electrodyssey/NASR-M/conf/LMK03328-settings/LMK03328-TP-solver-PS33.33-SZG64.8.jpg

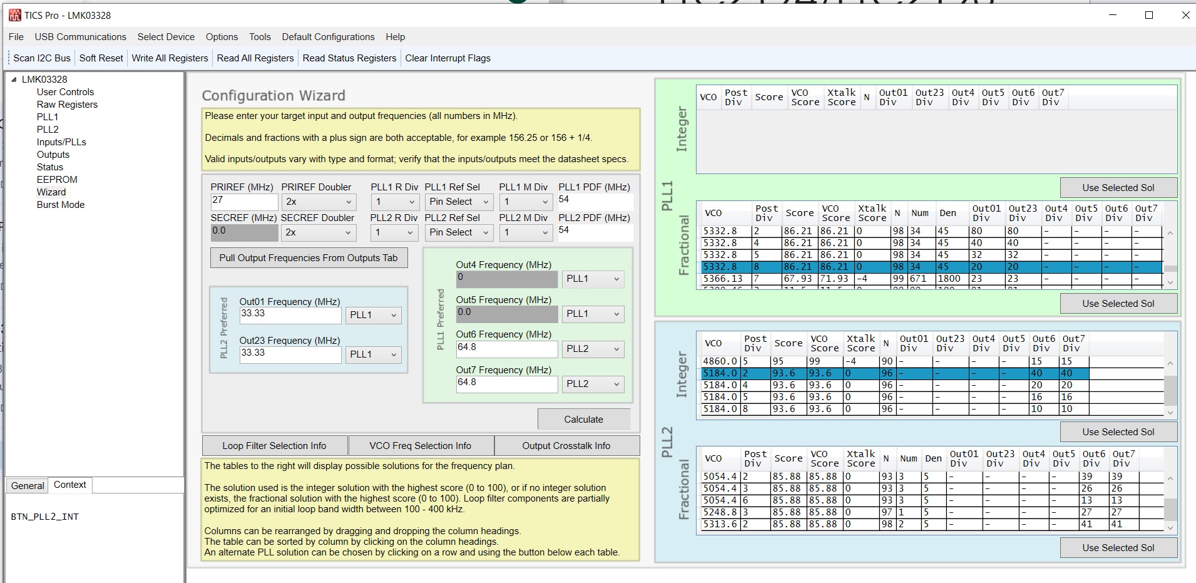
conf/LMK03328-settings/LMK03328-TP-solver-PS33.33-SZG64.8.jpg
