electrodyssey/NASR-M/conf/mcu-conf/nasr_stm32_clock.png

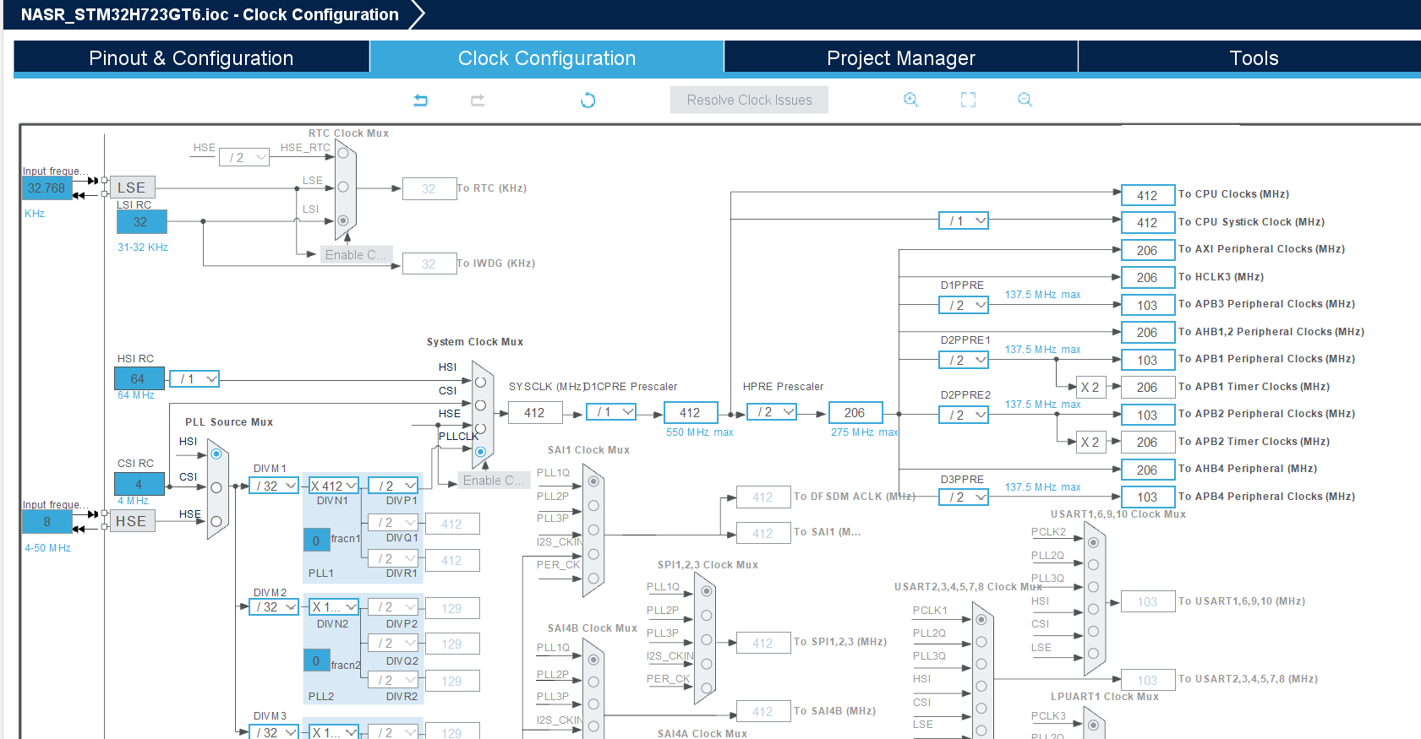
conf/mcu-conf/nasr_stm32_clock.png
