electrodyssey/NASR-M/datasheet/74/deadtime-spdt-nor-and.png

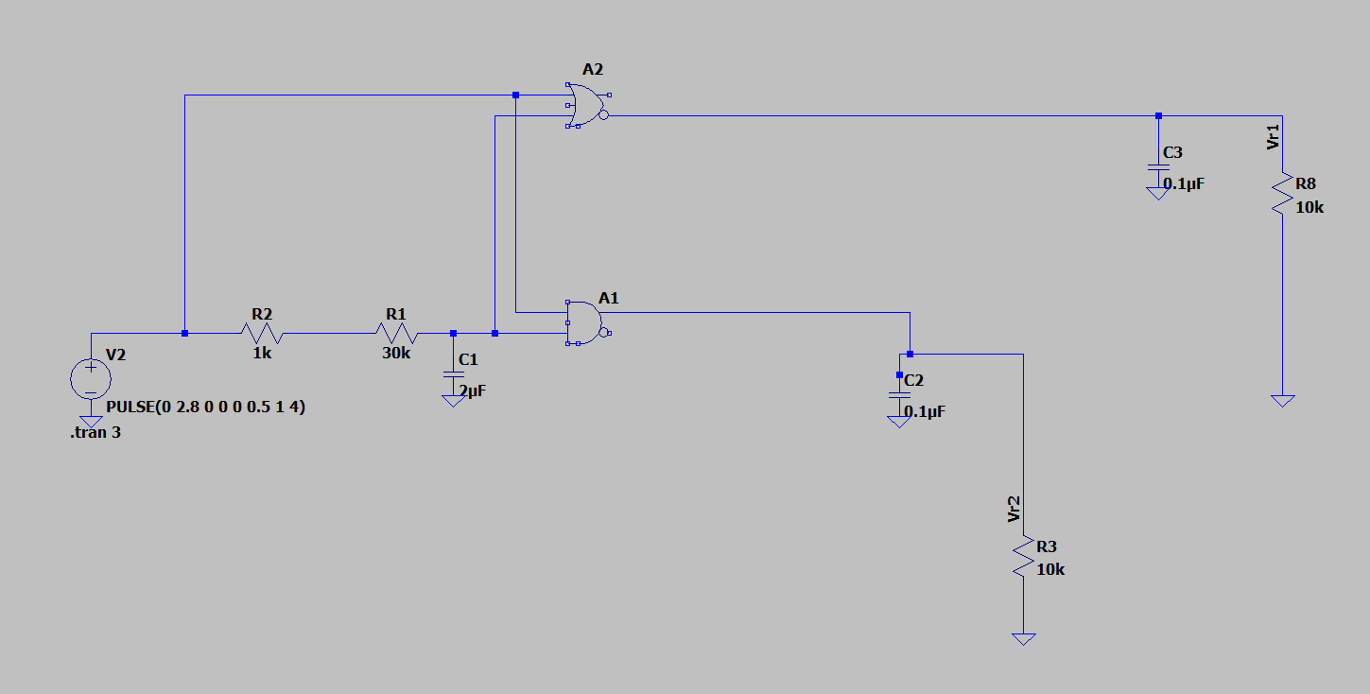
datasheet/74/deadtime-spdt-nor-and.png
