electrodyssey/NASR-M/datasheet/clock/Screenshot 2023-09-30 040555.jpg

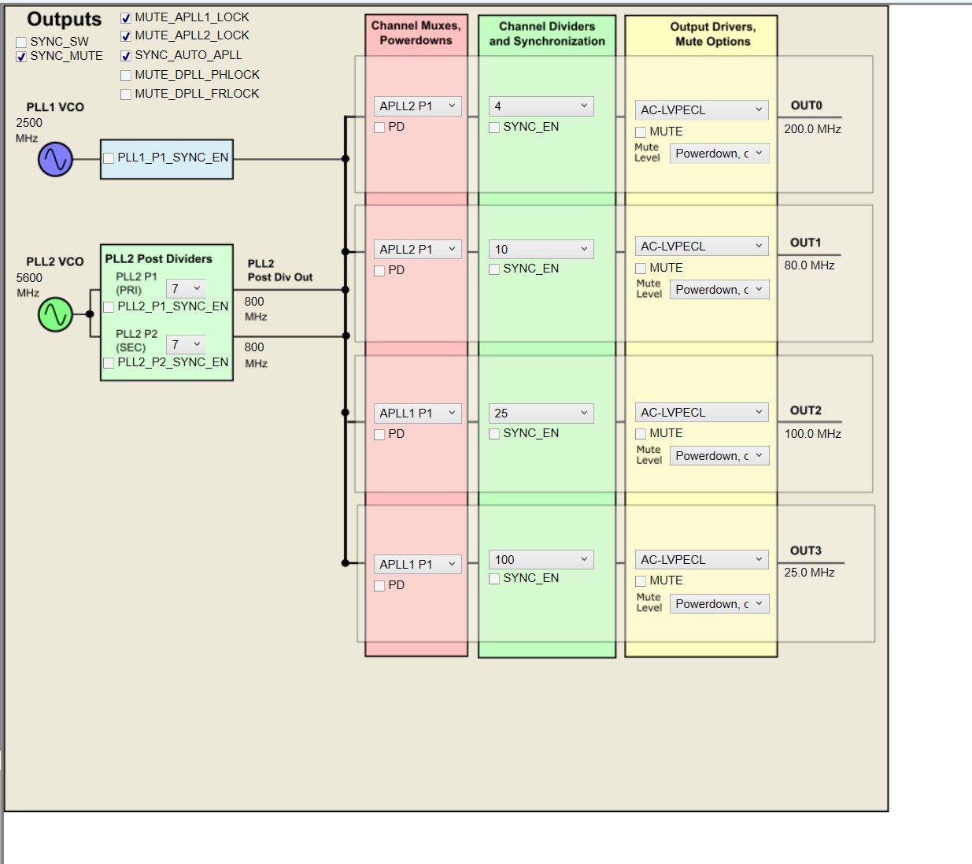
datasheet/clock/Screenshot 2023-09-30 040555.jpg
