electrodyssey/NASR-M/datasheet/enet-sw/4604.dp83640 AC coupling connection.JPG

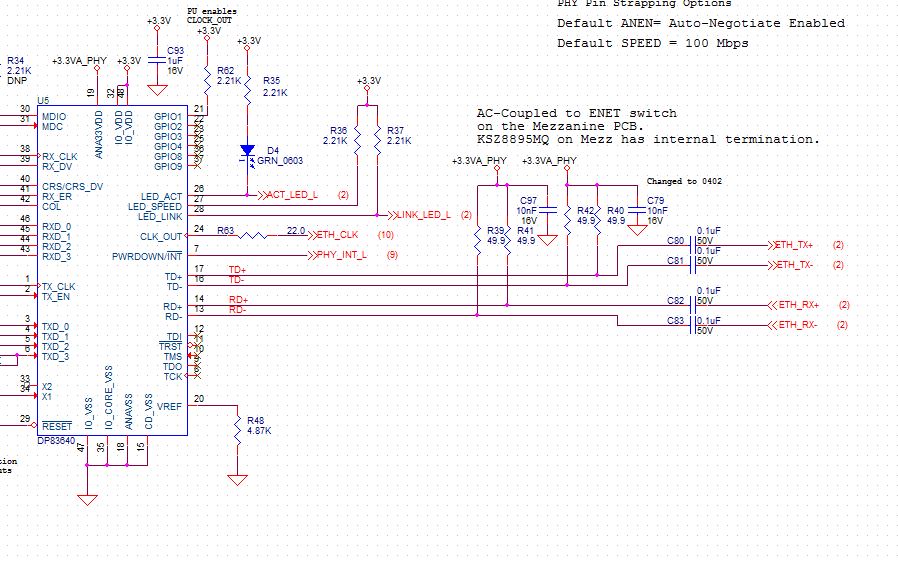
datasheet/enet-sw/4604.dp83640 AC coupling connection.JPG
