electrodyssey/NASR-M/datasheet/LM74700/LM74700-schema.png

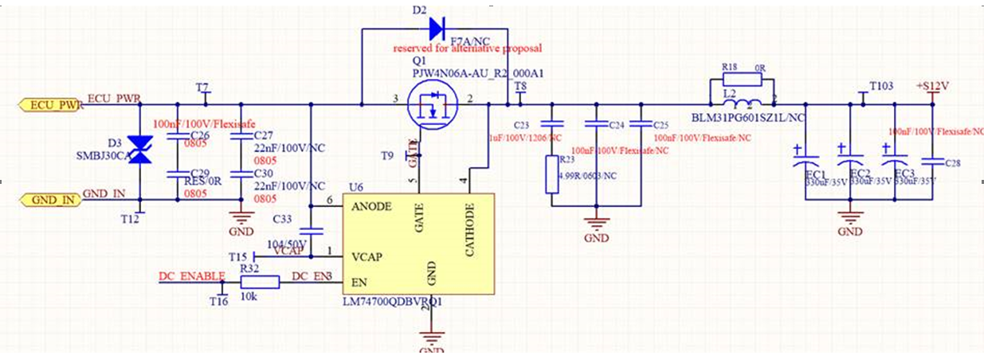
datasheet/LM74700/LM74700-schema.png
