electrodyssey/NASR-M/datasheet/pmic/LMR33640ADDAR  ‑  9V-36V to 6.50V @ 3.8A/LMR33640-buck-6.5V@3.8A.png

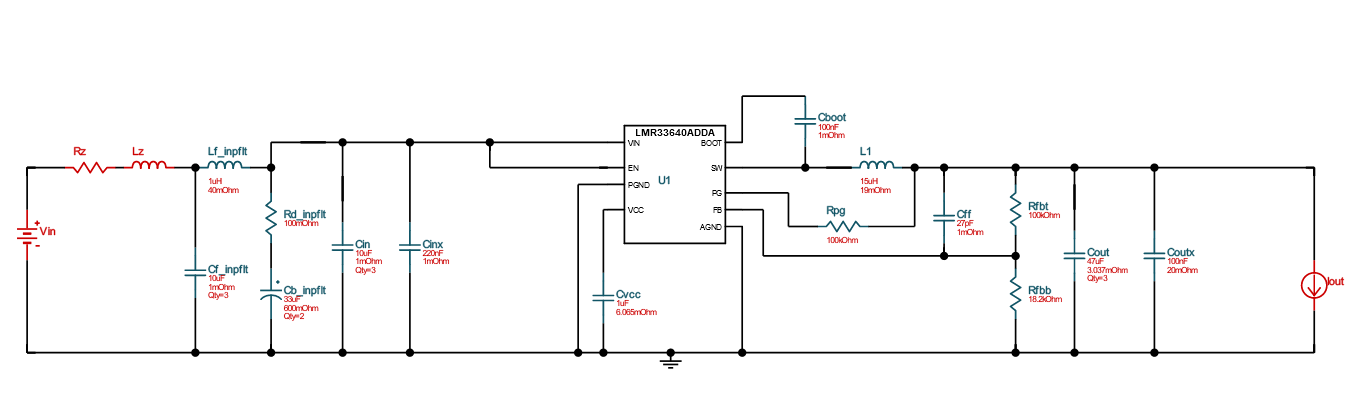
datasheet/pmic/LMR33640ADDAR ‑ 9V-36V to 6.50V @ 3.8A/LMR33640-buck-6.5V@3.8A.png
