electrodyssey/NASR-M/datasheet/usb-sata/sata-connector.jpg

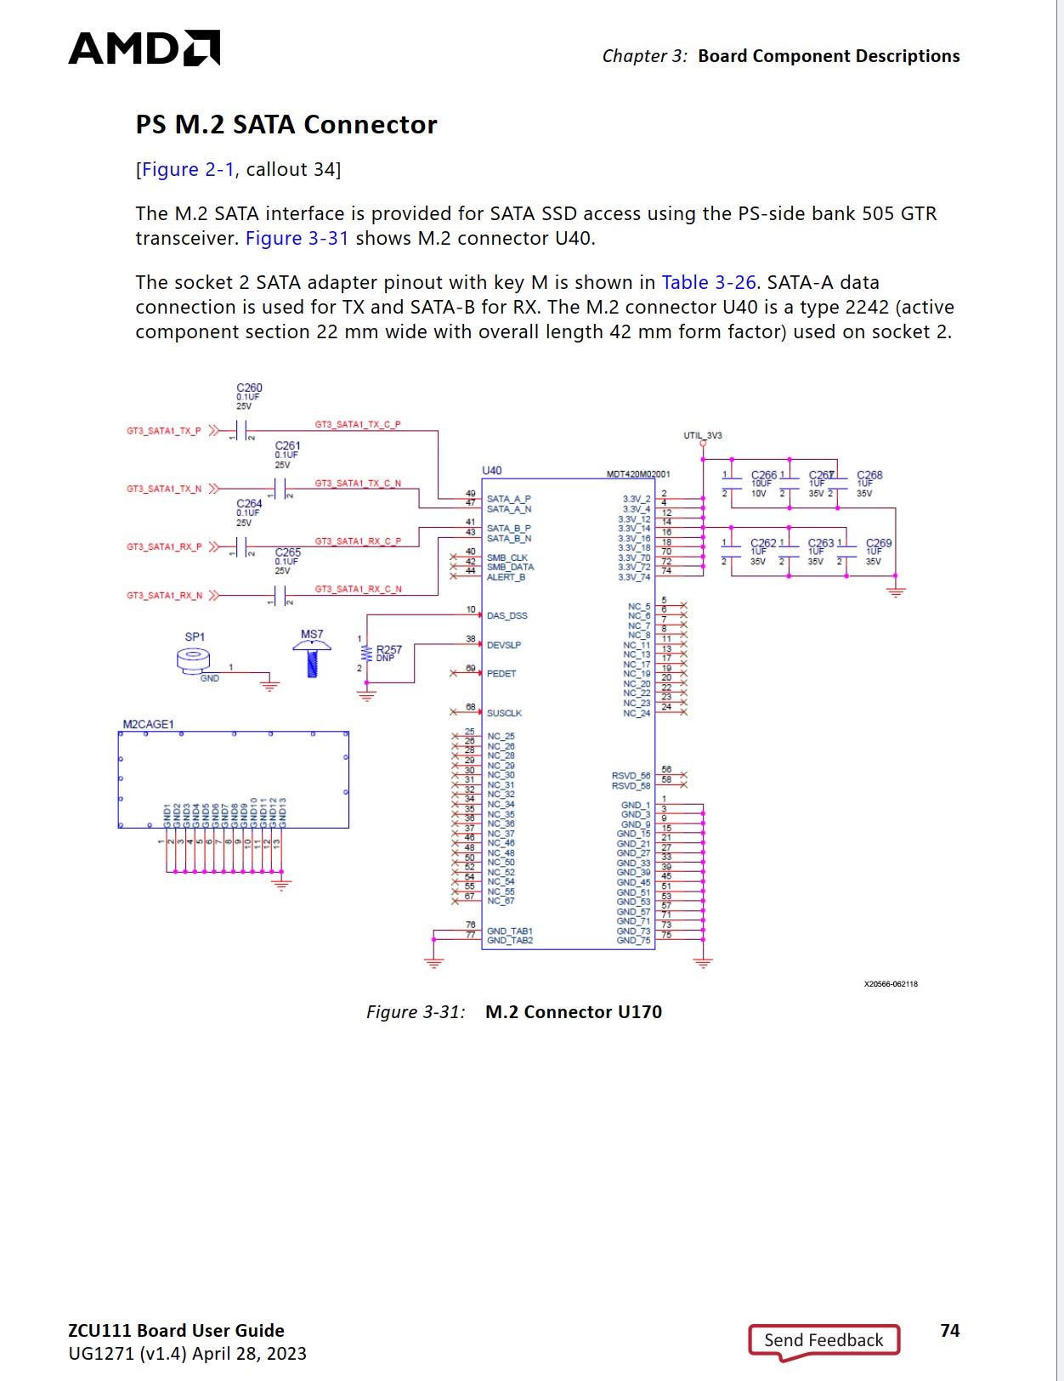
datasheet/usb-sata/sata-connector.jpg
