electrodyssey/NASR-M/datasheet/xilinx-7/artix-7-clocking/XC7A50T-FTG256.png

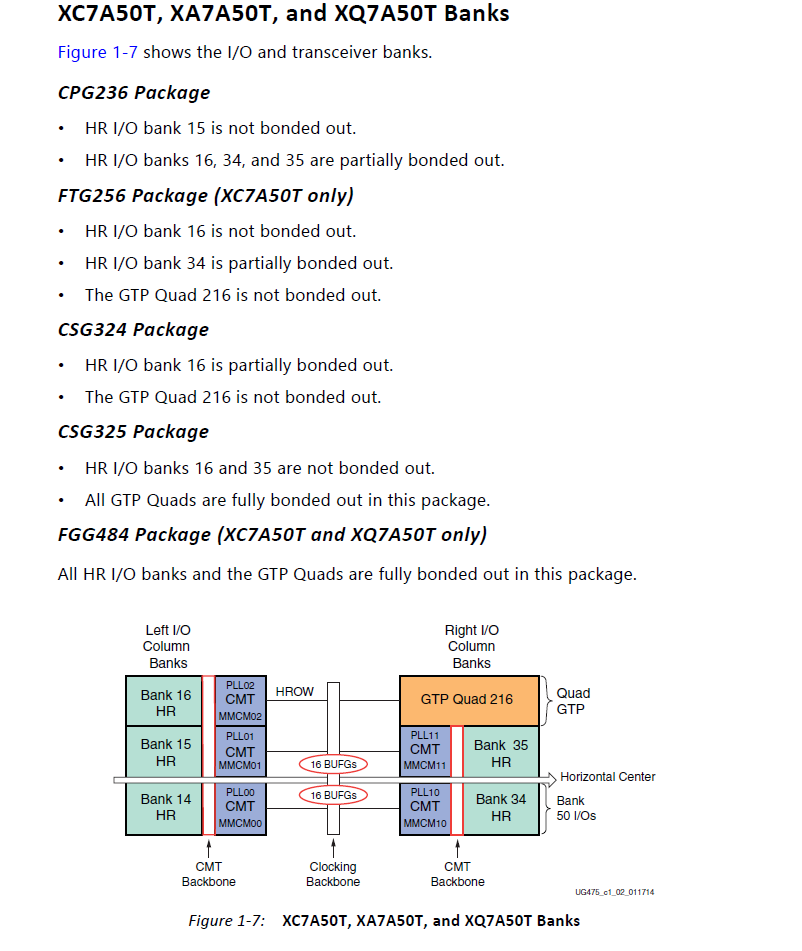
datasheet/xilinx-7/artix-7-clocking/XC7A50T-FTG256.png
