electrodyssey/NASR-M/stackup/JLC10161H-2116/stack-JLC10161H-2116-mil.jpg

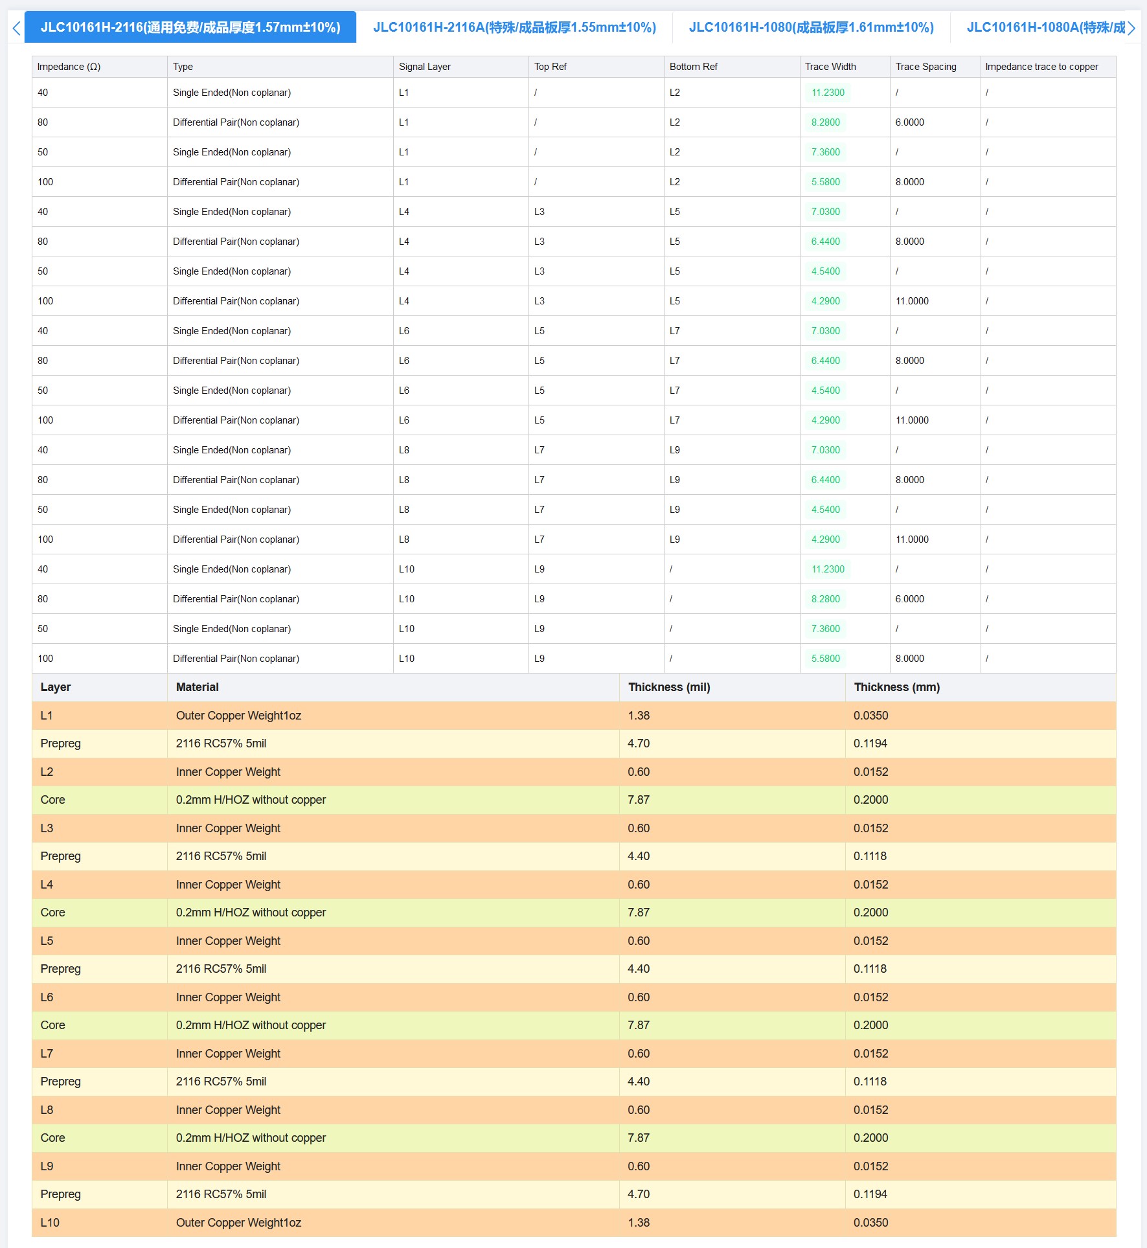
stackup/JLC10161H-2116/stack-JLC10161H-2116-mil.jpg
