electrodyssey/NASR-M/stackup/JLC10161H-2116/stack-JLC10161H-2116.jpg

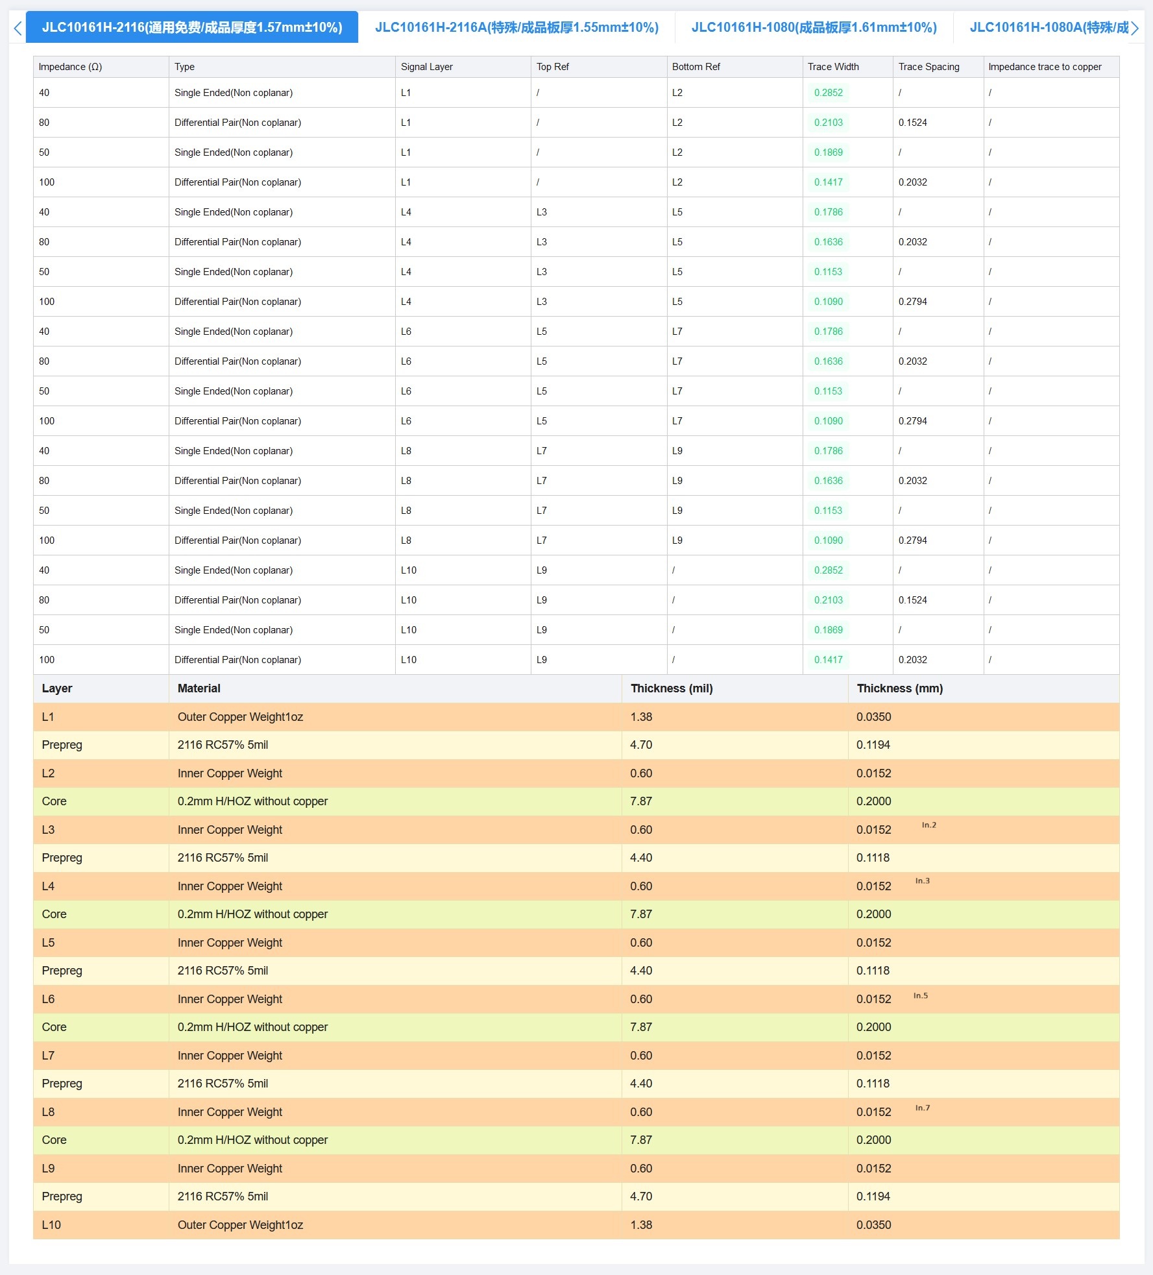
stackup/JLC10161H-2116/stack-JLC10161H-2116.jpg
