electrodyssey/NASR-M/vio-sim/tinadiag-vio-adc_0.001-2-sweep.bmp

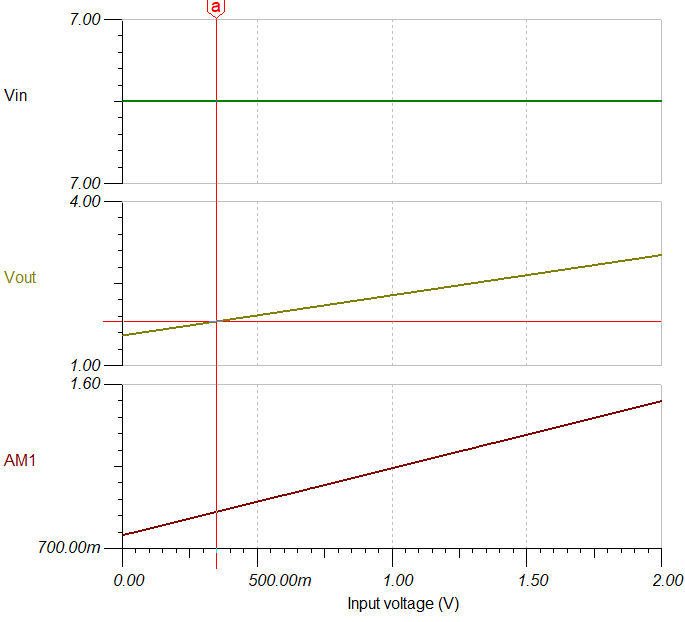
vio-sim/tinadiag-vio-adc_0.001-2-sweep.bmp
