electrodyssey/NASR-M/datasheet/74/spdt-emul.asc

A1: and
A2: or
C1: cap; 2µF
C2: cap; 0.1µF
C3: cap; 0.1µF
R1: res; 30k
R2: res; 1k
R3: res; 10k
R8: res; 10k
V2: voltage; PULSE(0 2.8 0 0 0 0.5 1 4)
Named nets: 0, Vr2, Vr1
.tran 3
