electrodyssey/NASR-M/NASR.kicad_sch

## KiCad design NASR.kicad_sch (2025-10-22)

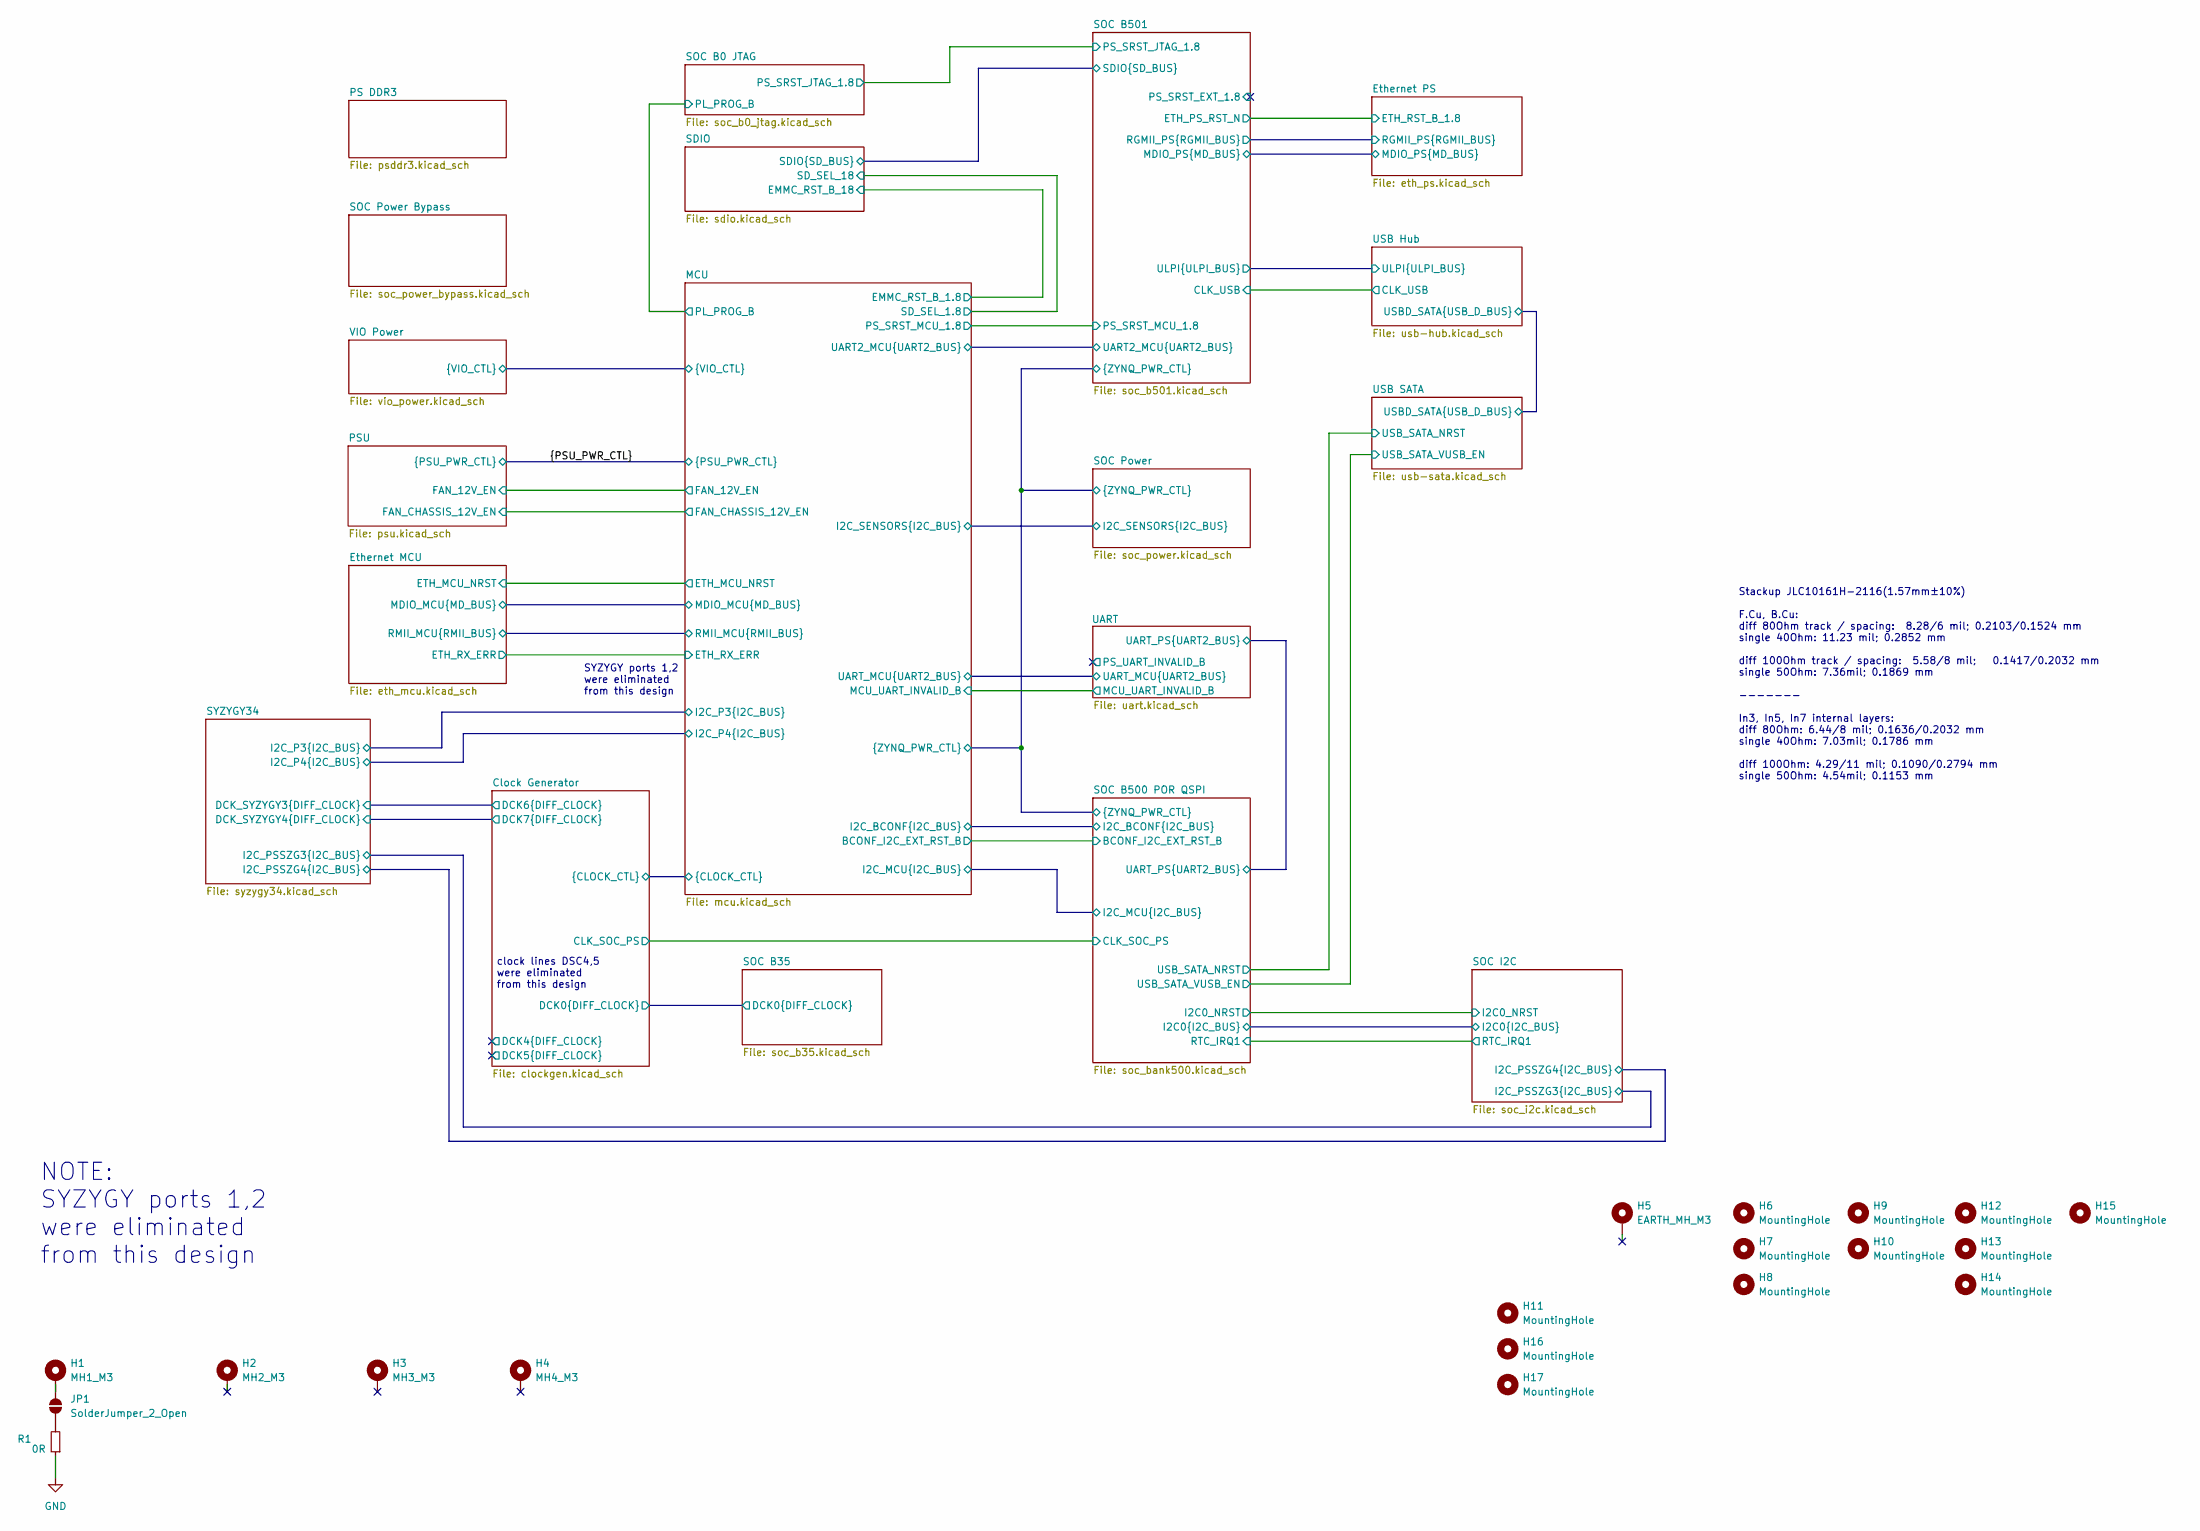
[picture p45: schematic NASR.kicad_sch]

Parts:
H1: MH1_M3; MountingHole_3.2mm_M3_Pad_Via
H2: MH2_M3; MountingHole_3.2mm_M3_Pad_Via
H3: MH3_M3; MountingHole_3.2mm_M3_Pad_Via
H4: MH4_M3; MountingHole_3.2mm_M3_Pad_Via
H5: EARTH_MH_M3; MountingHole_3.2mm_M3_Pad_Via
H6, H7, H8, H9, H10, H12, H13, H14, H15: MountingHole; MountingHole_3.2mm_M3
H11, H16, H17: MountingHole; MountingHole_4.3mm_M4_Pad_TopBottom
JP1: SolderJumper_2_Open; SolderJumper-2_P1.3mm_Open_RoundedPad1.0x1.5mm
R1: 0R; R_1210_3225Metric_Pad1.30x2.65mm_HandSolder; Part RC1210JR-070RL; JLCPCB Part # C137090

Connections:
GND: R1.1
unnamed: H1.1, JP1.2 (B)
unnamed: JP1.1 (A), R1.2

Notes on the sheet:
clock lines DSC4,5 were eliminated from this design
NOTE: SYZYGY ports 1,2 were eliminated from this design
SYZYGY ports 1,2 were eliminated from this design
Stackup JLC10161H-2116(1.57mm±10%) F.Cu, B.Cu: diff 80Ohm track / spacing: 8.28/6 mil; 0.2103/0.1524 mm single 40Ohm: 11.23 mil; 0.2852 mm diff 100Ohm track / spacing: 5.58/8 mil; 0.1417/0.2032 mm single 50Ohm: 7.36mil; 0.1869 mm ------- In3, In5, In7 internal layers: diff 80Ohm: 6.44/8 mil; 0.1636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
