electrodyssey/NASR-M/clockgen.kicad_sch

## KiCad design clockgen.kicad_sch (2026-03-24)

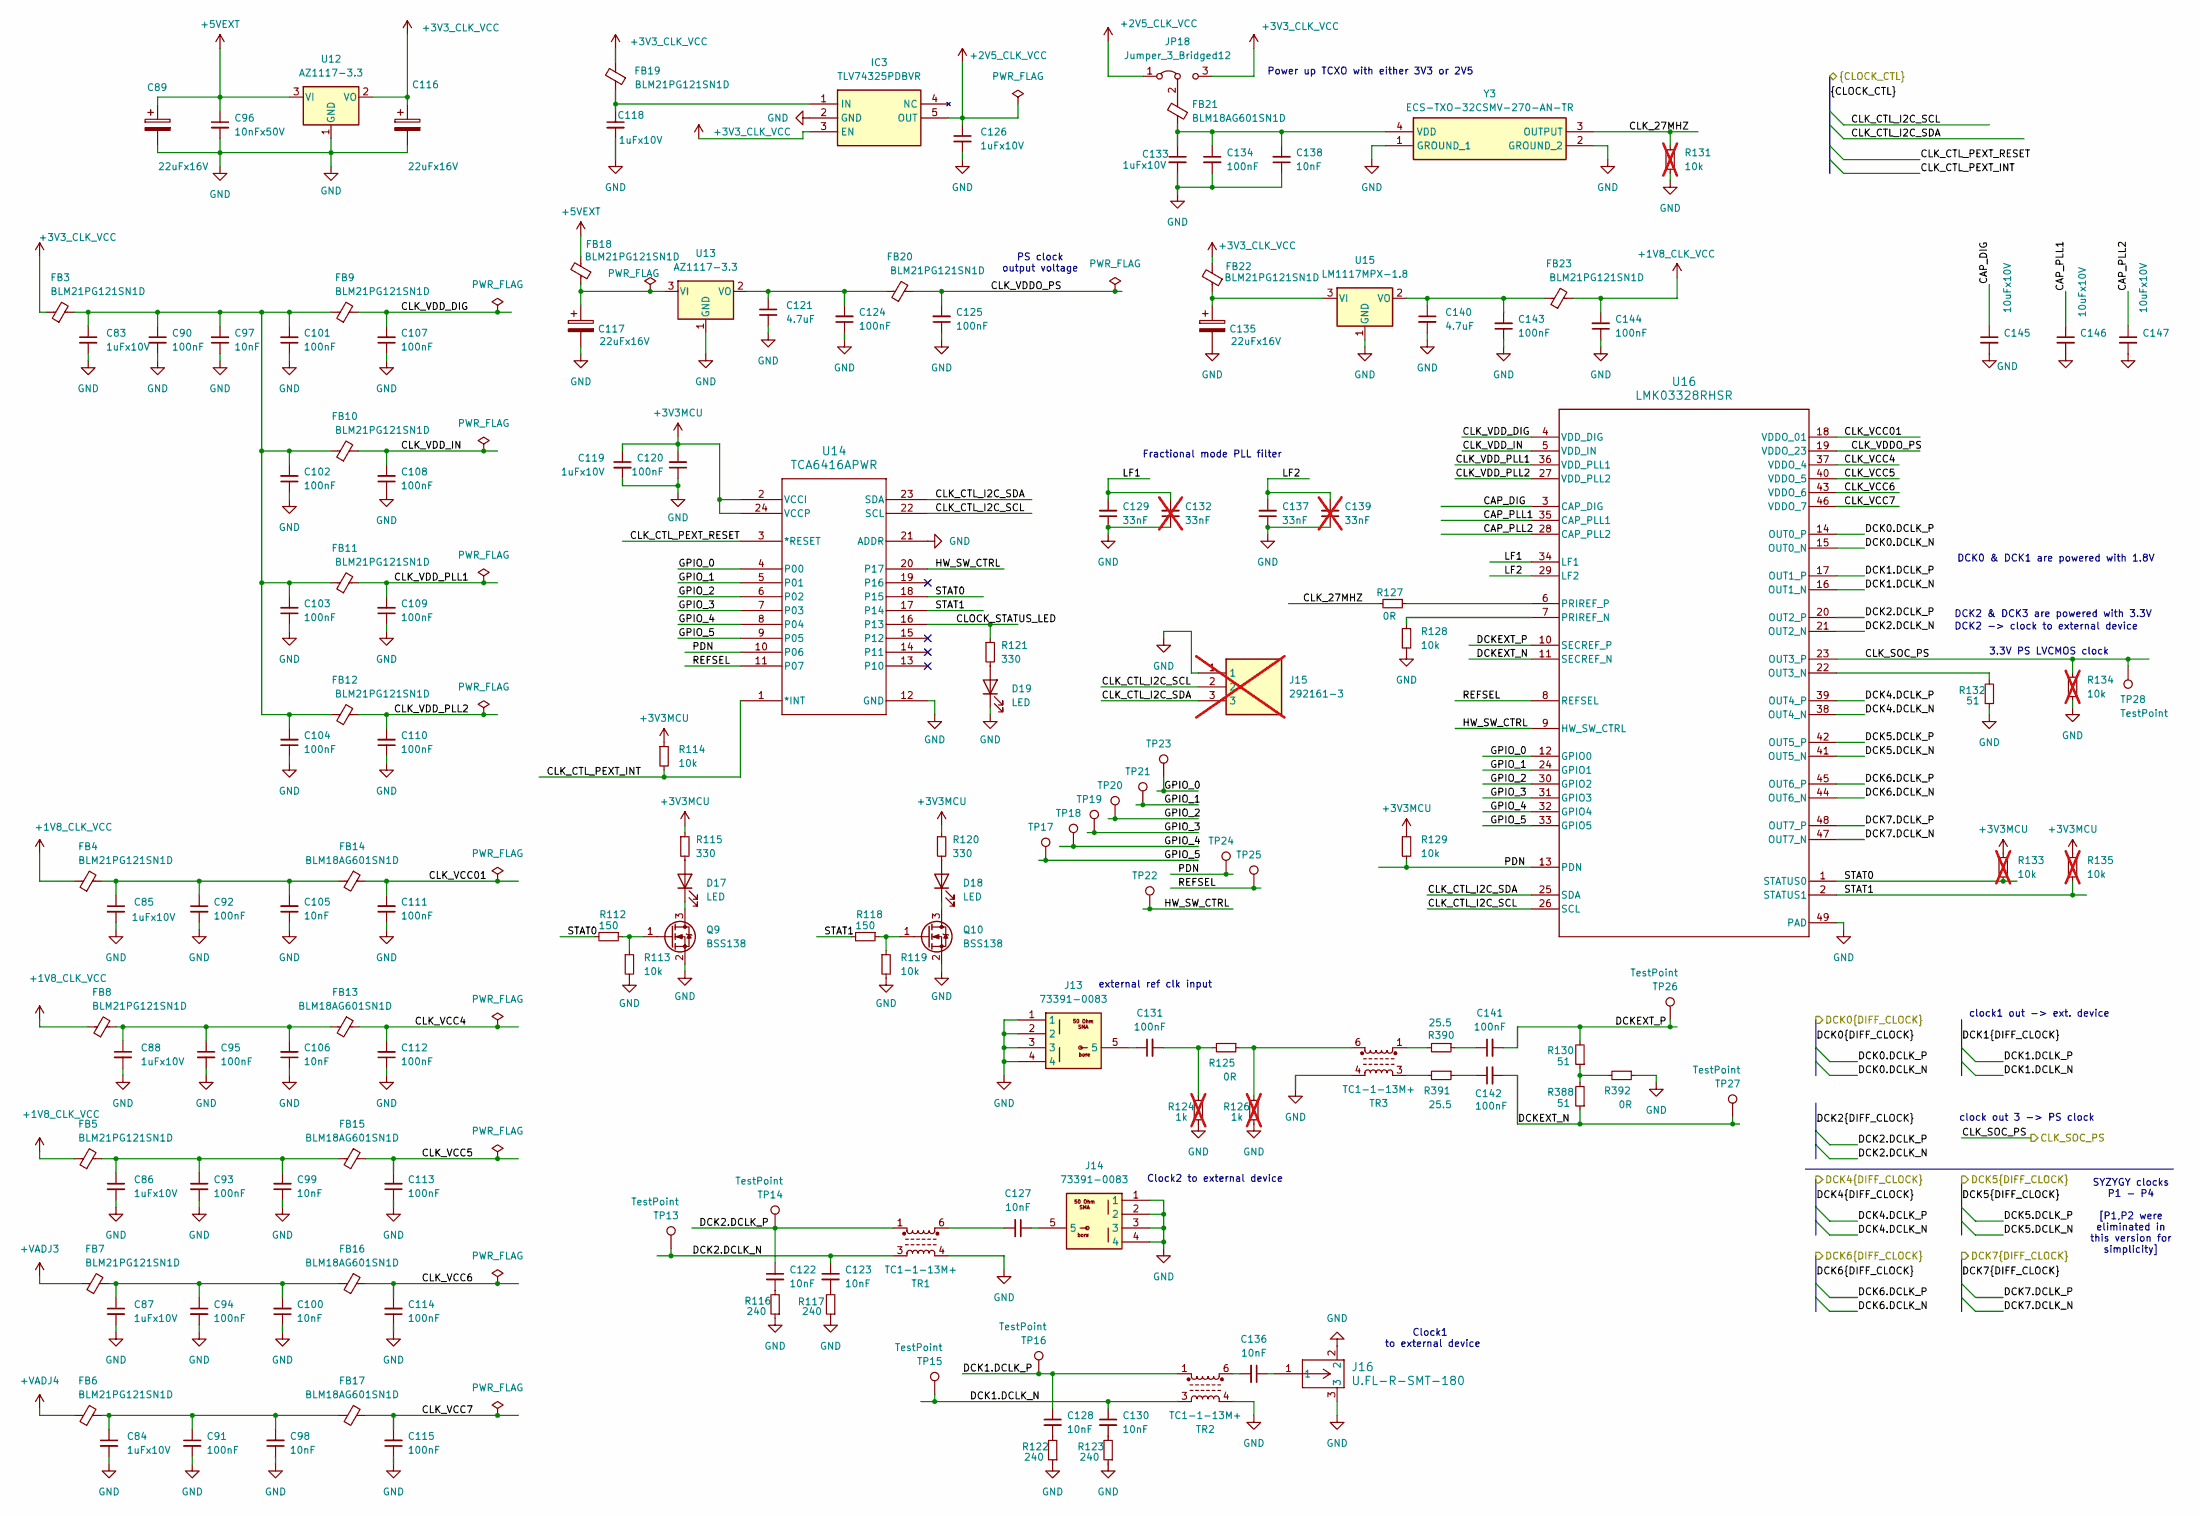
[picture p46: schematic clockgen.kicad_sch]

Parts:
C83, C84, C85, C86, C87, C88, C118, C119, C126, C133: 1uFx10V; C_0603_1608Metric; JLCPCB Part # C841050
C89, C116, C117, C135: 22uFx16V; CP_EIA-6032-15_Kemet-U; Part TR3C226K016C0350; JLCPCB Part # C1954274
C90, C91, C92, C93, C94, C95, C101, C102, C103, C104, C107, C108, C109, C110, C111, C112, C113, C114, C115, C120, C124, C125, C131, C134, C141, C142, C143, C144: 100nF; C_0402_1005Metric; Part CC0402JRX7R8BB104; JLCPCB Part # C541465
C96: 10nFx50V; C_1206_3216Metric; Part 1206B103K102NT; JLCPCB Part # C9194
C97, C98, C99, C100, C105, C106, C122, C123, C127, C128, C130, C136, C138: 10nF; C_0402_1005Metric; Part CL05B103KB5NNNC; JLCPCB Part # C15195
C121, C140: 4.7uF; C_0603_1608Metric; JLCPCB Part # C19666
C129, C137: 33nF; C_0603_1608Metric; Part CL10B333KB8NNNC; JLCPCB Part # C21117
C132, C139: 33nF; C_0603_1608Metric; Part CL10B333KB8NNNC; JLCPCB Part # C21117; not fitted
C145, C146, C147: 10uFx10V; C_0805_2012Metric; Part CL21A106KPFNNNE; JLCPCB Part # C17024
D17, D18, D19: LED; LED_0805_2012Metric; Part HL-PSC-2012S11GC; JLCPCB Part # C497958
FB3, FB4, FB5, FB6, FB7, FB8, FB9, FB10, FB11, FB12, FB18, FB19, FB20, FB22, FB23: BLM21PG121SN1D; L_0805_2012Metric; Part BLM21PG121SN1D; JLCPCB Part # C79382
FB13, FB14, FB15, FB16, FB17, FB21: BLM18AG601SN1D; L_0603_1608Metric; Part BLM18AG601SN1D; JLCPCB Part # C19330
IC3: TLV74325PDBVR; SOT95P280X145-5N; Mouser Part Number 595-TLV74325PDBVR
J13, J14: 73391-0083; 733910083; Mouser Part Number 538-73391-0083
J15: 292161-3; SHDR3W60P0X200_1X3_780X360X680P; Mouser Part Number 571-292161-3; not fitted
J16: U.FL-R-SMT-180; CONN1_U.FL-R-SMT-180_HIR; Part U.FL-R-SMT-1(80); JLCPCB Part # C88374
JP18: Jumper_3_Bridged12; SolderJumper-3_P1.3mm_Bridged2Bar12_Pad1.0x1.5mm_NumberLabe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
Q9, Q10: BSS138; SOT-23; JLCPCB Part # C52895
R112, R118: 150; R_0402_1005Metric; Part 0402WGF1500TCE; JLCPCB Part # C25082
R113, R114, R119, R128, R129: 10k; R_0402_1005Metric; Part 0402WGF1002TCE; JLCPCB Part # C25744
R115, R120, R121: 330; R_0402_1005Metric; Part 0402WGF3300TCE; JLCPCB Part # C25104
R116, R117, R122, R123: 240; R_0402_1005Metric; Part RK73B1ETTP241J; JLCPCB Part # C131545
R124, R126: 1k; R_0402_1005Metric; Part 0402WGF1001TCE; JLCPCB Part # C11702; not fitted
R125, R127, R392: 0R; R_0603_1608Metric; Part FRC0603F0000TS; JLCPCB Part # C2906974
R130, R132, R388: 51; R_0402_1005Metric; Part FRC0402J510 TS; JLCPCB Part # C2906953
R131, R133, R134, R135: 10k; R_0402_1005Metric; Part 0402WGF1002TCE; JLCPCB Part # C25744; not fitted
R390, R391: 25.5; R_0402_1005Metric; Part RK73H1ETTP25R5F; JLCPCB Part # C830244
TP13, TP14, TP15, TP16, TP17, TP18, TP19, TP20, TP21, TP22, TP23, TP24, TP25, TP26, TP27, TP28: TestPoint; TestPoint_Pad_D1.0mm
TR1, TR2, TR3: TC1-1-13M+; Transformer_MiniCircuits_AT224-1A; MFR.Part # TC1-1-13M+; JLCPCB Part # C879854
U12, U13: AZ1117-3.3; SOT-223-3_TabPin2; Part AZ1117H-3.3TRG1; JLCPCB Part # C110474
U14: TCA6416APWR; PW24; JLCPCB Part # C130203
U15: LM1117MPX-1.8; SOT-223-3_TabPin2; Part LM1117MPX-1.8/NOPB; JLCPCB Part # C9660
U16: LMK03328RHSR; RHS0048A; JLCPCB Part # C544831
Y3: ECS-TXO-32CSMV-270-AN-TR; ECSTXO32CSMV270ANTR; Mouser Part Number 520-TXO32CSMV270ANTR

Connections:
+1V8_CLK_VCC: C144.2, FB4.1, FB5.1, FB8.1, FB23.2
+2V5_CLK_VCC: C126.1, IC3.5 (OUT), JP18.1 (A)
+3V3MCU: C119.1, C120.2, R114.1, R115.1, R120.1, R129.1, R133.1, R135.1, U14.2 (VCCI), U14.24 (VCCP)
+3V3_CLK_VCC: C116.1, FB3.1, FB19.2, FB22.2, IC3.3 (EN), JP18.3 (B), U12.2 (VO)
+5VEXT: C89.1, C96.1, FB18.2, U12.3 (VI)
+VADJ3: FB7.1
+VADJ4: FB6.1
CAP_DIG: C145.1, U16.3 (CAP_DIG)
CAP_PLL1: C146.1, U16.35 (CAP_PLL1)
CAP_PLL2: C147.1, U16.28 (CAP_PLL2)
CLK_27MHZ: R127.2, R131.1, Y3.3 (OUTPUT)
CLK_CTL_I2C_SCL: J15.2, U14.22 (SCL), U16.26 (SCL)
CLK_CTL_I2C_SDA: J15.3, U14.23 (SDA), U16.25 (SDA)
CLK_CTL_PEXT_INT: R114.2, U14.1 (*INT)
CLK_CTL_PEXT_RESET: U14.3 (*RESET)
CLK_SOC_PS: R134.1, TP28.1, U16.23 (OUT3_P)
CLK_VCC01: C111.2, FB14.1, U16.18 (VDDO_01)
CLK_VCC4: C112.2, FB13.1, U16.37 (VDDO_4)
CLK_VCC5: C113.2, FB15.1, U16.40 (VDDO_5)
CLK_VCC6: C114.2, FB16.1, U16.43 (VDDO_6)
CLK_VCC7: C115.2, FB17.1, U16.46 (VDDO_7)
CLK_VDDO_PS: C125.2, FB20.2, U16.19 (VDDO_23)
CLK_VDD_DIG: C107.2, FB9.2, U16.4 (VDD_DIG)
CLK_VDD_IN: C108.2, FB10.2, U16.5 (VDD_IN)
CLK_VDD_PLL1: C109.2, FB11.2, U16.36 (VDD_PLL1)
CLK_VDD_PLL2: C110.2, FB12.2, U16.27 (VDD_PLL2)
CLOCK_STATUS_LED: R121.1, U14.16 (P13)
DCK0.DCLK_N: U16.15 (OUT0_N)
DCK0.DCLK_P: U16.14 (OUT0_P)
DCK1.DCLK_N: C130.1, TP15.1, TR2.3, U16.16 (OUT1_N)
DCK1.DCLK_P: C128.1, TP16.1, TR2.1, U16.17 (OUT1_P)
DCK2.DCLK_N: C123.1, TP13.1, TR1.3, U16.21 (OUT2_N)
DCK2.DCLK_P: C122.1, TP14.1, TR1.1, U16.20 (OUT2_P)
DCK4.DCLK_N: U16.38 (OUT4_N)
DCK4.DCLK_P: U16.39 (OUT4_P)
DCK5.DCLK_N: U16.41 (OUT5_N)
DCK5.DCLK_P: U16.42 (OUT5_P)
DCK6.DCLK_N: U16.44 (OUT6_N)
DCK6.DCLK_P: U16.45 (OUT6_P)
DCK7.DCLK_N: U16.47 (OUT7_N)
DCK7.DCLK_P: U16.48 (OUT7_P)
DCKEXT_N: C142.2, R388.1, TP27.1, U16.11 (SECREF_N)
DCKEXT_P: C141.2, R130.2, TP26.1, U16.10 (SECREF_P)
GND: C83.2, C84.2, C85.2, C86.2, C87.2, C88.2, C89.2, C90.2, C91.2, C92.2, C93.2, C94.2, C95.2, C96.2, C97.1, C98.1, C99.1, C100.1, C101.1, C102.1, C103.1, C104.1, C105.1, C106.1, C107.1, C108.1, C109.1, C110.1, C111.1, C112.1, C113.1, C114.1, C115.1, C116.2, C117.2, C118.2, C119.2, C120.1, C121.2, C124.1, C125.1, C126.2, C129.1, C132.1, C133.2, C134.2, C135.2, C137.1, C138.1, C139.1, C140.2, C143.1, C144.1, C145.2, C146.2, C147.2, D19.1 (K), IC3.2 (GND), J13.1, J13.2, J13.3, J13.4, J14.1, J14.2, J14.3, J14.4, J15.1, J16.2, J16.3, Q9.2 (S), Q10.2 (S), R113.2, R116.1, R117.1, R119.2, R122.1, R123.1, R124.1, R126.1, R128.2, R131.2, R132.1, R134.2, R392.1, TR1.4, TR2.4, TR3.4, U12.1 (GND), U13.1 (GND), U14.12 (GND), U14.21 (ADDR), U15.1 (GND), U16.49 (PAD), Y3.1 (GROUND_1), Y3.2 (GROUND_2)
GPIO_0: TP23.1, U14.4 (P00), U16.12 (GPIO0)
GPIO_1: TP21.1, U14.5 (P01), U16.24 (GPIO1)
GPIO_2: TP20.1, U14.6 (P02), U16.30 (GPIO2)
GPIO_3: TP19.1, U14.7 (P03), U16.31 (GPIO3)
GPIO_4: TP18.1, U14.8 (P04), U16.32 (GPIO4)
GPIO_5: TP17.1, U14.9 (P05), U16.33 (GPIO5)
HW_SW_CTRL: TP22.1, U14.20 (P17), U16.9 (HW_SW_CTRL)
LF1: C129.2, C132.2, U16.34 (LF1)
LF2: C137.2, C139.2, U16.29 (LF2)
unnamed: C84.1, C91.1, C98.2, FB6.2, FB17.2
unnamed: C86.1, C93.1, C99.2, FB5.2, FB15.2
unnamed: C87.1, C94.1, C100.2, FB7.2, FB16.2
unnamed: C83.1, C90.1, C97.2, C101.2, C102.2, C103.2, C104.2, FB3.2, FB9.1, FB10.1, FB11.1, FB12.1
unnamed: C85.1, C92.1, C105.2, FB4.2, FB14.2
unnamed: C88.1, C95.1, C106.2, FB8.2, FB13.2
unnamed: C117.1, FB18.1, U13.3 (VI)
unnamed: C118.1, FB19.1, IC3.1 (IN)
unnamed: C121.1, C124.2, FB20.1, U13.2 (VO)
unnamed: C122.2, R116.2
unnamed: C123.2, R117.2
unnamed: C127.1, J14.5
unnamed: C127.2, TR1.6
unnamed: C128.2, R122.2
unnamed: C130.2, R123.2
unnamed: C131.1, J13.5
unnamed: C131.2, R124.2, R125.2
unnamed: C133.1, C134.1, C138.2, FB21.1, Y3.4 (VDD)
unnamed: C135.1, FB22.1, U15.3 (VI)
unnamed: C136.1, J16.1
unnamed: C136.2, TR2.6
unnamed: C140.1, C143.2, FB23.1, U15.2 (VO)
unnamed: C141.1, R390.1
unnamed: C142.1, R391.1
unnamed: D17.1 (K), Q9.3 (D)
unnamed: D17.2 (A), R115.2
unnamed: D18.1 (K), Q10.3 (D)
unnamed: D18.2 (A), R120.2
unnamed: D19.2 (A), R121.2
unnamed: FB21.2, JP18.2 (C)
unnamed: Q9.1 (G), R112.1, R113.1
unnamed: Q10.1 (G), R118.1, R119.1
unnamed: R125.1, R126.2, TR3.6
unnamed: R127.1, U16.6 (PRIREF_P)
unnamed: R128.1, U16.7 (PRIREF_N)
unnamed: R130.1, R388.2, R392.2
unnamed: R132.2, U16.22 (OUT3_N)
unnamed: R390.2, TR3.1
unnamed: R391.2, TR3.3
PDN: R129.2, TP24.1, U14.10 (P06), U16.13 (PDN)
REFSEL: TP25.1, U14.11 (P07), U16.8 (REFSEL)
STAT0: R112.2, R133.2, U14.18 (P15), U16.1 (STATUS0)
STAT1: R118.2, R135.2, U14.17 (P14), U16.2 (STATUS1)

Notes on the sheet:
Clock1 to external device
DCK2 -> clock to external device
DCK2 & DCK3 are powered with 3.3V
Power up TCXO with either 3V3 or 2V5
Clock2 to external device
SYZYGY clocks P1 - P4 [P1,P2 were eliminated in this version for simplicity]
DCK0 & DCK1 are powered with 1.8V
PS clock output voltage
clock1 out -> ext. device
external ref clk input
clock out 3 -> PS clock
Fractional mode PLL filter
3.3V PS LVCMOS clock
