electrodyssey/NASR-M/eth_mcu.kicad_sch

## KiCad design eth_mcu.kicad_sch (2025-10-22)

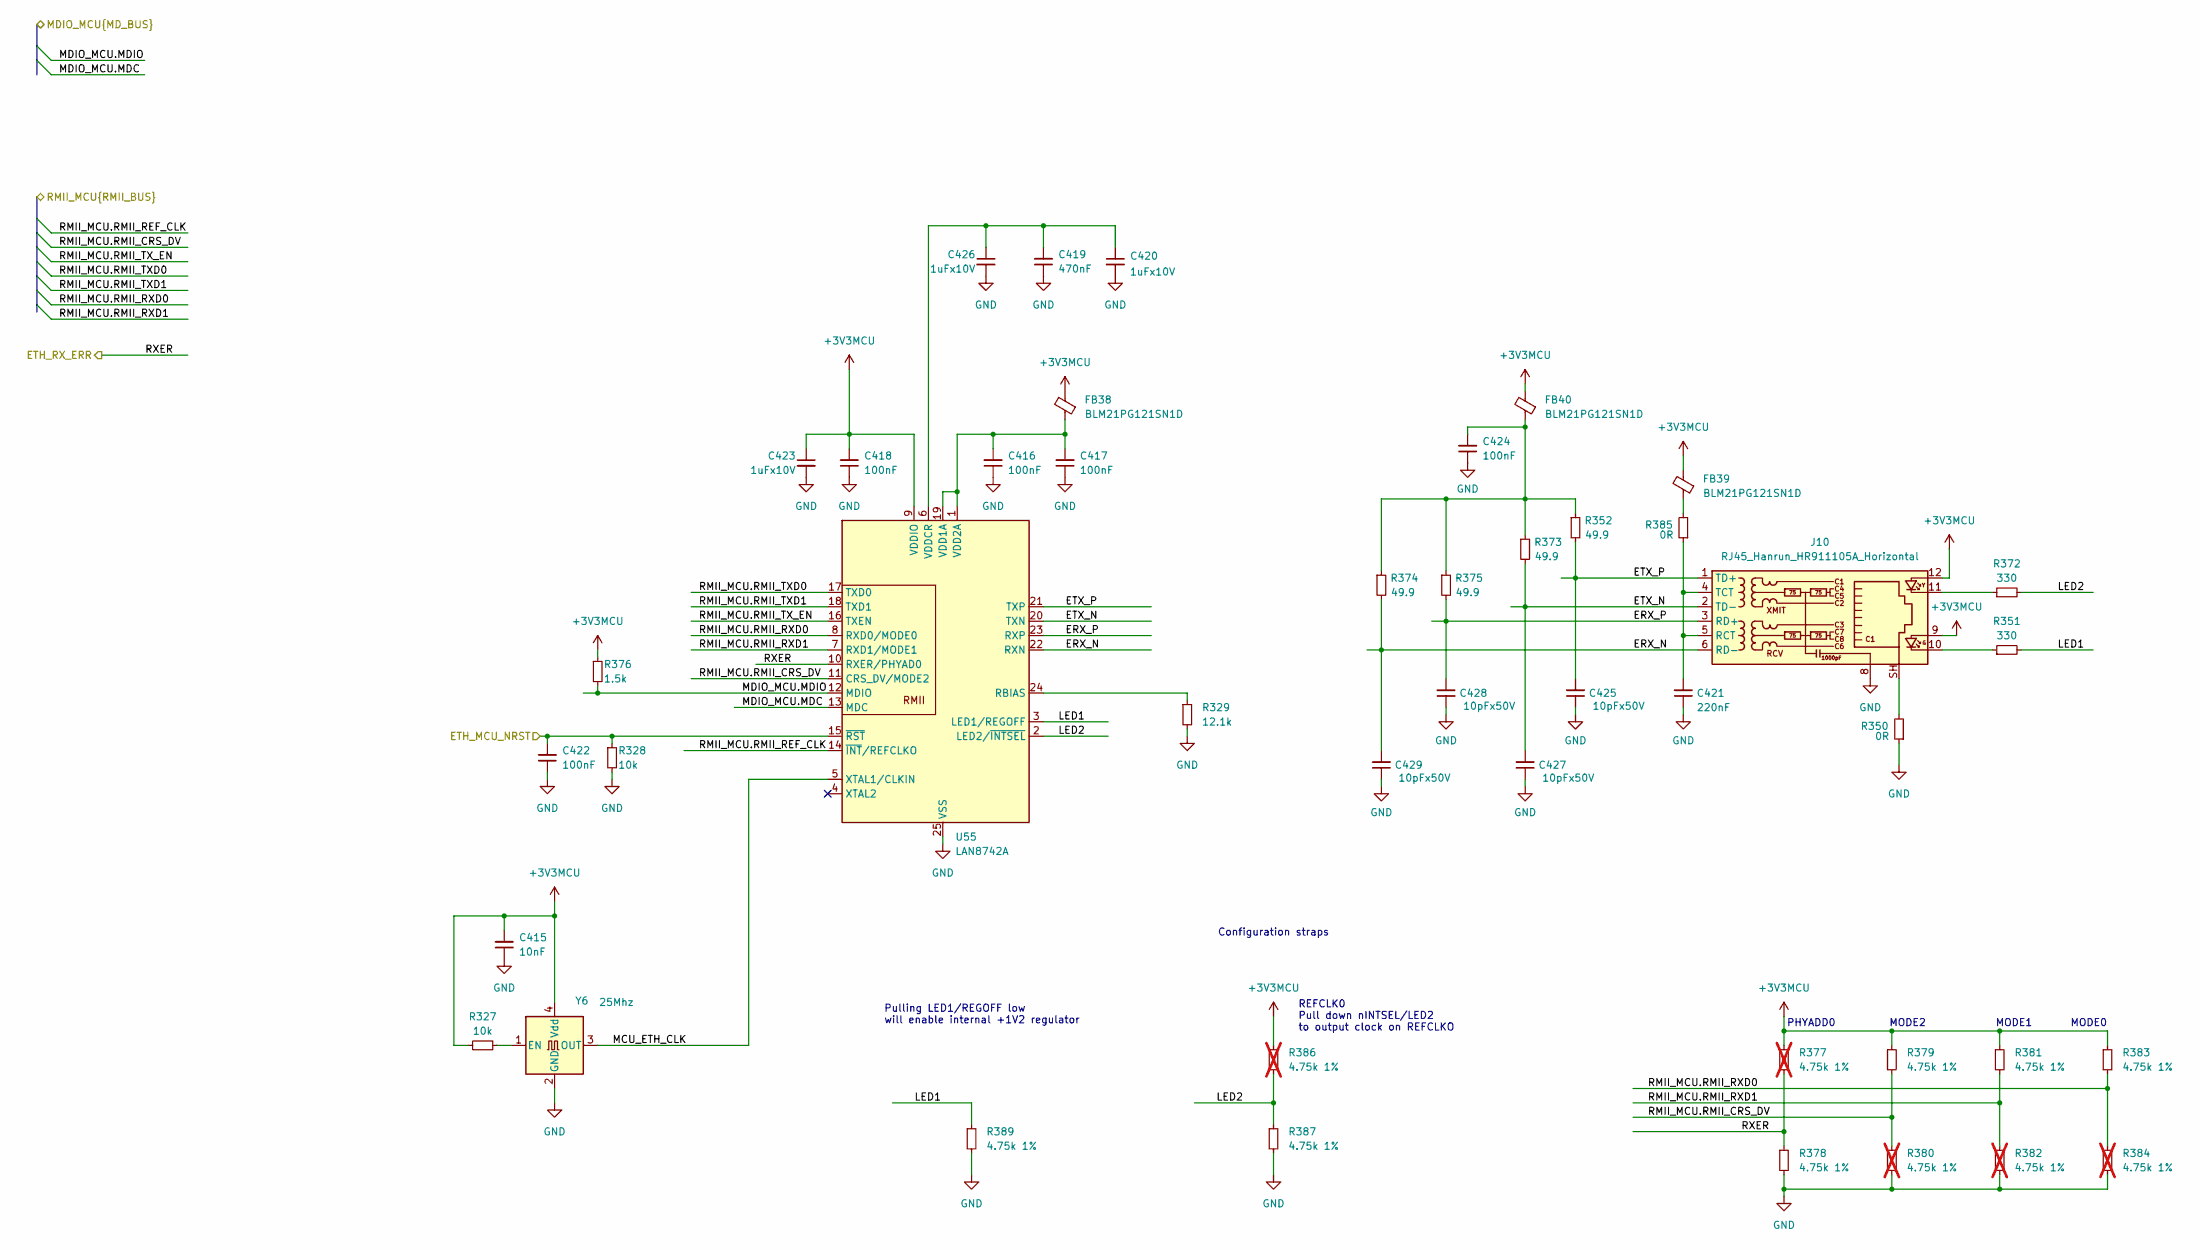
[picture p47: schematic eth_mcu.kicad_sch]

Parts:
C415: 10nF; C_0402_1005Metric; Part CL05B103KB5NNNC; JLCPCB Part # C15195
C416, C417, C418, C422, C424: 100nF; C_0402_1005Metric; Part CC0402JRX7R8BB104; JLCPCB Part # C541465
C419: 470nF; C_0201_0603Metric; Part CL03A474KQ3NNNC; JLCPCB Part # C318543
C420, C423, C426: 1uFx10V; C_0603_1608Metric; JLCPCB Part # C841050
C421: 220nF; C_0805_2012Metric; Part CL21B224KBFNNNE; JLCPCB Part # C5378
C425, C427, C428, C429: 10pFx50V; C_0402_1005Metric; Part 0402CG100J500NT; JLCPCB Part # C1545
FB38, FB39, FB40: BLM21PG121SN1D; L_0805_2012Metric; Part BLM21PG121SN1D; JLCPCB Part # C79382
J10: RJ45_Hanrun_HR911105A_Horizontal; JLCPCB Part # C12074
R327, R328: 10k; R_0402_1005Metric; Part 0402WGF1002TCE; JLCPCB Part # C25744
R329: 12.1k; R_0402_1005Metric; Part 0402WGF1212TCE; JLCPCB Part # C25852
R350, R385: 0R; R_1210_3225Metric_Pad1.30x2.65mm_HandSolder; Part RC1210JR-070RL; JLCPCB Part # C137090
R351, R372: 330; R_0402_1005Metric; Part FRC0402J331 TS; JLCPCB Part # C2906929
R352, R373, R374, R375: 49.9; R_0201_0603Metric; Part FRC0201F49R9TS; JLCPCB Part # C7467280
R376: 1.5k; R_0402_1005Metric; Part 0402WGF1501TCE; JLCPCB Part # C25867
R377, R380, R382, R384, R386: 4.75k 1%; R_0402_1005Metric; Part 0402WGF4751TCE; JLCPCB Part # C25901; not fitted
R378, R379, R381, R383, R387, R389: 4.75k 1%; R_0402_1005Metric; Part 0402WGF4751TCE; JLCPCB Part # C25901
U55: LAN8742A; VQFN-24-1EP_4x4mm_P0.5mm_EP2.5x2.5mm_ThermalVias; Part LAN8742AI-CZ; JLCPCB Part # C153279
Y6: 25Mhz; Oscillator_SMD_Abracon_ASE-4Pin_3.2x2.5mm; Part SX2M25.000M20F30TNN; JLCPCB Part # C2901601

Connections:
+3V3MCU: C415.2, C418.2, C423.1, FB38.2, FB39.2, FB40.2, J10.9, J10.12, R327.2, R376.1, R377.1, R379.1, R381.1, R383.1, R386.1, U55.9 (VDDIO), Y6.4 (Vdd)
ERX_N: C429.2, J10.6 (RD-), R374.2, U55.22 (RXN)
ERX_P: C428.2, J10.3 (RD+), R375.2, U55.23 (RXP)
ETH_MCU_NRST: C422.2, R328.1, U55.15 (~RST)
ETH_RX_ERR: R377.2, R378.1, U55.10 (RXER/PHYAD0)
ETX_N: C427.2, J10.2 (TD-), R373.2, U55.20 (TXN)
ETX_P: C425.2, J10.1 (TD+), R352.2, U55.21 (TXP)
GND: C415.1, C416.1, C417.1, C418.1, C419.1, C420.2, C421.1, C422.1, C423.2, C424.1, C425.1, C426.2, C427.1, C428.1, C429.1, J10.8, R328.2, R329.2, R350.1, R378.2, R380.2, R382.2, R384.2, R387.2, R389.2, U55.25 (VSS), Y6.2 (GND)
LED1: R351.2, R389.1, U55.3 (LED1/REGOFF)
LED2: R372.2, R386.2, R387.1, U55.2 (LED2/~INTSEL)
MCU_ETH_CLK: U55.5 (XTAL1/CLKIN), Y6.3 (OUT)
MDIO_MCU.MDC: U55.13 (MDC)
MDIO_MCU.MDIO: R376.2, U55.12 (MDIO)
unnamed: C416.2, C417.2, FB38.1, U55.1 (VDD2A), U55.19 (VDD1A)
unnamed: C419.2, C420.1, C426.1, U55.6 (VDDCR)
unnamed: C421.2, J10.4 (TCT), J10.5 (RCT), R385.1
unnamed: C424.2, FB40.1, R352.1, R373.1, R374.1, R375.1
unnamed: FB39.1, R385.2
unnamed: J10.10, R351.1
unnamed: J10.11, R372.1
unnamed: J10.SH, R350.2
unnamed: R327.1, Y6.1 (EN)
unnamed: R329.1, U55.24 (RBIAS)
RMII_MCU.RMII_CRS_DV: R379.2, R380.1, U55.11 (CRS_DV/MODE2)
RMII_MCU.RMII_REF_CLK: U55.14 (~INT/REFCLKO)
RMII_MCU.RMII_RXD0: R383.2, R384.1, U55.8 (RXD0/MODE0)
RMII_MCU.RMII_RXD1: R381.2, R382.1, U55.7 (RXD1/MODE1)
RMII_MCU.RMII_TXD0: U55.17 (TXD0)
RMII_MCU.RMII_TXD1: U55.18 (TXD1)
RMII_MCU.RMII_TX_EN: U55.16 (TXEN)

Notes on the sheet:
MODE1
Configuration straps
Pulling LED1/REGOFF low will enable internal +1V2 regulator
MODE2
PHYADD0
MODE0
REFCLK0 Pull down nINTSEL/LED2 to output clock on REFCLKO
