electrodyssey/NASR-M/eth_ps.kicad_sch

## KiCad design eth_ps.kicad_sch (2025-10-22)

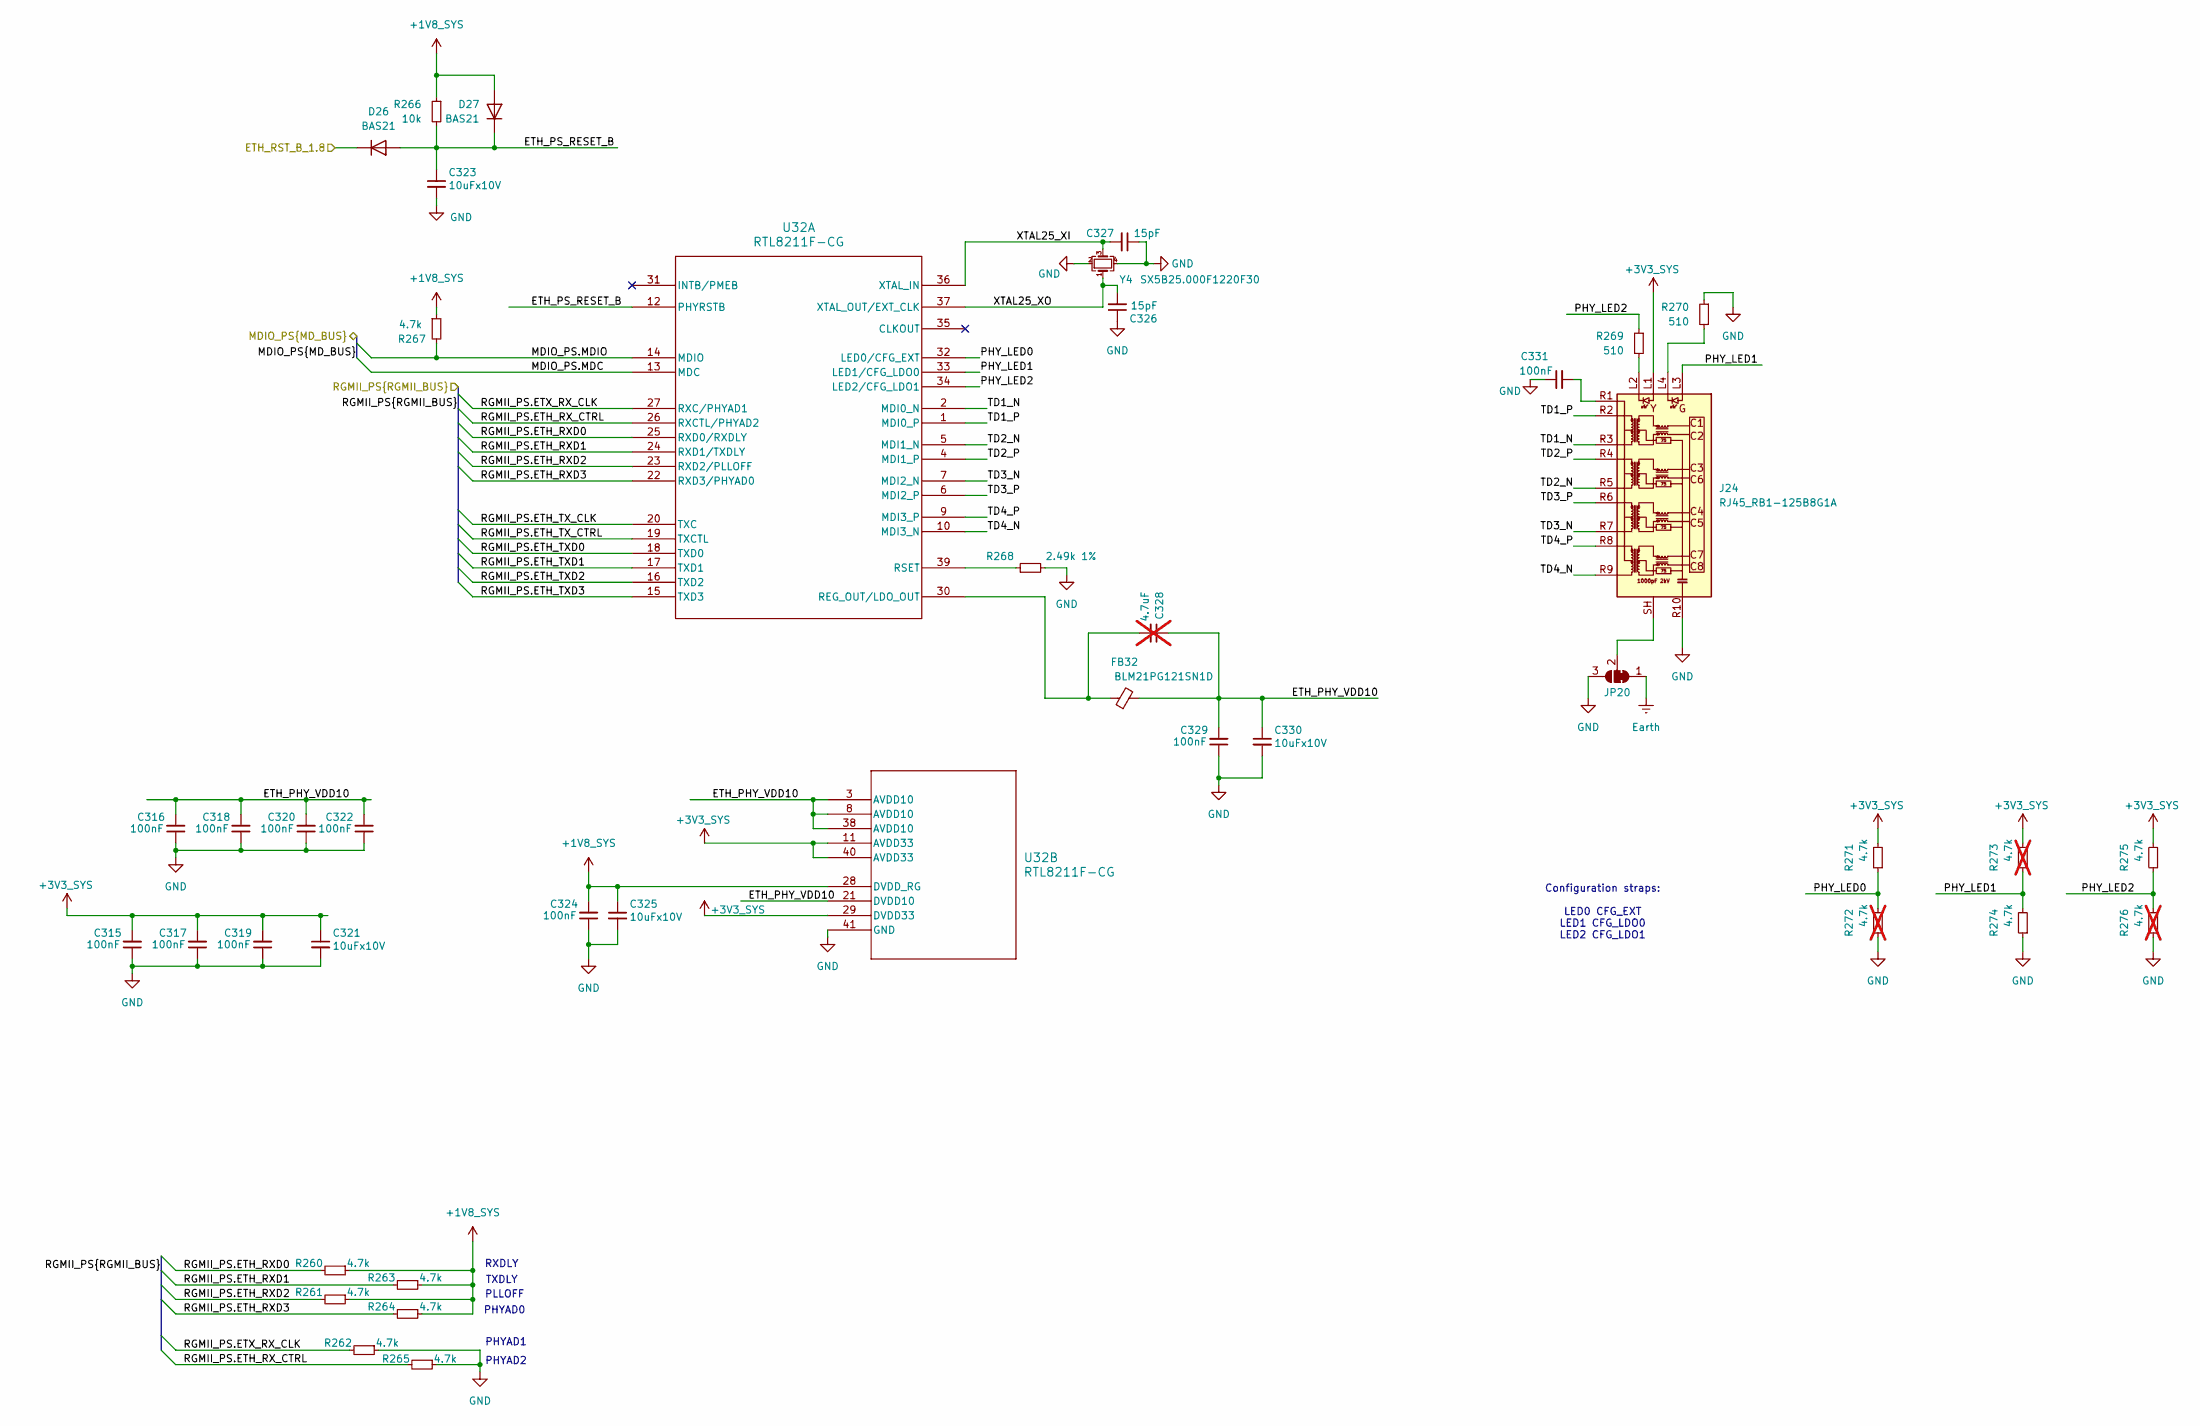
[picture p48: schematic eth_ps.kicad_sch]

Parts:
C315, C316, C317, C318, C319, C320, C322, C324, C329, C331: 100nF; C_0402_1005Metric; Part CC0402JRX7R8BB104; JLCPCB Part # C541465
C321, C323, C325, C330: 10uFx10V; C_0805_2012Metric; Part CL21A106KPFNNNE; JLCPCB Part # C17024
C326, C327: 15pF; C_0603_1608Metric; Part CL10C150JB8NNNC; JLCPCB Part # C1644
C328: 4.7uF; C_0402_1005Metric; Part 04026D475MAT2A; JLCPCB Part # C2170363; not fitted
D26, D27: BAS21; SOT-23; JLCPCB Part # C8661
FB32: BLM21PG121SN1D; L_0805_2012Metric; Part BLM21PG121SN1D; JLCPCB Part # C79382
J24: RJ45_RB1-125B8G1A; RJ45_UDE_RB1-125B8G1A; Part RJ45_RB1-125B8G1A; JLCPCB Part # C363353
JP20: SolderJumper_3_Bridged12; SolderJumper-3_P1.3mm_Bridged12_RoundedPad1.0x1.5mm_NumberL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
R260, R261, R262, R263, R264, R265, R267, R271, R274, R275: 4.7k; R_0402_1005Metric; Part 0402WGF4701TCE; JLCPCB Part # C25900
R266: 10k; R_0402_1005Metric; Part 0402WGF1002TCE; JLCPCB Part # C25744
R268: 2.49k 1%; R_0603_1608Metric; Part 0603WAF2491T5E; JLCPCB Part # C22908
R269, R270: 510; R_0402_1005Metric; Part 0402WGF5100TCE; JLCPCB Part # C25123
R272, R273, R276: 4.7k; R_0402_1005Metric; Part 0402WGF4701TCE; JLCPCB Part # C25900; not fitted
U32: RTL8211F-CG; RTL8211F-CG_RTK; JLCPCB Part # C187932
Y4: SX5B25.000F1220F30; Crystal_SMD_5032-4Pin_5.0x3.2mm; Part SX5B25.000F1220F30; JLCPCB Part # C2901635

Connections:
+1V8_SYS: C324.2, C325.1, D27.1 (A), R260.1, R261.1, R263.1, R264.1, R266.1, R267.1, U32.28 (DVDD_RG)
+3V3_SYS: C315.2, C317.2, C319.2, C321.1, J24.L1, R271.2, R273.2, R275.2, U32.11 (AVDD33), U32.29 (DVDD33), U32.40 (AVDD33)
ETH_PHY_VDD10: C316.2, C318.2, C320.2, C322.2, C328.1, C329.2, C330.1, FB32.2, U32.3 (AVDD10), U32.8 (AVDD10), U32.21 (DVDD10), U32.38 (AVDD10)
ETH_PS_RESET_B: C323.1, D26.1 (A), D27.3 (K), R266.2, U32.12 (PHYRSTB)
ETH_RST_B_1.8: D26.3 (K)
Earth: JP20.1 (A)
GND: C315.1, C316.1, C317.1, C318.1, C319.1, C320.1, C321.2, C322.1, C323.2, C324.1, C325.2, C326.1, C327.1, C329.1, C330.2, C331.1, J24.R10 (GND), JP20.3 (B), R262.1, R265.1, R268.2, R270.1, R272.1, R274.1, R276.1, U32.41 (GND), Y4.2, Y4.4
MDIO_PS.MDC: U32.13 (MDC)
MDIO_PS.MDIO: R267.2, U32.14 (MDIO)
unnamed: C328.2, FB32.1, U32.30 (REG_OUT/LDO_OUT)
unnamed: C331.2, J24.R1 (CT)
unnamed: J24.L2, R269.2
unnamed: J24.L4, R270.2
unnamed: J24.SH, JP20.2 (C)
unnamed: R268.1, U32.39 (RSET)
PHY_LED0: R271.1, R272.2, U32.32 (LED0/CFG_EXT)
PHY_LED1: J24.L3, R273.1, R274.2, U32.33 (LED1/CFG_LDO0)
PHY_LED2: R269.1, R275.1, R276.2, U32.34 (LED2/CFG_LDO1)
RGMII_PS.ETH_RXD0: R260.2, U32.25 (RXD0/RXDLY)
RGMII_PS.ETH_RXD1: R263.2, U32.24 (RXD1/TXDLY)
RGMII_PS.ETH_RXD2: R261.2, U32.23 (RXD2/PLLOFF)
RGMII_PS.ETH_RXD3: R264.2, U32.22 (RXD3/PHYAD0)
RGMII_PS.ETH_RX_CTRL: R265.2, U32.26 (RXCTL/PHYAD2)
RGMII_PS.ETH_TXD0: U32.18 (TXD0)
RGMII_PS.ETH_TXD1: U32.17 (TXD1)
RGMII_PS.ETH_TXD2: U32.16 (TXD2)
RGMII_PS.ETH_TXD3: U32.15 (TXD3)
RGMII_PS.ETH_TX_CLK: U32.20 (TXC)
RGMII_PS.ETH_TX_CTRL: U32.19 (TXCTL)
RGMII_PS.ETX_RX_CLK: R262.2, U32.27 (RXC/PHYAD1)
TD1_N: J24.R3 (TD1-), U32.2 (MDI0_N)
TD1_P: J24.R2 (TD1+), U32.1 (MDI0_P)
TD2_N: J24.R5 (TD2-), U32.5 (MDI1_N)
TD2_P: J24.R4 (TD2+), U32.4 (MDI1_P)
TD3_N: J24.R7 (TD3-), U32.7 (MDI2_N)
TD3_P: J24.R6 (TD3+), U32.6 (MDI2_P)
TD4_N: J24.R9 (TD4-), U32.10 (MDI3_N)
TD4_P: J24.R8 (TD4+), U32.9 (MDI3_P)
XTAL25_XI: C327.2, U32.36 (XTAL_IN), Y4.3
XTAL25_XO: C326.2, U32.37 (XTAL_OUT/EXT_CLK), Y4.1

Notes on the sheet:
TXDLY
PHYAD0
PHYAD1
PHYAD2
PLLOFF
Configuration straps: LED0 CFG_EXT LED1 CFG_LDO0 LED2 CFG_LDO1
RXDLY
