electrodyssey/NASR-M/ethconn.kicad_sch

## KiCad design ethconn.kicad_sch (2025-09-22)

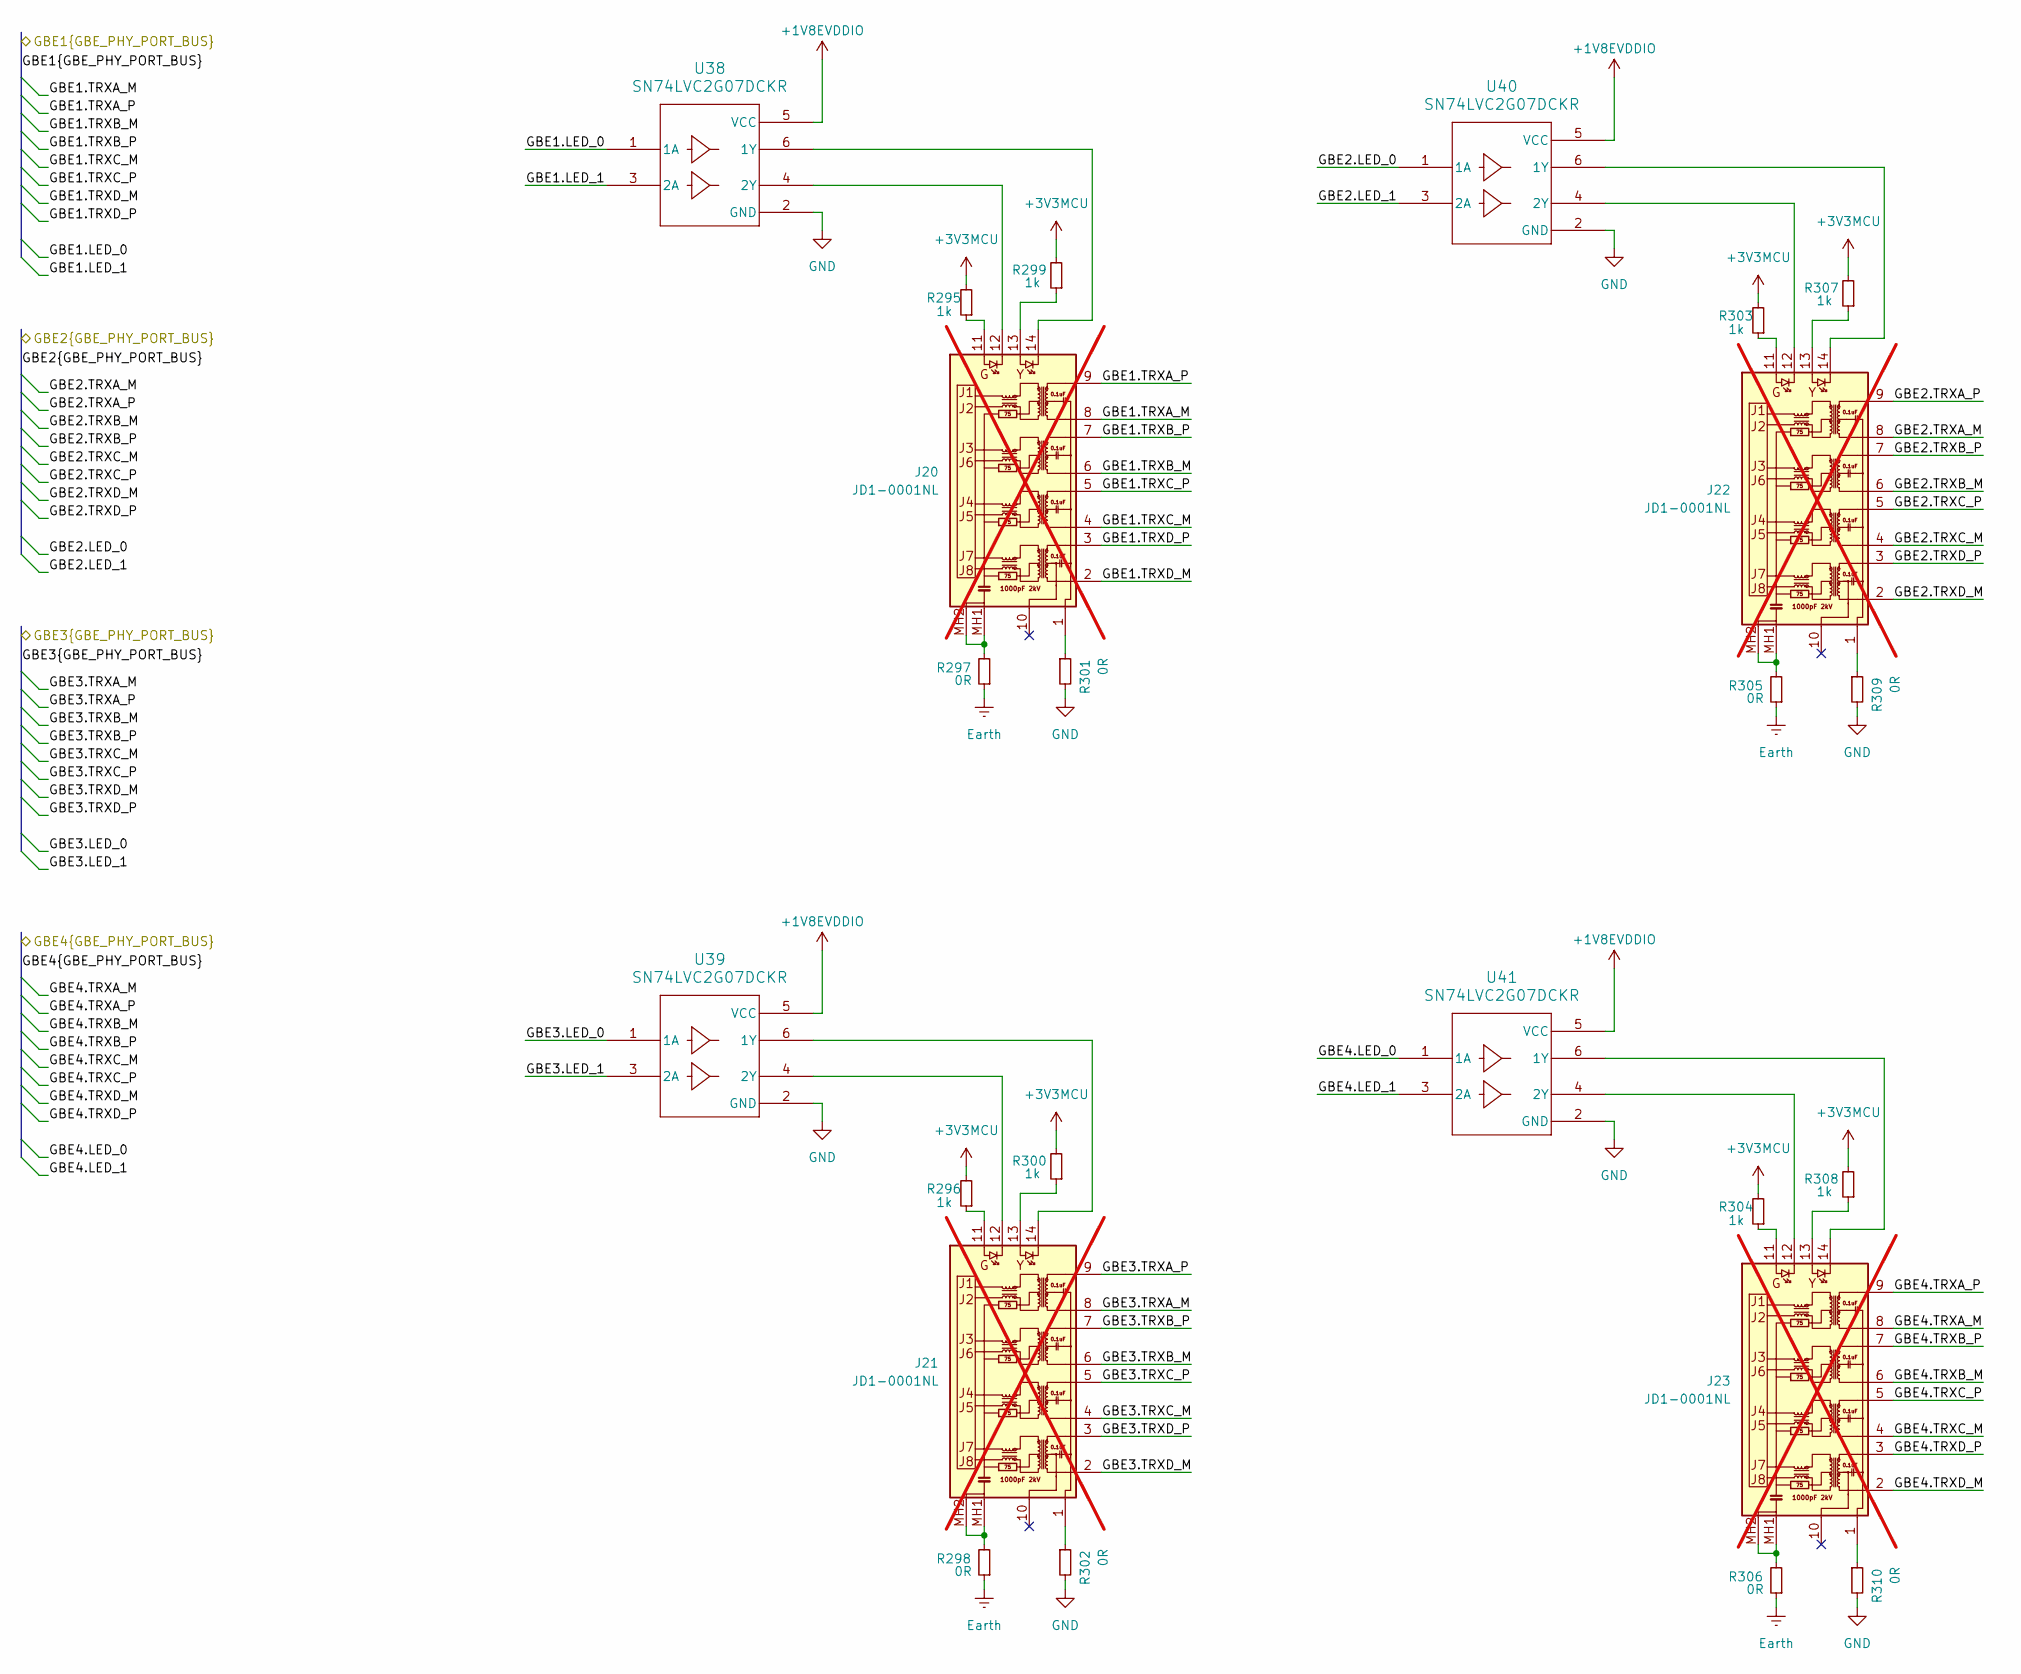
[picture p49: schematic ethconn.kicad_sch]

Parts:
J20, J21, J22, J23: JD1-0001NL; JD10001NL; Part JD1-0001NL; Mouser 673-JD1-0001NL; not fitted
R295, R296, R299, R300, R303, R304, R307, R308: 1k; R_0402_1005Metric; Part 0402WGF1001TCE; JLCPCB Part # C11702
R297, R298, R305, R306: 0R; R_1210_3225Metric_Pad1.30x2.65mm_HandSolder; Part RC1210JR-070RL; JLCPCB Part # C137090
R301, R302, R309, R310: 0R; R_0603_1608Metric; Part 0603WAF0000T5E; JLCPCB Part # C21189
U38, U39, U40, U41: SN74LVC2G07DCKR; DCK6; Part SN74LVC2G07DCKR; JLCPCB Part # C7849

Connections:
+1V8EVDDIO: U38.5 (VCC), U39.5 (VCC), U40.5 (VCC), U41.5 (VCC)
+3V3MCU: R295.2, R296.2, R299.2, R300.2, R303.2, R304.2, R307.2, R308.2
Earth: R297.1, R298.1, R305.1, R306.1
GBE1.LED_0: U38.1 (1A)
GBE1.LED_1: U38.3 (2A)
GBE1.TRXA_M: J20.8 (TD1-)
GBE1.TRXA_P: J20.9 (TD1+)
GBE1.TRXB_M: J20.6 (TD2-)
GBE1.TRXB_P: J20.7 (TD2+)
GBE1.TRXC_M: J20.4 (TD3-)
GBE1.TRXC_P: J20.5 (TD3+)
GBE1.TRXD_M: J20.2 (TD4-)
GBE1.TRXD_P: J20.3 (TD4+)
GBE2.LED_0: U40.1 (1A)
GBE2.LED_1: U40.3 (2A)
GBE2.TRXA_M: J22.8 (TD1-)
GBE2.TRXA_P: J22.9 (TD1+)
GBE2.TRXB_M: J22.6 (TD2-)
GBE2.TRXB_P: J22.7 (TD2+)
GBE2.TRXC_M: J22.4 (TD3-)
GBE2.TRXC_P: J22.5 (TD3+)
GBE2.TRXD_M: J22.2 (TD4-)
GBE2.TRXD_P: J22.3 (TD4+)
GBE3.LED_0: U39.1 (1A)
GBE3.LED_1: U39.3 (2A)
GBE3.TRXA_M: J21.8 (TD1-)
GBE3.TRXA_P: J21.9 (TD1+)
GBE3.TRXB_M: J21.6 (TD2-)
GBE3.TRXB_P: J21.7 (TD2+)
GBE3.TRXC_M: J21.4 (TD3-)
GBE3.TRXC_P: J21.5 (TD3+)
GBE3.TRXD_M: J21.2 (TD4-)
GBE3.TRXD_P: J21.3 (TD4+)
GBE4.LED_0: U41.1 (1A)
GBE4.LED_1: U41.3 (2A)
GBE4.TRXA_M: J23.8 (TD1-)
GBE4.TRXA_P: J23.9 (TD1+)
GBE4.TRXB_M: J23.6 (TD2-)
GBE4.TRXB_P: J23.7 (TD2+)
GBE4.TRXC_M: J23.4 (TD3-)
GBE4.TRXC_P: J23.5 (TD3+)
GBE4.TRXD_M: J23.2 (TD4-)
GBE4.TRXD_P: J23.3 (TD4+)
GND: R301.2, R302.2, R309.2, R310.2, U38.2 (GND), U39.2 (GND), U40.2 (GND), U41.2 (GND)
unnamed: J20.1 (CTCAP), R301.1
unnamed: J20.11 (GLED_A), R295.1
unnamed: J20.12 (GLED_C), U38.4 (2Y)
unnamed: J20.13 (YLED_A), R299.1
unnamed: J20.14 (YLED_C), U38.6 (1Y)
unnamed: J20.MH1, J20.MH2, R297.2
unnamed: J21.1 (CTCAP), R302.1
unnamed: J21.11 (GLED_A), R296.1
unnamed: J21.12 (GLED_C), U39.4 (2Y)
unnamed: J21.13 (YLED_A), R300.1
unnamed: J21.14 (YLED_C), U39.6 (1Y)
unnamed: J21.MH1, J21.MH2, R298.2
unnamed: J22.1 (CTCAP), R309.1
unnamed: J22.11 (GLED_A), R303.1
unnamed: J22.12 (GLED_C), U40.4 (2Y)
unnamed: J22.13 (YLED_A), R307.1
unnamed: J22.14 (YLED_C), U40.6 (1Y)
unnamed: J22.MH1, J22.MH2, R305.2
unnamed: J23.1 (CTCAP), R310.1
unnamed: J23.11 (GLED_A), R304.1
unnamed: J23.12 (GLED_C), U41.4 (2Y)
unnamed: J23.13 (YLED_A), R308.1
unnamed: J23.14 (YLED_C), U41.6 (1Y)
unnamed: J23.MH1, J23.MH2, R306.2
