electrodyssey/NASR-M/ethsw.kicad_sch

## KiCad design ethsw.kicad_sch (2025-09-22)

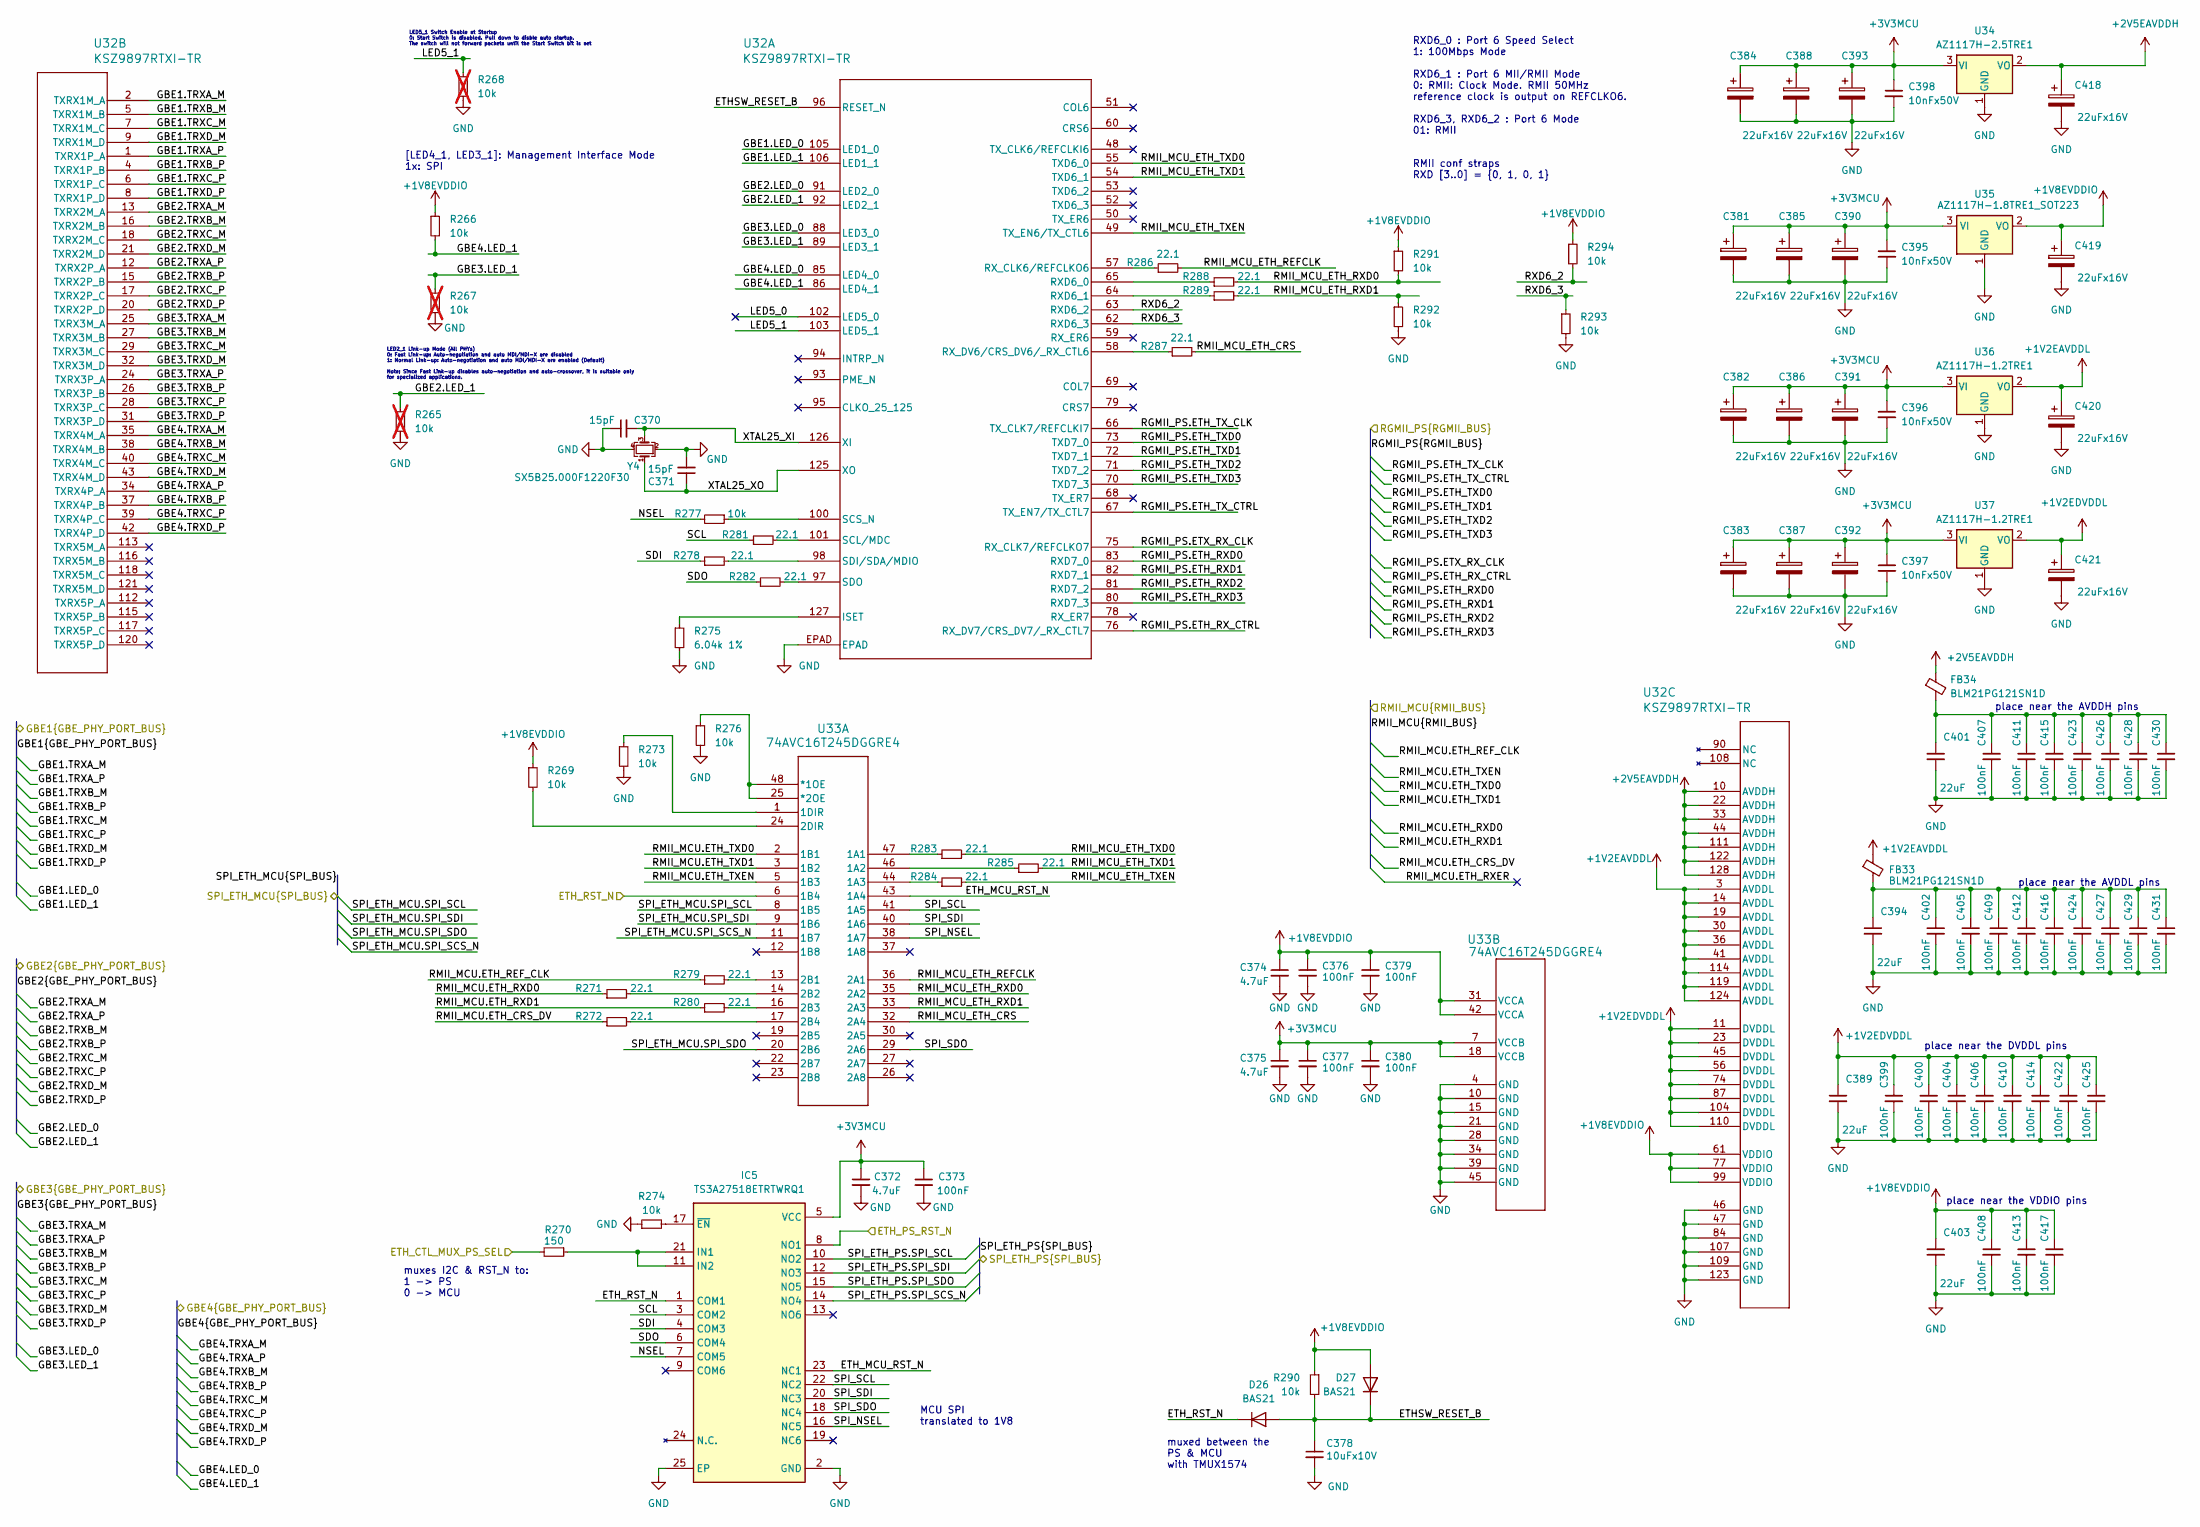
[picture p50: schematic ethsw.kicad_sch]

Parts:
C370, C371: 15pF; C_0603_1608Metric; Part CC0603JRNPO0BN150; JLCPCB Part # C327117
C372, C374, C375: 4.7uF; C_0402_1005Metric; Part 04026D475MAT2A; JLCPCB Part # C2170363
C373, C376, C377, C379, C380, C399, C400, C402, C404, C405, C406, C407, C408, C409, C410, C411, C412, C413, C414, C415, C416, C417, C422, C423, C424, C425, C426, C427, C428, C429, C430, C431: 100nF; C_0402_1005Metric; Part CC0402JRX7R8BB104; JLCPCB Part # C541465
C378: 10uFx10V; C_0805_2012Metric; Part CS2012X7R106M100NRE; JLCPCB Part # C5189822
C381, C382, C383, C384, C385, C386, C387, C388, C390, C391, C392, C393, C418, C419, C420, C421: 22uFx16V; CP_EIA-6032-15_Kemet-U; Part T494C226M016AT; JLCPCB Part # C1952930
C389, C394, C401, C403: 22uF; C_0805_2012Metric; Part GRM187R61A226ME15D; JLCPCB Part # C361061
C395, C396, C397, C398: 10nFx50V; C_1206_3216Metric; JLCPCB Part # C513774
D26, D27: BAS21; SOT-23
FB33, FB34: BLM21PG121SN1D; L_0805_2012Metric; Part BLM21PG121SN1D; JLCPCB Part # C79382
IC5: TS3A27518ETRTWRQ1; QFN50P400X400X80-25N-D; Mouser Part Number 595-S3A27518ETRTWRQ1
R265, R267, R268: 10k; R_0402_1005Metric; Part 0402WGF1002TCE; JLCPCB Part # C25744; not fitted
R266, R269, R273, R274, R276, R277, R290, R291, R292, R293, R294: 10k; R_0402_1005Metric; Part 0402WGF1002TCE; JLCPCB Part # C25744
R270: 150; R_0402_1005Metric; Part WR04X1500FTL; JLCPCB Part # C168203
R271, R272, R278, R279, R280, R281, R282, R283, R284, R285, R286, R287, R288, R289: 22.1; R_0402_1005Metric; Part WR04X22R1FTL; JLCPCB Part # C170264
R275: 6.04k 1%; R_0402_1005Metric; Part RC0402DR-076K04L; JLCPCB Part # C309541
U32: KSZ9897RTXI-TR; TQFP-EP128_TX_MCH
U33: 74AVC16T245DGGRE4; DGG48
U34: AZ1117H-2.5TRE1; SOT-223-3_TabPin2; Part AZ1117H-2.5TRE1; JLCPCB Part # C526404
U35: AZ1117H-1.8TRE1_SOT223; SOT-223-3_TabPin2; Part LM1117MPX-1.8/NOPB; JLCPCB Part # C9660
U36, U37: AZ1117H-1.2TRE1; SOT-223-3_TabPin2; Part AZ1117H-1.2TRE1; JLCPCB Part # C110105
Y4: SX5B25.000F1220F30; Crystal_SMD_5032-4Pin_5.0x3.2mm; Part SX5B25.000F1220F30; JLCPCB Part # C2901635

Connections:
+1V2EAVDDL: C420.1, FB33.1, U32.3 (AVDDL), U32.14 (AVDDL), U32.19 (AVDDL), U32.30 (AVDDL), U32.36 (AVDDL), U32.41 (AVDDL), U32.114 (AVDDL), U32.119 (AVDDL), U32.124 (AVDDL), U36.2 (VO)
+1V2EDVDDL: C389.1, C399.1, C400.1, C404.1, C406.1, C410.1, C414.1, C421.1, C422.1, C425.1, U32.11 (DVDDL), U32.23 (DVDDL), U32.45 (DVDDL), U32.56 (DVDDL), U32.74 (DVDDL), U32.87 (DVDDL), U32.104 (DVDDL), U32.110 (DVDDL), U37.2 (VO)
+1V8EVDDIO: C374.1, C376.1, C379.1, C403.1, C408.1, C413.1, C417.1, C419.1, D27.1 (A), R266.1, R269.1, R290.1, R291.1, R294.1, U32.61 (VDDIO), U32.77 (VDDIO), U32.99 (VDDIO), U33.31 (VCCA), U33.42 (VCCA), U35.2 (VO)
+2V5EAVDDH: C418.1, FB34.1, U32.10 (AVDDH), U32.22 (AVDDH), U32.33 (AVDDH), U32.44 (AVDDH), U32.111 (AVDDH), U32.122 (AVDDH), U32.128 (AVDDH), U34.2 (VO)
+3V3MCU: C372.1, C373.1, C375.1, C377.1, C380.1, C381.1, C382.1, C383.1, C384.1, C385.1, C386.1, C387.1, C388.1, C390.1, C391.1, C392.1, C393.1, C395.1, C396.1, C397.1, C398.1, IC5.5 (VCC), U33.7 (VCCB), U33.18 (VCCB), U34.3 (VI), U35.3 (VI), U36.3 (VI), U37.3 (VI)
ETHSW_RESET_B: C378.1, D26.1 (A), D27.3 (K), R290.2, U32.96 (RESET_N)
ETH_CTL_MUX_PS_SEL: R270.2
ETH_MCU_RST_N: IC5.23 (NC1), U33.43 (1A4)
ETH_PS_RST_N: IC5.8 (NO1)
ETH_RST_N: D26.3 (K), IC5.1 (COM1), U33.6 (1B4)
GBE1.LED_0: U32.105 (LED1_0)
GBE1.LED_1: U32.106 (LED1_1)
GBE1.TRXA_M: U32.2 (TXRX1M_A)
GBE1.TRXA_P: U32.1 (TXRX1P_A)
GBE1.TRXB_M: U32.5 (TXRX1M_B)
GBE1.TRXB_P: U32.4 (TXRX1P_B)
GBE1.TRXC_M: U32.7 (TXRX1M_C)
GBE1.TRXC_P: U32.6 (TXRX1P_C)
GBE1.TRXD_M: U32.9 (TXRX1M_D)
GBE1.TRXD_P: U32.8 (TXRX1P_D)
GBE2.LED_0: U32.91 (LED2_0)
GBE2.LED_1: R265.1, U32.92 (LED2_1)
GBE2.TRXA_M: U32.13 (TXRX2M_A)
GBE2.TRXA_P: U32.12 (TXRX2P_A)
GBE2.TRXB_M: U32.16 (TXRX2M_B)
GBE2.TRXB_P: U32.15 (TXRX2P_B)
GBE2.TRXC_M: U32.18 (TXRX2M_C)
GBE2.TRXC_P: U32.17 (TXRX2P_C)
GBE2.TRXD_M: U32.21 (TXRX2M_D)
GBE2.TRXD_P: U32.20 (TXRX2P_D)
GBE3.LED_0: U32.88 (LED3_0)
GBE3.LED_1: R267.1, U32.89 (LED3_1)
GBE3.TRXA_M: U32.25 (TXRX3M_A)
GBE3.TRXA_P: U32.24 (TXRX3P_A)
GBE3.TRXB_M: U32.27 (TXRX3M_B)
GBE3.TRXB_P: U32.26 (TXRX3P_B)
GBE3.TRXC_M: U32.29 (TXRX3M_C)
GBE3.TRXC_P: U32.28 (TXRX3P_C)
GBE3.TRXD_M: U32.32 (TXRX3M_D)
GBE3.TRXD_P: U32.31 (TXRX3P_D)
GBE4.LED_0: U32.85 (LED4_0)
GBE4.LED_1: R266.2, U32.86 (LED4_1)
GBE4.TRXA_M: U32.35 (TXRX4M_A)
GBE4.TRXA_P: U32.34 (TXRX4P_A)
GBE4.TRXB_M: U32.38 (TXRX4M_B)
GBE4.TRXB_P: U32.37 (TXRX4P_B)
GBE4.TRXC_M: U32.40 (TXRX4M_C)
GBE4.TRXC_P: U32.39 (TXRX4P_C)
GBE4.TRXD_M: U32.43 (TXRX4M_D)
GBE4.TRXD_P: U32.42 (TXRX4P_D)
GND: C370.1, C371.2, C372.2, C373.2, C374.2, C375.2, C376.2, C377.2, C378.2, C379.2, C380.2, C381.2, C382.2, C383.2, C384.2, C385.2, C386.2, C387.2, C388.2, C389.2, C390.2, C391.2, C392.2, C393.2, C394.2, C395.2, C396.2, C397.2, C398.2, C399.2, C400.2, C401.2, C402.2, C403.2, C404.2, C405.2, C406.2, C407.2, C408.2, C409.2, C410.2, C411.2, C412.2, C413.2, C414.2, C415.2, C416.2, C417.2, C418.2, C419.2, C420.2, C421.2, C422.2, C423.2, C424.2, C425.2, C426.2, C427.2, C428.2, C429.2, C430.2, C431.2, IC5.2 (GND), IC5.25 (EP), R265.2, R267.2, R268.2, R273.2, R274.1, R275.2, R276.2, R292.2, R293.2, U32.46 (GND), U32.47 (GND), U32.84 (GND), U32.107 (GND), U32.109 (GND), U32.123 (GND), U32.EPAD, U33.4 (GND), U33.10 (GND), U33.15 (GND), U33.21 (GND), U33.28 (GND), U33.34 (GND), U33.39 (GND), U33.45 (GND), U34.1 (GND), U35.1 (GND), U36.1 (GND), U37.1 (GND), Y4.2, Y4.4
LED5_0: U32.102 (LED5_0)
LED5_1: R268.1, U32.103 (LED5_1)
NSEL: IC5.7 (COM5), R277.2
unnamed: C394.1, C402.1, C405.1, C409.1, C412.1, C416.1, C424.1, C427.1, C429.1, C431.1, FB33.2
unnamed: C401.1, C407.1, C411.1, C415.1, C423.1, C426.1, C428.1, C430.1, FB34.2
unnamed: IC5.11 (IN2), IC5.21 (IN1), R270.1
unnamed: IC5.17 (~EN), R274.2
unnamed: R269.2, U33.24 (2DIR)
unnamed: R271.2, U33.14 (2B2)
unnamed: R272.2, U33.17 (2B4)
unnamed: R273.1, U33.1 (1DIR)
unnamed: R275.1, U32.127 (ISET)
unnamed: R276.1, U33.25 (*2OE), U33.48 (*1OE)
unnamed: R277.1, U32.100 (SCS_N)
unnamed: R278.2, U32.98 (SDI/SDA/MDIO)
unnamed: R279.2, U33.13 (2B1)
unnamed: R280.2, U33.16 (2B3)
unnamed: R281.2, U32.101 (SCL/MDC)
unnamed: R282.2, U32.97 (SDO)
unnamed: R283.1, U33.47 (1A1)
unnamed: R284.1, U33.44 (1A3)
unnamed: R285.1, U33.46 (1A2)
unnamed: R286.1, U32.57 (RX_CLK6/REFCLKO6)
unnamed: R287.1, U32.58 (RX_DV6/CRS_DV6/_RX_CTL6)
unnamed: R288.1, U32.65 (RXD6_0)
unnamed: R289.1, U32.64 (RXD6_1)
RGMII_PS.ETH_RXD0: U32.83 (RXD7_0)
RGMII_PS.ETH_RXD1: U32.82 (RXD7_1)
RGMII_PS.ETH_RXD2: U32.81 (RXD7_2)
RGMII_PS.ETH_RXD3: U32.80 (RXD7_3)
RGMII_PS.ETH_RX_CTRL: U32.76 (RX_DV7/CRS_DV7/_RX_CTL7)
RGMII_PS.ETH_TXD0: U32.73 (TXD7_0)
RGMII_PS.ETH_TXD1: U32.72 (TXD7_1)
RGMII_PS.ETH_TXD2: U32.71 (TXD7_2)
RGMII_PS.ETH_TXD3: U32.70 (TXD7_3)
RGMII_PS.ETH_TX_CLK: U32.66 (TX_CLK7/REFCLKI7)
RGMII_PS.ETH_TX_CTRL: U32.67 (TX_EN7/TX_CTL7)
RGMII_PS.ETX_RX_CLK: U32.75 (RX_CLK7/REFCLKO7)
RMII_MCU.ETH_CRS_DV: R272.1
RMII_MCU.ETH_REF_CLK: R279.1
RMII_MCU.ETH_RXD0: R271.1
RMII_MCU.ETH_RXD1: R280.1
RMII_MCU.ETH_TXD0: U33.2 (1B1)
RMII_MCU.ETH_TXD1: U33.3 (1B2)
RMII_MCU.ETH_TXEN: U33.5 (1B3)
RMII_MCU_ETH_CRS: R287.2, U33.32 (2A4)
RMII_MCU_ETH_REFCLK: R286.2, U33.36 (2A1)
RMII_MCU_ETH_RXD0: R288.2, R291.2, U33.35 (2A2)
RMII_MCU_ETH_RXD1: R289.2, R292.1, U33.33 (2A3)
RMII_MCU_ETH_TXD0: R283.2, U32.55 (TXD6_0)
RMII_MCU_ETH_TXD1: R285.2, U32.54 (TXD6_1)
RMII_MCU_ETH_TXEN: R284.2, U32.49 (TX_EN6/TX_CTL6)
RXD6_2: R294.2, U32.63 (RXD6_2)
RXD6_3: R293.1, U32.62 (RXD6_3)
SCL: IC5.3 (COM2), R281.1
SDI: IC5.4 (COM3), R278.1
SDO: IC5.6 (COM4), R282.1
SPI_ETH_MCU.SPI_SCL: U33.8 (1B5)
SPI_ETH_MCU.SPI_SCS_N: U33.11 (1B7)
SPI_ETH_MCU.SPI_SDI: U33.9 (1B6)
SPI_ETH_MCU.SPI_SDO: U33.20 (2B6)
SPI_ETH_PS.SPI_SCL: IC5.10 (NO2)
SPI_ETH_PS.SPI_SCS_N: IC5.14 (NO4)
SPI_ETH_PS.SPI_SDI: IC5.12 (NO3)
SPI_ETH_PS.SPI_SDO: IC5.15 (NO5)
SPI_NSEL: IC5.16 (NC5), U33.38 (1A7)
SPI_SCL: IC5.22 (NC2), U33.41 (1A5)
SPI_SDI: IC5.20 (NC3), U33.40 (1A6)
SPI_SDO: IC5.18 (NC4), U33.29 (2A6)
XTAL25_XI: C370.2, U32.126 (XI), Y4.3
XTAL25_XO: C371.1, U32.125 (XO), Y4.1

Notes on the sheet:
muxed between the PS & MCU with TMUX1574
LED5_1 Switch Enable at Startup 0: Start Switch is disabled. Pull down to disble auto startup. The switch will not forward packets until the Start Switch bit is set
place near the AVDDL pins
[LED4_1, LED3_1]: Management Interface Mode 1x: SPI
place near the VDDIO pins
muxes I2C & RST_N to: 1 -> PS 0 -> MCU
MCU SPI translated to 1V8
LED2_1 Link-up Mode (All PHYs) 0: Fast Link-up: Auto-negotiation and auto MDI/MDI-X are disabled 1: Normal Link-up: Auto-negotiation and auto MDI/MDI-X are enabled (Default) Note: Since Fast Link-up disables auto-negotiation and auto-crossover, it is suitable only for specialized applications.
place near the AVDDH pins
RXD6_0 : Port 6 Speed Select 1: 100Mbps Mode RXD6_1 : Port 6 MII/RMII Mode 0: RMII: Clock Mode. RMII 50MHz reference clock is output on REFCLKO6. RXD6_3, RXD6_2 : Port 6 Mode 01: RMII
RMII conf straps RXD [3..0] = {0, 1, 0, 1}
place near the DVDDL pins
