electrodyssey/NASR-M/frontend.kicad_sch

## KiCad design frontend.kicad_sch (2025-09-22)

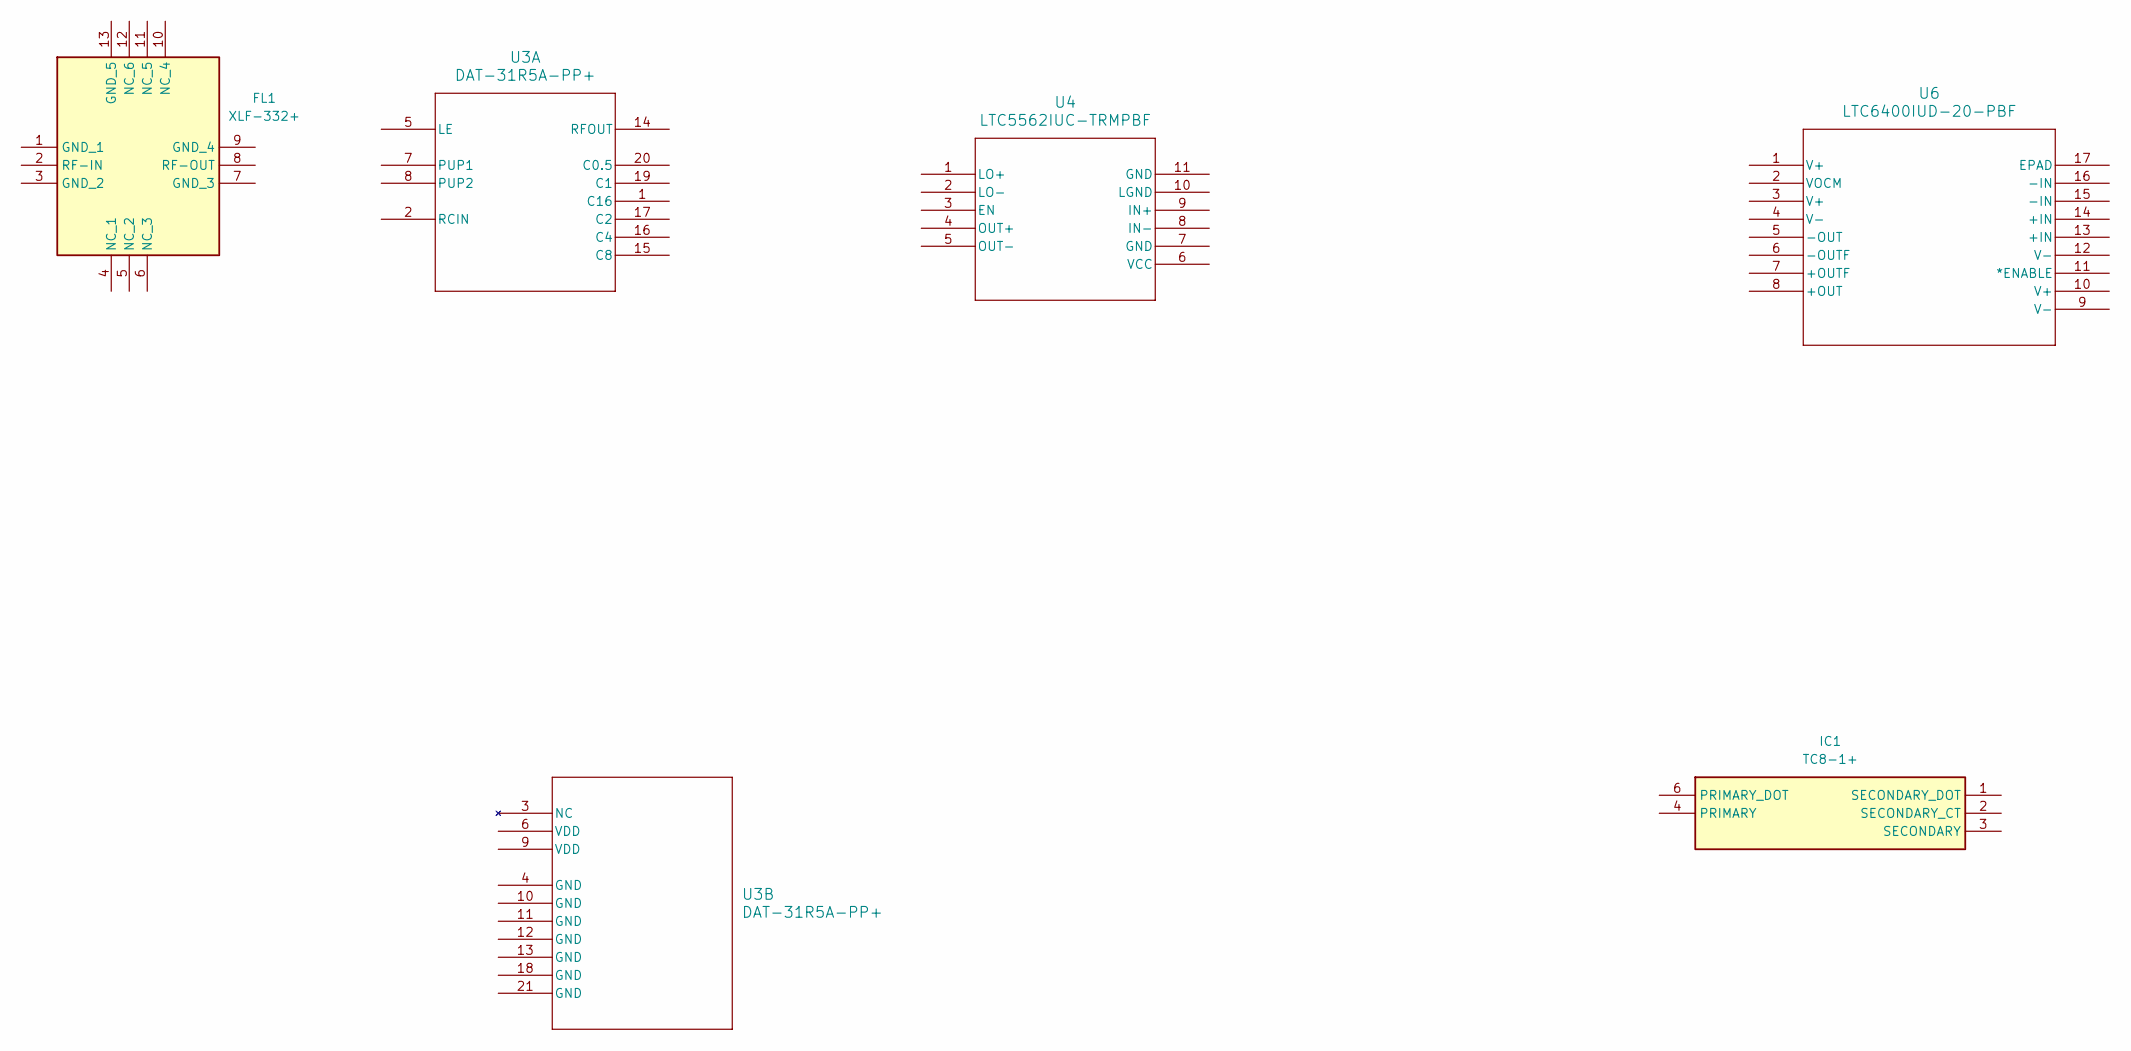
[picture p51: schematic frontend.kicad_sch]

Parts:
FL1: XLF-332+; QFN51P300X300X89-13N; Mouser Part Number 139-XLF-332
IC1: TC8-1+; TC81; Mouser Part Number 139-TC8-1
U3: DAT-31R5A-PP+; DG983-2_MNC
U4: LTC5562IUC-TRMPBF; 05-08-1534_ADI
U6: LTC6400IUD-20-PBF; QFN-16_UD_LIT
