electrodyssey/NASR-M/mcu.kicad_sch

## KiCad design mcu.kicad_sch (2025-10-22)

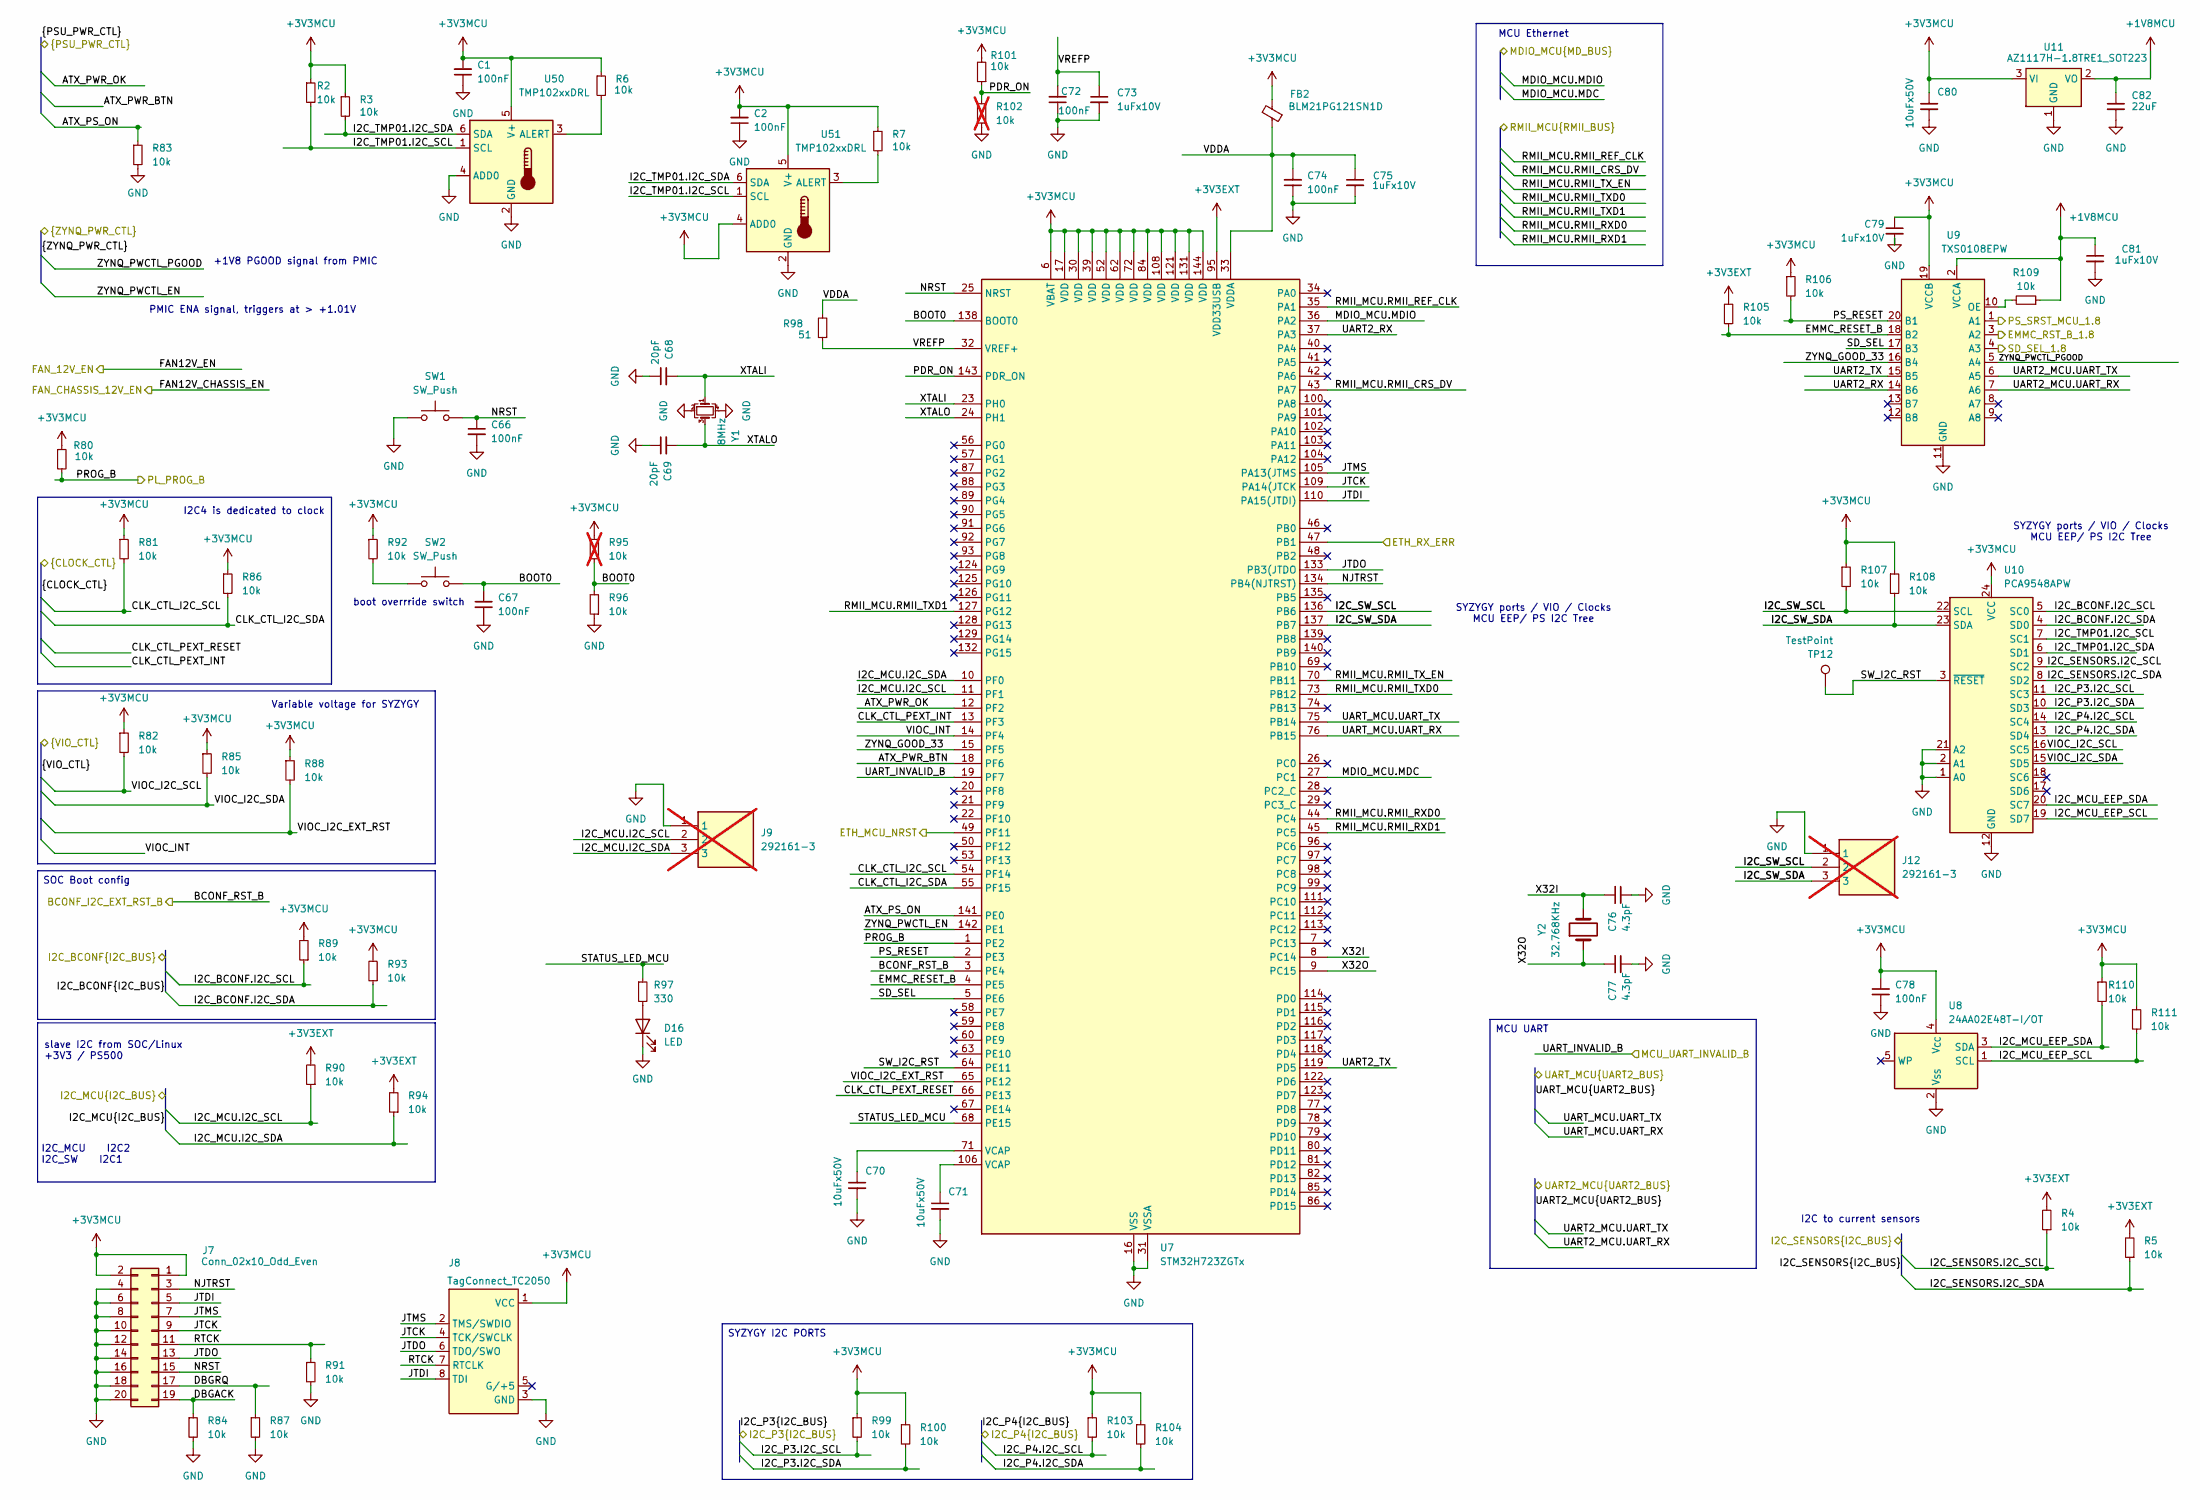
[picture p52: schematic mcu.kicad_sch]

Parts:
C1, C2, C66, C67, C72, C74, C78: 100nF; C_0402_1005Metric; Part CC0402JRX7R8BB104; JLCPCB Part # C541465
C68, C69: 20pF; C_0402_1005Metric; Part CC0402FRNPO9BN200; JLCPCB Part # C327010
C70, C71, C80: 10uFx50V; C_1206_3216Metric; Part CS3216X5R106K500NRI; JLCPCB Part # C513774
C73, C75, C79, C81: 1uFx10V; C_0603_1608Metric; JLCPCB Part # C841050
C76, C77: 4.3pF; C_0402_1005Metric; Part RF15N4R3A500CT; JLCPCB Part # C2918589
C82: 22uF; C_0805_2012Metric; Part CL21A226MQQNNNE; JLCPCB Part # C5674
D16: LED; LED_0805_2012Metric; Part HL-PSC-2012S11GC; JLCPCB Part # C497958
FB2: BLM21PG121SN1D; L_0805_2012Metric; Part BLM21PG121SN1D; JLCPCB Part # C79382
J7: Conn_02x10_Odd_Even; PinHeader_2x10_P2.00mm_Vertical_SMD; Part 3111-20MSNBK00R1; JLCPCB Part # C720760
J8: TagConnect_TC2050; Tag-Connect_TC2050-IDC-FP_2x05_P1.27mm_Vertical
J9, J12: 292161-3; SHDR3W60P0X200_1X3_780X360X680P; Mouser Part Number 571-292161-3; not fitted
R2, R3, R4, R5, R6, R7, R80, R81, R82, R83, R84, R85, R86, R87, R88, R89, R90, R91, R92, R93, R94, R96, R99, R100, R101, R103, R104, R105, R106, R107, R108, R109, R110, R111: 10k; R_0402_1005Metric; Part 0402WGF1002TCE; JLCPCB Part # C25744
R95, R102: 10k; R_0402_1005Metric; Part 0402WGF1002TCE; JLCPCB Part # C25744; not fitted
R97: 330; R_0402_1005Metric; Part 0402WGF3300TCE; JLCPCB Part # C25104
R98: 51; R_0402_1005Metric; Part FRC0402J510 TS; JLCPCB Part # C2906953
SW1: SW_Push; SW_Push_SPST_NO_Alps_SKRK; Part SKRKAHE020; JLCPCB Part # C202388
SW2: SW_Push; SW_Push_1P1T-MP_NO_Horizontal_Alps_SKRTLAE010; Part SKRTLAE010; JLCPCB Part # C110293
TP12: TestPoint; TestPoint_Pad_D1.0mm
U7: STM32H723ZGTx; LQFP-144_20x20mm_P0.5mm; JLCPCB Part # C730146
U8: 24AA02E48T-I/OT; SOT-23-5; Part 24AA02E48T-I/OT; JLCPCB Part # C38987
U9: TXS0108EPW; TSSOP-20_4.4x6.5mm_P0.65mm; Part TXS0108EPWR; JLCPCB Part # C17206
U10: PCA9548APW; TSSOP-24_4.4x7.8mm_P0.65mm; JLCPCB Part # C21198
U11: AZ1117H-1.8TRE1_SOT223; SOT-223-3_TabPin2; Part LM1117MPX-1.8/NOPB; JLCPCB Part # C9660
U50, U51: TMP102xxDRL; SOT-563; Part TMP102AIDRLR; JLCPCB Part # C99269
Y1: 8MHz; Crystal_SMD_5032-4Pin_5.0x3.2mm; Part SX5B8.000F1520F30; JLCPCB Part # C2901621
Y2: 32.768KHz; Crystal_SMD_3215-2Pin_3.2x1.5mm; Part X321532768KGD2SI; JLCPCB Part # C620155

Connections:
+1V8MCU: C81.1, C82.1, R109.1, U9.2 (VCCA), U11.2 (VO)
+3V3EXT: R4.2, R5.2, R90.2, R94.2, R105.1, U7.95 (VDD33USB)
+3V3MCU: C1.2, C2.2, C78.2, C79.1, C80.1, FB2.2, J7.1, J7.2, J8.1 (VCC), R2.1, R3.1, R6.1, R7.1, R80.1, R81.1, R82.1, R85.1, R86.1, R88.1, R89.2, R92.1, R93.2, R95.2, R99.1, R100.1, R101.2, R103.1, R104.1, R106.1, R107.1, R108.1, R110.1, R111.1, U7.6 (VBAT), U7.17 (VDD), U7.30 (VDD), U7.39 (VDD), U7.52 (VDD), U7.62 (VDD), U7.72 (VDD), U7.84 (VDD), U7.108 (VDD), U7.121 (VDD), U7.131 (VDD), U7.144 (VDD), U8.4 (V_{CC}), U9.19 (VCCB), U10.24 (VCC), U11.3 (VI), U50.5 (V+), U51.4 (ADD0), U51.5 (V+)
ATX_PS_ON: R83.1, U7.141 (PE0)
ATX_PWR_BTN: U7.18 (PF6)
ATX_PWR_OK: U7.12 (PF2)
BCONF_I2C_EXT_RST_B: U7.3 (PE4)
BOOT0: C67.1, R95.1, R96.2, SW2.2, U7.138 (BOOT0)
CLK_CTL_I2C_SCL: R81.2, U7.54 (PF14)
CLK_CTL_I2C_SDA: R86.2, U7.55 (PF15)
CLK_CTL_PEXT_INT: U7.13 (PF3)
CLK_CTL_PEXT_RESET: U7.66 (PE13)
DBGACK: J7.19, R84.1
DBGRQ: J7.17, R87.1
EMMC_RST_B_1.8: U9.3 (A2)
EMMC_RЕSЕT_B: R105.2, U7.4 (PE5), U9.18 (B2)
ETH_MCU_NRST: U7.49 (PF11)
ETH_RX_ERR: U7.47 (PB1)
GND: C1.1, C2.1, C66.2, C67.2, C68.1, C69.1, C70.2, C71.2, C72.1, C73.2, C74.1, C75.2, C76.1, C77.1, C78.1, C79.2, C80.2, C81.2, C82.2, D16.1 (K), J7.4, J7.6, J7.8, J7.10, J7.12, J7.14, J7.16, J7.18, J7.20, J8.3 (GND), J9.1, J12.1, R83.2, R84.2, R87.2, R91.2, R96.1, R102.1, SW1.1, U7.16 (VSS), U7.31 (VSSA), U7.38 (VSS), U7.51 (VSS), U7.61 (VSS), U7.83 (VSS), U7.94 (VSS), U7.107 (VSS), U7.120 (VSS), U7.130 (VSS), U8.2 (V_{SS}), U9.11 (GND), U10.1 (A0), U10.2 (A1), U10.12 (GND), U10.21 (A2), U11.1 (GND), U50.2 (GND), U50.4 (ADD0), U51.2 (GND), Y1.2, Y1.4
I2C_BCONF.I2C_SCL: R89.1, U10.5 (SC0)
I2C_BCONF.I2C_SDA: R93.1, U10.4 (SD0)
I2C_MCU.I2C_SCL: J9.2, R90.1, U7.11 (PF1)
I2C_MCU.I2C_SDA: J9.3, R94.1, U7.10 (PF0)
I2C_MCU_EEP_SCL: R111.2, U8.1 (SCL), U10.19 (SD7)
I2C_MCU_EEP_SDA: R110.2, U8.3 (SDA), U10.20 (SC7)
I2C_P3.I2C_SCL: R99.2, U10.11 (SC3)
I2C_P3.I2C_SDA: R100.2, U10.10 (SD3)
I2C_P4.I2C_SCL: R103.2, U10.14 (SC4)
I2C_P4.I2C_SDA: R104.2, U10.13 (SD4)
I2C_SENSORS.I2C_SCL: R4.1, U10.9 (SC2)
I2C_SENSORS.I2C_SDA: R5.1, U10.8 (SD2)
I2C_SW_SCL: J12.2, R107.2, U7.136 (PB6), U10.22 (SCL)
I2C_SW_SDA: J12.3, R108.2, U7.137 (PB7), U10.23 (SDA)
I2C_TMP01.I2C_SCL: R2.2, U10.7 (SC1), U50.1 (SCL), U51.1 (SCL)
I2C_TMP01.I2C_SDA: R3.2, U10.6 (SD1), U50.6 (SDA), U51.6 (SDA)
JTCK: J7.9, J8.4 (TCK/SWCLK), U7.109 (PA14(JTCK)
JTDI: J7.5, J8.8 (TDI), U7.110 (PA15(JTDI))
JTDO: J7.13, J8.6 (TDO/SWO), U7.133 (PB3(JTDO)
JTMS: J7.7, J8.2 (TMS/SWDIO), U7.105 (PA13(JTMS)
MCU_UART_INVALID_B: U7.19 (PF7)
MDIO_MCU.MDC: U7.27 (PC1)
MDIO_MCU.MDIO: U7.36 (PA2)
NJTRST: J7.3, U7.134 (PB4(NJTRST))
NRST: C66.1, J7.15, SW1.2, U7.25 (NRST)
unnamed: C70.1, U7.71 (VCAP)
unnamed: C71.1, U7.106 (VCAP)
unnamed: D16.2 (A), R97.2
unnamed: R6.2, U50.3 (ALERT)
unnamed: R7.2, U51.3 (ALERT)
unnamed: R92.2, SW2.1
unnamed: R109.2, U9.10 (OE)
PDR_ON: R101.1, R102.2, U7.143 (PDR_ON)
PL_PROG_B: R80.2, U7.1 (PE2)
PS_RESET: R106.2, U7.2 (PE3), U9.20 (B1)
PS_SRST_MCU_1.8: U9.1 (A1)
RMII_MCU.RMII_CRS_DV: U7.43 (PA7)
RMII_MCU.RMII_REF_CLK: U7.35 (PA1)
RMII_MCU.RMII_RXD0: U7.44 (PC4)
RMII_MCU.RMII_RXD1: U7.45 (PC5)
RMII_MCU.RMII_TXD0: U7.73 (PB12)
RMII_MCU.RMII_TXD1: U7.127 (PG12)
RMII_MCU.RMII_TX_EN: U7.70 (PB11)
RTCK: J7.11, J8.7 (RTCLK), R91.1
SD_SEL: U7.5 (PE6), U9.17 (B3)
SD_SEL_1.8: U9.4 (A3)
STATUS_LED_MCU: R97.1, U7.68 (PE15)
SW_I2C_RST: TP12.1, U7.64 (PE11), U10.3 (~RESET)
UART2_MCU.UART_RX: U9.7 (A6)
UART2_MCU.UART_TX: U9.6 (A5)
UART2_RX: U7.37 (PA3), U9.14 (B6)
UART2_TX: U7.119 (PD5), U9.15 (B5)
UART_MCU.UART_RX: U7.76 (PB15)
UART_MCU.UART_TX: U7.75 (PB14)
VDDA: C74.2, C75.1, FB2.1, R98.2, U7.33 (VDDA)
VIOC_I2C_EXT_RST: R88.2, U7.65 (PE12)
VIOC_I2C_SCL: R82.2, U10.16 (SC5)
VIOC_I2C_SDA: R85.2, U10.15 (SD5)
VIOC_INT: U7.14 (PF4)
VREFP: C72.2, C73.1, R98.1, U7.32 (VREF+)
X32I: C76.2, U7.8 (PC14), Y2.2
X32O: C77.2, U7.9 (PC15), Y2.1
XTALI: C68.2, U7.23 (PH0), Y1.1
XTALO: C69.2, U7.24 (PH1), Y1.3
ZYNQ_GOOD_33: U7.15 (PF5), U9.16 (B4)
ZYNQ_PWCTL_EN: U7.142 (PE1)
ZYNQ_PWCTL_PGOOD: U9.5 (A4)

Notes on the sheet:
slave I2C from SOC/Linux +3V3 / PS500
I2C to current sensors
MCU Ethernet
boot overrride switch
SYZYGY ports / VIO / Clocks MCU EEP/ PS I2C Tree
Variable voltage for SYZYGY
I2C_MCU I2C2 I2C_SW I2C1
PMIC ENA signal, triggers at > +1.01V
+1V8 PGOOD signal from PMIC
I2C4 is dedicated to clock
SOC Boot config
MCU UART
SYZYGY I2C PORTS
