electrodyssey/NASR-M/psddr3.kicad_sch

## KiCad design psddr3.kicad_sch (2025-10-22)

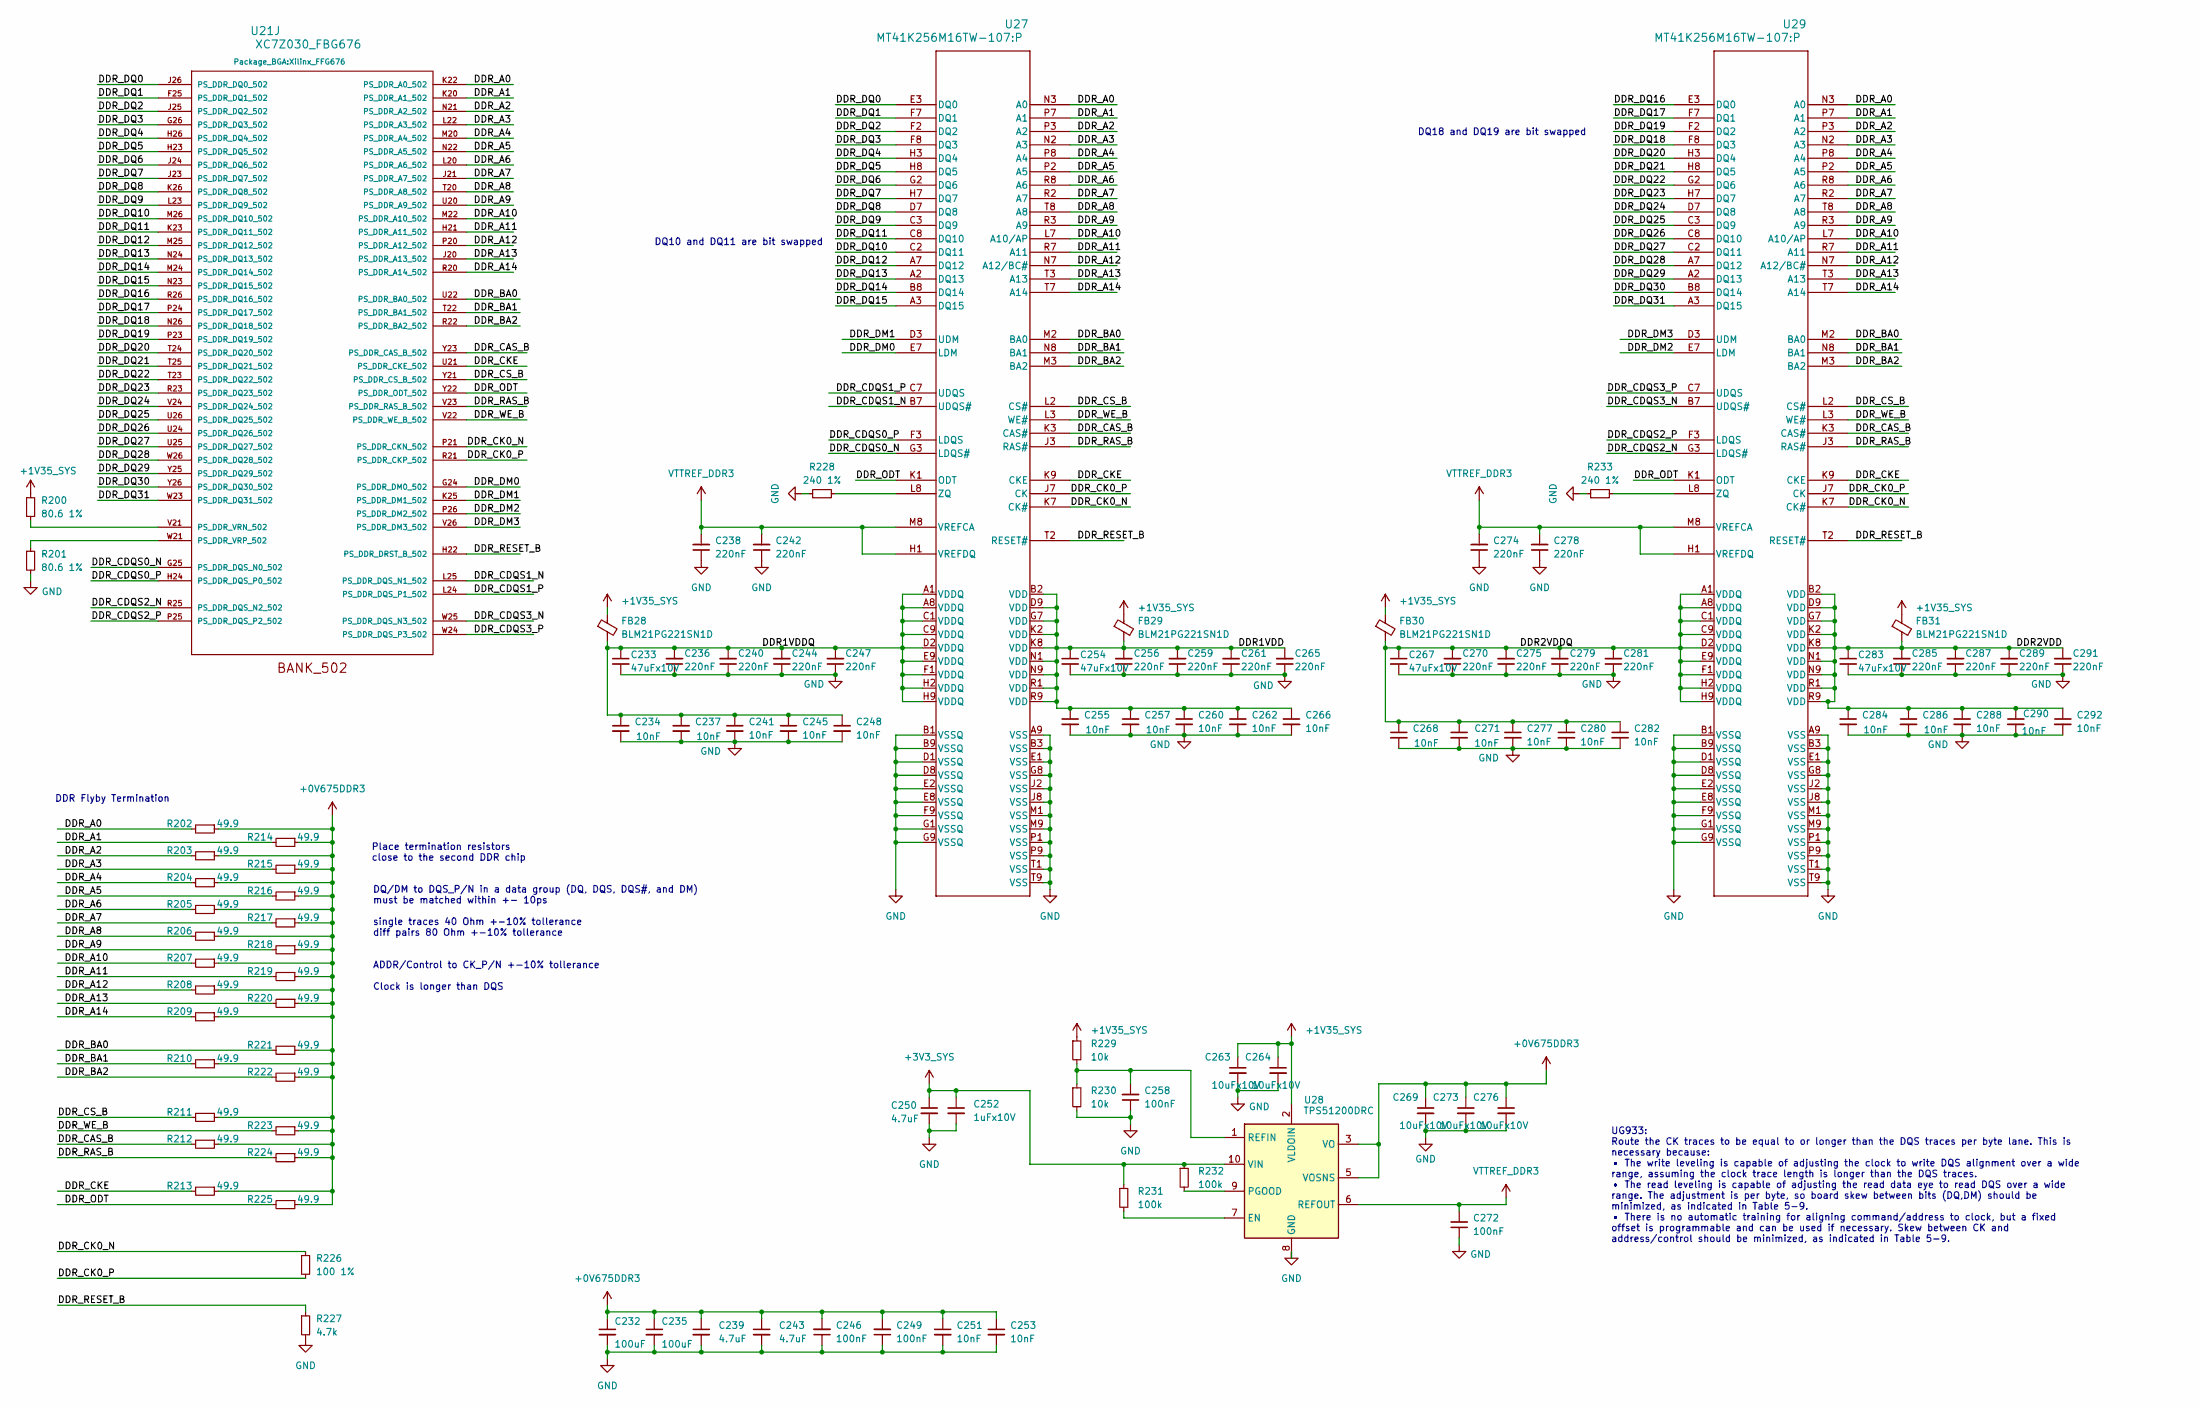
[picture p53: schematic psddr3.kicad_sch]

Parts:
C232, C235: 100uF; C_1210_3225Metric; Part GRM32EC70J107ME15L; JLCPCB Part # C393041
C233, C254, C267, C283: 47uFx10V; C_1210_3225Metric; Part GRM32ER71A476KE15L; JLCPCB Part # C84494
C234, C237, C241, C245, C248, C255, C257, C260, C262, C266, C268, C271, C277, C280, C282, C284, C286, C288, C290, C292: 10nF; C_0201_0603Metric; Part 0201B103K250NT; JLCPCB Part # C285010
C236, C238, C240, C242, C244, C247, C256, C259, C261, C265, C270, C274, C275, C278, C279, C281, C285, C287, C289, C291: 220nF; C_0201_0603Metric; Part CL03A224MQ3NNNC; JLCPCB Part # C34696
C239, C243, C250: 4.7uF; C_0402_1005Metric; Part CL05A475KP5NRNC; JLCPCB Part # C368809
C246, C249, C258, C272: 100nF; C_0402_1005Metric; Part CC0402JRX7R8BB104; JLCPCB Part # C541465
C251, C253: 10nF; C_0805_2012Metric; Part TCC0805X7R103K500DT; JLCPCB Part # C282728
C252: 1uFx10V; C_0603_1608Metric; JLCPCB Part # C841050
C263, C264, C269, C273, C276: 10uFx10V; C_0805_2012Metric; Part CL21A106KPFNNNE; JLCPCB Part # C17024
FB28, FB29, FB30, FB31: BLM21PG221SN1D; L_0805_2012Metric; Part BLM21PG221SN1D; JLCPCB Part # C85840
R200, R201: 80.6 1%; R_0402_1005Metric; Part 0402WGF806JTCE; JLCPCB Part # C25134
R202, R203, R204, R205, R206, R207, R208, R209, R210, R211, R212, R213, R214, R215, R216, R217, R218, R219, R220, R221, R222, R223, R224, R225: 49.9; R_0201_0603Metric; Part FRC0201F49R9TS; JLCPCB Part # C7467280
R226: 100 1%; R_0402_1005Metric; Part RM04FTN1000; JLCPCB Part # C153111
R227: 4.7k; R_0402_1005Metric; Part 0402WGF4701TCE; JLCPCB Part # C25900
R228, R233: 240 1%; R_0402_1005Metric; Part RT0402BRD07240RL; JLCPCB Part # C852660
R229, R230: 10k; R_0402_1005Metric; Part 0402WGF1002TCE; JLCPCB Part # C25744
R231, R232: 100k; R_0402_1005Metric; Part RC0402FR-07100KL; JLCPCB Part # C60491
U21: XC7Z030_FBG676; Xilinx_FFG676; JLCPCB Part # C966962
U27, U29: MT41K256M16TW-107:P; FBGA96_TW_MRN; Part MT41K256M16TW-107:P; JLCPCB Part # C253882
U28: TPS51200DRC; VSON-10-1EP_3x3mm_P0.5mm_EP1.65x2.4mm; Part TPS51200DRCT; JLCPCB Part # C70874

Connections:
+0V675DDR3: C232.1, C235.1, C239.1, C243.1, C246.2, C249.2, C251.1, C253.1, C269.1, C273.1, C276.1, R202.1, R203.1, R204.1, R205.1, R206.1, R207.1, R208.1, R209.1, R210.1, R211.1, R212.1, R213.1, R214.1, R215.1, R216.1, R217.1, R218.1, R219.1, R220.1, R221.1, R222.1, R223.1, R224.1, R225.1, U28.3 (VO), U28.5 (VOSNS)
+1V35_SYS: C263.1, C264.1, FB28.1, FB29.1, FB30.1, FB31.1, R200.1, R229.1, U28.2 (VLDOIN)
+3V3_SYS: C250.1, C252.1, R231.1, R232.1, U28.10 (VIN)
DDR1VDD: C254.1, C255.1, C256.2, C257.1, C259.2, C260.1, C261.2, C262.1, C265.2, C266.1, FB29.2, U27.B2 (VDD), U27.D9 (VDD), U27.G7 (VDD), U27.K2 (VDD), U27.K8 (VDD), U27.N1 (VDD), U27.N9 (VDD), U27.R1 (VDD), U27.R9 (VDD)
DDR1VDDQ: C233.1, C234.1, C236.2, C237.1, C240.2, C241.1, C244.2, C245.1, C247.2, C248.1, FB28.2, U27.A1 (VDDQ), U27.A8 (VDDQ), U27.C1 (VDDQ), U27.C9 (VDDQ), U27.D2 (VDDQ), U27.E9 (VDDQ), U27.F1 (VDDQ), U27.H2 (VDDQ), U27.H9 (VDDQ)
DDR2VDD: C283.1, C284.1, C285.2, C286.1, C287.2, C288.1, C289.2, C290.1, C291.2, C292.1, FB31.2, U29.B2 (VDD), U29.D9 (VDD), U29.G7 (VDD), U29.K2 (VDD), U29.K8 (VDD), U29.N1 (VDD), U29.N9 (VDD), U29.R1 (VDD), U29.R9 (VDD)
DDR2VDDQ: C267.1, C268.1, C270.2, C271.1, C275.2, C277.1, C279.2, C280.1, C281.2, C282.1, FB30.2, U29.A1 (VDDQ), U29.A8 (VDDQ), U29.C1 (VDDQ), U29.C9 (VDDQ), U29.D2 (VDDQ), U29.E9 (VDDQ), U29.F1 (VDDQ), U29.H2 (VDDQ), U29.H9 (VDDQ)
DDR_A0: R202.2, U21.K22 (PS_DDR_A0_502), U27.N3 (A0), U29.N3 (A0)
DDR_A1: R214.2, U21.K20 (PS_DDR_A1_502), U27.P7 (A1), U29.P7 (A1)
DDR_A2: R203.2, U21.N21 (PS_DDR_A2_502), U27.P3 (A2), U29.P3 (A2)
DDR_A3: R215.2, U21.L22 (PS_DDR_A3_502), U27.N2 (A3), U29.N2 (A3)
DDR_A4: R204.2, U21.M20 (PS_DDR_A4_502), U27.P8 (A4), U29.P8 (A4)
DDR_A5: R216.2, U21.N22 (PS_DDR_A5_502), U27.P2 (A5), U29.P2 (A5)
DDR_A6: R205.2, U21.L20 (PS_DDR_A6_502), U27.R8 (A6), U29.R8 (A6)
DDR_A7: R217.2, U21.J21 (PS_DDR_A7_502), U27.R2 (A7), U29.R2 (A7)
DDR_A8: R206.2, U21.T20 (PS_DDR_A8_502), U27.T8 (A8), U29.T8 (A8)
DDR_A9: R218.2, U21.U20 (PS_DDR_A9_502), U27.R3 (A9), U29.R3 (A9)
DDR_A10: R207.2, U21.M22 (PS_DDR_A10_502), U27.L7 (A10/AP), U29.L7 (A10/AP)
DDR_A11: R219.2, U21.H21 (PS_DDR_A11_502), U27.R7 (A11), U29.R7 (A11)
DDR_A12: R208.2, U21.P20 (PS_DDR_A12_502), U27.N7 (A12/BC#), U29.N7 (A12/BC#)
DDR_A13: R220.2, U21.J20 (PS_DDR_A13_502), U27.T3 (A13), U29.T3 (A13)
DDR_A14: R209.2, U21.R20 (PS_DDR_A14_502), U27.T7 (A14), U29.T7 (A14)
DDR_BA0: R221.2, U21.U22 (PS_DDR_BA0_502), U27.M2 (BA0), U29.M2 (BA0)
DDR_BA1: R210.2, U21.T22 (PS_DDR_BA1_502), U27.N8 (BA1), U29.N8 (BA1)
DDR_BA2: R222.2, U21.R22 (PS_DDR_BA2_502), U27.M3 (BA2), U29.M3 (BA2)
DDR_CAS_B: R212.2, U21.Y23 (PS_DDR_CAS_B_502), U27.K3 (CAS#), U29.K3 (CAS#)
DDR_CDQS0_N: U21.G25 (PS_DDR_DQS_N0_502), U27.G3 (LDQS#)
DDR_CDQS0_P: U21.H24 (PS_DDR_DQS_P0_502), U27.F3 (LDQS)
DDR_CDQS1_N: U21.L25 (PS_DDR_DQS_N1_502), U27.B7 (UDQS#)
DDR_CDQS1_P: U21.L24 (PS_DDR_DQS_P1_502), U27.C7 (UDQS)
DDR_CDQS2_N: U21.R25 (PS_DDR_DQS_N2_502), U29.G3 (LDQS#)
DDR_CDQS2_P: U21.P25 (PS_DDR_DQS_P2_502), U29.F3 (LDQS)
DDR_CDQS3_N: U21.W25 (PS_DDR_DQS_N3_502), U29.B7 (UDQS#)
DDR_CDQS3_P: U21.W24 (PS_DDR_DQS_P3_502), U29.C7 (UDQS)
DDR_CK0_N: R226.1, U21.P21 (PS_DDR_CKN_502), U27.K7 (CK#), U29.K7 (CK#)
DDR_CK0_P: R226.2, U21.R21 (PS_DDR_CKP_502), U27.J7 (CK), U29.J7 (CK)
DDR_CKE: R213.2, U21.U21 (PS_DDR_CKE_502), U27.K9 (CKE), U29.K9 (CKE)
DDR_CS_B: R211.2, U21.Y21 (PS_DDR_CS_B_502), U27.L2 (CS#), U29.L2 (CS#)
DDR_DM0: U21.G24 (PS_DDR_DM0_502), U27.E7 (LDM)
DDR_DM1: U21.K25 (PS_DDR_DM1_502), U27.D3 (UDM)
DDR_DM2: U21.P26 (PS_DDR_DM2_502), U29.E7 (LDM)
DDR_DM3: U21.V26 (PS_DDR_DM3_502), U29.D3 (UDM)
DDR_DQ0: U21.J26 (PS_DDR_DQ0_502), U27.E3 (DQ0)
DDR_DQ1: U21.F25 (PS_DDR_DQ1_502), U27.F7 (DQ1)
DDR_DQ2: U21.J25 (PS_DDR_DQ2_502), U27.F2 (DQ2)
DDR_DQ3: U21.G26 (PS_DDR_DQ3_502), U27.F8 (DQ3)
DDR_DQ4: U21.H26 (PS_DDR_DQ4_502), U27.H3 (DQ4)
DDR_DQ5: U21.H23 (PS_DDR_DQ5_502), U27.H8 (DQ5)
DDR_DQ6: U21.J24 (PS_DDR_DQ6_502), U27.G2 (DQ6)
DDR_DQ7: U21.J23 (PS_DDR_DQ7_502), U27.H7 (DQ7)
DDR_DQ8: U21.K26 (PS_DDR_DQ8_502), U27.D7 (DQ8)
DDR_DQ9: U21.L23 (PS_DDR_DQ9_502), U27.C3 (DQ9)
DDR_DQ10: U21.M26 (PS_DDR_DQ10_502), U27.C2 (DQ11)
DDR_DQ11: U21.K23 (PS_DDR_DQ11_502), U27.C8 (DQ10)
DDR_DQ12: U21.M25 (PS_DDR_DQ12_502), U27.A7 (DQ12)
DDR_DQ13: U21.N24 (PS_DDR_DQ13_502), U27.A2 (DQ13)
DDR_DQ14: U21.M24 (PS_DDR_DQ14_502), U27.B8 (DQ14)
DDR_DQ15: U21.N23 (PS_DDR_DQ15_502), U27.A3 (DQ15)
DDR_DQ16: U21.R26 (PS_DDR_DQ16_502), U29.E3 (DQ0)
DDR_DQ17: U21.P24 (PS_DDR_DQ17_502), U29.F7 (DQ1)
DDR_DQ18: U21.N26 (PS_DDR_DQ18_502), U29.F8 (DQ3)
DDR_DQ19: U21.P23 (PS_DDR_DQ19_502), U29.F2 (DQ2)
DDR_DQ20: U21.T24 (PS_DDR_DQ20_502), U29.H3 (DQ4)
DDR_DQ21: U21.T25 (PS_DDR_DQ21_502), U29.H8 (DQ5)
DDR_DQ22: U21.T23 (PS_DDR_DQ22_502), U29.G2 (DQ6)
DDR_DQ23: U21.R23 (PS_DDR_DQ23_502), U29.H7 (DQ7)
DDR_DQ24: U21.V24 (PS_DDR_DQ24_502), U29.D7 (DQ8)
DDR_DQ25: U21.U26 (PS_DDR_DQ25_502), U29.C3 (DQ9)
DDR_DQ26: U21.U24 (PS_DDR_DQ26_502), U29.C8 (DQ10)
DDR_DQ27: U21.U25 (PS_DDR_DQ27_502), U29.C2 (DQ11)
DDR_DQ28: U21.W26 (PS_DDR_DQ28_502), U29.A7 (DQ12)
DDR_DQ29: U21.Y25 (PS_DDR_DQ29_502), U29.A2 (DQ13)
DDR_DQ30: U21.Y26 (PS_DDR_DQ30_502), U29.B8 (DQ14)
DDR_DQ31: U21.W23 (PS_DDR_DQ31_502), U29.A3 (DQ15)
DDR_ODT: R225.2, U21.Y22 (PS_DDR_ODT_502), U27.K1 (ODT), U29.K1 (ODT)
DDR_RAS_B: R224.2, U21.V23 (PS_DDR_RAS_B_502), U27.J3 (RAS#), U29.J3 (RAS#)
DDR_RESET_B: R227.1, U21.H22 (PS_DDR_DRST_B_502), U27.T2 (RESET#), U29.T2 (RESET#)
DDR_WE_B: R223.2, U21.V22 (PS_DDR_WE_B_502), U27.L3 (WE#), U29.L3 (WE#)
GND: C232.2, C233.2, C234.2, C235.2, C236.1, C237.2, C238.1, C239.2, C240.1, C241.2, C242.1, C243.2, C244.1, C245.2, C246.1, C247.1, C248.2, C249.1, C250.2, C251.2, C252.2, C253.2, C254.2, C255.2, C256.1, C257.2, C258.1, C259.1, C260.2, C261.1, C262.2, C263.2, C264.2, C265.1, C266.2, C267.2, C268.2, C269.2, C270.1, C271.2, C272.1, C273.2, C274.1, C275.1, C276.2, C277.2, C278.1, C279.1, C280.2, C281.1, C282.2, C283.2, C284.2, C285.1, C286.2, C287.1, C288.2, C289.1, C290.2, C291.1, C292.2, R201.2, R227.2, R228.1, R230.2, R233.1, U27.A9 (VSS), U27.B1 (VSSQ), U27.B3 (VSS), U27.B9 (VSSQ), U27.D1 (VSSQ), U27.D8 (VSSQ), U27.E1 (VSS), U27.E2 (VSSQ), U27.E8 (VSSQ), U27.F9 (VSSQ), U27.G1 (VSSQ), U27.G8 (VSS), U27.G9 (VSSQ), U27.J2 (VSS), U27.J8 (VSS), U27.M1 (VSS), U27.M9 (VSS), U27.P1 (VSS), U27.P9 (VSS), U27.T1 (VSS), U27.T9 (VSS), U28.4 (GND), U28.8 (GND), U28.11 (GND), U29.A9 (VSS), U29.B1 (VSSQ), U29.B3 (VSS), U29.B9 (VSSQ), U29.D1 (VSSQ), U29.D8 (VSSQ), U29.E1 (VSS), U29.E2 (VSSQ), U29.E8 (VSSQ), U29.F9 (VSSQ), U29.G1 (VSSQ), U29.G8 (VSS), U29.G9 (VSSQ), U29.J2 (VSS), U29.J8 (VSS), U29.M1 (VSS), U29.M9 (VSS), U29.P1 (VSS), U29.P9 (VSS), U29.T1 (VSS), U29.T9 (VSS)
unnamed: C258.2, R229.2, R230.1, U28.1 (REFIN)
unnamed: R200.2, U21.V21 (PS_DDR_VRN_502)
unnamed: R201.1, U21.W21 (PS_DDR_VRP_502)
unnamed: R228.2, U27.L8 (ZQ)
unnamed: R231.2, U28.7 (EN)
unnamed: R232.2, U28.9 (PGOOD)
unnamed: R233.2, U29.L8 (ZQ)
VTTREF_DDR3: C238.2, C242.2, C272.2, C274.2, C278.2, U27.H1 (VREFDQ), U27.M8 (VREFCA), U28.6 (REFOUT), U29.H1 (VREFDQ), U29.M8 (VREFCA)

Notes on the sheet:
UG933: Route the CK traces to be equal to or longer than the DQS traces per byte lane. This is necessary because: • The write leveling is capable of adjusting the clock to write DQS alignment over a wide range, assuming the clock trace length is longer than the DQS traces. • The read leveling is ca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
DQ18 and DQ19 are bit swapped
Place termination resistors close to the second DDR chip
DQ/DM to DQS_P/N in a data group (DQ, DQS, DQS#, and DM) must be matched within +- 10ps single traces 40 Ohm +-10% tollerance diff pairs 80 Ohm +-10% tollerance ADDR/Control to CK_P/N +-10% tollerance Clock is longer than DQS
DQ10 and DQ11 are bit swapped
DDR Flyby Termination
