electrodyssey/NASR-M/psu.kicad_sch

## KiCad design psu.kicad_sch (2025-10-22)

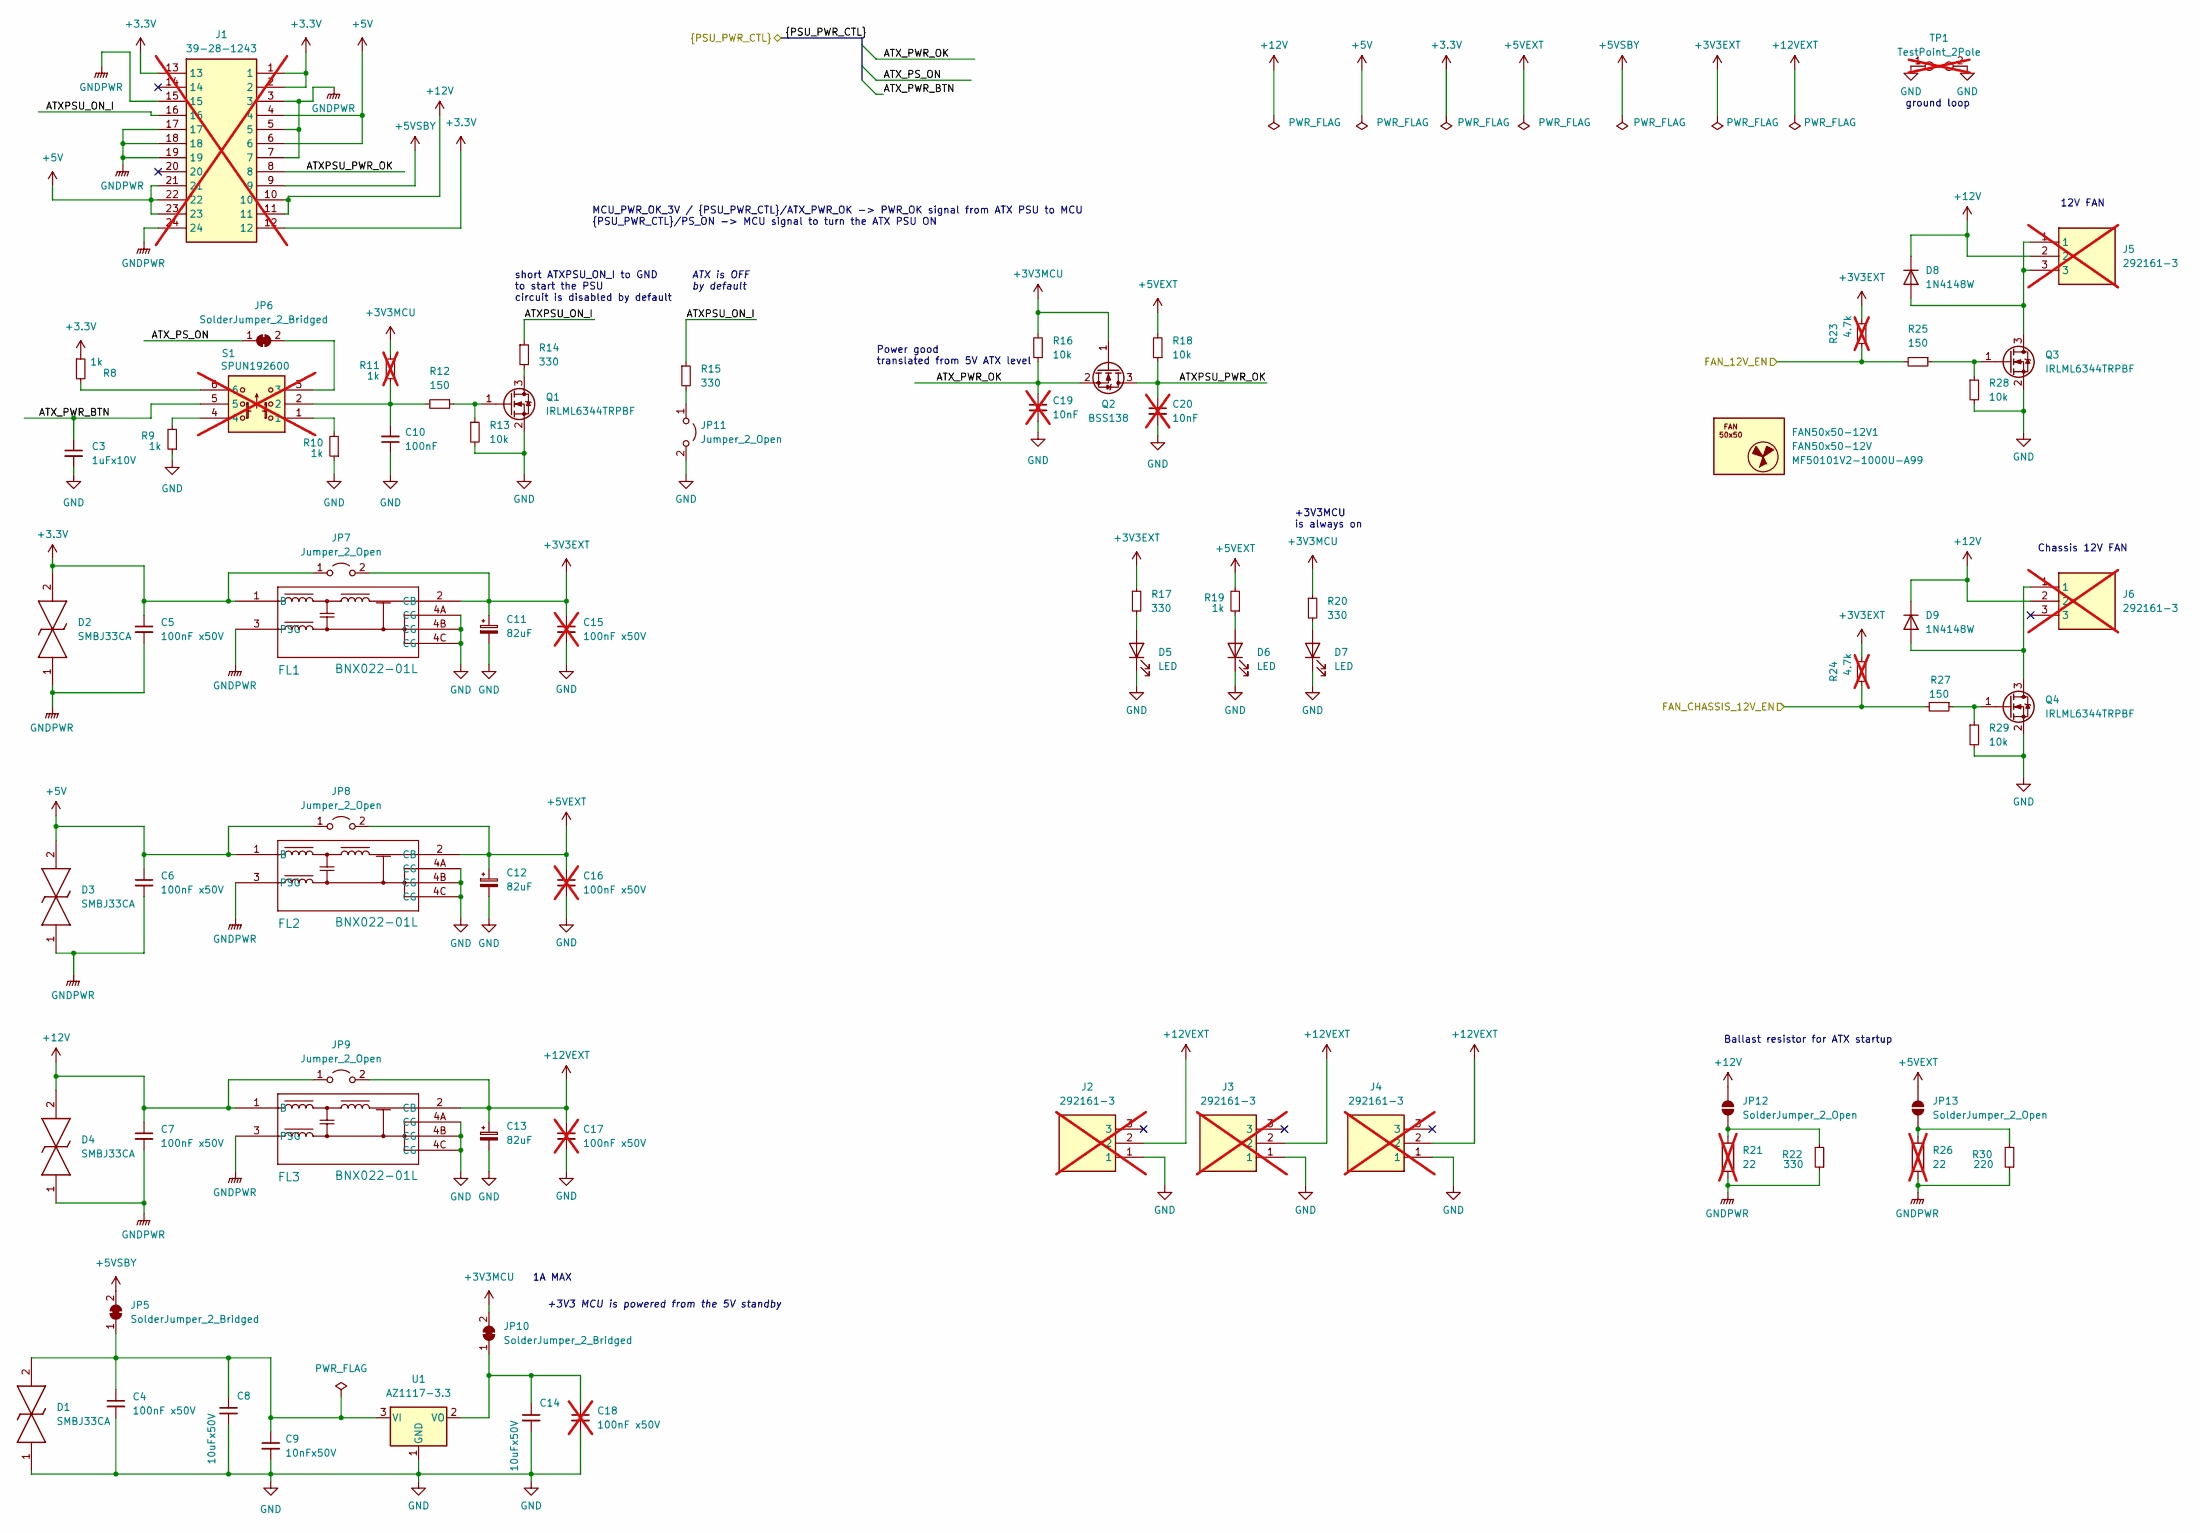
[picture p54: schematic psu.kicad_sch]

Parts:
C3: 1uFx10V; C_0603_1608Metric; JLCPCB Part # C841050
C4, C6, C7: 100nF x50V; C_0805_2012Metric; JLCPCB Part # C141172
C5: 100nF x50V; C_0805_2012Metric; Part C0805X104K5RACAUTO; JLCPCB Part # C141172
C8, C14: 10uFx50V; C_1206_3216Metric; Part CS3216X5R106K500NRI; JLCPCB Part # C513774
C9: 10nFx50V; C_1206_3216Metric; Part 1206B103K102NT; JLCPCB Part # C9194
C10: 100nF; C_0402_1005Metric; Part CC0402JRX7R8BB104; JLCPCB Part # C541465
C11, C12, C13: 82uF; CP_Elec_8x11.9; Part 35SVPF82M; JLCPCB Part # C188358
C15, C16, C17, C18: 100nF x50V; C_0805_2012Metric; Part C0805X104K5RACAUTO; JLCPCB Part # C141172; not fitted
C19, C20: 10nF; C_0805_2012Metric; not fitted
D1, D2, D3, D4: SMBJ33CA; D_SMB_Handsoldering; Mouser Part Number 652-SMBJ33CA
D5, D6, D7: LED; LED_0805_2012Metric; Part HL-PSC-2012S11GC; JLCPCB Part # C497958
D8, D9: 1N4148W; D_SOD-123; Part 1N4148W; JLCPCB Part # C81598
FAN50x50-12V1: FAN50x50-12V; FAN50x50; Manufacturer_Part_Number MF50101V2-1000U-A99; LCSC Part # C456906
FL1, FL2, FL3: BNX022-01L; BNX022_23-01_MUR; Part BNX022-01L; JLCPCB Part # C91575
J1: 39-28-1243; Mouser Part Number 538-39-28-1243; not fitted
J2, J3, J4, J5, J6: 292161-3; SHDR3W60P0X200_1X3_780X360X680P; Mouser Part Number 571-292161-3; not fitted
JP5, JP6, JP10: SolderJumper_2_Bridged; SolderJumper-2_P1.3mm_Bridged2Bar_Pad1.0x1.5mm
JP7, JP8, JP9, JP11: Jumper_2_Open; SolderJumper-2_P1.3mm_Open_TrianglePad1.0x1.5mm
JP12, JP13: SolderJumper_2_Open; SolderJumper-2_P1.3mm_Open_Pad1.0x1.5mm
Q1, Q3, Q4: IRLML6344TRPBF; SOT-23; JLCPCB Part # C53550
Q2: BSS138; SOT-23; JLCPCB Part # C52895
R8, R9, R10, R19: 1k; R_0402_1005Metric; Part 0402WGF1001TCE; JLCPCB Part # C11702
R11: 1k; R_0402_1005Metric; Part 0402WGF1001TCE; JLCPCB Part # C11702; not fitted
R12, R25, R27: 150; R_0402_1005Metric; Part 0402WGF1500TCE; JLCPCB Part # C25082
R13, R28, R29: 10k; R_0402_1005Metric; Part 0402WGF1002TCE; JLCPCB Part # C25744
R14, R15: 330; R_1206_3216Metric; Part 1206W4F3300T5E; JLCPCB Part # C17930
R16, R18: 10k; R_0603_1608Metric; Part 0603WAF1002T5E; JLCPCB Part # C25804
R17, R20: 330; R_0603_1608Metric; Part 0603WAF3300T5E; JLCPCB Part # C23138
R21, R26: 22; R_Axial_DIN0617_L17.0mm_D6.0mm_P7.62mm_Vertical; not fitted
R22: 330; R_1210_3225Metric_Pad1.30x2.65mm_HandSolder; Part FRC1210J331TS; JLCPCB Part # C5154013
R23, R24: 4.7k; R_0402_1005Metric; Part 0402WGF4701TCE; JLCPCB Part # C25900; not fitted
R30: 220; R_1210_3225Metric_Pad1.30x2.65mm_HandSolder; Part AC1210FR-07220RL; JLCPCB Part # C230115
S1: SPUN192600; Mouser Part Number 688-SPUN192600; not fitted
TP1: TestPoint_2Pole; PinHeader_1x02_P2.54mm_Vertical; not fitted
U1: AZ1117-3.3; SOT-223-3_TabPin2; Part AZ1117H-3.3TRG1; JLCPCB Part # C110474

Connections:
+3.3V: C5.1, D2.2, FL1.1 (B), J1.1, J1.2, J1.12, J1.13, JP7.1 (A), R8.1
+3V3EXT: C11.1, C15.1, FL1.2 (CB), JP7.2 (B), R17.1, R23.2, R24.2
+3V3MCU: JP10.2 (B), Q2.1 (G), R11.2, R16.2, R20.1
+5V: C6.1, D3.2, FL2.1 (B), J1.4, J1.6, J1.21, J1.22, J1.23, JP8.1 (A)
+5VEXT: C12.1, C16.1, FL2.2 (CB), JP8.2 (B), JP13.2 (B), R18.2, R19.2
+5VSBY: J1.9, JP5.2 (B)
+12V: C7.1, D4.2, D8.1 (K), D9.1 (K), FL3.1 (B), J1.10, J1.11, J5.2, J6.2, JP9.1 (A), JP12.2 (B)
+12VEXT: C13.1, C17.1, FL3.2 (CB), J2.2, J3.2, J4.2, JP9.2 (B)
ATXPSU_ON_I: J1.16, R14.1, R15.1
ATXPSU_PWR_OK: C20.1, J1.8, Q2.3 (D), R18.1
ATX_PS_ON: JP6.1 (A)
ATX_PWR_BTN: C3.1, S1.5
ATX_PWR_OK: C19.1, Q2.2 (S), R16.1
FAN_12V_EN: R23.1, R25.2
FAN_CHASSIS_12V_EN: R24.1, R27.2
GND: C3.2, C4.2, C8.2, C9.2, C10.1, C11.2, C12.2, C13.2, C14.2, C15.2, C16.2, C17.2, C18.2, C19.2, C20.2, D1.1, D5.1 (K), D6.1 (K), D7.1 (K), FL1.4A (CG), FL1.4B (CG), FL1.4C (CG), FL2.4A (CG), FL2.4B (CG), FL2.4C (CG), FL3.4A (CG), FL3.4B (CG), FL3.4C (CG), J2.1, J3.1, J4.1, JP11.2 (B), Q1.2 (S), Q3.2 (S), Q4.2 (S), R9.1, R10.1, R13.2, R28.2, R29.2, TP1.1, TP1.2, U1.1 (GND)
GNDPWR: C5.2, C6.2, C7.2, D2.1, D3.1, D4.1, FL1.3 (PSG), FL2.3 (PSG), FL3.3 (PSG), J1.3, J1.5, J1.7, J1.15, J1.17, J1.18, J1.19, J1.24, R21.2, R22.1, R26.2, R30.1
unnamed: C4.1, C8.1, C9.1, D1.2, JP5.1 (A), U1.3 (VI)
unnamed: C10.2, R11.1, R12.2, S1.2
unnamed: C14.1, C18.1, JP10.1 (A), U1.2 (VO)
unnamed: D5.2 (A), R17.2
unnamed: D6.2 (A), R19.1
unnamed: D7.2 (A), R20.2
unnamed: D8.2 (A), J5.1, J5.3, Q3.3 (D)
unnamed: D9.2 (A), J6.1, Q4.3 (D)
unnamed: JP6.2 (B), S1.3
unnamed: JP11.1 (A), R15.2
unnamed: JP12.1 (A), R21.1, R22.2
unnamed: JP13.1 (A), R26.1, R30.2
unnamed: Q1.1 (G), R12.1, R13.1
unnamed: Q1.3 (D), R14.2
unnamed: Q3.1 (G), R25.1, R28.1
unnamed: Q4.1 (G), R27.1, R29.1
unnamed: R8.2, S1.6
unnamed: R9.2, S1.4
unnamed: R10.2, S1.1

Notes on the sheet:
MCU_PWR_OK_3V / {PSU_PWR_CTL}/ATX_PWR_OK -> PWR_OK signal from ATX PSU to MCU {PSU_PWR_CTL}/PS_ON -> MCU signal to turn the ATX PSU ON
+3V3 MCU is powered from the 5V standby
1A MAX
+3V3MCU is always on
ground loop
short ATXPSU_ON_I to GND to start the PSU circuit is disabled by default
ATX is OFF by default
Chassis 12V FAN
Power good translated from 5V ATX level
Ballast resistor for ATX startup
12V FAN
