electrodyssey/NASR-M/sdio.kicad_sch

## KiCad design sdio.kicad_sch (2025-10-22)

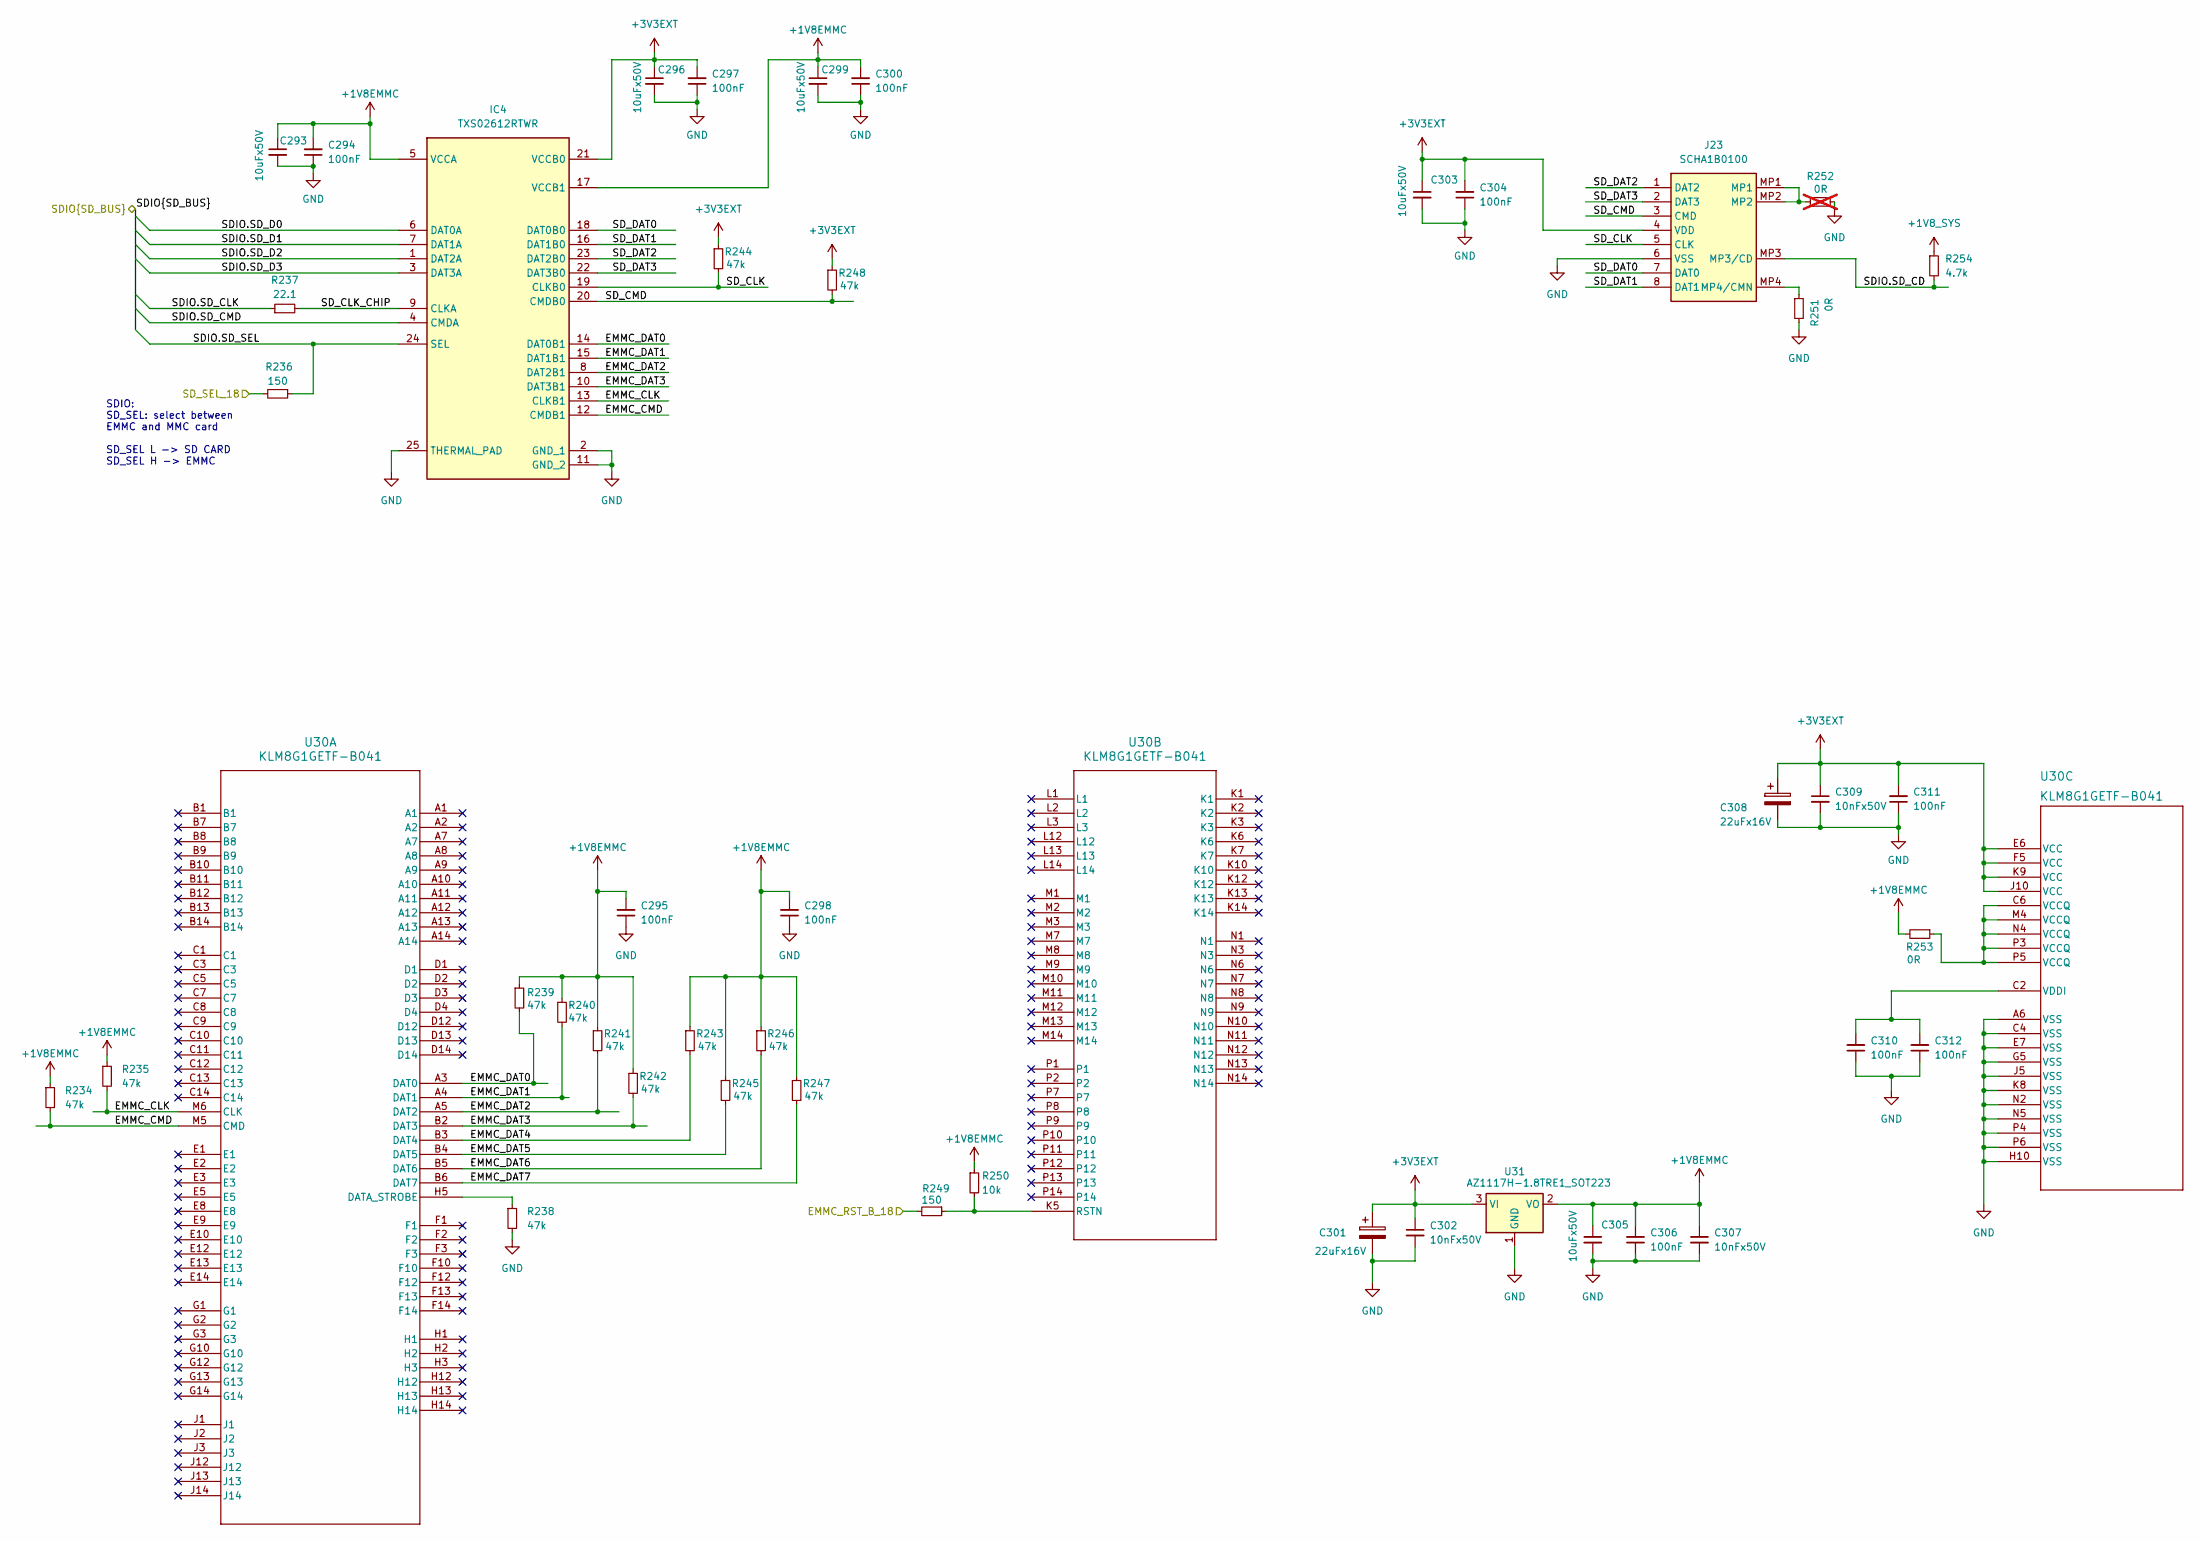
[picture p55: schematic sdio.kicad_sch]

Parts:
C293, C296, C299, C303, C305: 10uFx50V; C_1206_3216Metric; Part CS3216X5R106K500NRI; JLCPCB Part # C513774
C294, C295, C297, C298, C300, C304, C306, C310, C311, C312: 100nF; C_0402_1005Metric; Part CC0402JRX7R8BB104; JLCPCB Part # C541465
C301, C308: 22uFx16V; CP_EIA-6032-15_Kemet-U; Part TR3C226K016C0350; JLCPCB Part # C1954274
C302, C307, C309: 10nFx50V; C_1206_3216Metric; JLCPCB Part # C513774
IC4: TXS02612RTWR; QFN50P400X400X80-25N-D; Mouser Part Number 595-TXS02612RTWR
J23: SCHA1B0100; Manufacturer_Part_Number SCHA1B0100; Mouser Part Number 688-SCHA1B0100
R234, R235, R238, R239, R240, R241, R242, R243, R244, R245, R246, R247, R248: 47k; R_0402_1005Metric; Part 0402WGF4702TCE; JLCPCB Part # C25792
R236, R249: 150; R_0402_1005Metric; Part 0402WGF1500TCE; JLCPCB Part # C25082
R237: 22.1; R_0402_1005Metric; Part WR04X22R1FTL; JLCPCB Part # C170264
R250: 10k; R_0402_1005Metric; Part 0402WGF1002TCE; JLCPCB Part # C25744
R251, R253: 0R; R_0603_1608Metric; Part FRC0603F0000TS; JLCPCB Part # C2906974
R252: 0R; R_0603_1608Metric; Part 0603WAF0000T5E; JLCPCB Part # C21189; not fitted
R254: 4.7k; R_0402_1005Metric; Part 0402WGF4701TCE; JLCPCB Part # C25900
U30: KLM8G1GETF-B041; KLMBG2JENB-B041_SAM; JLCPCB Part # C499918
U31: AZ1117H-1.8TRE1_SOT223; SOT-223-3_TabPin2; Part LM1117MPX-1.8/NOPB; JLCPCB Part # C9660

Connections:
+1V8EMMC: C293.1, C294.2, C295.2, C298.2, C299.1, C300.2, C305.1, C306.2, C307.1, IC4.5 (VCCA), IC4.17 (VCCB1), R234.1, R235.1, R239.1, R240.1, R241.1, R242.1, R243.1, R245.1, R246.1, R247.1, R250.1, R253.2, U31.2 (VO)
+1V8_SYS: R254.1
+3V3EXT: C296.1, C297.2, C301.1, C302.1, C303.1, C304.2, C308.1, C309.1, C311.2, IC4.21 (VCCB0), J23.4 (VDD), R244.1, R248.1, U30.E6 (VCC), U30.F5 (VCC), U30.J10 (VCC), U30.K9 (VCC), U31.3 (VI)
EMMC_CLK: IC4.13 (CLKB1), R235.2, U30.M6 (CLK)
EMMC_CMD: IC4.12 (CMDB1), R234.2, U30.M5 (CMD)
EMMC_DAT0: IC4.14 (DAT0B1), R239.2, U30.A3 (DAT0)
EMMC_DAT1: IC4.15 (DAT1B1), R240.2, U30.A4 (DAT1)
EMMC_DAT2: IC4.8 (DAT2B1), R241.2, U30.A5 (DAT2)
EMMC_DAT3: IC4.10 (DAT3B1), R242.2, U30.B2 (DAT3)
EMMC_DAT4: R243.2, U30.B3 (DAT4)
EMMC_DAT5: R245.2, U30.B4 (DAT5)
EMMC_DAT6: R246.2, U30.B5 (DAT6)
EMMC_DAT7: R247.2, U30.B6 (DAT7)
EMMC_RST_B_18: R249.2
GND: C293.2, C294.1, C295.1, C296.2, C297.1, C298.1, C299.2, C300.1, C301.2, C302.2, C303.2, C304.1, C305.2, C306.1, C307.2, C308.2, C309.2, C310.1, C311.1, C312.1, IC4.2 (GND_1), IC4.11 (GND_2), IC4.25 (THERMAL_PAD), J23.6 (VSS), R238.2, R251.2, R252.2, U30.A6 (VSS), U30.C4 (VSS), U30.E7 (VSS), U30.G5 (VSS), U30.H10 (VSS), U30.J5 (VSS), U30.K8 (VSS), U30.N2 (VSS), U30.N5 (VSS), U30.P4 (VSS), U30.P6 (VSS), U31.1 (GND)
unnamed: C310.2, C312.2, U30.C2 (VDDI)
unnamed: J23.MP1, J23.MP2, R252.1
unnamed: J23.MP4 (MP4/CMN), R251.1
unnamed: R238.1, U30.H5 (DATA_STROBE)
unnamed: R249.1, R250.2, U30.K5 (RSTN)
unnamed: R253.1, U30.C6 (VCCQ), U30.M4 (VCCQ), U30.N4 (VCCQ), U30.P3 (VCCQ), U30.P5 (VCCQ)
SDIO.SD_CD: J23.MP3 (MP3/CD), R254.2
SDIO.SD_CLK: R237.1
SDIO.SD_CMD: IC4.4 (CMDA)
SDIO.SD_D0: IC4.6 (DAT0A)
SDIO.SD_D1: IC4.7 (DAT1A)
SDIO.SD_D2: IC4.1 (DAT2A)
SDIO.SD_D3: IC4.3 (DAT3A)
SDIO.SD_SEL: IC4.24 (SEL), R236.1
SD_CLK: IC4.19 (CLKB0), J23.5 (CLK), R244.2
SD_CLK_CHIP: IC4.9 (CLKA), R237.2
SD_CMD: IC4.20 (CMDB0), J23.3 (CMD), R248.2
SD_DAT0: IC4.18 (DAT0B0), J23.7 (DAT0)
SD_DAT1: IC4.16 (DAT1B0), J23.8 (DAT1)
SD_DAT2: IC4.23 (DAT2B0), J23.1 (DAT2)
SD_DAT3: IC4.22 (DAT3B0), J23.2 (DAT3)
SD_SEL_18: R236.2

Notes on the sheet:
SDIO: SD_SEL: select between EMMC and MMC card SD_SEL L -> SD CARD SD_SEL H -> EMMC
