electrodyssey/NASR-M/soc_b0_jtag.kicad_sch

## KiCad design soc_b0_jtag.kicad_sch (2025-10-22)

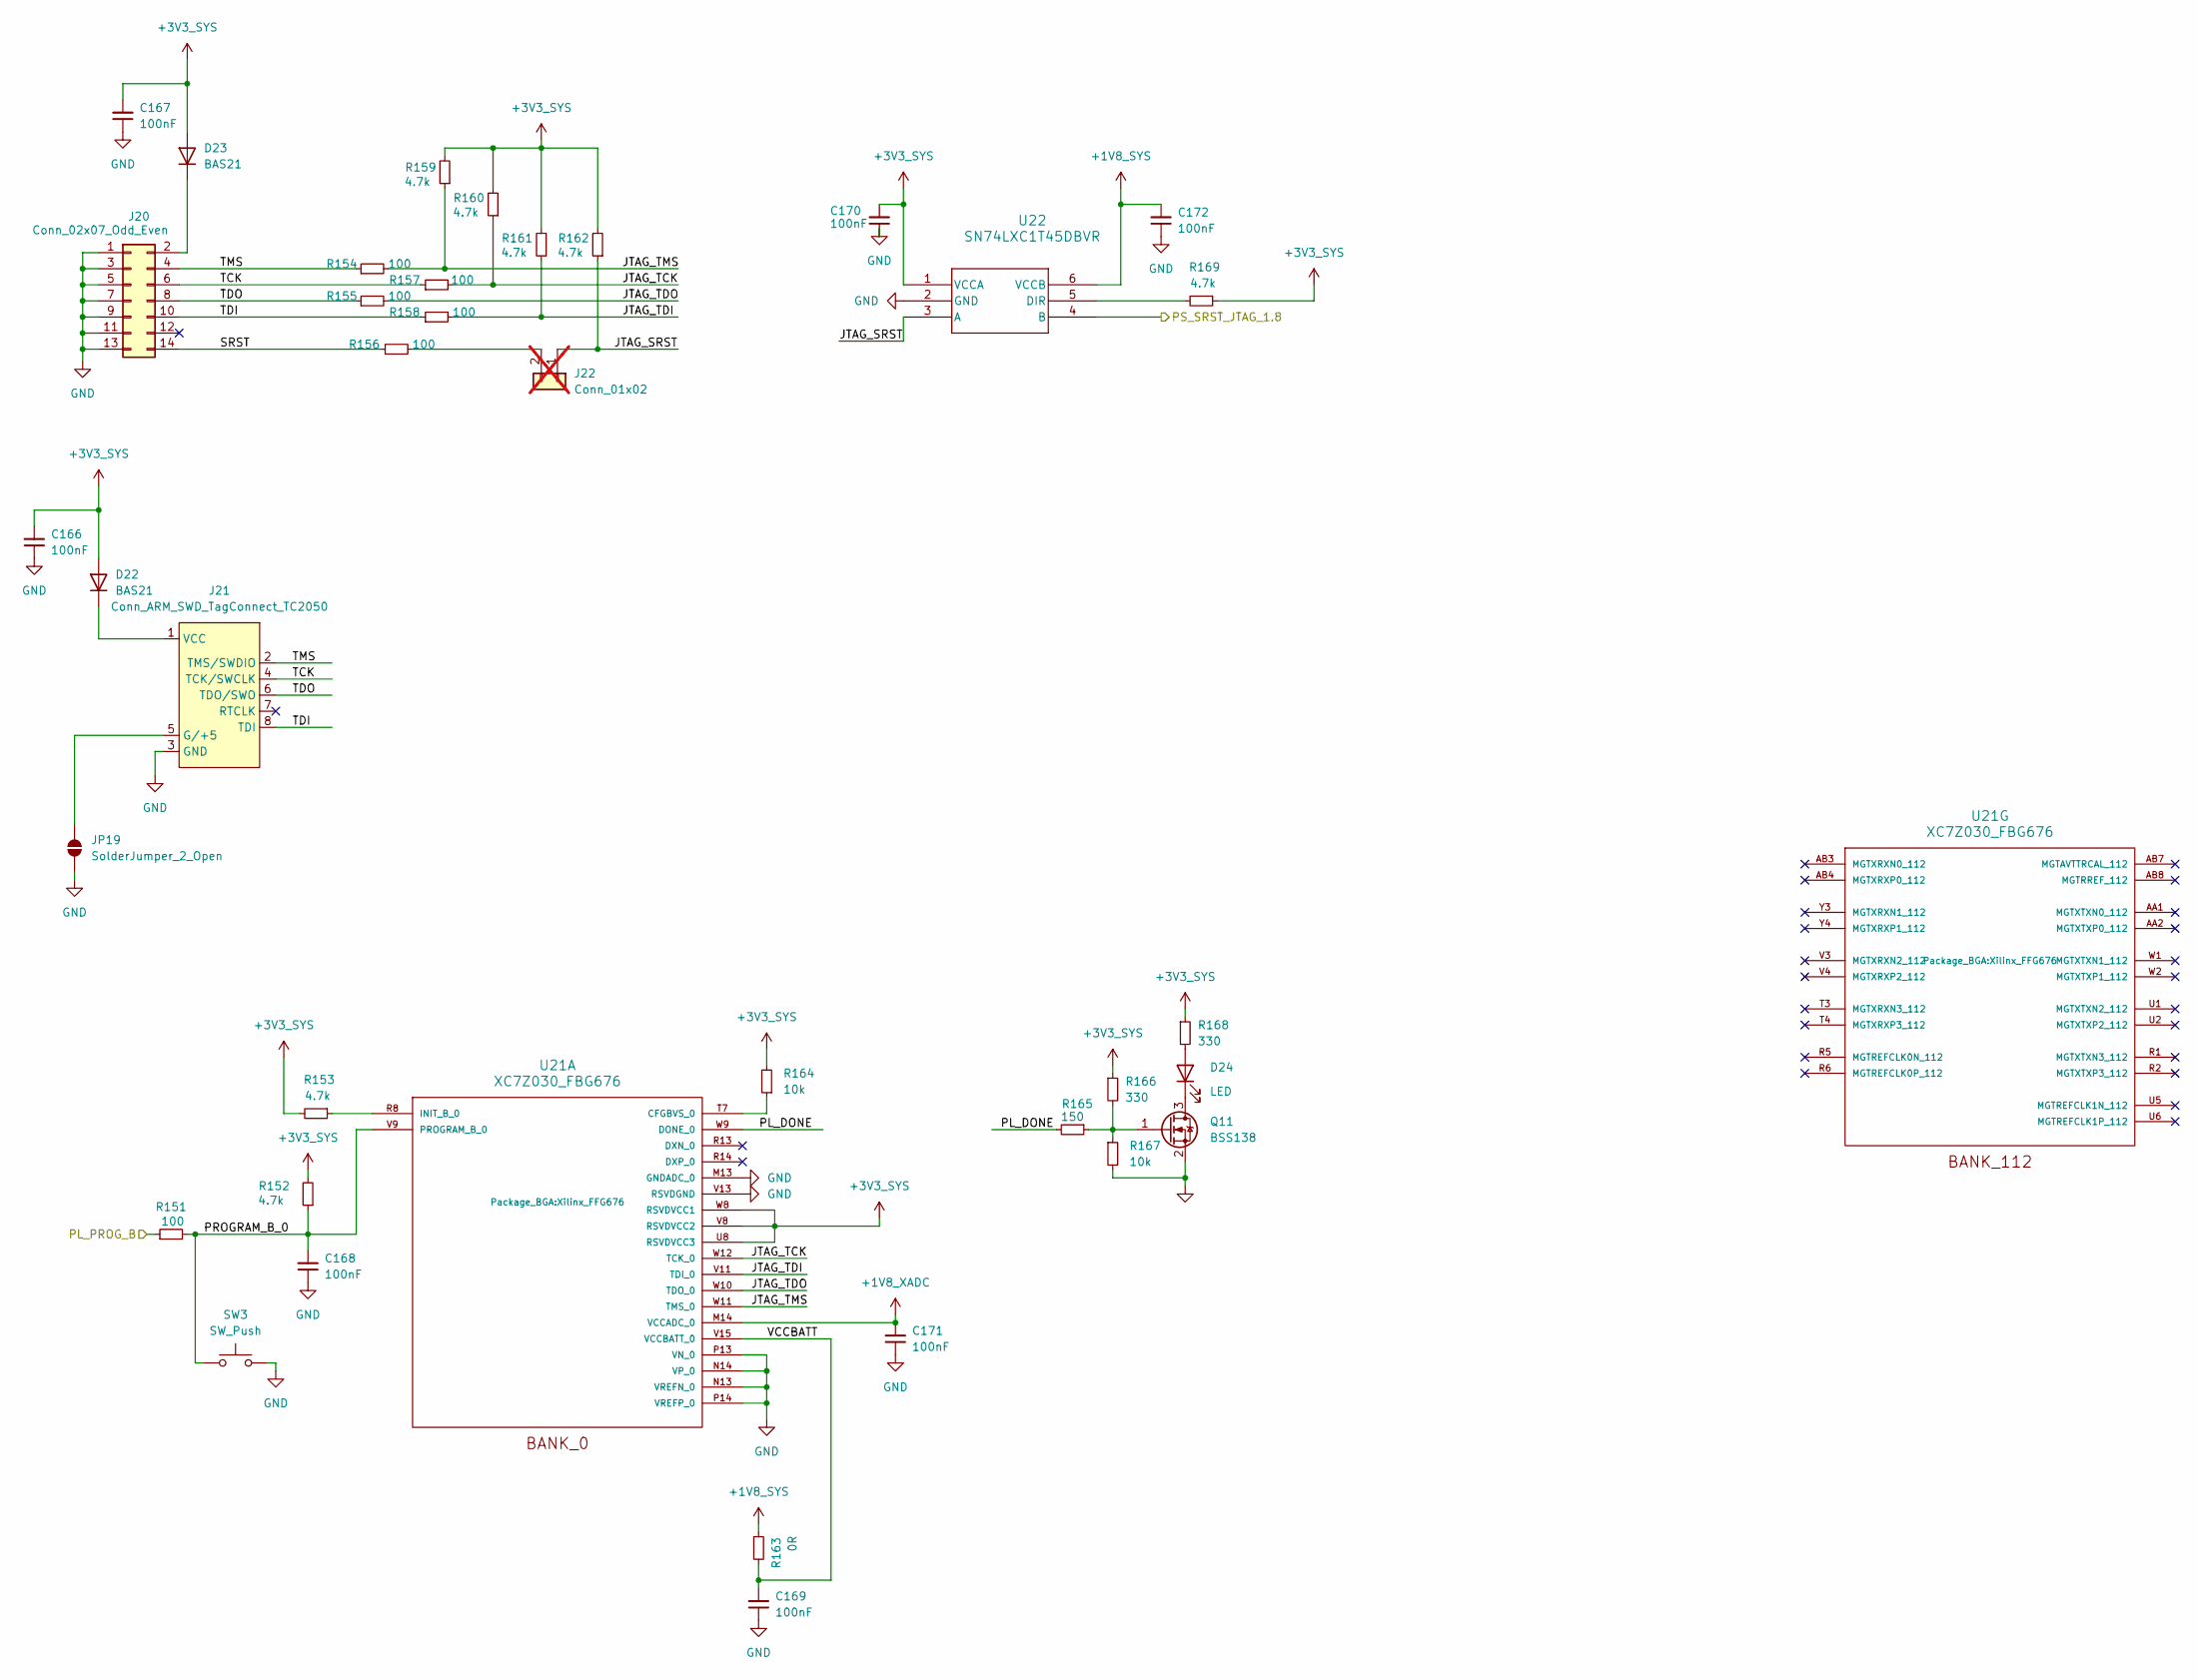
[picture p56: schematic soc_b0_jtag.kicad_sch]

Parts:
C166, C167, C168, C169, C170, C171, C172: 100nF; C_0402_1005Metric; Part CC0402JRX7R8BB104; JLCPCB Part # C541465
D22, D23: BAS21; SOT-23; JLCPCB Part # C8661
D24: LED; LED_0805_2012Metric; Part HL-PSC-2012S11GC; JLCPCB Part # C497958
J20: Conn_02x07_Odd_Even; PinHeader_2x07_P2.00mm_Vertical_SMD; Part B-3002N14P-0110; JLCPCB Part # C383681
J21: Conn_ARM_SWD_TagConnect_TC2050; Tag-Connect_TC2050-IDC-FP_2x05_P1.27mm_Vertical
J22: Conn_01x02; PinHeader_1x02_P2.54mm_Vertical; not fitted
JP19: SolderJumper_2_Open; SolderJumper-2_P1.3mm_Open_Pad1.0x1.5mm
Q11: BSS138; SOT-23; JLCPCB Part # C52895
R151, R154, R155, R156, R157, R158: 100; R_0402_1005Metric; Part RM04FTN1000; JLCPCB Part # C153111
R152, R153, R159, R160, R161, R162, R169: 4.7k; R_0402_1005Metric; Part 0402WGF4701TCE; JLCPCB Part # C25900
R163: 0R; R_0603_1608Metric; Part FRC0603F0000TS; JLCPCB Part # C2906974
R164, R167: 10k; R_0402_1005Metric; Part 0402WGF1002TCE; JLCPCB Part # C25744
R165: 150; R_0402_1005Metric; Part 0402WGF1500TCE; JLCPCB Part # C25082
R166, R168: 330; R_0402_1005Metric; Part 0402WGF3300TCE; JLCPCB Part # C25104
SW3: SW_Push; SW_Push_SPST_NO_Alps_SKRK; Part SKRKAHE020; JLCPCB Part # C202388
U21: XC7Z030_FBG676; Xilinx_FFG676; JLCPCB Part # C966962
U22: SN74LXC1T45DBVR; SOT-23-6_DBV_TEX; Part SN74LXC1T45DBVR; JLCPCB Part # C4364198

Connections:
+1V8_SYS: C172.2, R163.1, U22.6 (VCCB)
+1V8_XADC: C171.2, U21.M14 (VCCADC_0)
+3V3_SYS: C166.2, C167.2, C170.2, D22.1 (A), D23.1 (A), R152.2, R153.2, R159.2, R160.2, R161.2, R162.2, R164.2, R166.1, R168.1, R169.1, U21.U8 (RSVDVCC3), U21.V8 (RSVDVCC2), U21.W8 (RSVDVCC1), U22.1 (VCCA)
GND: C166.1, C167.1, C168.1, C169.1, C170.1, C171.1, C172.1, J20.1, J20.3, J20.5, J20.7, J20.9, J20.11, J20.13, J21.3 (GND), JP19.1 (A), Q11.2 (S), R167.2, SW3.2, U21.M13 (GNDADC_0), U21.N13 (VREFN_0), U21.N14 (VP_0), U21.P13 (VN_0), U21.P14 (VREFP_0), U21.V13 (RSVDGND), U22.2 (GND)
JTAG_SRST: J22.1, R162.1, U22.3 (A)
JTAG_TCK: R157.2, R160.1, U21.W12 (TCK_0)
JTAG_TDI: R158.2, R161.1, U21.V11 (TDI_0)
JTAG_TDO: R155.2, U21.W10 (TDO_0)
JTAG_TMS: R154.2, R159.1, U21.W11 (TMS_0)
unnamed: D22.3 (K), J21.1 (VCC)
unnamed: D23.3 (K), J20.2
unnamed: D24.1 (K), Q11.3 (D)
unnamed: D24.2 (A), R168.2
unnamed: J21.5 (G/+5), JP19.2 (B)
unnamed: J22.2, R156.2
unnamed: Q11.1 (G), R165.1, R166.2, R167.1
unnamed: R153.1, U21.R8 (INIT_B_0)
unnamed: R164.1, U21.T7 (CFGBVS_0)
unnamed: R169.2, U22.5 (DIR)
PL_DONE: R165.2, U21.W9 (DONE_0)
PL_PROG_B: R151.1
PROGRAM_B_0: C168.2, R151.2, R152.1, SW3.1, U21.V9 (PROGRAM_B_0)
PS_SRST_JTAG_1.8: U22.4 (B)
SRST: J20.14, R156.1
TCK: J20.6, J21.4 (TCK/SWCLK), R157.1
TDI: J20.10, J21.8 (TDI), R158.1
TDO: J20.8, J21.6 (TDO/SWO), R155.1
TMS: J20.4, J21.2 (TMS/SWDIO), R154.1
VCCBATT: C169.2, R163.2, U21.V15 (VCCBATT_0)
