electrodyssey/NASR-M/soc_b35.kicad_sch

## KiCad design soc_b35.kicad_sch (2025-10-22)

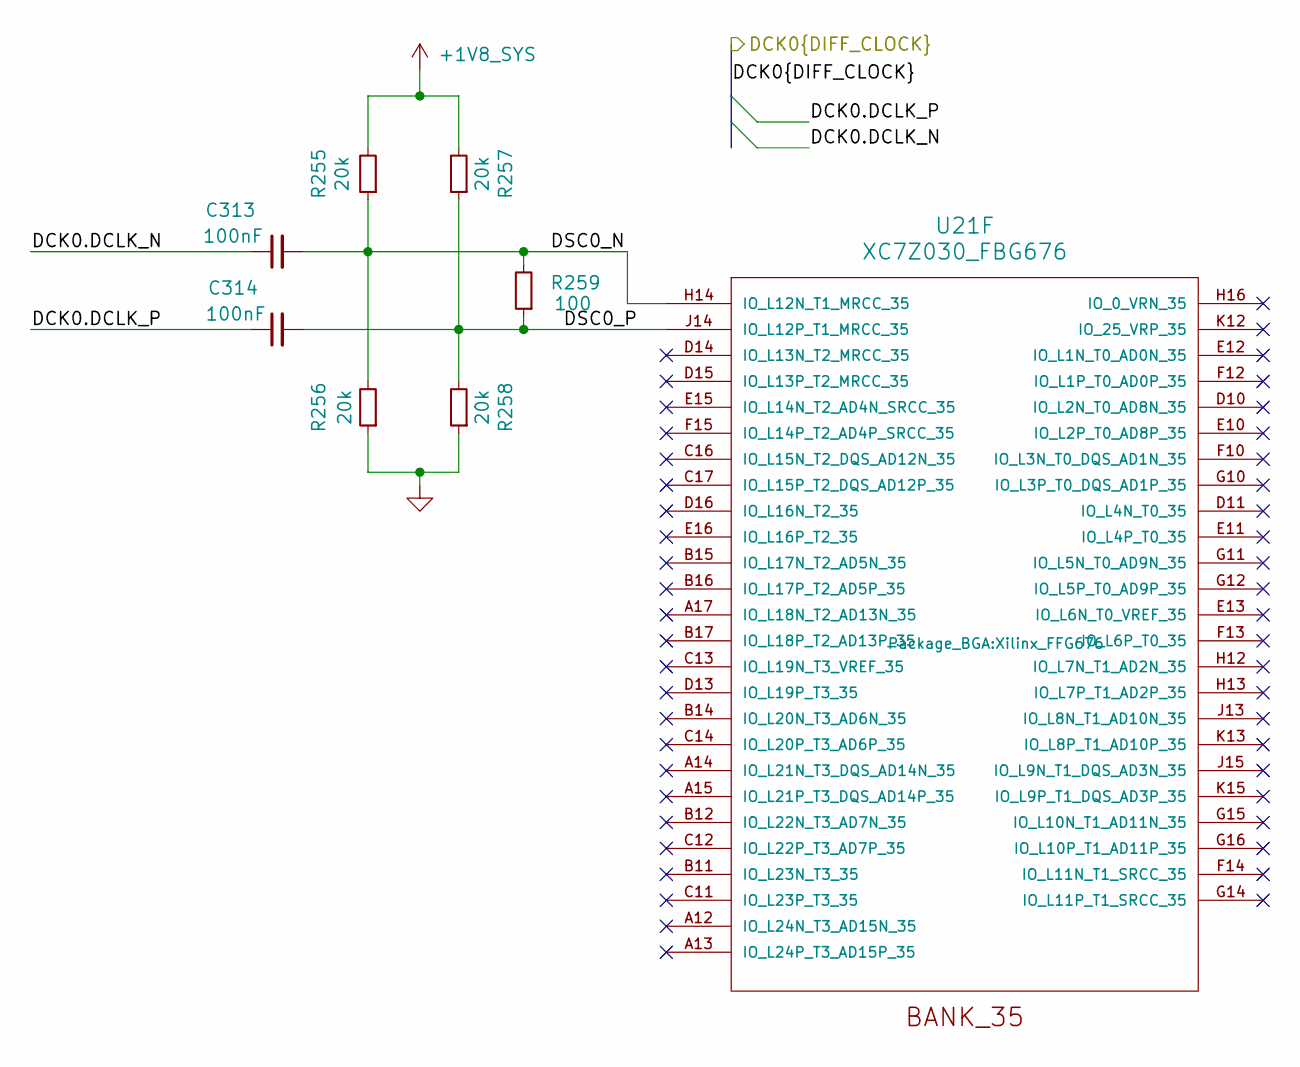
[picture p57: schematic soc_b35.kicad_sch]

Parts:
C313, C314: 100nF; C_0402_1005Metric; Part CC0402JRX7R8BB104; JLCPCB Part # C541465
R255, R256, R257, R258: 20k; R_0402_1005Metric; Part RT0402DRE0720KL; JLCPCB Part # C705678
R259: 100; R_0201_0603Metric; Part WR02X1000FAL; JLCPCB Part # C180289
U21: XC7Z030_FBG676; Xilinx_FFG676; JLCPCB Part # C966962

Connections:
+1V8_SYS: R255.2, R257.2
DCK0.DCLK_N: C313.1
DCK0.DCLK_P: C314.1
DSC0_N: C313.2, R255.1, R256.2, R259.2, U21.H14 (IO_L12N_T1_MRCC_35)
DSC0_P: C314.2, R257.1, R258.2, R259.1, U21.J14 (IO_L12P_T1_MRCC_35)
GND: R256.1, R258.1
