electrodyssey/NASR-M/soc_b501.kicad_sch

## KiCad design soc_b501.kicad_sch (2025-10-22)

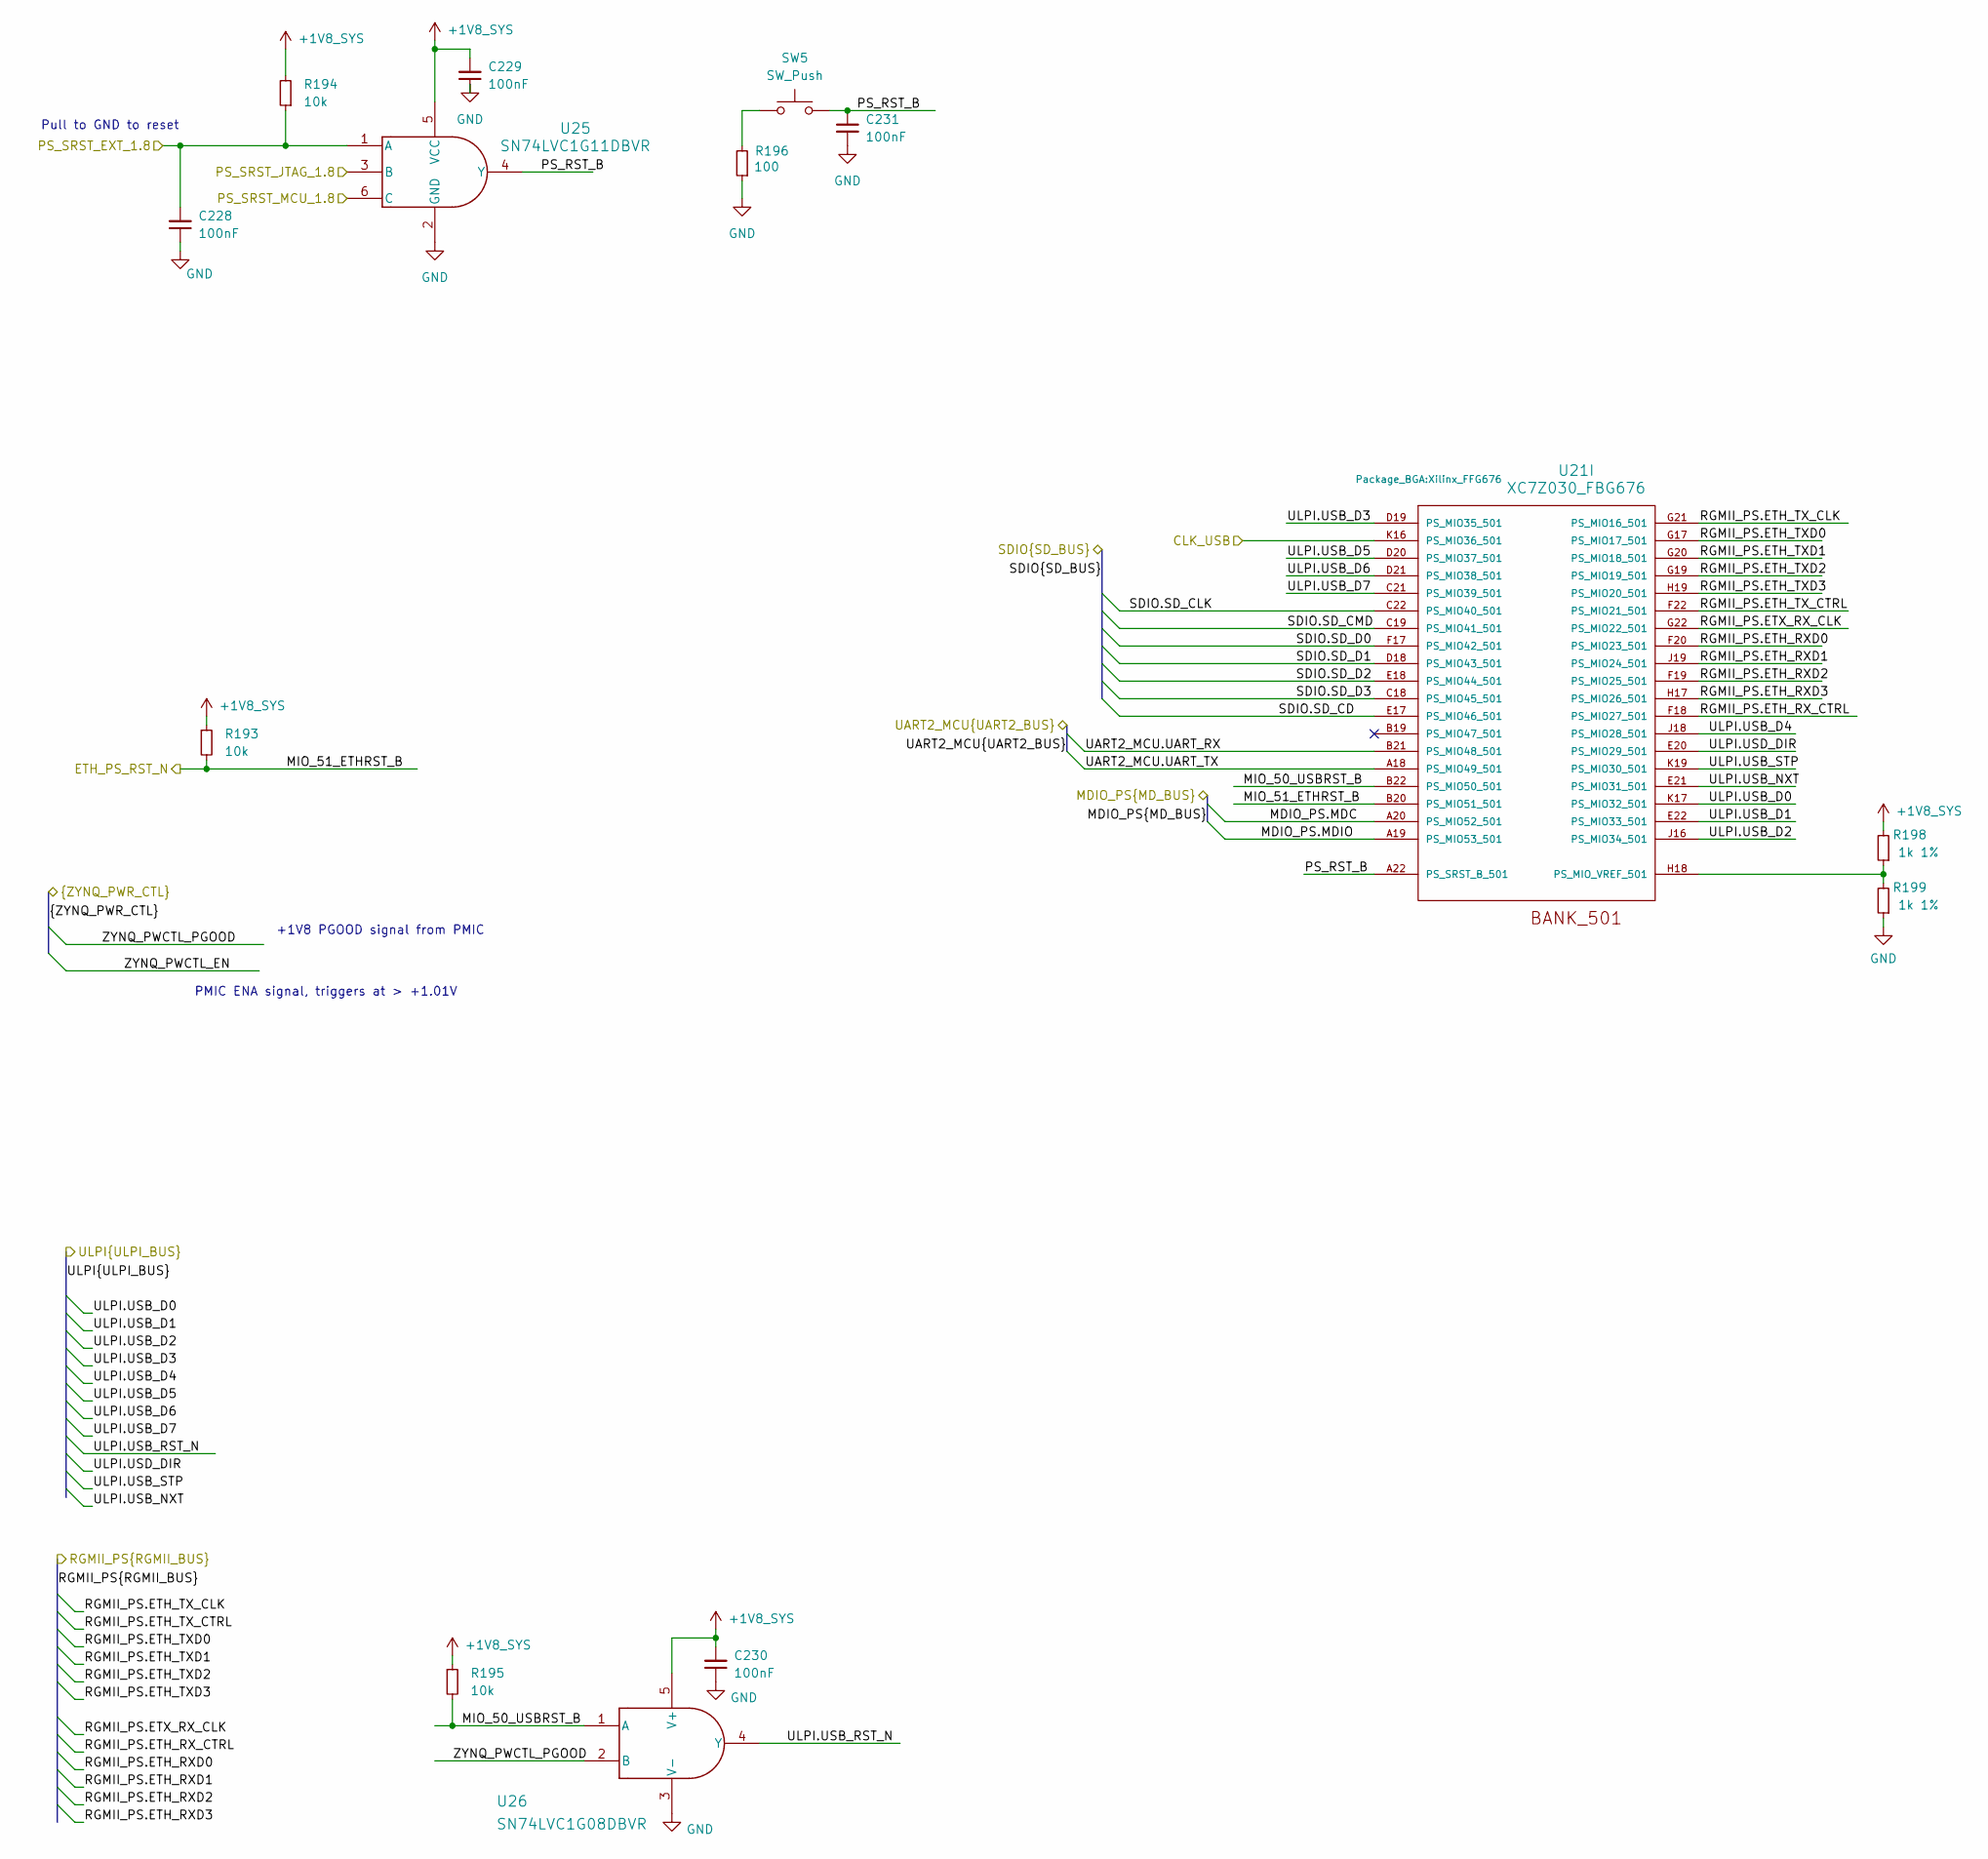
[picture p58: schematic soc_b501.kicad_sch]

Parts:
C228, C229, C230, C231: 100nF; C_0402_1005Metric; Part CC0402JRX7R8BB104; JLCPCB Part # C541465
R193, R194, R195: 10k; R_0402_1005Metric; Part 0402WGF1002TCE; JLCPCB Part # C25744
R196: 100; R_0402_1005Metric; Part RM04FTN1000; JLCPCB Part # C153111
R198, R199: 1k 1%; R_0603_1608Metric; Part 0603WAF1001T5E; JLCPCB Part # C21190
SW5: SW_Push; SW_Push_SPST_NO_Alps_SKRK; Part SKRKAHE020; JLCPCB Part # C202388
U21: XC7Z030_FBG676; Xilinx_FFG676; JLCPCB Part # C966962
U25: SN74LVC1G11DBVR; DBV0006A_N; Part SN74LVC1G11DBVR; JLCPCB Part # C22046
U26: SN74LVC1G08DBVR; DBV0005A_N; Part SN74LVC1G08DBVR; JLCPCB Part # C7666

Connections:
+1V8_SYS: C229.2, C230.2, R193.1, R194.2, R195.1, R198.2, U25.5 (VCC), U26.5 (V+)
CLK_USB: U21.K16 (PS_MIO36_501)
ETH_PS_RST_N: R193.2, U21.B20 (PS_MIO51_501)
GND: C228.1, C229.1, C230.1, C231.2, R196.1, R199.1, U25.2 (GND), U26.3 (V-)
MDIO_PS.MDC: U21.A20 (PS_MIO52_501)
MDIO_PS.MDIO: U21.A19 (PS_MIO53_501)
MIO_50_USBRST_B: R195.2, U21.B22 (PS_MIO50_501), U26.1 (A)
unnamed: R196.2, SW5.1
unnamed: R198.1, R199.2, U21.H18 (PS_MIO_VREF_501)
PS_RST_B: C231.1, SW5.2, U21.A22 (PS_SRST_B_501), U25.4 (Y)
PS_SRST_EXT_1.8: C228.2, R194.1, U25.1 (A)
PS_SRST_JTAG_1.8: U25.3 (B)
PS_SRST_MCU_1.8: U25.6 (C)
RGMII_PS.ETH_RXD0: U21.F20 (PS_MIO23_501)
RGMII_PS.ETH_RXD1: U21.J19 (PS_MIO24_501)
RGMII_PS.ETH_RXD2: U21.F19 (PS_MIO25_501)
RGMII_PS.ETH_RXD3: U21.H17 (PS_MIO26_501)
RGMII_PS.ETH_RX_CTRL: U21.F18 (PS_MIO27_501)
RGMII_PS.ETH_TXD0: U21.G17 (PS_MIO17_501)
RGMII_PS.ETH_TXD1: U21.G20 (PS_MIO18_501)
RGMII_PS.ETH_TXD2: U21.G19 (PS_MIO19_501)
RGMII_PS.ETH_TXD3: U21.H19 (PS_MIO20_501)
RGMII_PS.ETH_TX_CLK: U21.G21 (PS_MIO16_501)
RGMII_PS.ETH_TX_CTRL: U21.F22 (PS_MIO21_501)
RGMII_PS.ETX_RX_CLK: U21.G22 (PS_MIO22_501)
SDIO.SD_CD: U21.E17 (PS_MIO46_501)
SDIO.SD_CLK: U21.C22 (PS_MIO40_501)
SDIO.SD_CMD: U21.C19 (PS_MIO41_501)
SDIO.SD_D0: U21.F17 (PS_MIO42_501)
SDIO.SD_D1: U21.D18 (PS_MIO43_501)
SDIO.SD_D2: U21.E18 (PS_MIO44_501)
SDIO.SD_D3: U21.C18 (PS_MIO45_501)
UART2_MCU.UART_RX: U21.B21 (PS_MIO48_501)
UART2_MCU.UART_TX: U21.A18 (PS_MIO49_501)
ULPI.USB_D0: U21.K17 (PS_MIO32_501)
ULPI.USB_D1: U21.E22 (PS_MIO33_501)
ULPI.USB_D2: U21.J16 (PS_MIO34_501)
ULPI.USB_D3: U21.D19 (PS_MIO35_501)
ULPI.USB_D4: U21.J18 (PS_MIO28_501)
ULPI.USB_D5: U21.D20 (PS_MIO37_501)
ULPI.USB_D6: U21.D21 (PS_MIO38_501)
ULPI.USB_D7: U21.C21 (PS_MIO39_501)
ULPI.USB_NXT: U21.E21 (PS_MIO31_501)
ULPI.USB_RST_N: U26.4 (Y)
ULPI.USB_STP: U21.K19 (PS_MIO30_501)
ULPI.USD_DIR: U21.E20 (PS_MIO29_501)
ZYNQ_PWCTL_PGOOD: U26.2 (B)

Notes on the sheet:
Pull to GND to reset
+1V8 PGOOD signal from PMIC
PMIC ENA signal, triggers at > +1.01V
