electrodyssey/NASR-M/soc_bank500.kicad_sch

## KiCad design soc_bank500.kicad_sch (2025-10-22)

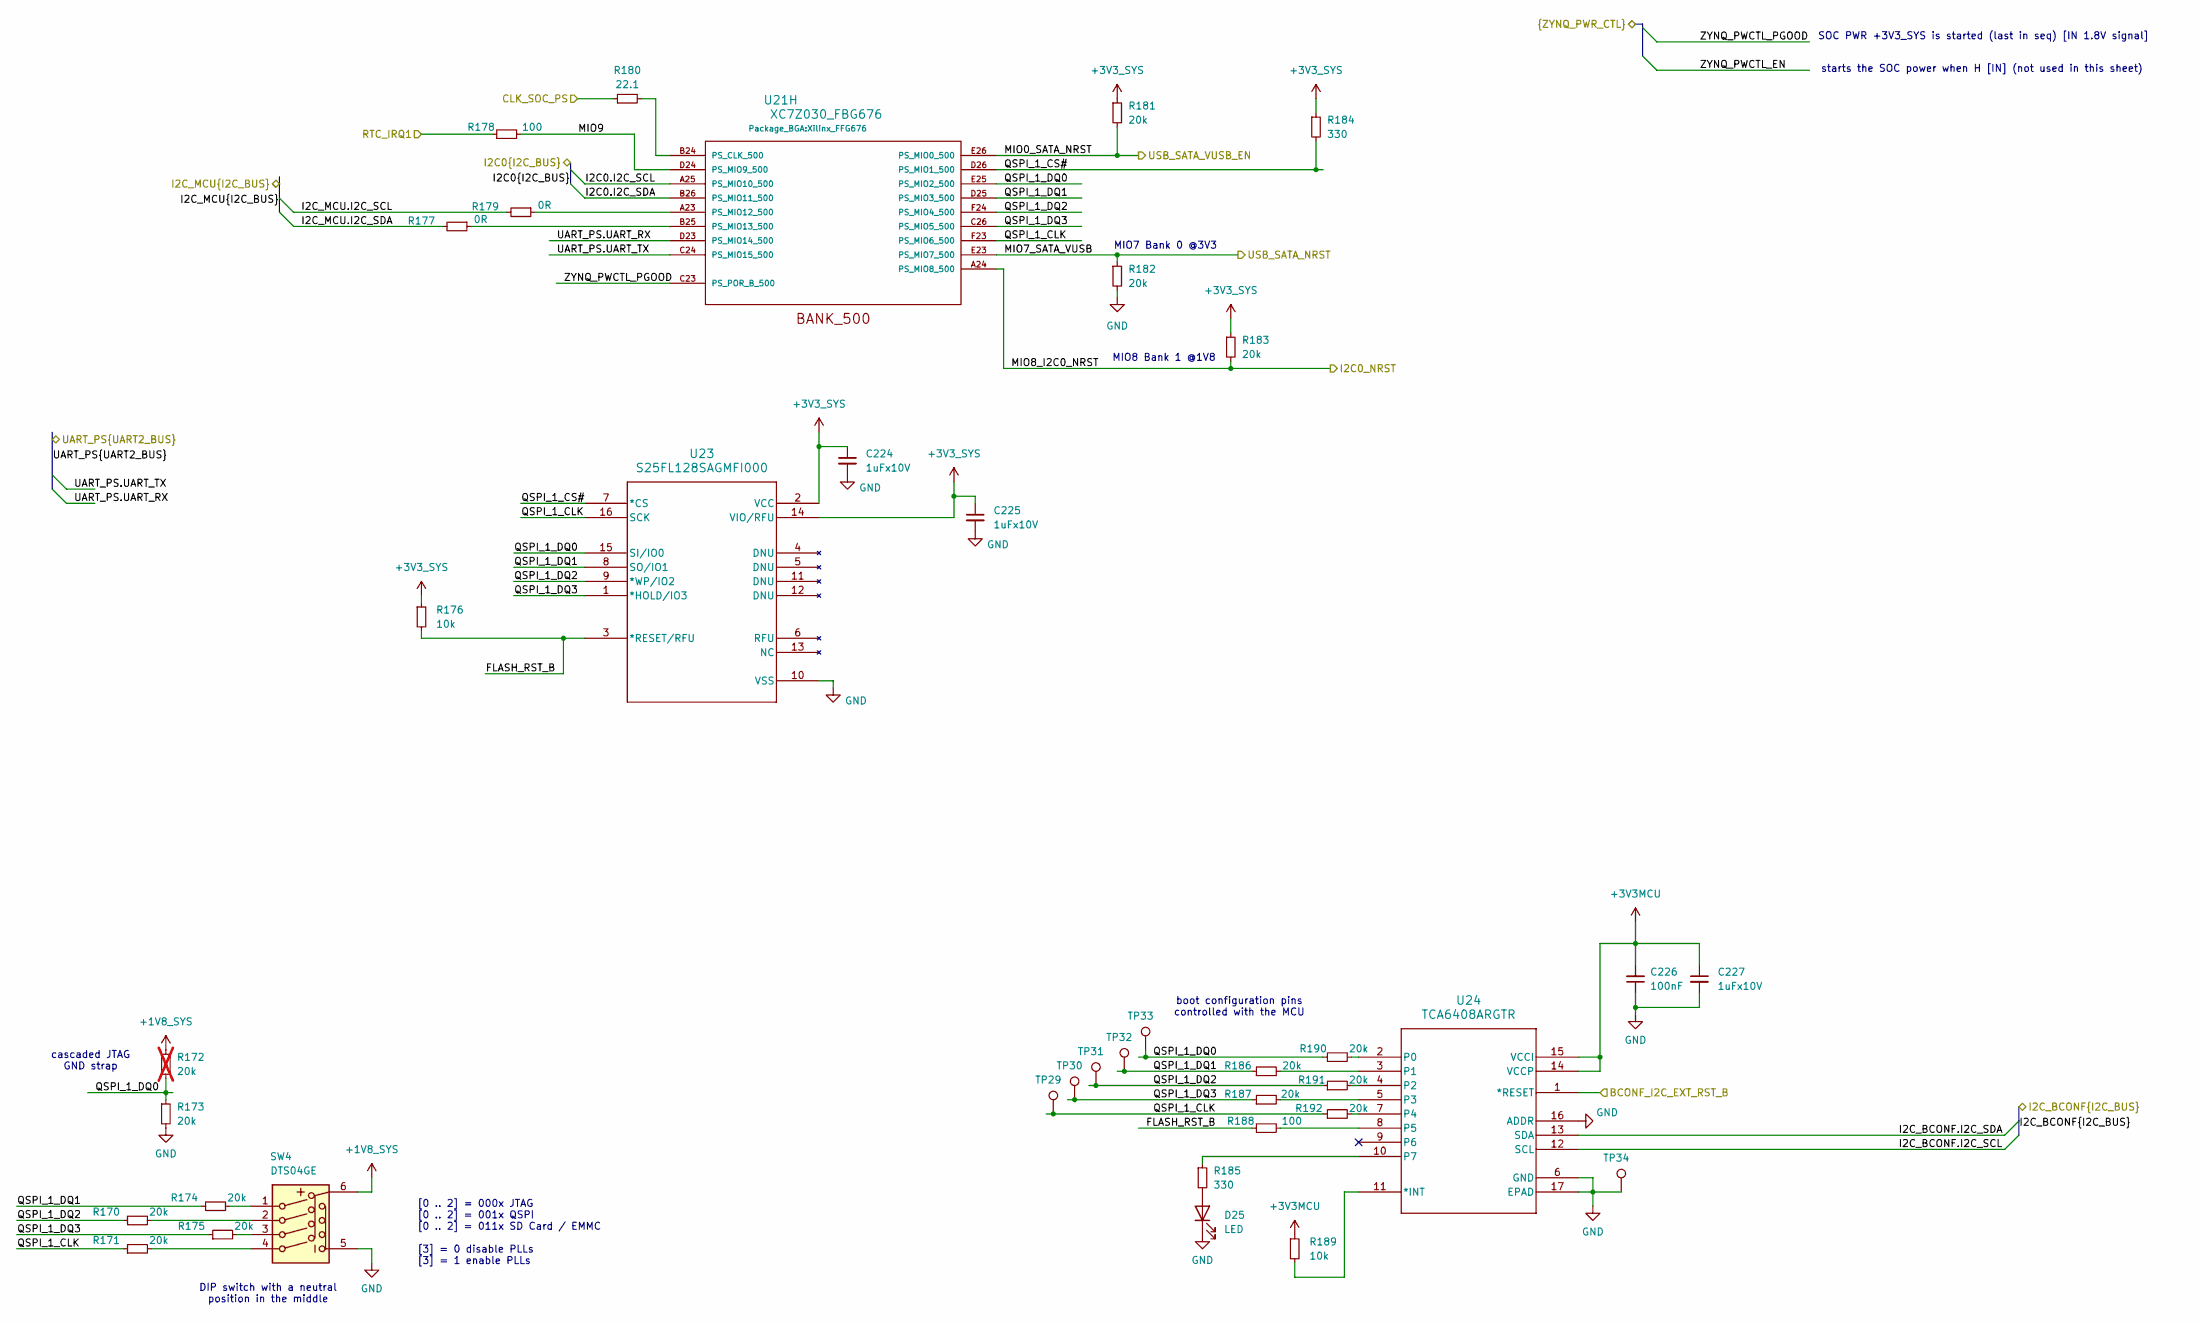
[picture p59: schematic soc_bank500.kicad_sch]

Parts:
C224, C225, C227: 1uFx10V; C_0603_1608Metric; JLCPCB Part # C841050
C226: 100nF; C_0402_1005Metric; Part CC0402JRX7R8BB104; JLCPCB Part # C541465
D25: LED; LED_0805_2012Metric; Part HL-PSC-2012S11GC; JLCPCB Part # C497958
R170, R171, R173, R174, R175, R181, R182, R183, R186, R187, R190, R191, R192: 20k; R_0402_1005Metric; Part RT0402DRE0720KL; JLCPCB Part # C705678
R172: 20k; R_0402_1005Metric; Part RT0402CRD0720KL; JLCPCB Part # C705658; not fitted
R176, R189: 10k; R_0402_1005Metric; Part 0402WGF1002TCE; JLCPCB Part # C25744
R177, R179: 0R; R_0603_1608Metric; Part FRC0603F0000TS; JLCPCB Part # C2906974
R178, R188: 100; R_0402_1005Metric; Part RM04FTN1000; JLCPCB Part # C153111
R180: 22.1; R_0402_1005Metric; Part WR04X22R1FTL; JLCPCB Part # C170264
R184, R185: 330; R_0402_1005Metric; Part 0402WGF3300TCE; JLCPCB Part # C25104
SW4: DTS04GE; MFR.Part # DTS04GE; JLCPCB Part # C3294670
TP29, TP30, TP31, TP32, TP33, TP34: TestPoint; TestPoint_Pad_D1.0mm
U21: XC7Z030_FBG676; Xilinx_FFG676; JLCPCB Part # C966962
U23: S25FL128SAGMFI000; SO3016_SPA; Part S25FL128SAGMFI000; JLCPCB Part # C393875
U24: TCA6408ARGTR; RGT16_1P45X1P45; Part TCA6408ARGTR; JLCPCB Part # C181499

Connections:
+1V8_SYS: R172.1, SW4.6
+3V3MCU: C226.2, C227.1, R189.1, U24.14 (VCCP), U24.15 (VCCI)
+3V3_SYS: C224.1, C225.1, R176.1, R181.1, R183.1, R184.1, U23.2 (VCC), U23.14 (VIO/RFU)
BCONF_I2C_EXT_RST_B: U24.1 (*RESET)
CLK_SOC_PS: R180.1
FLASH_RST_B: R176.2, R188.1, U23.3 (*RESET/RFU)
GND: C224.2, C225.2, C226.1, C227.2, D25.1 (K), R173.2, R182.2, SW4.5, TP34.1, U23.10 (VSS), U24.6 (GND), U24.16 (ADDR), U24.17 (EPAD)
I2C0.I2C_SCL: U21.A25 (PS_MIO10_500)
I2C0.I2C_SDA: U21.B26 (PS_MIO11_500)
I2C0_NRST: R183.2, U21.A24 (PS_MIO8_500)
I2C_BCONF.I2C_SCL: U24.12 (SCL)
I2C_BCONF.I2C_SDA: U24.13 (SDA)
I2C_MCU.I2C_SCL: R179.2
I2C_MCU.I2C_SDA: R177.2
MIO0_SATA_NRST: R181.2, U21.E26 (PS_MIO0_500)
MIO7_SATA_VUSB: R182.1, U21.E23 (PS_MIO7_500)
MIO9: R178.2, U21.D24 (PS_MIO9_500)
unnamed: D25.2 (A), R185.2
unnamed: R170.2, SW4.2
unnamed: R171.2, SW4.4
unnamed: R174.2, SW4.1
unnamed: R175.2, SW4.3
unnamed: R177.1, U21.B25 (PS_MIO13_500)
unnamed: R179.1, U21.A23 (PS_MIO12_500)
unnamed: R180.2, U21.B24 (PS_CLK_500)
unnamed: R185.1, U24.10 (P7)
unnamed: R186.2, U24.3 (P1)
unnamed: R187.2, U24.5 (P3)
unnamed: R188.2, U24.8 (P5)
unnamed: R189.2, U24.11 (*INT)
unnamed: R190.2, U24.2 (P0)
unnamed: R191.2, U24.4 (P2)
unnamed: R192.2, U24.7 (P4)
QSPI_1_CLK: R171.1, R192.1, TP29.1, U21.F23 (PS_MIO6_500), U23.16 (SCK)
QSPI_1_CS#: R184.2, U21.D26 (PS_MIO1_500), U23.7 (*CS)
QSPI_1_DQ0: R172.2, R173.1, R190.1, TP33.1, U21.E25 (PS_MIO2_500), U23.15 (SI/IO0)
QSPI_1_DQ1: R174.1, R186.1, TP32.1, U21.D25 (PS_MIO3_500), U23.8 (SO/IO1)
QSPI_1_DQ2: R170.1, R191.1, TP31.1, U21.F24 (PS_MIO4_500), U23.9 (*WP/IO2)
QSPI_1_DQ3: R175.1, R187.1, TP30.1, U21.C26 (PS_MIO5_500), U23.1 (*HOLD/IO3)
RTC_IRQ1: R178.1
UART_PS.UART_RX: U21.D23 (PS_MIO14_500)
UART_PS.UART_TX: U21.C24 (PS_MIO15_500)
ZYNQ_PWCTL_PGOOD: U21.C23 (PS_POR_B_500)

Notes on the sheet:
boot configuration pins controlled with the MCU
DIP switch with a neutral position in the middle
MIO7 Bank 0 @3V3
SOC PWR +3V3_SYS is started (last in seq) [IN 1.8V signal]
starts the SOC power when H [IN] (not used in this sheet)
MIO8 Bank 1 @1V8
cascaded JTAG GND strap
[0 .. 2] = 000x JTAG [0 .. 2] = 001x QSPI [0 .. 2] = 011x SD Card / EMMC [3] = 0 disable PLLs [3] = 1 enable PLLs
