electrodyssey/NASR-M/soc_i2c.kicad_sch

## KiCad design soc_i2c.kicad_sch (2025-10-22)

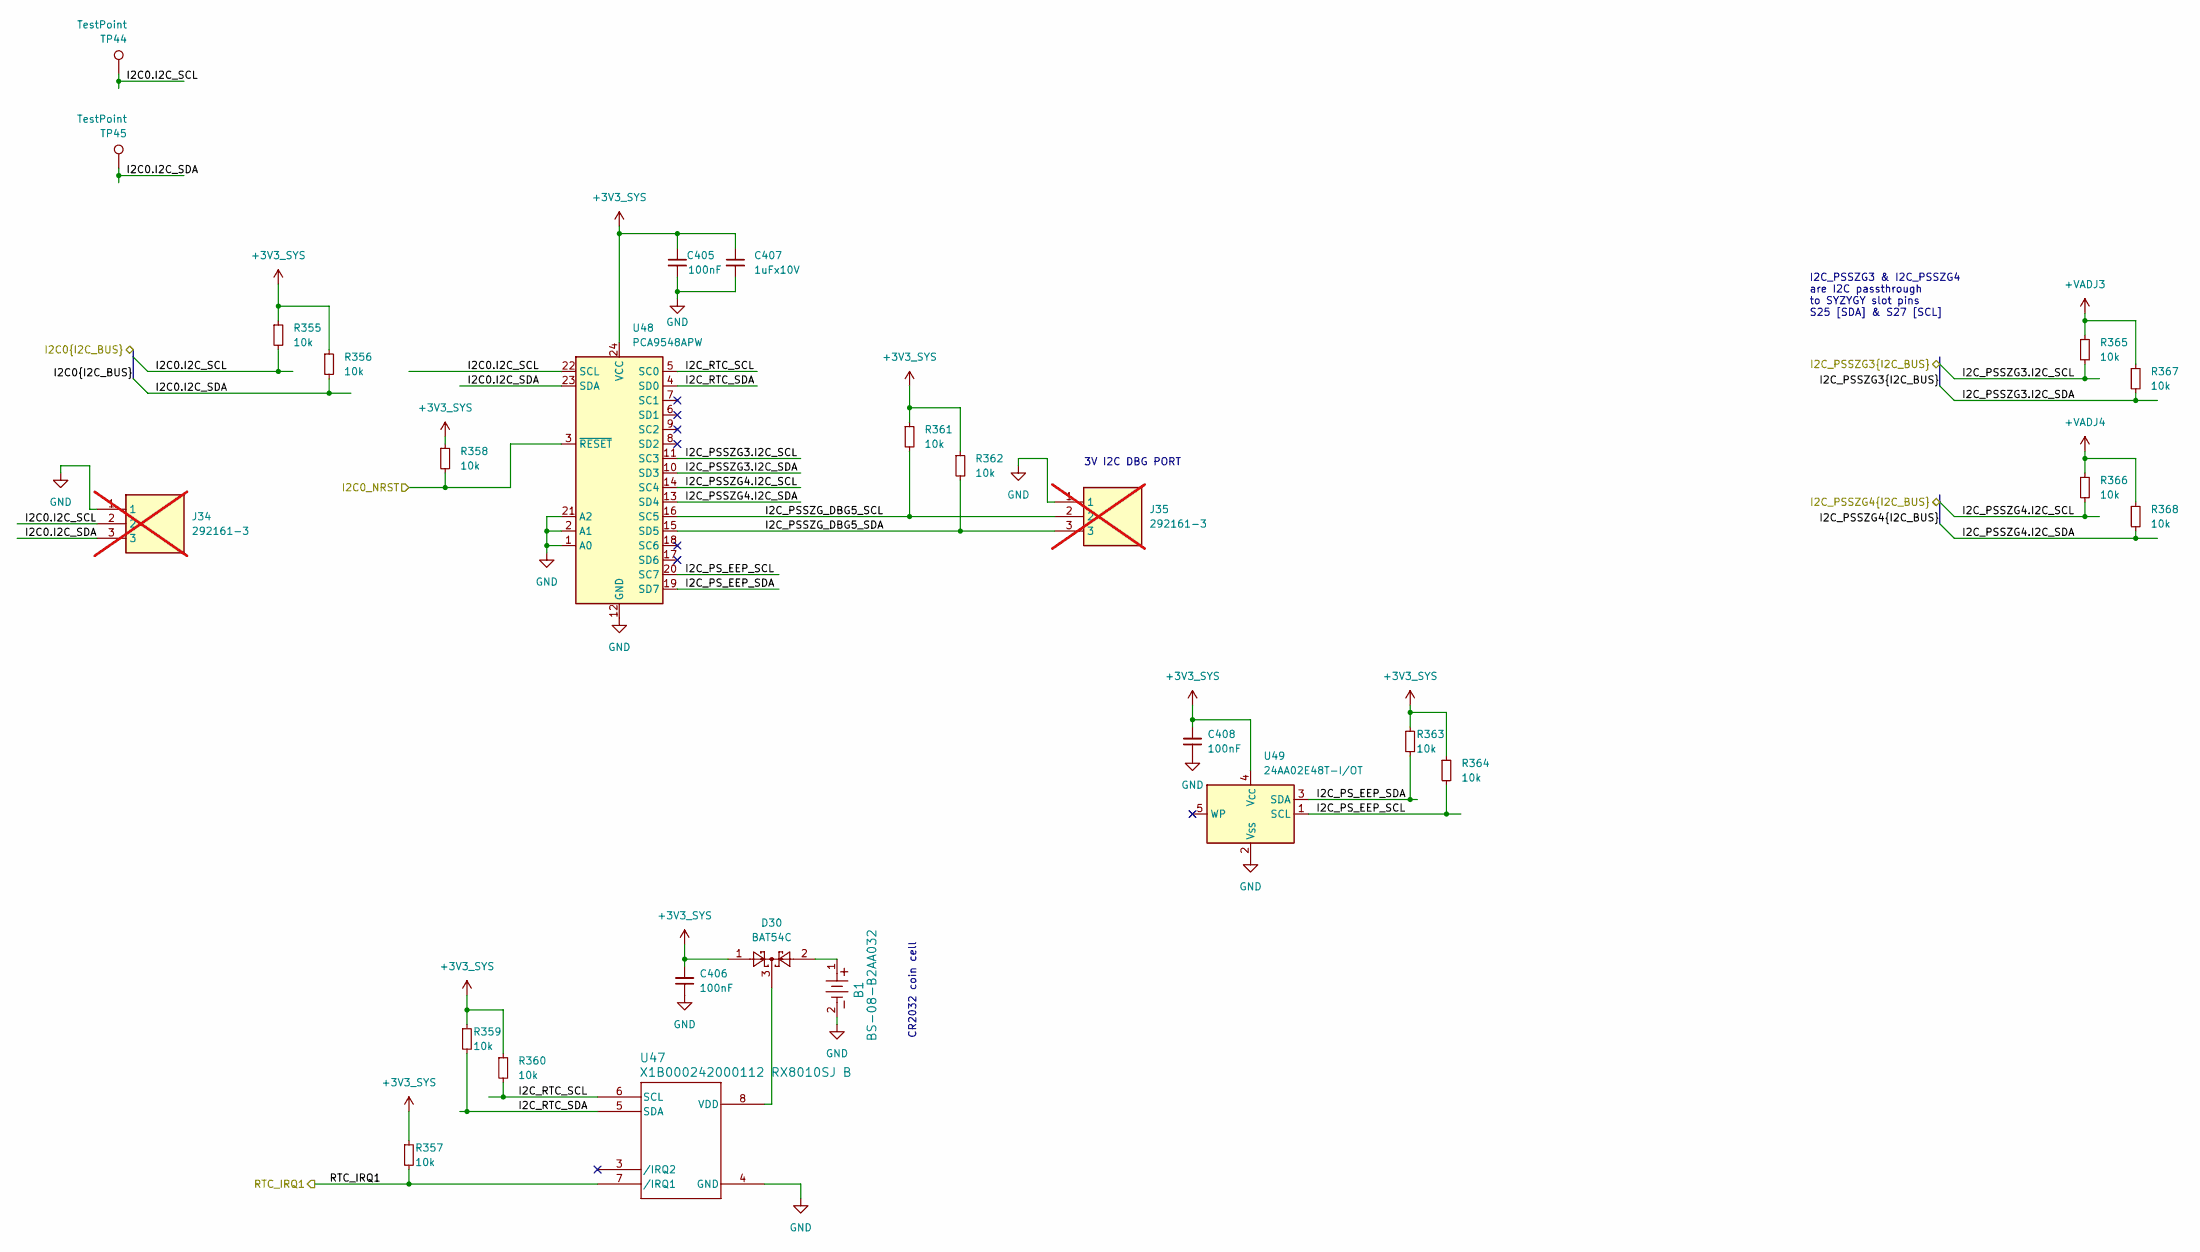
[picture p60: schematic soc_i2c.kicad_sch]

Parts:
B1: BS-08-B2AA032; BS-08-B2AA032_MYG; JLCPCB Part # C5290173
C405, C406, C408: 100nF; C_0402_1005Metric; Part CC0402JRX7R8BB104; JLCPCB Part # C541465
C407: 1uFx10V; C_0603_1608Metric; JLCPCB Part # C841050
D30: BAT54C; SOT-23; Part BAT54C-7-MS; JLCPCB Part # C2995316
J34, J35: 292161-3; SHDR3W60P0X200_1X3_780X360X680P; Mouser Part Number 571-292161-3; not fitted
R355, R356, R357, R358, R359, R360, R361, R362, R363, R364, R365, R366, R367, R368: 10k; R_0402_1005Metric; Part 0402WGF1002TCE; JLCPCB Part # C25744
TP44, TP45: TestPoint; TestPoint_Pad_D1.0mm
U47: X1B000242000112 RX8010SJ B; RX8010SJ_SOP-8_EPS; Part RX8010SJ; JLCPCB Part # C91734
U48: PCA9548APW; TSSOP-24_4.4x7.8mm_P0.65mm; JLCPCB Part # C21198
U49: 24AA02E48T-I/OT; SOT-23-5; Part 24AA02E48T-I/OT; JLCPCB Part # C38987

Connections:
+3V3_SYS: C405.1, C406.2, C407.1, C408.2, D30.1, R355.1, R356.1, R357.1, R358.1, R359.1, R360.1, R361.1, R362.1, R363.1, R364.1, U48.24 (VCC), U49.4 (V_{CC})
+VADJ3: R365.1, R367.1
+VADJ4: R366.1, R368.1
GND: B1.2, C405.2, C406.1, C407.2, C408.1, J34.1, J35.1, U47.4 (GND), U48.1 (A0), U48.2 (A1), U48.12 (GND), U48.21 (A2), U49.2 (V_{SS})
I2C0.I2C_SCL: J34.2, R355.2, TP44.1, U48.22 (SCL)
I2C0.I2C_SDA: J34.3, R356.2, TP45.1, U48.23 (SDA)
I2C0_NRST: R358.2, U48.3 (~RESET)
I2C_PSSZG3.I2C_SCL: R365.2, U48.11 (SC3)
I2C_PSSZG3.I2C_SDA: R367.2, U48.10 (SD3)
I2C_PSSZG4.I2C_SCL: R366.2, U48.14 (SC4)
I2C_PSSZG4.I2C_SDA: R368.2, U48.13 (SD4)
I2C_PSSZG_DBG5_SCL: J35.2, R361.2, U48.16 (SC5)
I2C_PSSZG_DBG5_SDA: J35.3, R362.2, U48.15 (SD5)
I2C_PS_EEP_SCL: R364.2, U48.20 (SC7), U49.1 (SCL)
I2C_PS_EEP_SDA: R363.2, U48.19 (SD7), U49.3 (SDA)
I2C_RTC_SCL: R360.2, U47.6 (SCL), U48.5 (SC0)
I2C_RTC_SDA: R359.2, U47.5 (SDA), U48.4 (SD0)
unnamed: B1.1, D30.2
unnamed: D30.3, U47.8 (VDD)
RTC_IRQ1: R357.2, U47.7 (/IRQ1)

Notes on the sheet:
3V I2C DBG PORT
CR2032 coin cell
I2C_PSSZG3 & I2C_PSSZG4 are I2C passthrough to SYZYGY slot pins S25 [SDA] & S27 [SCL]
