electrodyssey/NASR-M/soc_power.kicad_sch

## KiCad design soc_power.kicad_sch (2025-10-22)

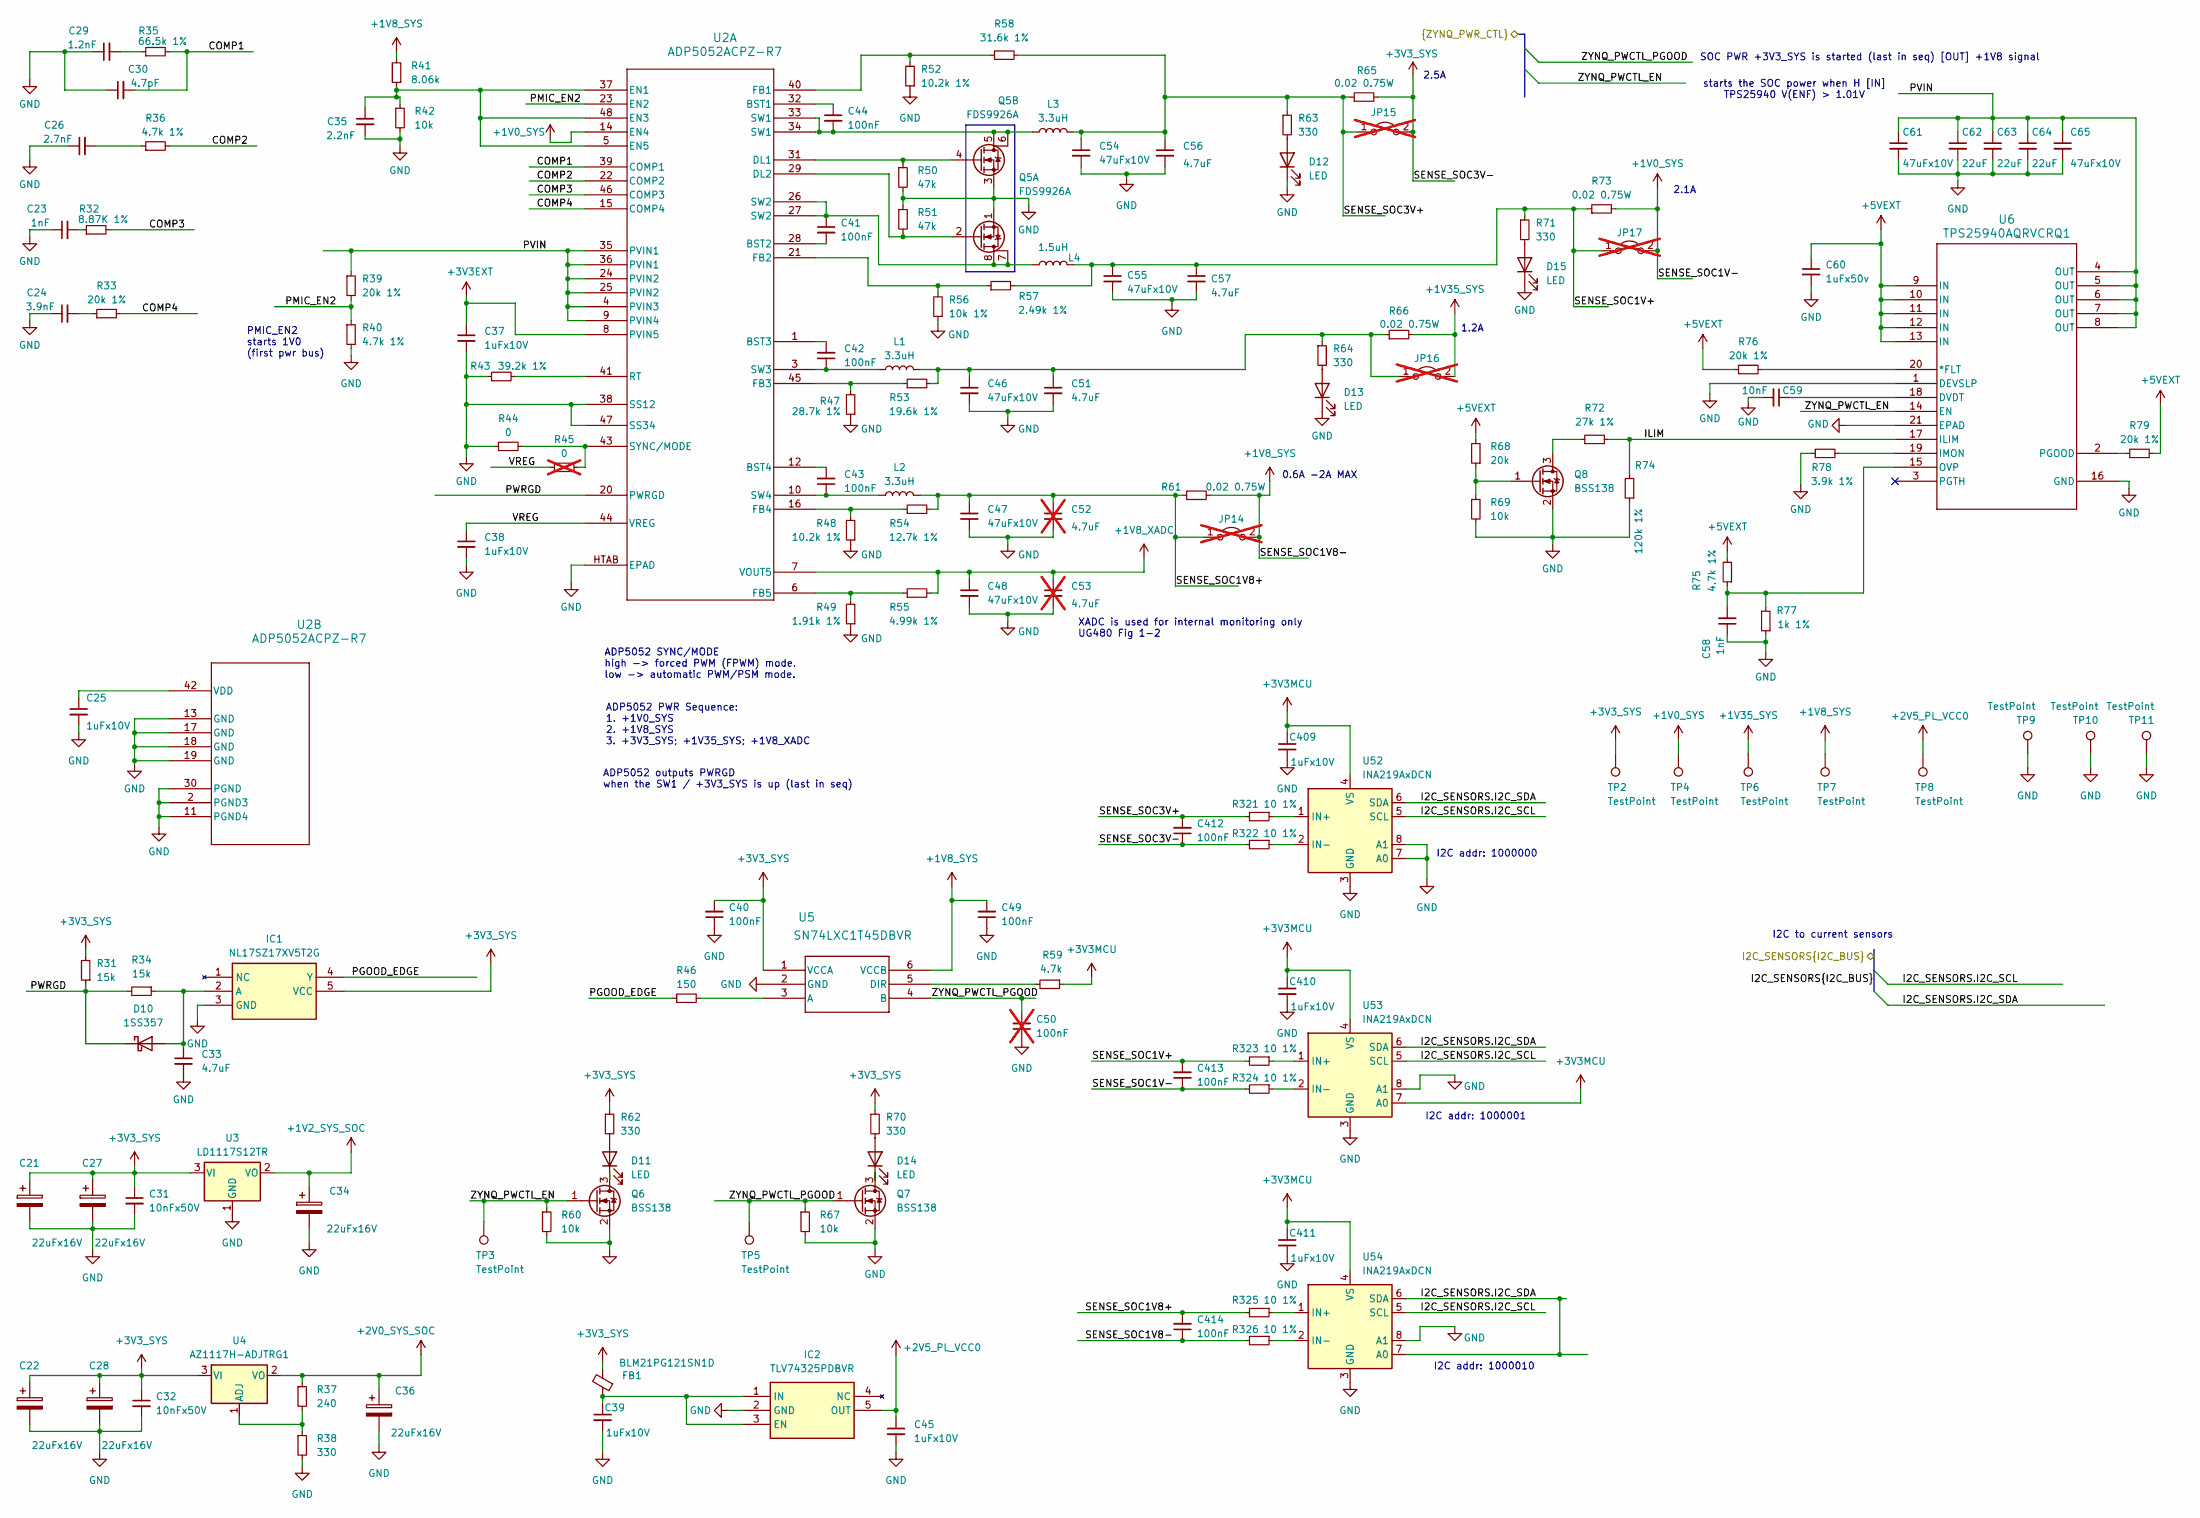
[picture p61: schematic soc_power.kicad_sch]

Parts:
C21, C22, C27, C28, C34, C36: 22uFx16V; CP_EIA-6032-15_Kemet-U; Part TR3C226K016C0350; JLCPCB Part # C1954274
C23, C58: 1nF; C_0603_1608Metric; Part CL10B102KB8NNNC; JLCPCB Part # C1588
C24: 3.9nF; C_0603_1608Metric; Part GRM188R71H392KA01D; JLCPCB Part # C470850
C25, C37, C38, C39, C45, C409, C410, C411: 1uFx10V; C_0603_1608Metric; JLCPCB Part # C841050
C26: 2.7nF; C_0805_2012Metric; Part NL0805B272K500CPBN; JLCPCB Part # C2961025
C29: 1.2nF; C_0805_2012Metric; Part C0805N122J050T; JLCPCB Part # C105920
C30: 4.7pF; C_0603_1608Metric; Part 0603CG4R7C500NT; JLCPCB Part # C1669
C31, C32: 10nFx50V; C_1206_3216Metric; JLCPCB Part # C513774
C33, C51, C56, C57: 4.7uF; C_1206_3216Metric; JLCPCB Part # C415529
C35: 2.2nF; C_0603_1608Metric; Part 0603B222K500NT; JLCPCB Part # C1604
C40, C41, C42, C43, C44, C49, C412, C413, C414: 100nF; C_0402_1005Metric; Part CC0402JRX7R8BB104; JLCPCB Part # C541465
C46, C47, C48, C54, C55, C61, C65: 47uFx10V; C_1210_3225Metric; Part GRM32ER71A476KE15L; JLCPCB Part # C84494
C50: 100nF; C_0402_1005Metric; Part CC0402JRX7R8BB104; JLCPCB Part # C541465; not fitted
C52, C53: 4.7uF; C_1206_3216Metric; JLCPCB Part # C415529; not fitted
C59: 10nF; C_0603_1608Metric; Part 0603B103K500NT; JLCPCB Part # C57112
C60: 1uFx50v; C_1206_3216Metric; JLCPCB Part # C1848
C62, C63, C64: 22uF; C_0805_2012Metric; Part CL21A226MQQNNNE; JLCPCB Part # C5674
D10: 1SS357; D_SOD-323; JLCPCB Part # C5240602
D11, D12, D13, D14, D15: LED; LED_0805_2012Metric; Part HL-PSC-2012S11GC; JLCPCB Part # C497958
FB1: BLM21PG121SN1D; L_0805_2012Metric; Part BLM21PG121SN1D; JLCPCB Part # C79382
IC1: NL17SZ17XV5T2G; SOTFL50P160X60-5N; Mouser Part Number 863-NL17SZ17XV5T2G
IC2: TLV74325PDBVR; SOT95P280X145-5N; Mouser Part Number 595-TLV74325PDBVR
JP14, JP15, JP16, JP17: Jumper_2_Open; PinHeader_1x02_P2.54mm_Vertical; not fitted
L1, L2, L3: 3.3uH; SRYH.0530.YF3R3MT00; Part SRYH.0530.YF3R3MT00; JLCPCB Part # C5122863
L4: 1.5uH; L_SMNR3010; Part SMNR3010-1R5MT; JLCPCB Part # C135227
Q5: FDS9926A; SOIC-8_3.9x4.9mm_P1.27mm; JLCPCB Part # C3021108
Q6, Q7, Q8: BSS138; SOT-23; JLCPCB Part # C52895
R31, R34: 15k; R_0603_1608Metric; Part 0603WAF1502T5E; JLCPCB Part # C22809
R32: 8.87K 1%; R_0603_1608Metric; Part FRC0603F8871TS; JLCPCB Part # C2998144
R33, R39, R76, R79: 20k 1%; R_0402_1005Metric; Part RT0402DRE0720KL; JLCPCB Part # C705678
R35: 66.5k 1%; R_0603_1608Metric; Part RS-03K6652FT; JLCPCB Part # C321977
R36, R40, R75: 4.7k 1%; R_0402_1005Metric; Part 0402WGF4701TCE; JLCPCB Part # C25900
R37: 240; R_0402_1005Metric; Part RT0402DRE07240RL; JLCPCB Part # C853865
R38: 330; R_0402_1005Metric; Part FRC0402J331 TS; JLCPCB Part # C2906929
R41: 8.06k; R_0603_1608Metric; Part FRC0603F8061TS; JLCPCB Part # C2960681
R42, R60, R67, R69: 10k; R_0402_1005Metric; Part 0402WGF1002TCE; JLCPCB Part # C25744
R43: 39.2k 1%; R_0603_1608Metric; Part 0603WAF3922T5E; JLCPCB Part # C23037
R44: 0; R_0805_2012Metric; Part 0805W8F0000T5E; JLCPCB Part # C17477
R45: 0; R_0805_2012Metric; JLCPCB Part # C2936632; not fitted
R46: 150; R_0402_1005Metric; Part 0402WGF1500TCE; JLCPCB Part # C25082
R47: 28.7k 1%; R_0603_1608Metric; Part RC0603FR-0728K7L; JLCPCB Part # C245945
R48, R52: 10.2k 1%; R_0603_1608Metric; Part 0603WAF1022T5E; JLCPCB Part # C22772
R49: 1.91k 1%; R_0603_1608Metric; Part 0603WAF1911T5E; JLCPCB Part # C22853
R50, R51: 47k; R_0603_1608Metric; JLCPCB Part # C5139555
R53: 19.6k 1%; R_0603_1608Metric; Part 0603WAF1962T5E; JLCPCB Part # C22898
R54: 12.7k 1%; R_0603_1608Metric; Part AC0603FR-0712K7L; JLCPCB Part # C138285
R55: 4.99k 1%; R_0603_1608Metric; Part 0603WAF4991T5E; JLCPCB Part # C23046
R56: 10k 1%; R_0603_1608Metric; Part 0603WAF1002T5E; JLCPCB Part # C25804
R57: 2.49k 1%; R_0603_1608Metric; Part 0603WAF2491T5E; JLCPCB Part # C22908
R58: 31.6k 1%; R_0603_1608Metric; Part 0603WAF3162T5E; JLCPCB Part # C25967
R59: 4.7k; R_0402_1005Metric; Part 0402WGF4701TCE; JLCPCB Part # C25900
R61, R65, R66, R73: 0.02 0.75W; R_2010_5025Metric_Pad1.40x2.65mm_HandSolder; Part RLM20FECR020; JLCPCB Part # C912937
R62, R63, R64, R70, R71: 330; R_0402_1005Metric; Part 0402WGF3300TCE; JLCPCB Part # C25104
R68: 20k; R_0402_1005Metric; Part RT0402DRE0720KL; JLCPCB Part # C705678
R72: 27k 1%; R_0603_1608Metric; Part 0603WAF2702T5E; JLCPCB Part # C22967
R74: 120k 1%; R_0603_1608Metric; Part 0603WAF1203T5E; JLCPCB Part # C25808
R77: 1k 1%; R_0603_1608Metric; Part 0603WAF1001T5E; JLCPCB Part # C21190
R78: 3.9k 1%; R_0603_1608Metric; Part 0603WAF3901T5E; JLCPCB Part # C23018
R321, R322, R323, R324, R325, R326: 10 1%; R_0402_1005Metric; Part RTT0210R0FTH; JLCPCB Part # C102766
TP2, TP3, TP4, TP5, TP6, TP7, TP8, TP9, TP10, TP11: TestPoint; TestPoint_Pad_D1.0mm
U2: ADP5052ACPZ-R7; CP_48_13_ADI; JLCPCB Part # C459150
U3: LD1117S12TR; SOT-223-3_TabPin2; Part LD1117S12TR; JLCPCB Part # C155612
U4: AZ1117H-ADJTRG1; SOT-223-3_TabPin2; Part AZ1117H-ADJTRG1; JLCPCB Part # C110475
U5: SN74LXC1T45DBVR; SOT-23-6_DBV_TEX; Part SN74LXC1T45DBVR; JLCPCB Part # C4364198
U6: TPS25940AQRVCRQ1; RVC20_TEX; JLCPCB Part # C2155806
U52, U53, U54: INA219AxDCN; SOT-23-8; Part INA219AIDCNR; JLCPCB Part # C87469

Connections:
+1V0_SYS: C413.1, JP17.2 (B), R73.2, R324.2, TP4.1, U2.14 (EN4)
+1V2_SYS_SOC: C34.1, U3.2 (VO)
+1V8_SYS: C49.2, C414.1, JP14.2 (B), R41.2, R61.2, R326.2, TP7.1, U5.6 (VCCB)
+1V8_XADC: C48.1, C53.1, R55.2, U2.7 (VOUT5)
+1V35_SYS: JP16.2 (B), R66.2, TP6.1
+2V0_SYS_SOC: C36.1, R37.1, U4.2 (VO)
+2V5_PL_VCC0: C45.1, IC2.5 (OUT), TP8.1
+3V3EXT: C37.1, U2.8 (PVIN5)
+3V3MCU: C409.1, C410.1, C411.1, R59.1, U52.4 (VS), U53.4 (VS), U53.7 (A0), U54.4 (VS)
+3V3_SYS: C21.1, C22.1, C27.1, C28.1, C31.1, C32.1, C40.2, C412.1, FB1.2, IC1.5 (VCC), JP15.2 (B), R31.2, R62.1, R65.2, R70.1, R322.2, TP2.1, U3.3 (VI), U4.3 (VI), U5.1 (VCCA)
+5VEXT: C60.1, R68.2, R75.2, R76.1, R79.2, U6.9 (IN), U6.10 (IN), U6.11 (IN), U6.12 (IN), U6.13 (IN)
COMP1: C30.2, R35.2, U2.39 (COMP1)
COMP2: R36.2, U2.22 (COMP2)
COMP3: R32.2, U2.46 (COMP3)
COMP4: R33.2, U2.15 (COMP4)
GND: C21.2, C22.2, C23.1, C24.1, C25.2, C26.1, C27.2, C28.2, C29.1, C30.1, C31.2, C32.2, C33.2, C34.2, C35.2, C36.2, C37.2, C38.2, C39.2, C40.1, C45.2, C46.2, C47.2, C48.2, C49.1, C50.1, C51.2, C52.2, C53.2, C54.2, C55.2, C56.2, C57.2, C58.1, C59.2, C60.2, C61.2, C62.2, C63.2, C64.2, C65.2, C409.2, C410.2, C411.2, D12.1 (K), D13.1 (K), D15.1 (K), IC1.3 (GND), IC2.2 (GND), Q5.1 (S1), Q5.3 (S2), Q6.2 (S), Q7.2 (S), Q8.2 (S), R38.2, R40.2, R42.2, R43.1, R44.1, R47.1, R48.1, R49.1, R50.2, R51.1, R52.1, R56.1, R60.2, R67.2, R69.2, R74.1, R77.1, R78.1, TP9.1, TP10.1, TP11.1, U2.2 (PGND3), U2.11 (PGND4), U2.13 (GND), U2.17 (GND), U2.18 (GND), U2.19 (GND), U2.30 (PGND), U2.38 (SS12), U2.47 (SS34), U2.HTAB (EPAD), U3.1 (GND), U5.2 (GND), U6.1 (DEVSLP), U6.16 (GND), U6.21 (EPAD), U52.3 (GND), U52.7 (A0), U52.8 (A1), U53.3 (GND), U53.8 (A1), U54.3 (GND), U54.8 (A1)
I2C_SENSORS.I2C_SCL: U52.5 (SCL), U53.5 (SCL), U54.5 (SCL)
I2C_SENSORS.I2C_SDA: U52.6 (SDA), U53.6 (SDA), U54.6 (SDA), U54.7 (A0)
ILIM: R72.2, R74.2, U6.17 (ILIM)
unnamed: C23.2, R32.1
unnamed: C24.2, R33.1
unnamed: C25.1, U2.42 (VDD)
unnamed: C26.2, R36.1
unnamed: C29.2, R35.1
unnamed: C33.1, D10.2 (A), IC1.2 (A), R34.1
unnamed: C35.1, R41.1, R42.1, U2.5 (EN5), U2.37 (EN1), U2.48 (EN3)
unnamed: C39.1, FB1.1, IC2.1 (IN), IC2.3 (EN)
unnamed: C41.1, L4.1, Q5.7 (D1), Q5.8 (D1), U2.26 (SW2), U2.27 (SW2)
unnamed: C41.2, U2.28 (BST2)
unnamed: C42.1, L1.1, U2.3 (SW3)
unnamed: C42.2, U2.1 (BST3)
unnamed: C43.1, L2.1, U2.10 (SW4)
unnamed: C43.2, U2.12 (BST4)
unnamed: C44.1, U2.32 (BST1)
unnamed: C44.2, L3.1, Q5.5 (D2), Q5.6 (D2), U2.33 (SW1), U2.34 (SW1)
unnamed: C46.1, C51.1, JP16.1 (A), L1.2, R53.2, R64.1, R66.1
unnamed: C58.2, R75.1, R77.2, U6.15 (OVP)
unnamed: C59.1, U6.18 (DVDT)
unnamed: D11.1 (K), Q6.3 (D)
unnamed: D11.2 (A), R62.2
unnamed: D12.2 (A), R63.2
unnamed: D13.2 (A), R64.2
unnamed: D14.1 (K), Q7.3 (D)
unnamed: D14.2 (A), R70.2
unnamed: D15.2 (A), R71.2
unnamed: Q5.2 (G1), R51.2, U2.29 (DL2)
unnamed: Q5.4 (G2), R50.1, U2.31 (DL1)
unnamed: Q8.1 (G), R68.1, R69.1
unnamed: Q8.3 (D), R72.1
unnamed: R37.2, R38.1, U4.1 (ADJ)
unnamed: R43.2, U2.41 (RT)
unnamed: R44.2, R45.2, U2.43 (SYNC/MODE)
unnamed: R46.2, U5.3 (A)
unnamed: R47.2, R53.1, U2.45 (FB3)
unnamed: R48.2, R54.1, U2.16 (FB4)
unnamed: R49.2, R55.1, U2.6 (FB5)
unnamed: R52.2, R58.1, U2.40 (FB1)
unnamed: R56.2, R57.1, U2.21 (FB2)
unnamed: R59.2, U5.5 (DIR)
unnamed: R76.2, U6.20 (*FLT)
unnamed: R78.2, U6.19 (IMON)
unnamed: R79.1, U6.2 (PGOOD)
unnamed: R321.1, U52.1 (IN+)
unnamed: R322.1, U52.2 (IN-)
unnamed: R323.1, U53.1 (IN+)
unnamed: R324.1, U53.2 (IN-)
unnamed: R325.1, U54.1 (IN+)
unnamed: R326.1, U54.2 (IN-)
PGOOD_EDGE: IC1.4 (Y), R46.1
PMIC_EN2: R39.2, R40.1, U2.23 (EN2)
PVIN: C61.1, C62.1, C63.1, C64.1, C65.1, R39.1, U2.4 (PVIN3), U2.9 (PVIN4), U2.24 (PVIN2), U2.25 (PVIN2), U2.35 (PVIN1), U2.36 (PVIN1), U6.4 (OUT), U6.5 (OUT), U6.6 (OUT), U6.7 (OUT), U6.8 (OUT)
PWRGD: D10.1 (K), R31.1, R34.2, U2.20 (PWRGD)
SENSE_SOC1V8+: C47.1, C52.1, C414.2, JP14.1 (A), L2.2, R54.2, R61.1, R325.2
SENSE_SOC1V+: C55.1, C57.1, C413.2, JP17.1 (A), L4.2, R57.2, R71.1, R73.1, R323.2
SENSE_SOC3V+: C54.1, C56.1, C412.2, JP15.1 (A), L3.2, R58.2, R63.1, R65.1, R321.2
VREG: C38.1, R45.1, U2.44 (VREG)
ZYNQ_PWCTL_EN: Q6.1 (G), R60.1, TP3.1, U6.14 (EN)
ZYNQ_PWCTL_PGOOD: C50.2, Q7.1 (G), R67.1, TP5.1, U5.4 (B)

Notes on the sheet:
XADC is used for internal monitoring only UG480 Fig 1-2
0.6A -2A MAX
PMIC_EN2 starts 1V0 (first pwr bus)
I2C addr: 1000000
ADP5052 SYNC/MODE high -> forced PWM (FPWM) mode. low -> automatic PWM/PSM mode.
2.5A
I2C addr: 1000001
1.2A
I2C to current sensors
SOC PWR +3V3_SYS is started (last in seq) [OUT] +1V8 signal
2.1A
ADP5052 PWR Sequence: 1. +1V0_SYS 2. +1V8_SYS 3. +3V3_SYS; +1V35_SYS; +1V8_XADC
I2C addr: 1000010
starts the SOC power when H [IN] TPS25940 V(ENF) > 1.01V
ADP5052 outputs PWRGD when the SW1 / +3V3_SYS is up (last in seq)
