electrodyssey/NASR-M/soc_power_bypass.kicad_sch

## KiCad design soc_power_bypass.kicad_sch (2025-10-22)

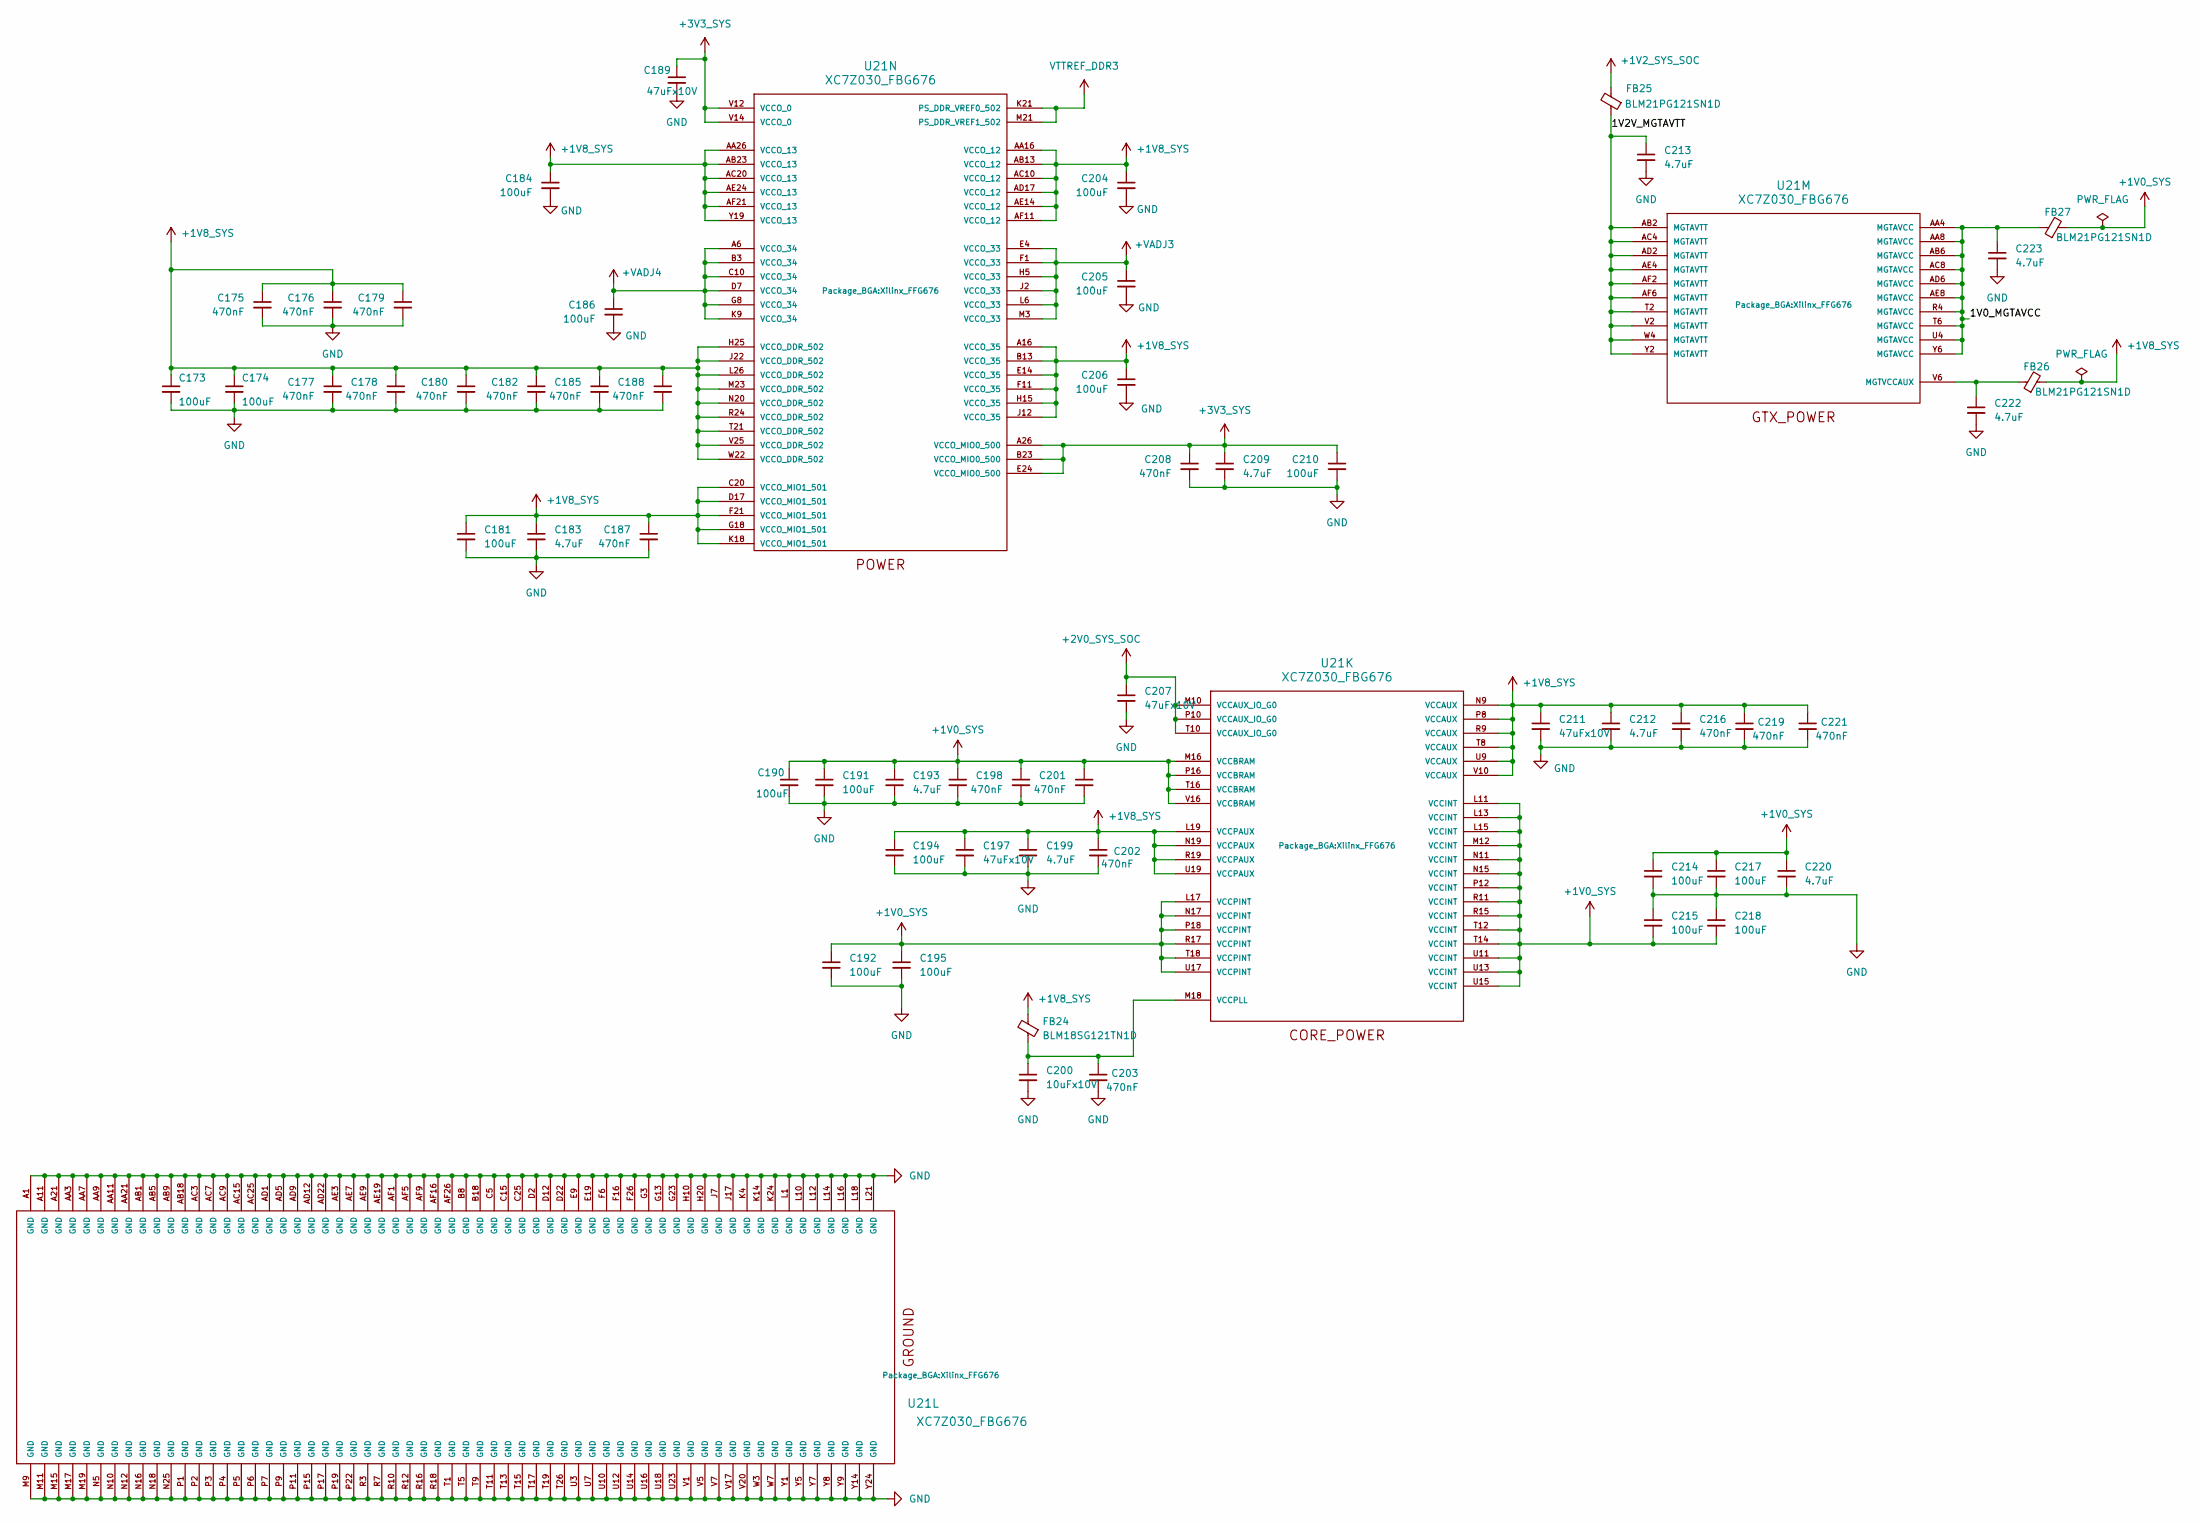
[picture p62: schematic soc_power_bypass.kicad_sch]

Parts:
C173, C174, C181, C184, C186, C190, C191, C192, C194, C195, C204, C205, C206, C210, C214, C215, C217, C218: 100uF; C_1210_3225Metric; Part GRM32EC70J107ME15L; JLCPCB Part # C393041
C175, C176, C177, C178, C179, C180, C182, C185, C187, C188, C196, C198, C201, C202, C203, C208, C216, C219, C221: 470nF; C_0201_0603Metric; Part CL03A474KQ3NNNC; JLCPCB Part # C318543
C183, C193, C199, C209, C212, C213, C220, C222, C223: 4.7uF; C_0402_1005Metric; Part CL05A475KP5NRNC; JLCPCB Part # C368809
C189, C197, C207, C211: 47uFx10V; C_1210_3225Metric; Part GRM32ER71A476KE15L; JLCPCB Part # C84494
C200: 10uFx10V; C_0805_2012Metric; Part CL21A106KPFNNNE; JLCPCB Part # C17024
FB24: BLM18SG121TN1D; L_0603_1608Metric; Part BLM18SG121TN1D; JLCPCB Part # C113030
FB25, FB26, FB27: BLM21PG121SN1D; L_0805_2012Metric; Part BLM21PG121SN1D; JLCPCB Part # C79382
U21: XC7Z030_FBG676; Xilinx_FFG676; JLCPCB Part # C966962

Connections:
1V0_MGTAVCC: C223.1, FB27.1, U21.AA4 (MGTAVCC), U21.AA8 (MGTAVCC), U21.AB6 (MGTAVCC), U21.AC8 (MGTAVCC), U21.AD6 (MGTAVCC), U21.AE8 (MGTAVCC), U21.R4 (MGTAVCC), U21.T6 (MGTAVCC), U21.U4 (MGTAVCC), U21.Y6 (MGTAVCC)
1V2V_MGTAVTT: C213.1, FB25.1, U21.AB2 (MGTAVTT), U21.AC4 (MGTAVTT), U21.AD2 (MGTAVTT), U21.AE4 (MGTAVTT), U21.AF2 (MGTAVTT), U21.AF6 (MGTAVTT), U21.T2 (MGTAVTT), U21.V2 (MGTAVTT), U21.W4 (MGTAVTT), U21.Y2 (MGTAVTT)
+1V0_SYS: C190.1, C191.1, C192.1, C193.1, C195.1, C196.1, C198.1, C201.1, C214.1, C215.2, C217.1, C218.2, C220.1, FB27.2, U21.L11 (VCCINT), U21.L13 (VCCINT), U21.L15 (VCCINT), U21.L17 (VCCPINT), U21.M12 (VCCINT), U21.M16 (VCCBRAM), U21.N11 (VCCINT), U21.N15 (VCCINT), U21.N17 (VCCPINT), U21.P12 (VCCINT), U21.P16 (VCCBRAM), U21.P18 (VCCPINT), U21.R11 (VCCINT), U21.R15 (VCCINT), U21.R17 (VCCPINT), U21.T12 (VCCINT), U21.T14 (VCCINT), U21.T16 (VCCBRAM), U21.T18 (VCCPINT), U21.U11 (VCCINT), U21.U13 (VCCINT), U21.U15 (VCCINT), U21.U17 (VCCPINT), U21.V16 (VCCBRAM)
+1V2_SYS_SOC: FB25.2
+1V8_SYS: C173.1, C174.1, C175.1, C176.1, C177.1, C178.1, C179.1, C180.1, C181.1, C182.1, C183.1, C184.1, C185.1, C187.1, C188.1, C194.1, C197.1, C199.1, C202.1, C204.1, C206.1, C211.1, C212.1, C216.1, C219.1, C221.1, FB24.2, FB26.2, U21.A16 (VCCO_35), U21.AA16 (VCCO_12), U21.AA26 (VCCO_13), U21.AB13 (VCCO_12), U21.AB23 (VCCO_13), U21.AC10 (VCCO_12), U21.AC20 (VCCO_13), U21.AD17 (VCCO_12), U21.AE14 (VCCO_12), U21.AE24 (VCCO_13), U21.AF11 (VCCO_12), U21.AF21 (VCCO_13), U21.B13 (VCCO_35), U21.C20 (VCCO_MIO1_501), U21.D17 (VCCO_MIO1_501), U21.E14 (VCCO_35), U21.F11 (VCCO_35), U21.F21 (VCCO_MIO1_501), U21.G18 (VCCO_MIO1_501), U21.H15 (VCCO_35), U21.H25 (VCCO_DDR_502), U21.J12 (VCCO_35), U21.J22 (VCCO_DDR_502), U21.K18 (VCCO_MIO1_501), U21.L19 (VCCPAUX), U21.L26 (VCCO_DDR_502), U21.M23 (VCCO_DDR_502), U21.N9 (VCCAUX), U21.N19 (VCCPAUX), U21.N20 (VCCO_DDR_502), U21.P8 (VCCAUX), U21.R9 (VCCAUX), U21.R19 (VCCPAUX), U21.R24 (VCCO_DDR_502), U21.T8 (VCCAUX), U21.T21 (VCCO_DDR_502), U21.U9 (VCCAUX), U21.U19 (VCCPAUX), U21.V10 (VCCAUX), U21.V25 (VCCO_DDR_502), U21.W22 (VCCO_DDR_502), U21.Y19 (VCCO_13)
+2V0_SYS_SOC: C207.1, U21.M10 (VCCAUX_IO_G0), U21.P10 (VCCAUX_IO_G0), U21.T10 (VCCAUX_IO_G0)
+3V3_SYS: C189.1, C208.1, C209.1, C210.1, U21.A26 (VCCO_MIO0_500), U21.B23 (VCCO_MIO0_500), U21.E24 (VCCO_MIO0_500), U21.V12 (VCCO_0), U21.V14 (VCCO_0)
+VADJ3: C205.1, U21.E4 (VCCO_33), U21.F1 (VCCO_33), U21.H5 (VCCO_33), U21.J2 (VCCO_33), U21.L6 (VCCO_33), U21.M3 (VCCO_33)
+VADJ4: C186.1, U21.A6 (VCCO_34), U21.B3 (VCCO_34), U21.C10 (VCCO_34), U21.D7 (VCCO_34), U21.G8 (VCCO_34), U21.K9 (VCCO_34)
GND: C173.2, C174.2, C175.2, C176.2, C177.2, C178.2, C179.2, C180.2, C181.2, C182.2, C183.2, C184.2, C185.2, C186.2, C187.2, C188.2, C189.2, C190.2, C191.2, C192.2, C193.2, C194.2, C195.2, C196.2, C197.2, C198.2, C199.2, C200.2, C201.2, C202.2, C203.2, C204.2, C205.2, C206.2, C207.2, C208.2, C209.2, C210.2, C211.2, C212.2, C213.2, C214.2, C215.1, C216.2, C217.2, C218.1, C219.2, C220.2, C221.2, C222.2, C223.2, U21.A1 (GND), U21.A11 (GND), U21.A21 (GND), U21.AA3 (GND), U21.AA7 (GND), U21.AA9 (GND), U21.AA11 (GND), U21.AA21 (GND), U21.AB1 (GND), U21.AB5 (GND), U21.AB9 (GND), U21.AB18 (GND), U21.AC3 (GND), U21.AC7 (GND), U21.AC9 (GND), U21.AC15 (GND), U21.AC25 (GND), U21.AD1 (GND), U21.AD5 (GND), U21.AD9 (GND), U21.AD12 (GND), U21.AD22 (GND), U21.AE3 (GND), U21.AE7 (GND), U21.AE9 (GND), U21.AE19 (GND), U21.AF1 (GND), U21.AF5 (GND), U21.AF9 (GND), U21.AF16 (GND), U21.AF26 (GND), U21.B8 (GND), U21.B18 (GND), U21.C5 (GND), U21.C15 (GND), U21.C25 (GND), U21.D2 (GND), U21.D12 (GND), U21.D22 (GND), U21.E9 (GND), U21.E19 (GND), U21.F6 (GND), U21.F16 (GND), U21.F26 (GND), U21.G3 (GND), U21.G13 (GND), U21.G23 (GND), U21.H10 (GND), U21.H20 (GND), U21.J7 (GND), U21.J17 (GND), U21.K4 (GND), U21.K14 (GND), U21.K24 (GND), U21.L1 (GND), U21.L10 (GND), U21.L12 (GND), U21.L14 (GND), U21.L16 (GND), U21.L18 (GND), U21.L21 (GND), U21.M9 (GND), U21.M11 (GND), U21.M15 (GND), U21.M17 (GND), U21.M19 (GND), U21.N5 (GND), U21.N10 (GND), U21.N12 (GND), U21.N16 (GND), U21.N18 (GND), U21.N25 (GND), U21.P1 (GND), U21.P2 (GND), U21.P3 (GND), U21.P4 (GND), U21.P5 (GND), U21.P6 (GND), U21.P7 (GND), U21.P9 (GND), U21.P11 (GND), U21.P15 (GND), U21.P17 (GND), U21.P19 (GND), U21.P22 (GND), U21.R3 (GND), U21.R7 (GND), U21.R10 (GND), U21.R12 (GND), U21.R16 (GND), U21.R18 (GND), U21.T1 (GND), U21.T5 (GND), U21.T9 (GND), U21.T11 (GND), U21.T13 (GND), U21.T15 (GND), U21.T17 (GND), U21.T19 (GND), U21.T26 (GND), U21.U3 (GND), U21.U7 (GND), U21.U10 (GND), U21.U12 (GND), U21.U14 (GND), U21.U16 (GND), U21.U18 (GND), U21.U23 (GND), U21.V1 (GND), U21.V5 (GND), U21.V7 (GND), U21.V17 (GND), U21.V20 (GND), U21.W3 (GND), U21.W7 (GND), U21.Y1 (GND), U21.Y5 (GND), U21.Y7 (GND), U21.Y8 (GND), U21.Y9 (GND), U21.Y14 (GND), U21.Y24 (GND)
unnamed: C200.1, C203.1, FB24.1, U21.M18 (VCCPLL)
unnamed: C222.1, FB26.1, U21.V6 (MGTVCCAUX)
VTTREF_DDR3: U21.K21 (PS_DDR_VREF0_502), U21.M21 (PS_DDR_VREF1_502)
