electrodyssey/NASR-M/syzygy12.kicad_sch

## KiCad design syzygy12.kicad_sch (2025-09-22)

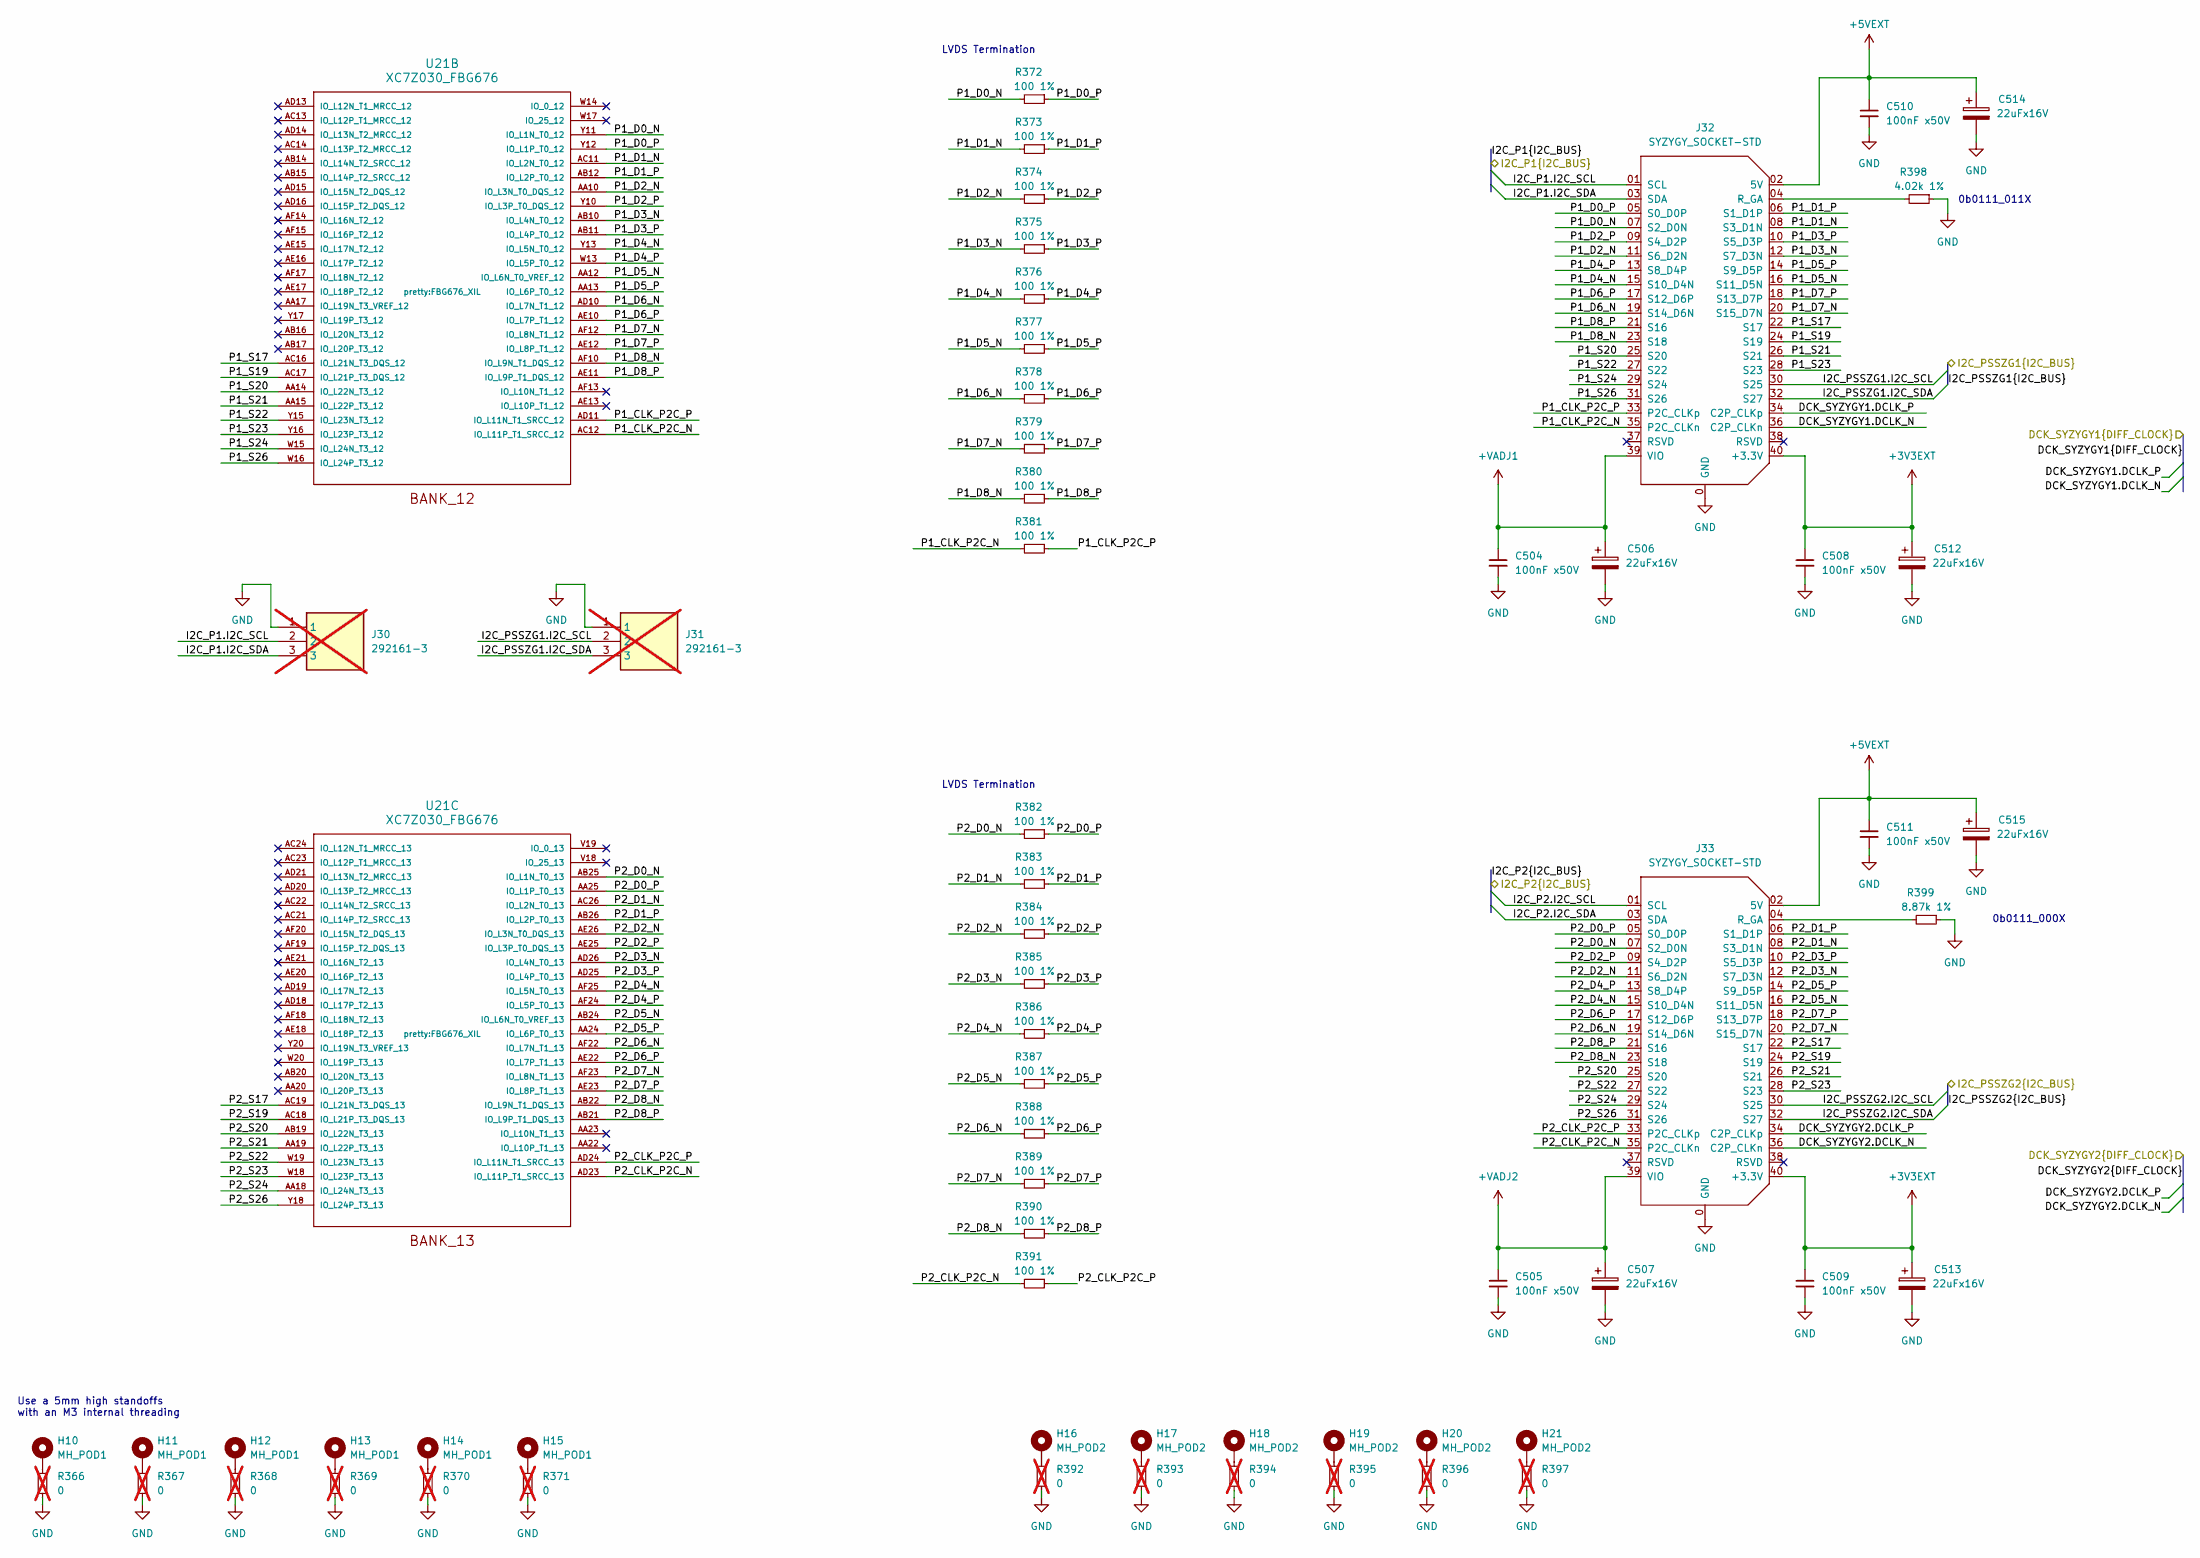
[picture p63: schematic syzygy12.kicad_sch]

Parts:
C504, C505, C508, C509, C510, C511: 100nF x50V; C_0805_2012Metric; JLCPCB Part # C141172
C506, C507, C512, C513, C514, C515: 22uFx16V; CP_EIA-6032-15_Kemet-U; Part T494C226M016AT; JLCPCB Part # C1952930
H10, H11, H12, H13, H14, H15: MH_POD1; MountingHole_3.2mm_M3_Pad_Via
H16, H17, H18, H19, H20, H21: MH_POD2; MountingHole_3.2mm_M3_Pad_Via
J30, J31: 292161-3; SHDR3W60P0X200_1X3_780X360X680P; Mouser Part Number 571-292161-3; not fitted
J32, J33: SYZYGY_SOCKET-STD; SAMTEC_QSE-020-01-F-D-A; Manufacturer_PN QSE-020-01-F-D-A
R366, R367, R368, R369, R370, R371, R392, R393, R394, R395, R396, R397: 0; R_0805_2012Metric; JLCPCB Part # C2936632; not fitted
R372, R373, R374, R375, R376, R377, R378, R379, R380, R381, R382, R383, R384, R385, R386, R387, R388, R389, R390, R391: 100 1%; R_0402_1005Metric; Part C153111; JLCPCB Part # RM04FTN1000
R398: 4.02k 1%; R_0603_1608Metric; Part TC0350B4021T5F; JLCPCB Part # C2989572
R399: 8.87k 1%; R_0603_1608Metric; Part RS-03K8871FT; JLCPCB Part # C304791
U21: XC7Z030_FBG676; FBG676_XIL

Connections:
+3V3EXT: C508.1, C509.1, C512.1, C513.1, J32.40 (+3.3V), J33.40 (+3.3V)
+5VEXT: C510.1, C511.1, C514.1, C515.1, J32.02 (5V), J33.02 (5V)
+VADJ1: C504.1, C506.1, J32.39 (VIO)
+VADJ2: C505.1, C507.1, J33.39 (VIO)
DCK_SYZYGY1.DCLK_N: J32.36 (C2P_CLKn)
DCK_SYZYGY1.DCLK_P: J32.34 (C2P_CLKp)
DCK_SYZYGY2.DCLK_N: J33.36 (C2P_CLKn)
DCK_SYZYGY2.DCLK_P: J33.34 (C2P_CLKp)
GND: C504.2, C505.2, C506.2, C507.2, C508.2, C509.2, C510.2, C511.2, C512.2, C513.2, C514.2, C515.2, J30.1, J31.1, J32.0 (GND), J33.0 (GND), R366.1, R367.1, R368.1, R369.1, R370.1, R371.1, R392.1, R393.1, R394.1, R395.1, R396.1, R397.1, R398.1, R399.1
I2C_P1.I2C_SCL: J30.2, J32.01 (SCL)
I2C_P1.I2C_SDA: J30.3, J32.03 (SDA)
I2C_P2.I2C_SCL: J33.01 (SCL)
I2C_P2.I2C_SDA: J33.03 (SDA)
I2C_PSSZG1.I2C_SCL: J31.2, J32.30 (S25)
I2C_PSSZG1.I2C_SDA: J31.3, J32.32 (S27)
I2C_PSSZG2.I2C_SCL: J33.30 (S25)
I2C_PSSZG2.I2C_SDA: J33.32 (S27)
unnamed: H10.1, R366.2
unnamed: H11.1, R367.2
unnamed: H12.1, R368.2
unnamed: H13.1, R369.2
unnamed: H14.1, R370.2
unnamed: H15.1, R371.2
unnamed: H16.1, R392.2
unnamed: H17.1, R393.2
unnamed: H18.1, R394.2
unnamed: H19.1, R395.2
unnamed: H20.1, R396.2
unnamed: H21.1, R397.2
unnamed: J32.04 (R_GA), R398.2
unnamed: J33.04 (R_GA), R399.2
P1_CLK_P2C_N: J32.35 (P2C_CLKn), R381.2, U21.AC12 (IO_L11P_T1_SRCC_12)
P1_CLK_P2C_P: J32.33 (P2C_CLKp), R381.1, U21.AD11 (IO_L11N_T1_SRCC_12)
P1_D0_N: J32.07 (S2_D0N), R372.2, U21.Y11 (IO_L1N_T0_12)
P1_D0_P: J32.05 (S0_D0P), R372.1, U21.Y12 (IO_L1P_T0_12)
P1_D1_N: J32.08 (S3_D1N), R373.2, U21.AC11 (IO_L2N_T0_12)
P1_D1_P: J32.06 (S1_D1P), R373.1, U21.AB12 (IO_L2P_T0_12)
P1_D2_N: J32.11 (S6_D2N), R374.2, U21.AA10 (IO_L3N_T0_DQS_12)
P1_D2_P: J32.09 (S4_D2P), R374.1, U21.Y10 (IO_L3P_T0_DQS_12)
P1_D3_N: J32.12 (S7_D3N), R375.2, U21.AB10 (IO_L4N_T0_12)
P1_D3_P: J32.10 (S5_D3P), R375.1, U21.AB11 (IO_L4P_T0_12)
P1_D4_N: J32.15 (S10_D4N), R376.2, U21.Y13 (IO_L5N_T0_12)
P1_D4_P: J32.13 (S8_D4P), R376.1, U21.W13 (IO_L5P_T0_12)
P1_D5_N: J32.16 (S11_D5N), R377.2, U21.AA12 (IO_L6N_T0_VREF_12)
P1_D5_P: J32.14 (S9_D5P), R377.1, U21.AA13 (IO_L6P_T0_12)
P1_D6_N: J32.19 (S14_D6N), R378.2, U21.AD10 (IO_L7N_T1_12)
P1_D6_P: J32.17 (S12_D6P), R378.1, U21.AE10 (IO_L7P_T1_12)
P1_D7_N: J32.20 (S15_D7N), R379.2, U21.AF12 (IO_L8N_T1_12)
P1_D7_P: J32.18 (S13_D7P), R379.1, U21.AE12 (IO_L8P_T1_12)
P1_D8_N: J32.23 (S18), R380.2, U21.AF10 (IO_L9N_T1_DQS_12)
P1_D8_P: J32.21 (S16), R380.1, U21.AE11 (IO_L9P_T1_DQS_12)
P1_S17: J32.22 (S17), U21.AC16 (IO_L21N_T3_DQS_12)
P1_S19: J32.24 (S19), U21.AC17 (IO_L21P_T3_DQS_12)
P1_S20: J32.25 (S20), U21.AA14 (IO_L22N_T3_12)
P1_S21: J32.26 (S21), U21.AA15 (IO_L22P_T3_12)
P1_S22: J32.27 (S22), U21.Y15 (IO_L23N_T3_12)
P1_S23: J32.28 (S23), U21.Y16 (IO_L23P_T3_12)
P1_S24: J32.29 (S24), U21.W15 (IO_L24N_T3_12)
P1_S26: J32.31 (S26), U21.W16 (IO_L24P_T3_12)
P2_CLK_P2C_N: J33.35 (P2C_CLKn), R391.2, U21.AD23 (IO_L11P_T1_SRCC_13)
P2_CLK_P2C_P: J33.33 (P2C_CLKp), R391.1, U21.AD24 (IO_L11N_T1_SRCC_13)
P2_D0_N: J33.07 (S2_D0N), R382.2, U21.AB25 (IO_L1N_T0_13)
P2_D0_P: J33.05 (S0_D0P), R382.1, U21.AA25 (IO_L1P_T0_13)
P2_D1_N: J33.08 (S3_D1N), R383.2, U21.AC26 (IO_L2N_T0_13)
P2_D1_P: J33.06 (S1_D1P), R383.1, U21.AB26 (IO_L2P_T0_13)
P2_D2_N: J33.11 (S6_D2N), R384.2, U21.AE26 (IO_L3N_T0_DQS_13)
P2_D2_P: J33.09 (S4_D2P), R384.1, U21.AE25 (IO_L3P_T0_DQS_13)
P2_D3_N: J33.12 (S7_D3N), R385.2, U21.AD26 (IO_L4N_T0_13)
P2_D3_P: J33.10 (S5_D3P), R385.1, U21.AD25 (IO_L4P_T0_13)
P2_D4_N: J33.15 (S10_D4N), R386.2, U21.AF25 (IO_L5N_T0_13)
P2_D4_P: J33.13 (S8_D4P), R386.1, U21.AF24 (IO_L5P_T0_13)
P2_D5_N: J33.16 (S11_D5N), R387.2, U21.AB24 (IO_L6N_T0_VREF_13)
P2_D5_P: J33.14 (S9_D5P), R387.1, U21.AA24 (IO_L6P_T0_13)
P2_D6_N: J33.19 (S14_D6N), R388.2, U21.AF22 (IO_L7N_T1_13)
P2_D6_P: J33.17 (S12_D6P), R388.1, U21.AE22 (IO_L7P_T1_13)
P2_D7_N: J33.20 (S15_D7N), R389.2, U21.AF23 (IO_L8N_T1_13)
P2_D7_P: J33.18 (S13_D7P), R389.1, U21.AE23 (IO_L8P_T1_13)
P2_D8_N: J33.23 (S18), R390.2, U21.AB22 (IO_L9N_T1_DQS_13)
P2_D8_P: J33.21 (S16), R390.1, U21.AB21 (IO_L9P_T1_DQS_13)
P2_S17: J33.22 (S17), U21.AC19 (IO_L21N_T3_DQS_13)
P2_S19: J33.24 (S19), U21.AC18 (IO_L21P_T3_DQS_13)
P2_S20: J33.25 (S20), U21.AB19 (IO_L22N_T3_13)
P2_S21: J33.26 (S21), U21.AA19 (IO_L22P_T3_13)
P2_S22: J33.27 (S22), U21.W19 (IO_L23N_T3_13)
P2_S23: J33.28 (S23), U21.W18 (IO_L23P_T3_13)
P2_S24: J33.29 (S24), U21.AA18 (IO_L24N_T3_13)
P2_S26: J33.31 (S26), U21.Y18 (IO_L24P_T3_13)

Notes on the sheet:
LVDS Termination
Use a 5mm high standoffs with an M3 internal threading
0b0111_011X
0b0111_000X
