electrodyssey/NASR-M/syzygy34.kicad_sch

## KiCad design syzygy34.kicad_sch (2025-10-22)

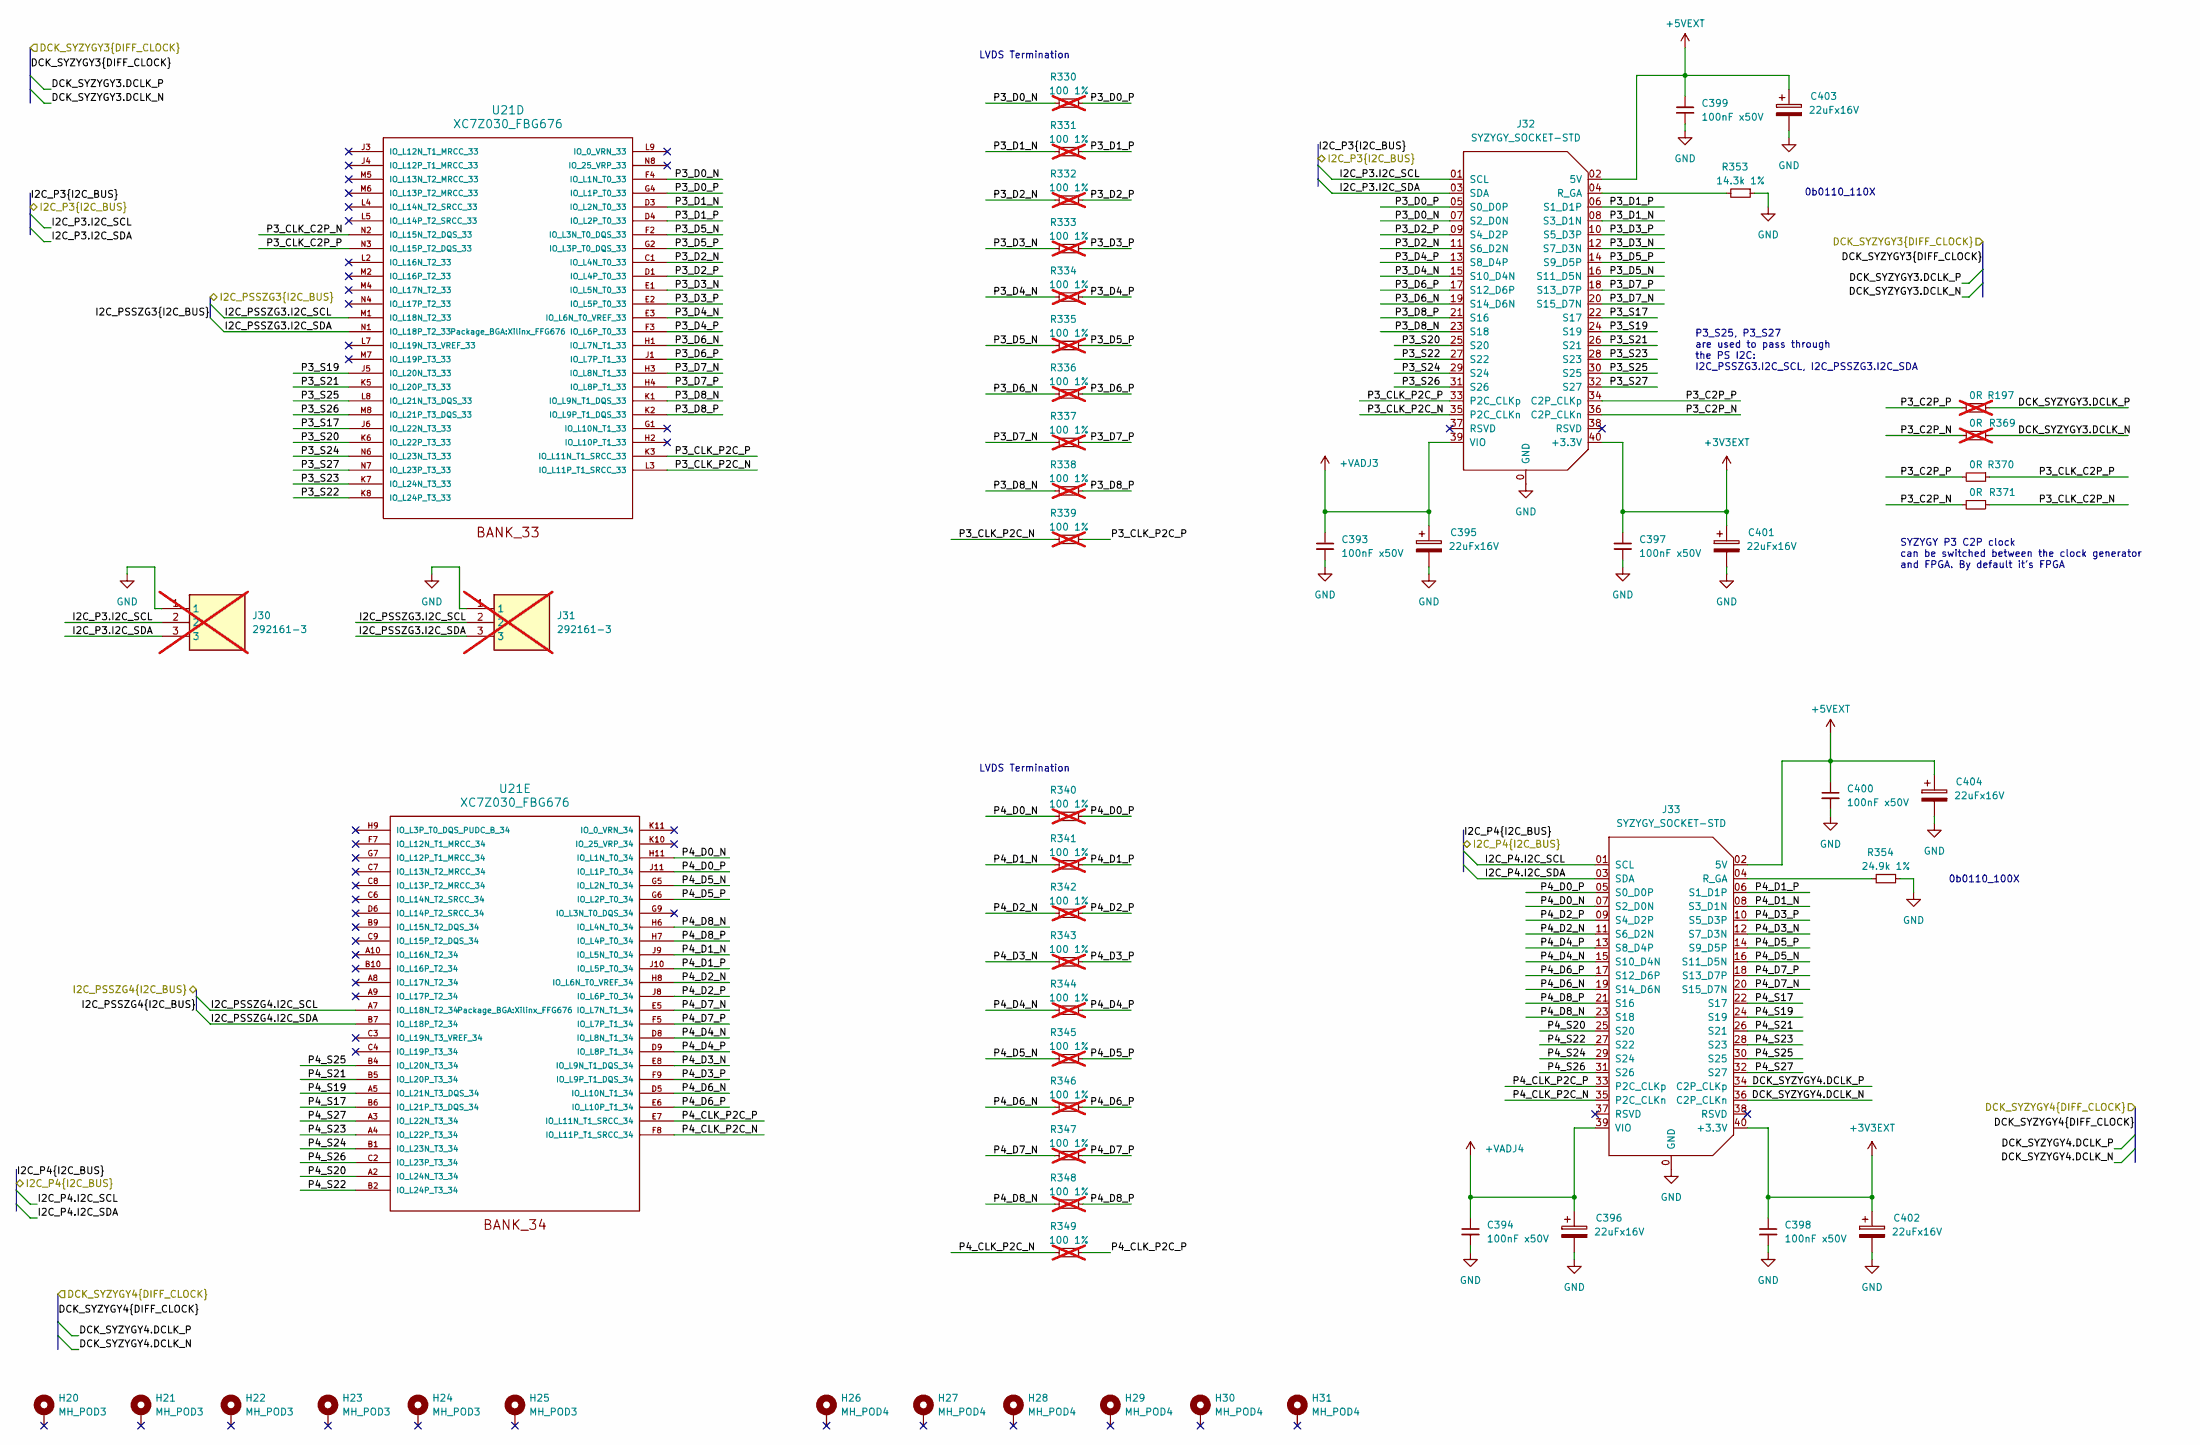
[picture p64: schematic syzygy34.kicad_sch]

Parts:
C393, C394, C397, C398, C399, C400: 100nF x50V; C_0805_2012Metric; JLCPCB Part # C141172
C395, C396, C401, C402, C403, C404: 22uFx16V; CP_EIA-6032-15_Kemet-U; Part TR3C226K016C0350; JLCPCB Part # C1954274
H20, H21, H22, H23, H24, H25: MH_POD3; MountingHole_4.3mm_M4_Pad_TopBottom
H26, H27, H28, H29, H30, H31: MH_POD4; MountingHole_4.3mm_M4_Pad_TopBottom
J30, J31: 292161-3; SHDR3W60P0X200_1X3_780X360X680P; Mouser Part Number 571-292161-3; not fitted
J32, J33: SYZYGY_SOCKET-STD; SAMTEC_QSE-020-01-F-D-A; Manufacturer_PN QSE-020-01-F-D-A; JLCPCB Part # C3643352
R197, R369: 0R; R_0402_1005Metric; Part 0402WGF0000TCE; JLCPCB Part # C17168; not fitted
R330, R331, R332, R333, R334, R335, R336, R337, R338, R339, R340, R341, R342, R343, R344, R345, R346, R347, R348, R349: 100 1%; R_0201_0603Metric; Part WR02X1000FAL; JLCPCB Part # C180289; not fitted
R353: 14.3k 1%; R_0603_1608Metric; Part RS-03K1432FT; JLCPCB Part # C304702
R354: 24.9k 1%; R_0603_1608Metric; Part TD03G2492BT; JLCPCB Part # C667077
R370, R371: 0R; R_0402_1005Metric; Part 0402WGF0000TCE; JLCPCB Part # C17168
U21: XC7Z030_FBG676; Xilinx_FFG676; JLCPCB Part # C966962

Connections:
+3V3EXT: C397.1, C398.1, C401.1, C402.1, J32.40 (+3.3V), J33.40 (+3.3V)
+5VEXT: C399.1, C400.1, C403.1, C404.1, J32.02 (5V), J33.02 (5V)
+VADJ3: C393.1, C395.1, J32.39 (VIO)
+VADJ4: C394.1, C396.1, J33.39 (VIO)
DCK_SYZYGY3.DCLK_N: R369.1
DCK_SYZYGY3.DCLK_P: R197.1
DCK_SYZYGY4.DCLK_N: J33.36 (C2P_CLKn)
DCK_SYZYGY4.DCLK_P: J33.34 (C2P_CLKp)
GND: C393.2, C394.2, C395.2, C396.2, C397.2, C398.2, C399.2, C400.2, C401.2, C402.2, C403.2, C404.2, J30.1, J31.1, J32.0 (GND), J33.0 (GND), R353.1, R354.1
I2C_P3.I2C_SCL: J30.2, J32.01 (SCL)
I2C_P3.I2C_SDA: J30.3, J32.03 (SDA)
I2C_P4.I2C_SCL: J33.01 (SCL)
I2C_P4.I2C_SDA: J33.03 (SDA)
I2C_PSSZG3.I2C_SCL: J31.2, U21.M1 (IO_L18N_T2_33)
I2C_PSSZG3.I2C_SDA: J31.3, U21.N1 (IO_L18P_T2_33)
I2C_PSSZG4.I2C_SCL: U21.A7 (IO_L18N_T2_34)
I2C_PSSZG4.I2C_SDA: U21.B7 (IO_L18P_T2_34)
unnamed: J32.04 (R_GA), R353.2
unnamed: J33.04 (R_GA), R354.2
P3_C2P_N: J32.36 (C2P_CLKn), R369.2, R371.2
P3_C2P_P: J32.34 (C2P_CLKp), R197.2, R370.2
P3_CLK_C2P_N: R371.1, U21.N2 (IO_L15N_T2_DQS_33)
P3_CLK_C2P_P: R370.1, U21.N3 (IO_L15P_T2_DQS_33)
P3_CLK_P2C_N: J32.35 (P2C_CLKn), R339.2, U21.L3 (IO_L11P_T1_SRCC_33)
P3_CLK_P2C_P: J32.33 (P2C_CLKp), R339.1, U21.K3 (IO_L11N_T1_SRCC_33)
P3_D0_N: J32.07 (S2_D0N), R330.2, U21.F4 (IO_L1N_T0_33)
P3_D0_P: J32.05 (S0_D0P), R330.1, U21.G4 (IO_L1P_T0_33)
P3_D1_N: J32.08 (S3_D1N), R331.2, U21.D3 (IO_L2N_T0_33)
P3_D1_P: J32.06 (S1_D1P), R331.1, U21.D4 (IO_L2P_T0_33)
P3_D2_N: J32.11 (S6_D2N), R332.2, U21.C1 (IO_L4N_T0_33)
P3_D2_P: J32.09 (S4_D2P), R332.1, U21.D1 (IO_L4P_T0_33)
P3_D3_N: J32.12 (S7_D3N), R333.2, U21.E1 (IO_L5N_T0_33)
P3_D3_P: J32.10 (S5_D3P), R333.1, U21.E2 (IO_L5P_T0_33)
P3_D4_N: J32.15 (S10_D4N), R334.2, U21.E3 (IO_L6N_T0_VREF_33)
P3_D4_P: J32.13 (S8_D4P), R334.1, U21.F3 (IO_L6P_T0_33)
P3_D5_N: J32.16 (S11_D5N), R335.2, U21.F2 (IO_L3N_T0_DQS_33)
P3_D5_P: J32.14 (S9_D5P), R335.1, U21.G2 (IO_L3P_T0_DQS_33)
P3_D6_N: J32.19 (S14_D6N), R336.2, U21.H1 (IO_L7N_T1_33)
P3_D6_P: J32.17 (S12_D6P), R336.1, U21.J1 (IO_L7P_T1_33)
P3_D7_N: J32.20 (S15_D7N), R337.2, U21.H3 (IO_L8N_T1_33)
P3_D7_P: J32.18 (S13_D7P), R337.1, U21.H4 (IO_L8P_T1_33)
P3_D8_N: J32.23 (S18), R338.2, U21.K1 (IO_L9N_T1_DQS_33)
P3_D8_P: J32.21 (S16), R338.1, U21.K2 (IO_L9P_T1_DQS_33)
P3_S17: J32.22 (S17), U21.J6 (IO_L22N_T3_33)
P3_S19: J32.24 (S19), U21.J5 (IO_L20N_T3_33)
P3_S20: J32.25 (S20), U21.K6 (IO_L22P_T3_33)
P3_S21: J32.26 (S21), U21.K5 (IO_L20P_T3_33)
P3_S22: J32.27 (S22), U21.K8 (IO_L24P_T3_33)
P3_S23: J32.28 (S23), U21.K7 (IO_L24N_T3_33)
P3_S24: J32.29 (S24), U21.N6 (IO_L23N_T3_33)
P3_S25: J32.30 (S25), U21.L8 (IO_L21N_T3_DQS_33)
P3_S26: J32.31 (S26), U21.M8 (IO_L21P_T3_DQS_33)
P3_S27: J32.32 (S27), U21.N7 (IO_L23P_T3_33)
P4_CLK_P2C_N: J33.35 (P2C_CLKn), R349.2, U21.F8 (IO_L11P_T1_SRCC_34)
P4_CLK_P2C_P: J33.33 (P2C_CLKp), R349.1, U21.E7 (IO_L11N_T1_SRCC_34)
P4_D0_N: J33.07 (S2_D0N), R340.2, U21.H11 (IO_L1N_T0_34)
P4_D0_P: J33.05 (S0_D0P), R340.1, U21.J11 (IO_L1P_T0_34)
P4_D1_N: J33.08 (S3_D1N), R341.2, U21.J9 (IO_L5N_T0_34)
P4_D1_P: J33.06 (S1_D1P), R341.1, U21.J10 (IO_L5P_T0_34)
P4_D2_N: J33.11 (S6_D2N), R342.2, U21.H8 (IO_L6N_T0_VREF_34)
P4_D2_P: J33.09 (S4_D2P), R342.1, U21.J8 (IO_L6P_T0_34)
P4_D3_N: J33.12 (S7_D3N), R343.2, U21.E8 (IO_L9N_T1_DQS_34)
P4_D3_P: J33.10 (S5_D3P), R343.1, U21.F9 (IO_L9P_T1_DQS_34)
P4_D4_N: J33.15 (S10_D4N), R344.2, U21.D8 (IO_L8N_T1_34)
P4_D4_P: J33.13 (S8_D4P), R344.1, U21.D9 (IO_L8P_T1_34)
P4_D5_N: J33.16 (S11_D5N), R345.2, U21.G5 (IO_L2N_T0_34)
P4_D5_P: J33.14 (S9_D5P), R345.1, U21.G6 (IO_L2P_T0_34)
P4_D6_N: J33.19 (S14_D6N), R346.2, U21.D5 (IO_L10N_T1_34)
P4_D6_P: J33.17 (S12_D6P), R346.1, U21.E6 (IO_L10P_T1_34)
P4_D7_N: J33.20 (S15_D7N), R347.2, U21.E5 (IO_L7N_T1_34)
P4_D7_P: J33.18 (S13_D7P), R347.1, U21.F5 (IO_L7P_T1_34)
P4_D8_N: J33.23 (S18), R348.2, U21.H6 (IO_L4N_T0_34)
P4_D8_P: J33.21 (S16), R348.1, U21.H7 (IO_L4P_T0_34)
P4_S17: J33.22 (S17), U21.B6 (IO_L21P_T3_DQS_34)
P4_S19: J33.24 (S19), U21.A5 (IO_L21N_T3_DQS_34)
P4_S20: J33.25 (S20), U21.A2 (IO_L24N_T3_34)
P4_S21: J33.26 (S21), U21.B5 (IO_L20P_T3_34)
P4_S22: J33.27 (S22), U21.B2 (IO_L24P_T3_34)
P4_S23: J33.28 (S23), U21.A4 (IO_L22P_T3_34)
P4_S24: J33.29 (S24), U21.B1 (IO_L23N_T3_34)
P4_S25: J33.30 (S25), U21.B4 (IO_L20N_T3_34)
P4_S26: J33.31 (S26), U21.C2 (IO_L23P_T3_34)
P4_S27: J33.32 (S27), U21.A3 (IO_L22N_T3_34)

Notes on the sheet:
LVDS Termination
SYZYGY P3 C2P clock can be switched between the clock generator and FPGA. By default it's FPGA
P3_S25, P3_S27 are used to pass through the PS I2C: I2C_PSSZG3.I2C_SCL, I2C_PSSZG3.I2C_SDA
0b0110_100X
0b0110_110X
