electrodyssey/NASR-M/uart.kicad_sch

## KiCad design uart.kicad_sch (2025-10-22)

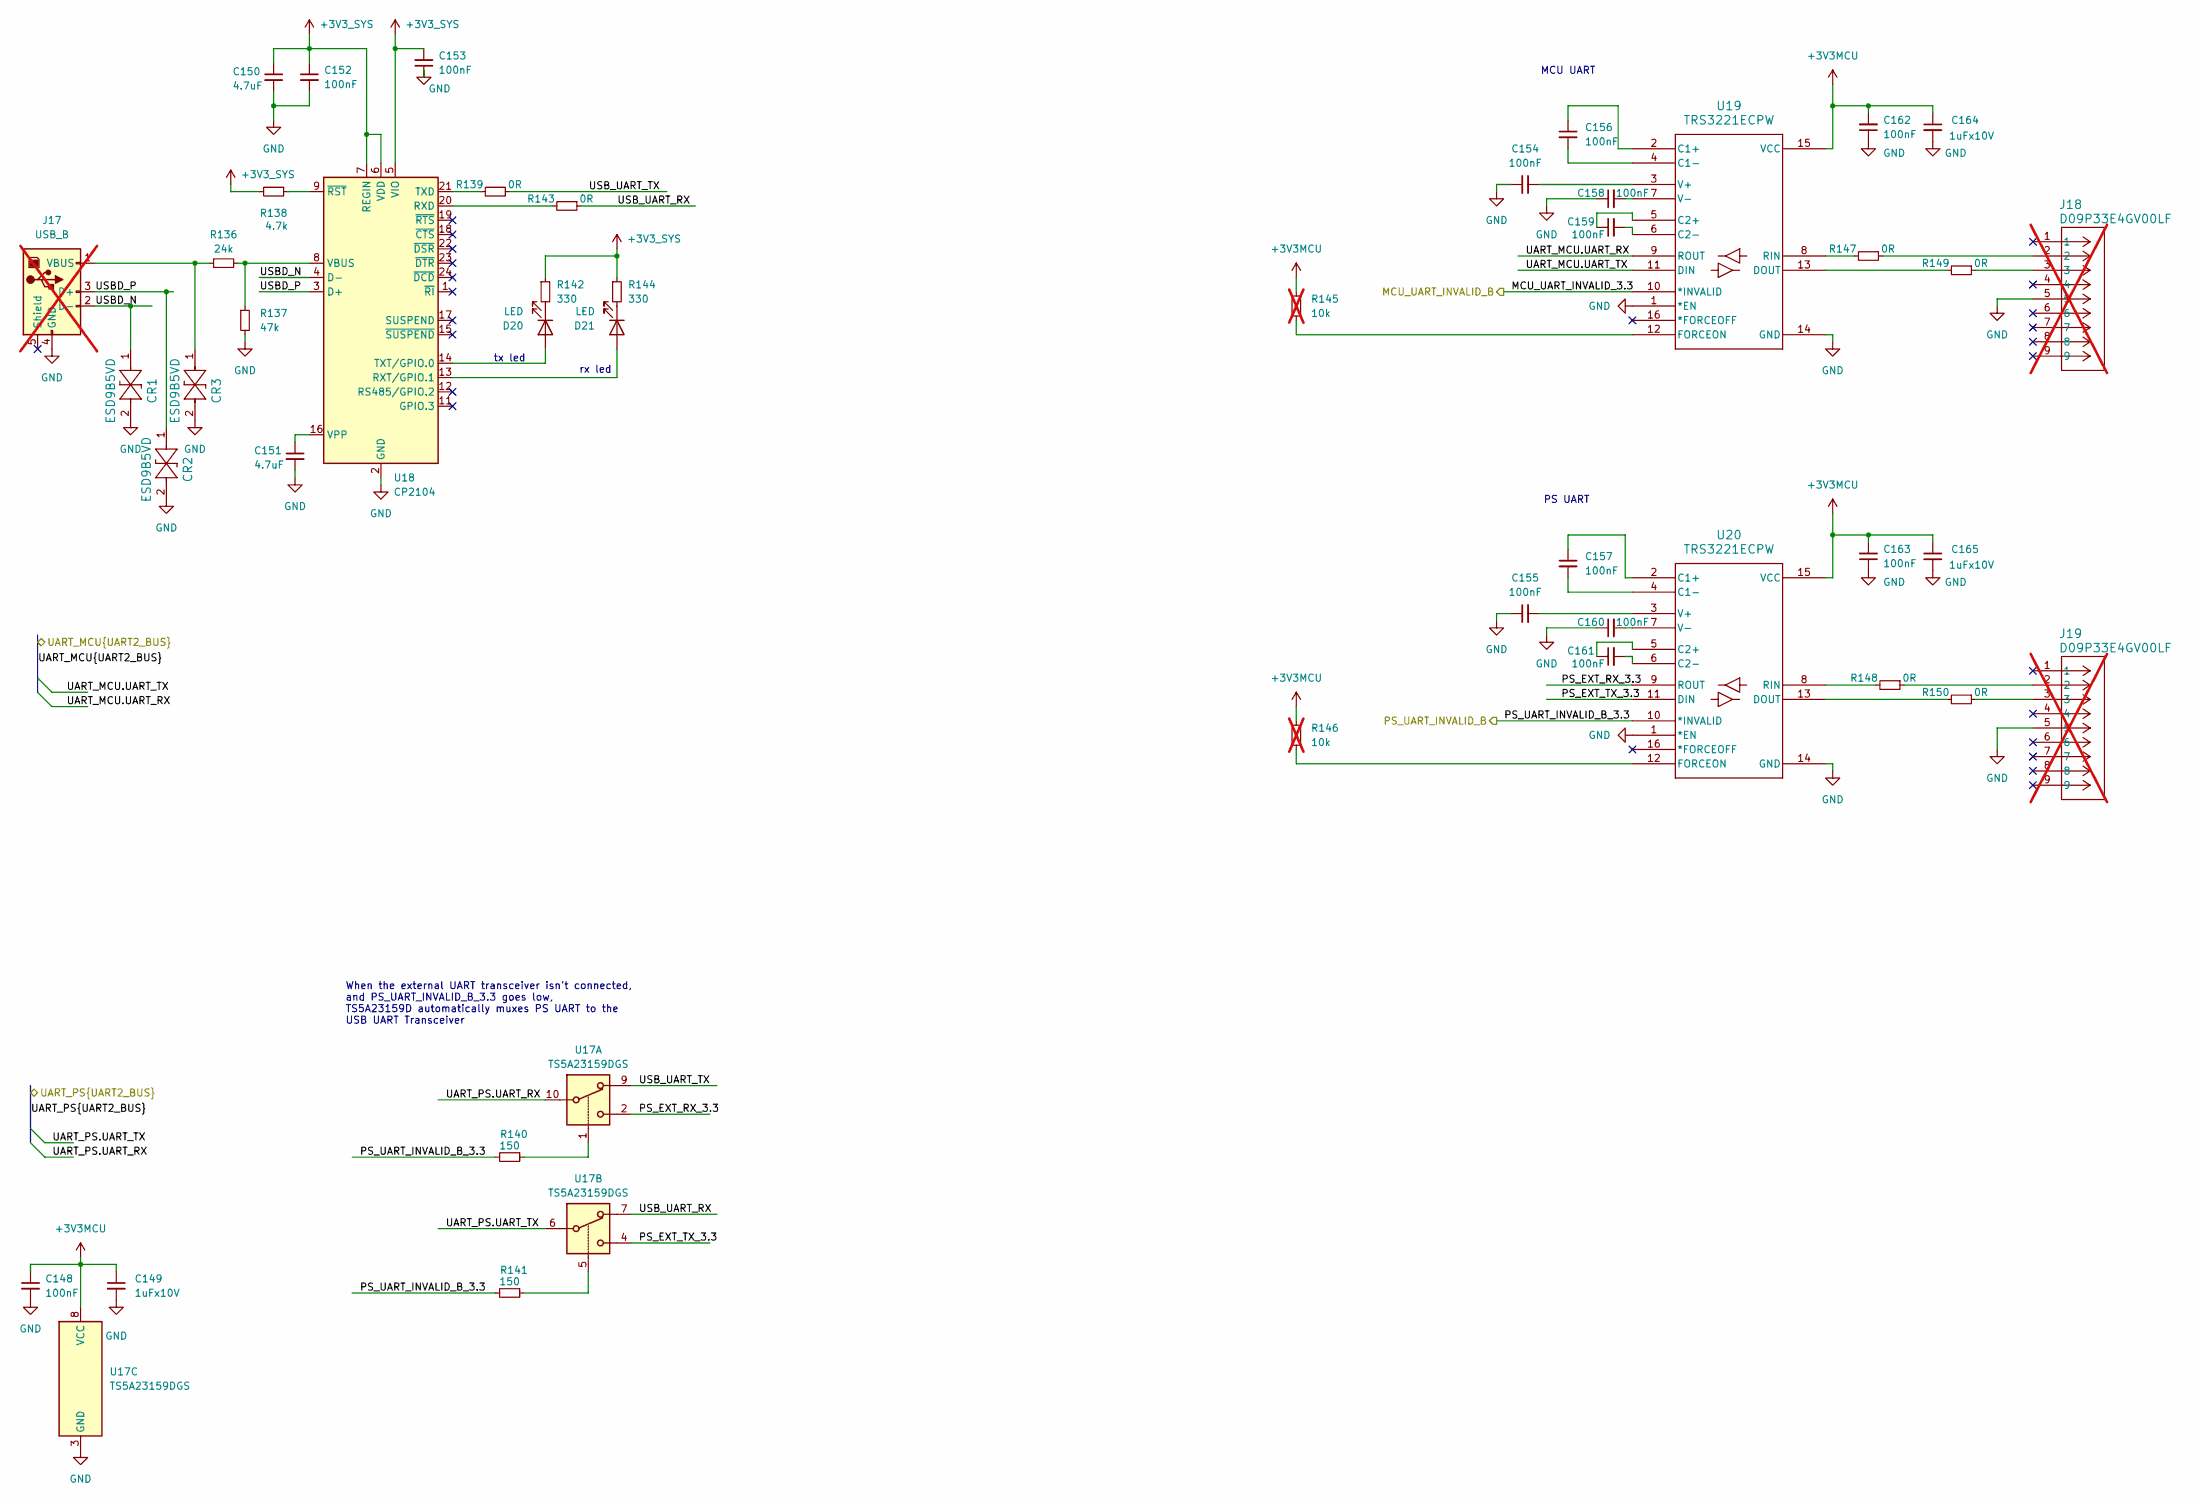
[picture p65: schematic uart.kicad_sch]

Parts:
C148, C152, C153, C162, C163: 100nF; C_0402_1005Metric; Part CC0402JRX7R8BB104; JLCPCB Part # C541465
C149, C164, C165: 1uFx10V; C_0603_1608Metric; JLCPCB Part # C841050
C150, C151: 4.7uF; C_0402_1005Metric; Part CL05A475KP5NRNC; JLCPCB Part # C368809
C154, C155, C156, C157, C158, C159, C160, C161: 100nF; C_0805_2012Metric; Part CC0805KRX7R9BB104; JLCPCB Part # C49678
CR1, CR2, CR3: ESD9B5VD; SOD-9230402_TCP; Part ESD9B5VL; JLCPCB Part # C2827544
D20, D21: LED; LED_0805_2012Metric; Part HL-PSC-2012S11GC; JLCPCB Part # C497958
J17: USB_B; USB_B_OST_USB-B1HSxx_Horizontal; not fitted
J18, J19: D09P33E4GV00LF; CONN_D09P33ExGX00xx_AMP; Part D09P33E4GV00LF; JLCPCB Part # C599281; not fitted
R136: 24k; R_0603_1608Metric; Part ERA3AEB243V; JLCPCB Part # C473247
R137: 47k; R_0603_1608Metric; JLCPCB Part # C5139555
R138: 4.7k; R_0402_1005Metric; Part 0402WGF4701TCE; JLCPCB Part # C25900
R139, R143, R147, R148, R149, R150: 0R; R_0603_1608Metric; Part FRC0603F0000TS; JLCPCB Part # C2906974
R140, R141: 150; R_0402_1005Metric; Part 0402WGF1500TCE; JLCPCB Part # C25082
R142, R144: 330; R_0402_1005Metric; Part 0402WGF3300TCE; JLCPCB Part # C25104
R145, R146: 10k; R_0402_1005Metric; Part 0402WGF1002TCE; JLCPCB Part # C25744; not fitted
U17: TS5A23159DGS; VSSOP-10_3x3mm_P0.5mm; JLCPCB Part # C42751
U18: CP2104; QFN-24-1EP_4x4mm_P0.5mm_EP2.6x2.6mm; Part CP2104-F03-GMR; JLCPCB Part # C47742
U19, U20: TRS3221ECPW; PW16; JLCPCB Part # C2865157

Connections:
+3V3MCU: C148.1, C149.1, C162.2, C163.2, C164.1, C165.1, R145.1, R146.1, U17.8 (VCC), U19.15 (VCC), U20.15 (VCC)
+3V3_SYS: C150.1, C152.1, C153.2, R138.2, R142.1, R144.1, U18.5 (VIO), U18.6 (VDD), U18.7 (REGIN)
GND: C148.2, C149.2, C150.2, C151.2, C152.2, C153.1, C154.1, C155.1, C158.1, C160.1, C162.1, C163.1, C164.2, C165.2, CR1.2, CR2.2, CR3.2, J17.4 (GND), J18.5, J19.5, R137.2, U17.3 (GND), U18.2 (GND), U18.25 (GND), U19.1 (*EN), U19.14 (GND), U20.1 (*EN), U20.14 (GND)
MCU_UART_INVALID_3.3: U19.10 (*INVALID)
unnamed: C151.1, U18.16 (VPP)
unnamed: C154.2, U19.3 (V+)
unnamed: C155.2, U20.3 (V+)
unnamed: C156.1, U19.2 (C1+)
unnamed: C156.2, U19.4 (C1-)
unnamed: C157.1, U20.2 (C1+)
unnamed: C157.2, U20.4 (C1-)
unnamed: C158.2, U19.7 (V-)
unnamed: C159.1, U19.5 (C2+)
unnamed: C159.2, U19.6 (C2-)
unnamed: C160.2, U20.7 (V-)
unnamed: C161.1, U20.5 (C2+)
unnamed: C161.2, U20.6 (C2-)
unnamed: CR3.1, J17.1 (VBUS), R136.1
unnamed: D20.1 (K), R142.2
unnamed: D20.2 (A), U18.14 (TXT/GPIO.0)
unnamed: D21.1 (K), R144.2
unnamed: D21.2 (A), U18.13 (RXT/GPIO.1)
unnamed: J18.2, R147.1
unnamed: J18.3, R149.1
unnamed: J19.2, R148.1
unnamed: J19.3, R150.1
unnamed: R136.2, R137.1, U18.8 (VBUS)
unnamed: R138.1, U18.9 (~RST)
unnamed: R139.2, U18.21 (TXD)
unnamed: R140.1, U17.1
unnamed: R141.1, U17.5
unnamed: R143.2, U18.20 (RXD)
unnamed: R145.2, U19.12 (FORCEON)
unnamed: R146.2, U20.12 (FORCEON)
unnamed: R147.2, U19.8 (RIN)
unnamed: R148.2, U20.8 (RIN)
unnamed: R149.2, U19.13 (DOUT)
unnamed: R150.2, U20.13 (DOUT)
PS_EXT_RX_3.3: U17.2, U20.9 (ROUT)
PS_EXT_TX_3.3: U17.4, U20.11 (DIN)
PS_UART_INVALID_B: R140.2, R141.2, U20.10 (*INVALID)
UART_MCU.UART_RX: U19.9 (ROUT)
UART_MCU.UART_TX: U19.11 (DIN)
UART_PS.UART_RX: U17.10
UART_PS.UART_TX: U17.6
USBD_N: CR1.1, J17.2 (D-), U18.4 (D-)
USBD_P: CR2.1, J17.3 (D+), U18.3 (D+)
USB_UART_RX: R143.1, U17.7
USB_UART_TX: R139.1, U17.9

Notes on the sheet:
PS UART
MCU UART
When the external UART transceiver isn't connected, and PS_UART_INVALID_B_3.3 goes low, TS5A23159D automatically muxes PS UART to the USB UART Transceiver
rx led
tx led
