electrodyssey/NASR-M/usb-hub.kicad_sch

## KiCad design usb-hub.kicad_sch (2025-10-22)

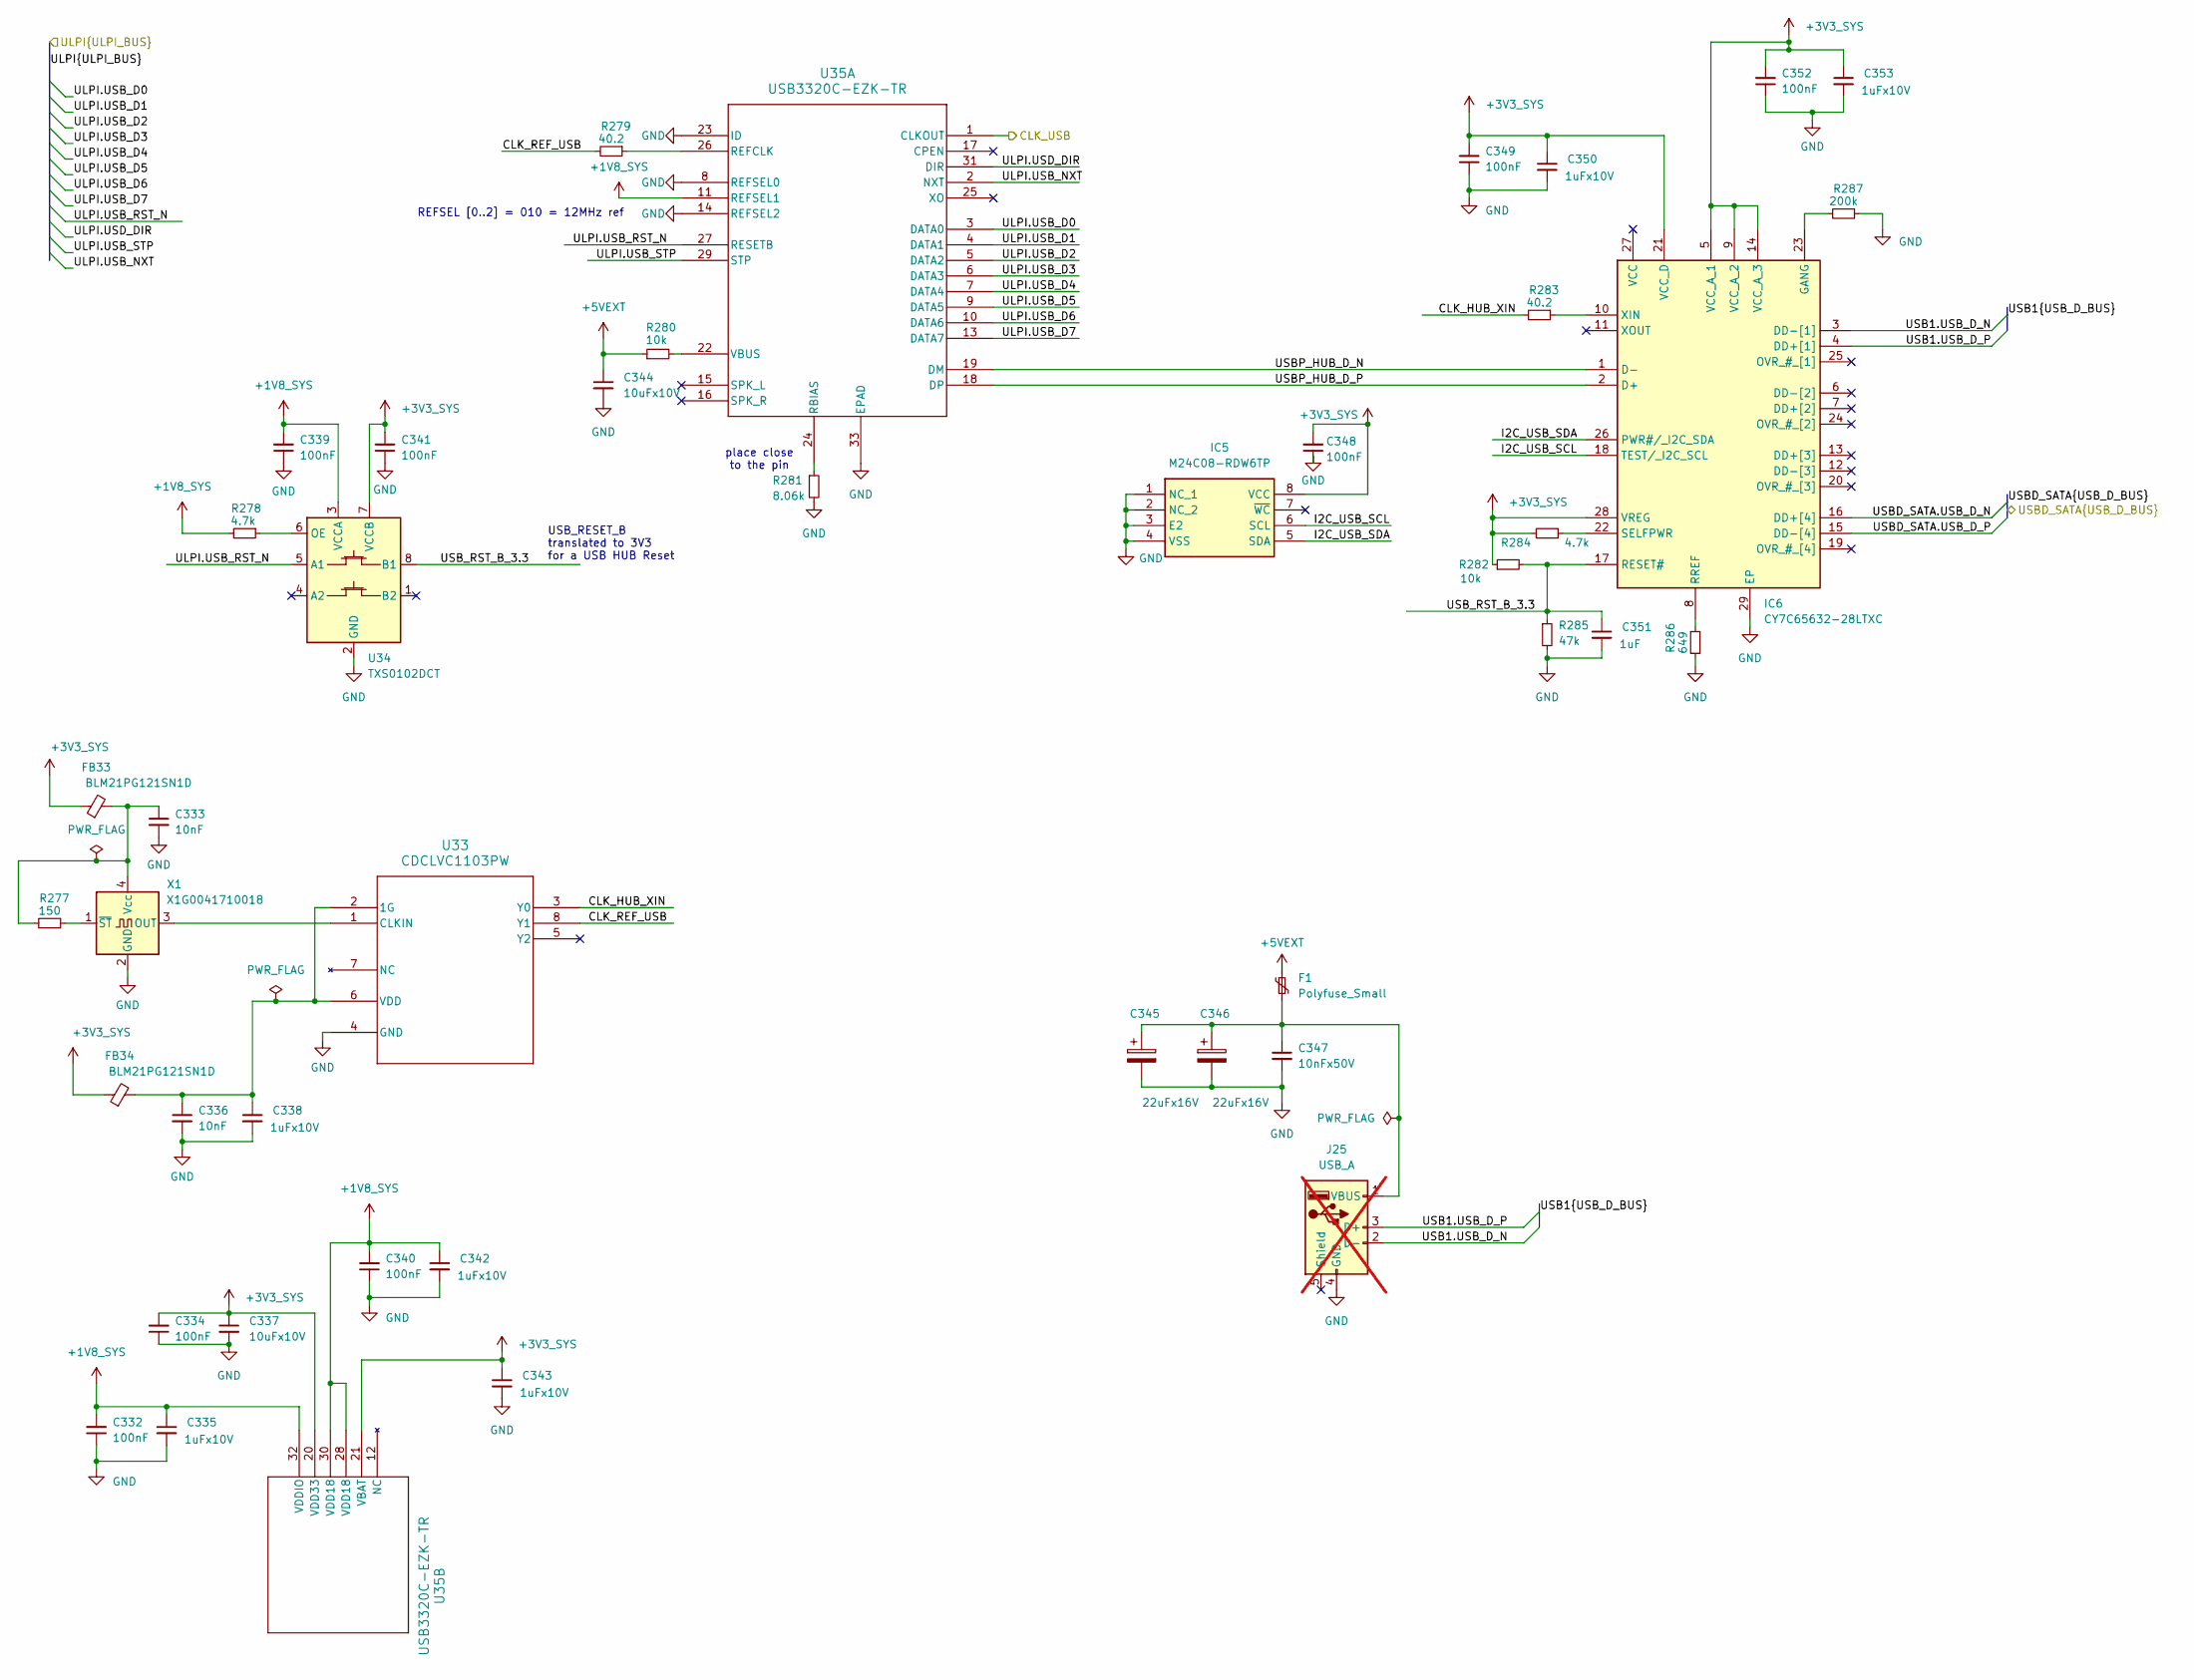
[picture p66: schematic usb-hub.kicad_sch]

Parts:
C332, C334, C339, C340, C341, C348, C349, C352: 100nF; C_0402_1005Metric; Part CC0402JRX7R8BB104; JLCPCB Part # C541465
C333, C336: 10nF; C_0805_2012Metric; Part TCC0805X7R103K500DT; JLCPCB Part # C282728
C335, C338, C342, C343, C350, C353: 1uFx10V; C_0603_1608Metric; JLCPCB Part # C841050
C337, C344: 10uFx10V; C_0805_2012Metric; Part CL21A106KPFNNNE; JLCPCB Part # C17024
C345, C346: 22uFx16V; CP_EIA-6032-15_Kemet-U; Part TR3C226K016C0350; JLCPCB Part # C1954274
C347: 10nFx50V; C_1206_3216Metric; JLCPCB Part # C513774
C351: 1uF; C_0603_1608Metric; JLCPCB Part # C841050
F1: Polyfuse_Small; Fuse_Bourns_MF-SM_7.98x5.44mm; Part 2920L125PR; JLCPCB Part # C192524
FB33, FB34: BLM21PG121SN1D; L_0805_2012Metric; Part BLM21PG121SN1D; JLCPCB Part # C79382
IC5: M24C08-RDW6TP; SOP65P640X120-8N; Mouser Part Number 511-M24C08-RDW6TP
IC6: CY7C65632-28LTXC; QFN50P500X500X80-29N-D; Mouser Part Number 727-CY7C65632-28LTXC
J25: USB_A; USB_A_CONNFLY_DS1095-WNR0; Part DS1095-WNR0; JLCPCB Part # C19944603; not fitted
R277: 150; R_0402_1005Metric; Part 0402WGF1500TCE; JLCPCB Part # C25082
R278, R284: 4.7k; R_0402_1005Metric; Part 0402WGF4701TCE; JLCPCB Part # C25900
R279, R283: 40.2; R_0402_1005Metric; Part RT0402FRE0740R2L; JLCPCB Part # C327007
R280, R282: 10k; R_0402_1005Metric; Part 0402WGF1002TCE; JLCPCB Part # C25744
R281: 8.06k; R_0603_1608Metric; Part FRC0603F8061TS; JLCPCB Part # C2960681
R285: 47k; R_0603_1608Metric; JLCPCB Part # C5139555
R286: 649; R_0603_1608Metric; Part RT0603CRD07649RL; JLCPCB Part # C705904
R287: 200k; R_0603_1608Metric; Part RT0603BRD07200KL; JLCPCB Part # C728585
U33: CDCLVC1103PW; PW8; Part CDCLVC1103PWR; JLCPCB Part # C555453
U34: TXS0102DCT; SSOP-8_2.95x2.8mm_P0.65mm; Part TXS0102DCTR; JLCPCB Part # C324082
U35: USB3320C-EZK-TR; QFN32_5X5MC_MCH; Part USB3320C-EZK-TR; JLCPCB Part # C132156
X1: X1G0041710018; Oscillator_SMD_SeikoEpson_SG210-4Pin_2.5x2.0mm; Part X1G0041710018; JLCPCB Part # C255991

Connections:
+1V8_SYS: C332.2, C335.1, C339.2, C340.2, C342.1, R278.2, U34.3 (VCCA), U35.11 (REFSEL1), U35.28 (VDD18), U35.30 (VDD18), U35.32 (VDDIO)
+3V3_SYS: C334.2, C337.1, C341.2, C343.1, C348.2, C349.2, C350.1, C352.2, C353.1, FB33.1, FB34.1, IC5.8 (VCC), IC6.5 (VCC_A_1), IC6.9 (VCC_A_2), IC6.14 (VCC_A_3), IC6.21 (VCC_D), IC6.28 (VREG), R282.1, R284.2, U34.7 (VCCB), U35.20 (VDD33), U35.21 (VBAT)
+5VEXT: C344.1, F1.1, R280.1
CLK_HUB_XIN: R283.2, U33.3 (Y0)
CLK_REF_USB: R279.2, U33.8 (Y1)
CLK_USB: U35.1 (CLKOUT)
GND: C332.1, C333.2, C334.1, C335.2, C336.2, C337.2, C338.2, C339.1, C340.1, C341.1, C342.2, C343.2, C344.2, C345.2, C346.2, C347.2, C348.1, C349.1, C350.2, C351.2, C352.1, C353.2, IC5.1 (NC_1), IC5.2 (NC_2), IC5.3 (E2), IC5.4 (VSS), IC6.29 (EP), J25.4 (GND), R281.2, R285.2, R286.2, R287.1, U33.4 (GND), U34.2 (GND), U35.8 (REFSEL0), U35.14 (REFSEL2), U35.23 (ID), U35.33 (EPAD), X1.2 (GND)
I2C_USB_SCL: IC5.6 (SCL), IC6.18 (TEST/_I2C_SCL)
I2C_USB_SDA: IC5.5 (SDA), IC6.26 (PWR#/_I2C_SDA)
unnamed: C333.1, FB33.2, R277.2, X1.4 (Vcc)
unnamed: C336.1, C338.1, FB34.2, U33.2 (1G), U33.6 (VDD)
unnamed: C345.1, C346.1, C347.1, F1.2, J25.1 (VBUS)
unnamed: IC6.8 (RREF), R286.1
unnamed: IC6.10 (XIN), R283.1
unnamed: IC6.22 (SELFPWR), R284.1
unnamed: IC6.23 (GANG), R287.2
unnamed: R277.1, X1.1 (~ST)
unnamed: R278.1, U34.6 (OE)
unnamed: R279.1, U35.26 (REFCLK)
unnamed: R280.2, U35.22 (VBUS)
unnamed: R281.1, U35.24 (RBIAS)
unnamed: U33.1 (CLKIN), X1.3 (OUT)
ULPI.USB_D0: U35.3 (DATA0)
ULPI.USB_D1: U35.4 (DATA1)
ULPI.USB_D2: U35.5 (DATA2)
ULPI.USB_D3: U35.6 (DATA3)
ULPI.USB_D4: U35.7 (DATA4)
ULPI.USB_D5: U35.9 (DATA5)
ULPI.USB_D6: U35.10 (DATA6)
ULPI.USB_D7: U35.13 (DATA7)
ULPI.USB_NXT: U35.2 (NXT)
ULPI.USB_RST_N: U34.5 (A1), U35.27 (RESETB)
ULPI.USB_STP: U35.29 (STP)
ULPI.USD_DIR: U35.31 (DIR)
USB1.USB_D_N: IC6.3 (DD-[1]), J25.2 (D-)
USB1.USB_D_P: IC6.4 (DD+[1]), J25.3 (D+)
USBD_SATA.USB_D_N: IC6.16 (DD+[4])
USBD_SATA.USB_D_P: IC6.15 (DD-[4])
USBP_HUB_D_N: IC6.1 (D-), U35.19 (DM)
USBP_HUB_D_P: IC6.2 (D+), U35.18 (DP)
USB_RST_B_3.3: C351.1, IC6.17 (RESET#), R282.2, R285.1, U34.8 (B1)

Notes on the sheet:
USB_RESET_B translated to 3V3 for a USB HUB Reset
place close to the pin
REFSEL [0..2] = 010 = 12MHz ref
