electrodyssey/NASR-M/usb-sata.kicad_sch

## KiCad design usb-sata.kicad_sch (2025-10-22)

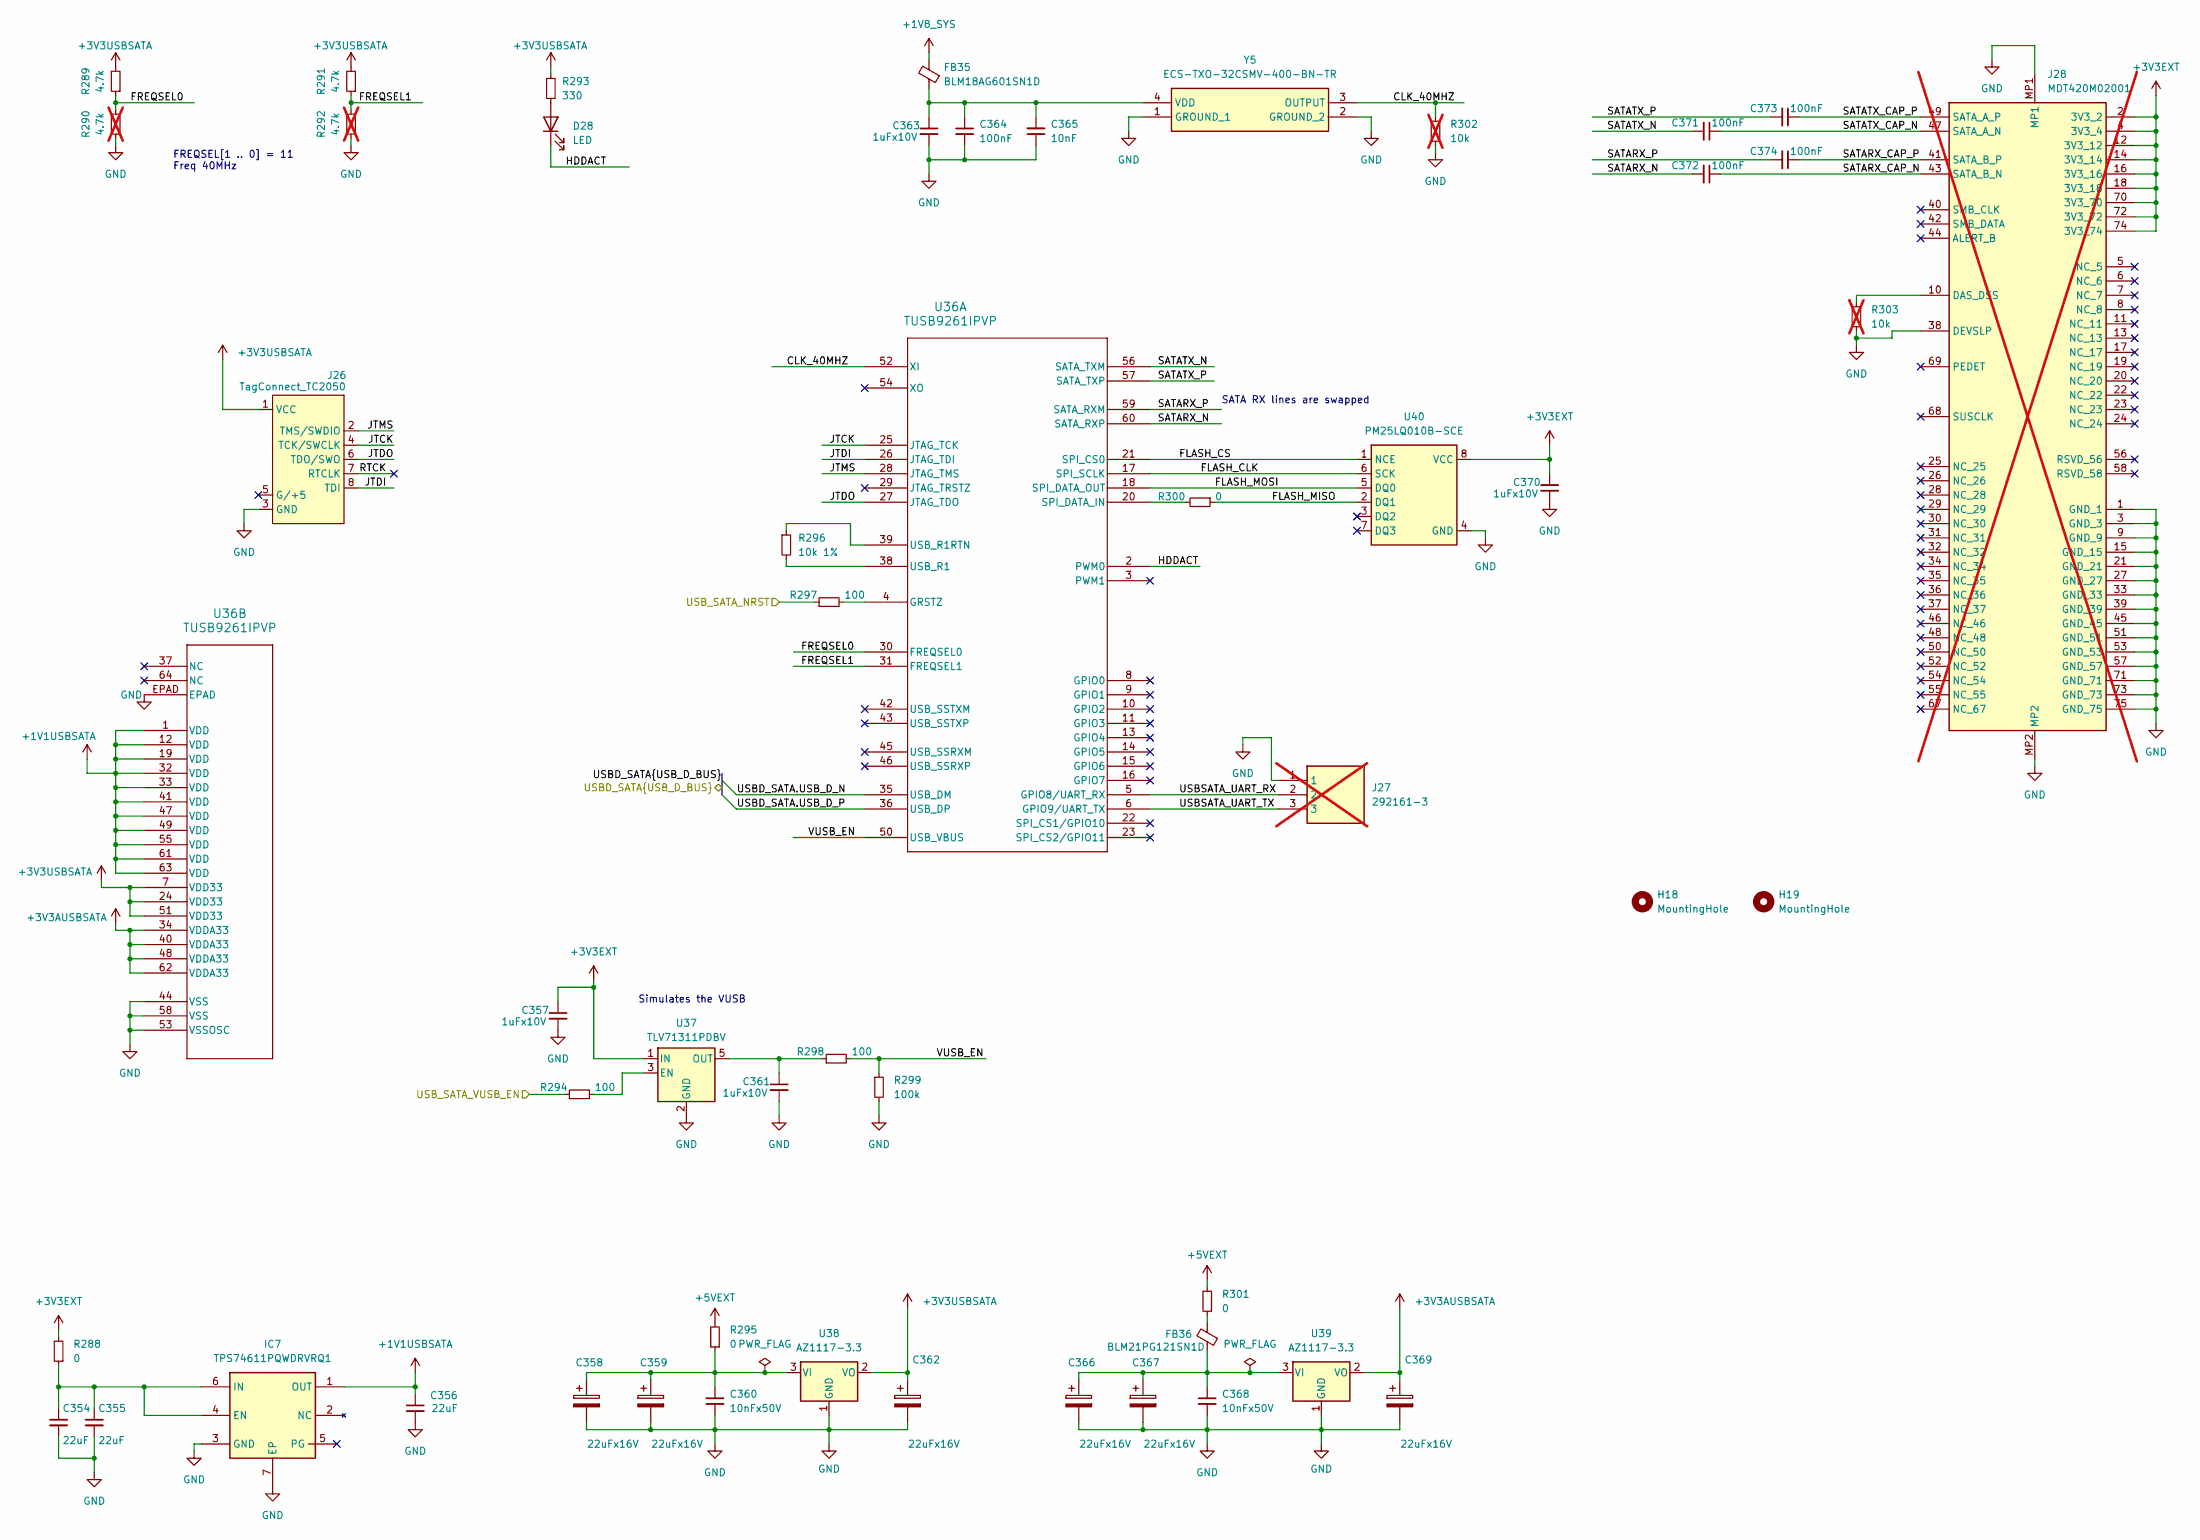
[picture p67: schematic usb-sata.kicad_sch]

Parts:
C354, C355, C356: 22uF; C_0805_2012Metric; Part CL21A226MQQNNNE; JLCPCB Part # C5674
C357, C361, C363, C370: 1uFx10V; C_0603_1608Metric; JLCPCB Part # C841050
C358, C359, C362, C366, C367, C369: 22uFx16V; CP_EIA-6032-15_Kemet-U; Part TR3C226K016C0350; JLCPCB Part # C1954274
C360, C368: 10nFx50V; C_1206_3216Metric; JLCPCB Part # C513774
C364, C371, C372, C373, C374: 100nF; C_0402_1005Metric; Part CC0402JRX7R8BB104; JLCPCB Part # C541465
C365: 10nF; C_0402_1005Metric; Part CL05B103KB5NNNC; JLCPCB Part # C15195
D28: LED; LED_0805_2012Metric; Part HL-PSC-2012S11GC; JLCPCB Part # C497958
FB35: BLM18AG601SN1D; L_0603_1608Metric; Part BLM18AG601SN1D; JLCPCB Part # C19330
FB36: BLM21PG121SN1D; L_0805_2012Metric; Part BLM21PG121SN1D; JLCPCB Part # C79382
H18, H19: MountingHole; MountingHole_4.3x6.2mm_M4_Pad
IC7: TPS74611PQWDRVRQ1; SON65P200X200X80-7N; Mouser Part Number 595-PS74611PQWDRVRQ1
J26: TagConnect_TC2050; Tag-Connect_TC2050-IDC-FP_2x05_P1.27mm_Vertical
J27: 292161-3; SHDR3W60P0X200_1X3_780X360X680P; Mouser Part Number 571-292161-3; not fitted
J28: MDT420M02001; Mouser Part Number 523-MDT420M02001; not fitted
R288, R295, R300, R301: 0; R_0805_2012Metric; Part 0805W8F0000T5E; JLCPCB Part # C17477
R289, R291: 4.7k; R_0402_1005Metric; Part 0402WGF4701TCE; JLCPCB Part # C25900
R290, R292: 4.7k; R_0402_1005Metric; Part 0402WGF4701TCE; JLCPCB Part # C25900; not fitted
R293: 330; R_0402_1005Metric; Part 0402WGF3300TCE; JLCPCB Part # C25104
R294, R297, R298: 100; R_0402_1005Metric; Part RM04FTN1000; JLCPCB Part # C153111
R296: 10k 1%; R_0402_1005Metric; Part 0402WGF1002TCE; JLCPCB Part # C25744
R299: 100k; R_0402_1005Metric; Part RC0402FR-07100KL; JLCPCB Part # C60491
R302, R303: 10k; R_0402_1005Metric; Part 0402WGF1002TCE; JLCPCB Part # C25744; not fitted
U36: TUSB9261IPVP; PVP64_3P9X3P9; JLCPCB Part # C140577
U37: TLV71311PDBV; SOT-23-5; Part TLV71311PDBVR; JLCPCB Part # C205964
U38, U39: AZ1117-3.3; SOT-223-3_TabPin2; Part AZ1117H-3.3TRG1; JLCPCB Part # C110474
U40: PM25LQ010B-SCE; SOIC-8_3.9x4.9mm_P1.27mm; JLCPCB Part # C411812
Y5: ECS-TXO-32CSMV-400-BN-TR; ECSTXO32CSMV270ANTR; Mouser Part Number 520-TXO32CSMV270ANTR

Connections:
+1V1USBSATA: C356.1, IC7.1 (OUT), U36.1 (VDD), U36.12 (VDD), U36.19 (VDD), U36.32 (VDD), U36.33 (VDD), U36.41 (VDD), U36.47 (VDD), U36.49 (VDD), U36.55 (VDD), U36.61 (VDD), U36.63 (VDD)
+1V8_SYS: FB35.2
+3V3AUSBSATA: C369.1, U36.34 (VDDA33), U36.40 (VDDA33), U36.48 (VDDA33), U36.62 (VDDA33), U39.2 (VO)
+3V3EXT: C357.1, C370.1, J28.2 (3V3_2), J28.4 (3V3_4), J28.12 (3V3_12), J28.14 (3V3_14), J28.16 (3V3_16), J28.18 (3V3_18), J28.70 (3V3_70), J28.72 (3V3_72), J28.74 (3V3_74), R288.2, U37.1 (IN), U40.8 (VCC)
+3V3USBSATA: C362.1, J26.1 (VCC), R289.2, R291.2, R293.1, U36.7 (VDD33), U36.24 (VDD33), U36.51 (VDD33), U38.2 (VO)
+5VEXT: R295.2, R301.2
CLK_40MHZ: R302.1, U36.52 (XI), Y5.3 (OUTPUT)
FLASH_CLK: U36.17 (SPI_SCLK), U40.6 (SCK)
FLASH_CS: U36.21 (SPI_CS0), U40.1 (NCE)
FLASH_MISO: R300.1, U40.2 (DQ1)
FLASH_MOSI: U36.18 (SPI_DATA_OUT), U40.5 (DQ0)
FREQSEL0: R289.1, R290.2, U36.30 (FREQSEL0)
FREQSEL1: R291.1, R292.2, U36.31 (FREQSEL1)
GND: C354.2, C355.2, C356.2, C357.2, C358.2, C359.2, C360.2, C361.2, C362.2, C363.2, C364.2, C365.1, C366.2, C367.2, C368.2, C369.2, C370.2, IC7.3 (GND), IC7.7 (EP), J26.3 (GND), J27.1, J28.1 (GND_1), J28.3 (GND_3), J28.9 (GND_9), J28.15 (GND_15), J28.21 (GND_21), J28.27 (GND_27), J28.33 (GND_33), J28.38 (DEVSLP), J28.39 (GND_39), J28.45 (GND_45), J28.51 (GND_51), J28.53 (GND_53), J28.57 (GND_57), J28.71 (GND_71), J28.73 (GND_73), J28.75 (GND_75), J28.MP1, J28.MP2, R290.1, R292.1, R299.2, R302.2, R303.2, U36.44 (VSS), U36.53 (VSSOSC), U36.58 (VSS), U36.EPAD, U37.2 (GND), U38.1 (GND), U39.1 (GND), U40.4 (GND), Y5.1 (GROUND_1), Y5.2 (GROUND_2)
HDDACT: D28.1 (K), U36.2 (PWM0)
JTCK: J26.4 (TCK/SWCLK), U36.25 (JTAG_TCK)
JTDI: J26.8 (TDI), U36.26 (JTAG_TDI)
JTDO: J26.6 (TDO/SWO), U36.27 (JTAG_TDO)
JTMS: J26.2 (TMS/SWDIO), U36.28 (JTAG_TMS)
unnamed: C354.1, C355.1, IC7.4 (EN), IC7.6 (IN), R288.1
unnamed: C358.1, C359.1, C360.1, R295.1, U38.3 (VI)
unnamed: C361.1, R298.1, U37.5 (OUT)
unnamed: C363.1, C364.1, C365.2, FB35.1, Y5.4 (VDD)
unnamed: C366.1, C367.1, C368.1, FB36.1, U39.3 (VI)
unnamed: D28.2 (A), R293.2
unnamed: FB36.2, R301.1
unnamed: J28.10 (DAS_DSS), R303.1
unnamed: R294.2, U37.3 (EN)
unnamed: R296.1, U36.39 (USB_R1RTN)
unnamed: R296.2, U36.38 (USB_R1)
unnamed: R297.2, U36.4 (GRSTZ)
unnamed: R300.2, U36.20 (SPI_DATA_IN)
RTCK: J26.7 (RTCLK)
SATARX_CAP_N: C372.1, J28.43 (SATA_B_N)
SATARX_CAP_P: C374.1, J28.41 (SATA_B_P)
SATARX_N: C372.2, U36.60 (SATA_RXP)
SATARX_P: C374.2, U36.59 (SATA_RXM)
SATATX_CAP_N: C371.1, J28.47 (SATA_A_N)
SATATX_CAP_P: C373.1, J28.49 (SATA_A_P)
SATATX_N: C371.2, U36.56 (SATA_TXM)
SATATX_P: C373.2, U36.57 (SATA_TXP)
USBD_SATA.USB_D_N: U36.35 (USB_DM)
USBD_SATA.USB_D_P: U36.36 (USB_DP)
USBSATA_UART_RX: J27.2, U36.5 (GPIO8/UART_RX)
USBSATA_UART_TX: J27.3, U36.6 (GPIO9/UART_TX)
USB_SATA_NRST: R297.1
USB_SATA_VUSB_EN: R294.1
VUSB_EN: R298.2, R299.1, U36.50 (USB_VBUS)

Notes on the sheet:
Simulates the VUSB
SATA RX lines are swapped
FREQSEL[1 .. 0] = 11 Freq 40MHz
