electrodyssey/NASR-M/vio_power.kicad_sch

## KiCad design vio_power.kicad_sch (2025-10-22)

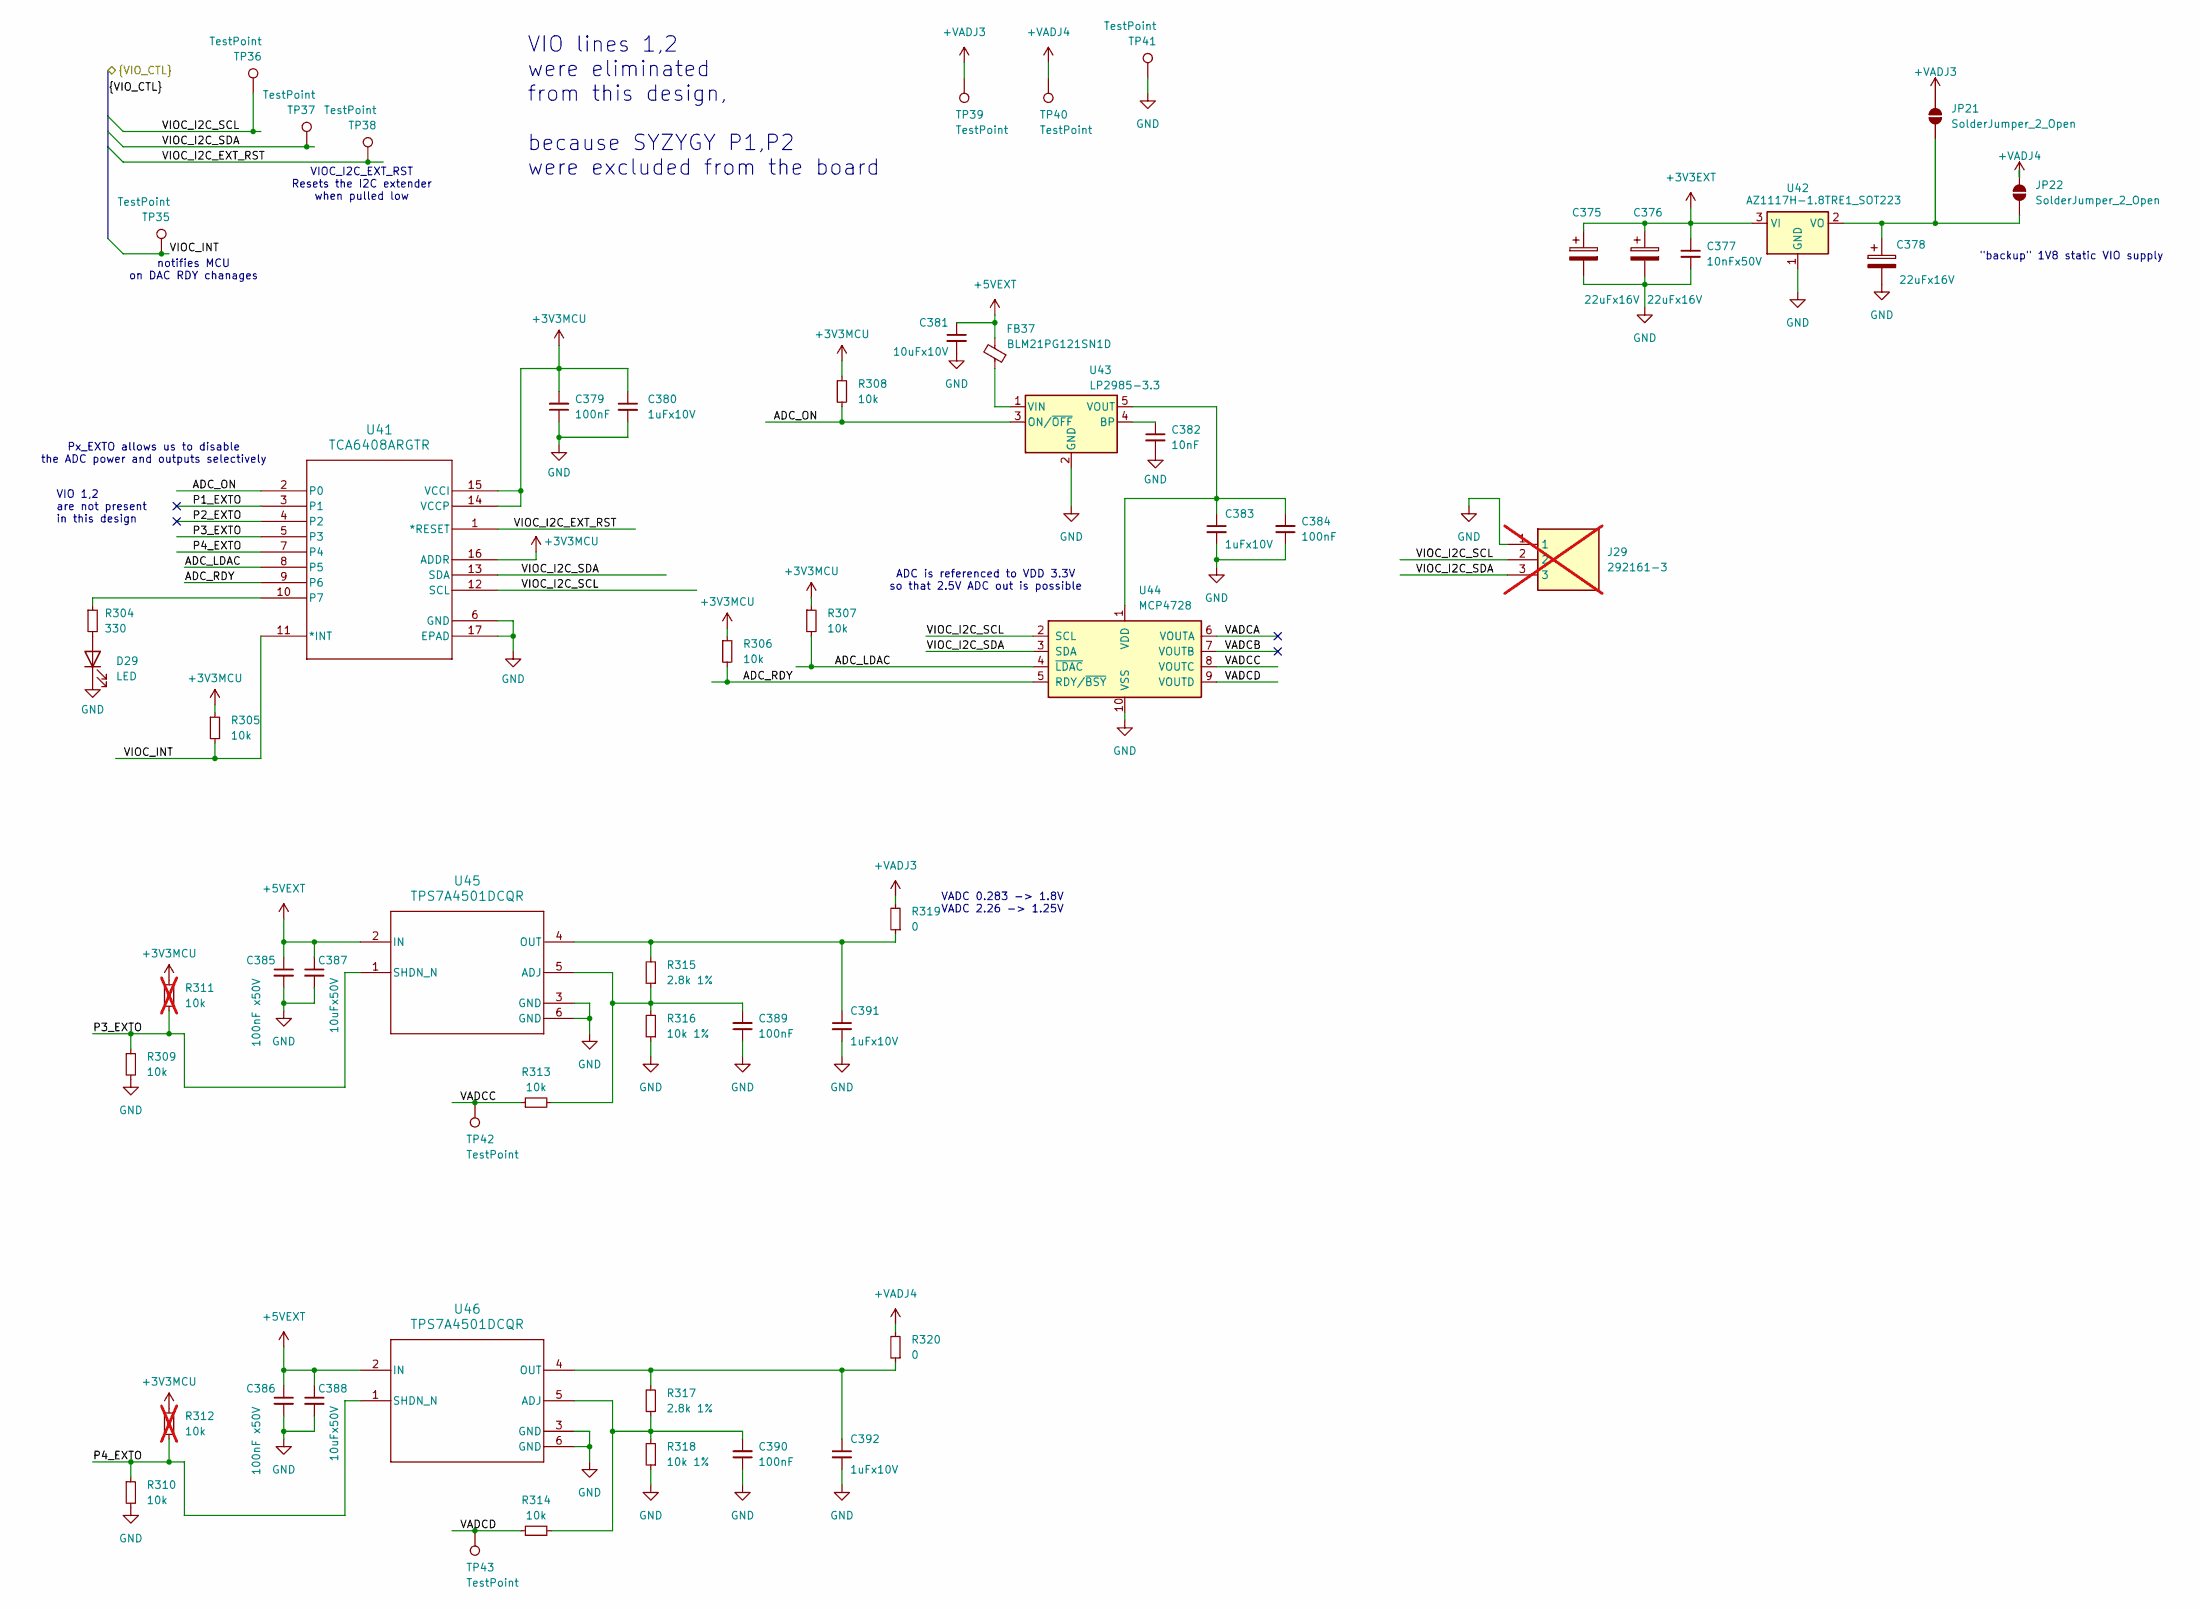
[picture p68: schematic vio_power.kicad_sch]

Parts:
C375, C376, C378: 22uFx16V; CP_EIA-6032-15_Kemet-U; Part TR3C226K016C0350; JLCPCB Part # C1954274
C377: 10nFx50V; C_1206_3216Metric; Part 1206B103K102NT; JLCPCB Part # C9194
C379, C384, C389, C390: 100nF; C_0402_1005Metric; Part CC0402JRX7R8BB104; JLCPCB Part # C541465
C380, C383, C391, C392: 1uFx10V; C_0603_1608Metric; JLCPCB Part # C841050
C381: 10uFx10V; C_0805_2012Metric; Part CL21A106KPFNNNE; JLCPCB Part # C17024
C382: 10nF; C_0805_2012Metric; Part TCC0805X7R103K500DT; JLCPCB Part # C282728
C385, C386: 100nF x50V; C_0805_2012Metric; Part C0805X104K5RACAUTO; JLCPCB Part # C141172
C387, C388: 10uFx50V; C_1206_3216Metric; Part CS3216X5R106K500NRI; JLCPCB Part # C513774
D29: LED; LED_0805_2012Metric; Part HL-PSC-2012S11GC; JLCPCB Part # C497958
FB37: BLM21PG121SN1D; L_0805_2012Metric; Part BLM21PG121SN1D; JLCPCB Part # C79382
J29: 292161-3; SHDR3W60P0X200_1X3_780X360X680P; Mouser Part Number 571-292161-3; not fitted
JP21, JP22: SolderJumper_2_Open; SolderJumper-2_P1.3mm_Open_Pad1.0x1.5mm
R304: 330; R_0402_1005Metric; Part 0402WGF3300TCE; JLCPCB Part # C25104
R305, R306, R307, R308, R309, R310, R313, R314: 10k; R_0402_1005Metric; Part 0402WGF1002TCE; JLCPCB Part # C25744
R311, R312: 10k; R_0402_1005Metric; Part 0402WGF1002TCE; JLCPCB Part # C25744; not fitted
R315, R317: 2.8k 1%; R_0402_1005Metric; Part 0402WGF2801TCE; JLCPCB Part # C62741
R316, R318: 10k 1%; R_0402_1005Metric; Part 0402WGF1002TCE; JLCPCB Part # C25744
R319, R320: 0; R_0805_2012Metric; Part 0805W8F0000T5E; JLCPCB Part # C17477
TP35, TP36, TP37, TP38, TP39, TP40, TP41, TP42, TP43: TestPoint; TestPoint_Pad_D1.0mm
U41: TCA6408ARGTR; RGT16_1P45X1P45; Part TCA6408ARGTR; JLCPCB Part # C181499
U42: AZ1117H-1.8TRE1_SOT223; SOT-223-3_TabPin2; Part LM1117MPX-1.8/NOPB; JLCPCB Part # C9660
U43: LP2985-3.3; SOT-23-5; JLCPCB Part # C95414
U44: MCP4728; MSOP-10_3x3mm_P0.5mm; JLCPCB Part # C108207
U45, U46: TPS7A4501DCQR; DCQ0006A-IPC_A; Part TPS7A4501DCQR; JLCPCB Part # C840094

Connections:
+3V3EXT: C375.1, C376.1, C377.1, U42.3 (VI)
+3V3MCU: C379.2, C380.1, R305.1, R306.1, R307.1, R308.1, R311.1, R312.1, U41.14 (VCCP), U41.15 (VCCI), U41.16 (ADDR)
+5VEXT: C381.1, C385.1, C386.1, C387.1, C388.1, FB37.2, U45.2 (IN), U46.2 (IN)
+VADJ3: JP21.2 (B), R319.2, TP39.1
+VADJ4: JP22.2 (B), R320.2, TP40.1
ADC_LDAC: R307.2, U41.8 (P5), U44.4 (~LDAC)
ADC_ON: R308.2, U41.2 (P0), U43.3 (ON/~OFF)
ADC_RDY: R306.2, U41.9 (P6), U44.5 (RDY/~BSY)
GND: C375.2, C376.2, C377.2, C378.2, C379.1, C380.2, C381.2, C382.2, C383.2, C384.1, C385.2, C386.2, C387.2, C388.2, C389.1, C390.1, C391.2, C392.2, D29.1 (K), J29.1, R309.2, R310.2, R316.1, R318.1, TP41.1, U41.6 (GND), U41.17 (EPAD), U42.1 (GND), U43.2 (GND), U44.10 (VSS), U45.3 (GND), U45.6 (GND), U46.3 (GND), U46.6 (GND)
unnamed: C378.1, JP21.1 (A), JP22.1 (A), U42.2 (VO)
unnamed: C382.1, U43.4 (BP)
unnamed: C383.1, C384.2, U43.5 (VOUT), U44.1 (VDD)
unnamed: C389.2, R313.2, R315.1, R316.2, U45.5 (ADJ)
unnamed: C390.2, R314.2, R317.1, R318.2, U46.5 (ADJ)
unnamed: C391.1, R315.2, R319.1, U45.4 (OUT)
unnamed: C392.1, R317.2, R320.1, U46.4 (OUT)
unnamed: D29.2 (A), R304.2
unnamed: FB37.1, U43.1 (VIN)
unnamed: R304.1, U41.10 (P7)
P1_EXTO: U41.3 (P1)
P2_EXTO: U41.4 (P2)
P3_EXTO: R309.1, R311.2, U41.5 (P3), U45.1 (SHDN_N)
P4_EXTO: R310.1, R312.2, U41.7 (P4), U46.1 (SHDN_N)
VADCA: U44.6 (VOUTA)
VADCB: U44.7 (VOUTB)
VADCC: R313.1, TP42.1, U44.8 (VOUTC)
VADCD: R314.1, TP43.1, U44.9 (VOUTD)
VIOC_I2C_EXT_RST: TP38.1, U41.1 (*RESET)
VIOC_I2C_SCL: J29.2, TP36.1, U41.12 (SCL), U44.2 (SCL)
VIOC_I2C_SDA: J29.3, TP37.1, U41.13 (SDA), U44.3 (SDA)
VIOC_INT: R305.2, TP35.1, U41.11 (*INT)

Notes on the sheet:
VADC 0.283 -> 1.8V VADC 2.26 -> 1.25V
ADC is referenced to VDD 3.3V so that 2.5V ADC out is possible
Px_EXTO allows us to disable the ADC power and outputs selectively
VIO 1,2 are not present in this design
"backup" 1V8 static VIO supply
VIOC_I2C_EXT_RST Resets the I2C extender when pulled low
VIO lines 1,2 were eliminated from this design, because SYZYGY P1,P2 were excluded from the board
notifies MCU on DAC RDY chanages
